ArakniD/foxbms/hardware/hw-slave-12-ltc6811-1/v2.1.7/Sources/slave.PcbDoc.htm

Reporting Options

# File in Previous Format

Date | : | 11/01/2020
Time | : | 5:13:20 AM
Filename | : | C:\sandbox\github\foxBMS\hardware\hw-slave-12-ltc6811-1\v2.1.7\Sources\slave.PcbDoc

Version | Warning

This file was generated by an earlier version of the software
