ArakniD/foxbms/hardware/hw-master/v1.0.6-2/Sources/master.PcbDoc.htm

Reporting Options

# File in Previous Format

Date | : | 3/12/2019
Time | : | 3:43:56 PM
Filename | : | C:\Users\lucas\Documents\GitHub\foxbms\hardware\hw-master\v1.0.6\Sources\master.PcbDoc

Version | Warning

This file was generated by an earlier version of the software
