ArakniD/foxbms/hardware/datasheets/TPS26602 - Design Calculator Rev1p0.xlsx

Sheet: Calculation Sheet
TPS26602 Design Calculator Tool
Constants Cells | Input / Select Cells | Calculation Cells
 | Calculated, but can be over-ridden by the user. Note: Once cells are over-ridden, new calculation sheet should be used for the next design
Parameter | Description | Value | Units | Tolerance
VIN (max) | Maximum System Input Voltage | 16.0 | V
UVset | Undervoltage Lockout Threshold | 10.00 | V
OVset | Over Voltage Clamp Threshold | 38 | V
Cout | Load Capacitance | 330.0 | µF | 10%
TA (max) | Maximum Ambient Temperature | TA = 85C | °C
RLstart | Load during start-up (Assumed to be resistive) | 42.0 | Ω
Imax | Maximum continuous load current | 1.0 | A
ILimit | Current Limit, 10% higher than the maximum continuous load current | 1.10 | A
UVLO, OVP Calculations
R2_sel | Select a value in the range from 10k to 249k | 49.9 | kΩ | 1.0% | 9.34 | PFAIL (VIN Falling)
R1_cal | Calculated value of Resistor at IN pin | 369.4 | kΩ |  | 10.11 | UVLO (VIN Rising)
SELECT THE CLOSEST POSSIBLE RESISTANCE VALUE FOR R1, R2 |  |  |  |  | 38.00 | OV Clamp (VIN Rising)
R2_sel | Selected closest possible value for R3 resistor | 49.9 | kΩ | 1.0%
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
