ArakniD/foxbms/hardware/datasheets/TPS2663x _TPS1663x_Design_Calculator_revA.xlsx

Sheet: Instructions
Instructions for using the TPS2663x/TPS1663x Design Calculator
Instructions for using the TPS2663x/TPS1663x Design Calculator Design Inputs • Enter the design inputs for operating input voltage, under voltage, overvoltage set points, output capacitance, ambient temperature, load at start-up, maximum continuous load current, and permissible inrush current at start up for charging output capacitance in cells D5 to D14 in Calculation Sheet. • Select the current limit for device (ILimit) at-least 5% more than (Imax + IINRUSH_Permissible) in Cell D15 in Calculation Sheet. UVLO, OVP Calculations • Enter the value of resistor (R3) between UVLO and OVP pins in Cell D17 in Calculation in Calculation Sheet • Design Calculator provides the calculated value of R2, R3 • Select the value of R1, R2 and R3 resistors in cells D22 to D24 close to the calculated values. • Design calculator provides the final under voltage, overvoltage and power fail set points based on selected values of R1 to R3 in cells D22 to D24. • Verify the value of current through resistors R1 to R3. The color of cell D28 changes based on value of current. If Current < 2uA, the cell turns RED and value of
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
