ArakniD/foxbms/hardware/hw-master/v1.0.6-2/Fabrication/Report Board Stack/master.xls

Board Stack Report
Stack Up |  | Layer Stack
Layer | Board Layer Stack | Name | Material | Thickness | Constant
1 |  | Top Paste
2 |  | Top Overlay
3 |  | Top Solder | Solder Resist | 0.020mm | 3.8
4 |  | Top Signal | Copper | 0.036mm
5 |  | Dielectric 1 | PP-015 | 0.100mm | 4.05
6 |  | Top GND | Copper | 0.018mm
7 |  | Dielectric 4 | Core-036 | 0.565mm | 4.6
8 |  | Inner PWR | Copper | 0.018mm
9 |  | Dielectric 2 | PP-015 | 0.127mm | 4.25
10 |  | Inner Signal | Copper | 0.018mm
11 |  | Dielectric 5 | Core-036 | 0.565mm | 4.6
12 |  | Bottom GND | Copper | 0.018mm
13 |  | Dielectric 3 | PP-015 | 0.100mm | 4.05
14 |  | Bottom Signal | Copper | 0.036mm
15 |  | Bottom Solder | Solder Resist | 0.020mm | 3.8
16 |  | Bottom Overlay
17 |  | Bottom Paste
 | Height : 1.641mm
