ArakniD/foxbms/hardware/datasheets/WBDesign21_AltiumDesigner/ExportFiles/Schematic/Altium/2019-07-21_03-39-48/readme.txt

 

**********************************************************
*************  Important Instructions Follow  ************
**********************************************************
 
All files exported to: Z:\\23\\04\\2304964\\21\Altium\2019-07-21_03-39-48\2019-07-21_03-39-48

**********************************************************
***************** Schematic Instructions  ****************
**********************************************************

To import your new Schematic into Altium:

1. Unzip the downloaded folder files to a local directory and
Start the Altium program.
2. From the menu select "File"->"Open".
3. Select the file named in the path above ending with ".schdoc"
and "Open" the file.
4. Your Schematic should be viewable within Altium now.

For additional information, please visit this site:
http://www.accelerated-designs.com/help/Altium_BrdSch_import.html

**********************************************************
*******************  PCB Instructions  *******************
**********************************************************

To import your new BOARD into Altium:

1. Unzip the downloaded folder files to a local directory
	and Start the Altium program.
2. From the menu select "File"->"Open".
3. Select the file named in the path above ending with ".pcbdoc"
and "Open" the file.
4. Planes will need to be repoured to update the Copper Pour Polygons
	a. Once your board is loaded, select the Tools menu from the
	   top Menu Bar
	b. Scroll to the Polygon Pours item on the Tools Menu.
	c. The Polygon Pours item should expand to show more options
	d. Select Repour All Polygons, this will repour all of the
	   polygons.
5. Your board should be viewable within Altium now.

For additional information, please visit this site:
http://www.accelerated-designs.com/help/Altium_BrdSch_import.html

**********************************************************
*******************  LIB Instructions  *******************
**********************************************************

To import your new LIBRARY PARTS into Altium follow these steps:

1. After running the Ultra Librarian export for the first time,
you will need to copy the following files into an area where
they can be accessed for all future translations.  They are script
files that Altium will need to be able to find.
	a. UL_Form.dfm
	b. UL_Form.pas
	c. UL_Import.pas
	d. UL_Import.prjScr
2. The above script file will need to be run from within Altium.
This can be done by going to File, Open and selecting the
UL_Import.PrjScr file stored above.
3. Select the "DXP" dropdown menu in the top-left corner runfrom
the drop down menu and select "Run Script". Select "UL_Form.pas"
and click "OK"
4. When the script is run, it will ask you for the file name of the
Ultra Librarian file to run. Click "File...", select the latest file
produced with a date code (for instance 2010-02-17_23-12-34.txt), and
click "Start Import".
5. The script will open a new Integraged Library project and import
the Ultra Librarian data into it.  When complete a message box
will pop up saying that import is done.

For additional information, please visit this site:
http://www.accelerated-designs.com/help/Altium_import.html

For a video tutorial, please visit:
http://youtu.be/pih50yx9HYU

**********************************************************
**********************************************************
**********************************************************

Padstack "RX78p74Y236p22D0T" renamed to "RX78p74Y236p22D0"
Symbol "WB_CFF_BLOCK_TPS54202" renamed to "WB_CFF_BLOCK_TPS"
Symbol "WB_PWL_VOLTAGE_SOURCE" renamed to "WB_PWL_VOLTAGE_S"
Symbol "WB_SOURCE_RESISTOR" renamed to "WB_SOURCE_RESIST"
Symbol "WB_PRIM_PWL_VOLTAGE_SOURCE" renamed to "WB_PRIM_PWL_VOLT"
Symbol "WB_PRIM_STARTUP_VOLTAGE_SOURCE" renamed to "WB_PRIM_STARTUP_"
Symbol "WB_STARTUP_VOLTAGE_SOURCE" renamed to "WB_STARTUP_VOLTA"
Symbol "WB_PWL_CURRENT_LOAD" renamed to "WB_PWL_CURRENT_L"
Symbol "WB_PRIMITIVE_BATTERY" renamed to "WB_PRIMITIVE_BAT"
Component "TPS54202DDCR" renamed to "TPS54202DDCR"
Component "WB_CURRENT_LOAD" renamed to "WB_CURRENT_LOAD"
Component "SRN6045-4R7Y" renamed to "SRN6045-4R7Y"
Component "CRCW040222K1FKED" renamed to "CRCW040222K1FKED"
Component "CGA3E2X7R1H104K080AA" renamed to "CGA3E2X7R1H104K0"
Component "CL32B106KBJNNWE" renamed to "CL32B106KBJNNWE"
Component "WB_GND" renamed to "WB_GND"
Component "CRCW0402100KFKED" renamed to "CRCW0402100KFKED"
Component "CL21C510JBANNNC" renamed to "CL21C510JBANNNC"
Component "WB_BATTERY" renamed to "WB_BATTERY"
Component "TMK325B7226KMHP" renamed to "TMK325B7226KMHP"
The Symbol WB_CONTINUATION was missing a RefDes attribute, a refdes was created for the symbol.
The Symbol WB_CONTINUATION was missing a Type attribute, a type was created for the symbol.
The Symbol WB_CONTINUATION was missing a Value attribute, a value was created for the symbol.
The Symbol WB_BLOCK_IO was missing a RefDes attribute, a refdes was created for the symbol.
The Symbol WB_BLOCK_IO was missing a Type attribute, a type was created for the symbol.
The Symbol WB_BLOCK_IO was missing a Value attribute, a value was created for the symbol.
The Symbol WB_TPS54202DDC was missing a RefDes attribute, a refdes was created for the symbol.
The Symbol WB_TPS54202DDC was missing a Type attribute, a type was created for the symbol.
The Symbol WB_TPS54202DDC was missing a Value attribute, a value was created for the symbol.
The Symbol WB_VOLTAGE_PROBE was missing a RefDes attribute, a refdes was created for the symbol.
The Symbol WB_VOLTAGE_PROBE was missing a Type attribute, a type was created for the symbol.
The Symbol WB_VOLTAGE_PROBE was missing a Value attribute, a value was created for the symbol.
The Symbol WB_CURRENT_PROBE was missing a RefDes attribute, a refdes was created for the symbol.
The Symbol WB_CURRENT_PROBE was missing a Type attribute, a type was created for the symbol.
The Symbol WB_CURRENT_PROBE was missing a Value attribute, a value was created for the symbol.
The Symbol WB_CFF_BLOCK_TPS was missing a RefDes attribute, a refdes was created for the symbol.
The Symbol WB_CFF_BLOCK_TPS was missing a Type attribute, a type was created for the symbol.
The Symbol WB_CFF_BLOCK_TPS was missing a Value attribute, a value was created for the symbol.
The Symbol WB_PWL_VOLTAGE_S was missing a RefDes attribute, a refdes was created for the symbol.
The Symbol WB_PWL_VOLTAGE_S was missing a Type attribute, a type was created for the symbol.
The Symbol WB_PWL_VOLTAGE_S was missing a Value attribute, a value was created for the symbol.
The Symbol WB_SOURCE_RESIST was missing a RefDes attribute, a refdes was created for the symbol.
The Symbol WB_SOURCE_RESIST was missing a Type attribute, a type was created for the symbol.
The Symbol WB_SOURCE_RESIST was missing a Value attribute, a value was created for the symbol.
The Symbol WB_PRIM_PWL_VOLT was missing a RefDes attribute, a refdes was created for the symbol.
The Symbol WB_PRIM_PWL_VOLT was missing a Type attribute, a type was created for the symbol.
The Symbol WB_PRIM_PWL_VOLT was missing a Value attribute, a value was created for the symbol.
The Symbol WB_LOAD_RESISTOR was missing a RefDes attribute, a refdes was created for the symbol.
The Symbol WB_LOAD_RESISTOR was missing a Type attribute, a type was created for the symbol.
The Symbol WB_LOAD_RESISTOR was missing a Value attribute, a value was created for the symbol.
The Symbol WB_PRIM_STARTUP_ was missing a RefDes attribute, a refdes was created for the symbol.
The Symbol WB_PRIM_STARTUP_ was missing a Type attribute, a type was created for the symbol.
The Symbol WB_PRIM_STARTUP_ was missing a Value attribute, a value was created for the symbol.
The Symbol WB_STARTUP_VOLTA was missing a RefDes attribute, a refdes was created for the symbol.
The Symbol WB_STARTUP_VOLTA was missing a Type attribute, a type was created for the symbol.
The Symbol WB_STARTUP_VOLTA was missing a Value attribute, a value was created for the symbol.
The Symbol WB_PWL_CURRENT_L was missing a RefDes attribute, a refdes was created for the symbol.
The Symbol WB_PWL_CURRENT_L was missing a Type attribute, a type was created for the symbol.
The Symbol WB_PWL_CURRENT_L was missing a Value attribute, a value was created for the symbol.
The Symbol WB_PRIMITIVE_BAT was missing a RefDes attribute, a refdes was created for the symbol.
The Symbol WB_PRIMITIVE_BAT was missing a Type attribute, a type was created for the symbol.
The Symbol WB_PRIMITIVE_BAT was missing a Value attribute, a value was created for the symbol.

Ultra Librarian Gold 8.1.204 Process Report

Message - Component "SRN6045-4R7Y" attribute "Datasheet URL" references text style "" that is not in the database.
The default pattern text style "H50s3" was substituted.
Message - Component "SRN6045-4R7Y" attribute "L" references text style "" that is not in the database.
The default pattern text style "H50s3" was substituted.
Message - Component "SRN6045-4R7Y" attribute "DCR" references text style "" that is not in the database.
The default pattern text style "H50s3" was substituted.
Message - Component "SRN6045-4R7Y" attribute "IDC" references text style "" that is not in the database.
The default pattern text style "H50s3" was substituted.
Message - Component "CRCW040222K1FKED" attribute "Resistance" references text style "" that is not in the database.
The default pattern text style "H50s3" was substituted.
Message - Component "CRCW040222K1FKED" attribute "Power" references text style "" that is not in the database.
The default pattern text style "H50s3" was substituted.
Message - Component "CRCW040222K1FKED" attribute "Tolerance" references text style "" that is not in the database.
The default pattern text style "H50s3" was substituted.
Message - Component "CGA3E2X7R1H104K0" attribute "Datasheet URL" references text style "" that is not in the database.
The default pattern text style "H50s3" was substituted.
Message - Component "CGA3E2X7R1H104K0" attribute "Cap" references text style "" that is not in the database.
The default pattern text style "H50s3" was substituted.
Message - Component "CGA3E2X7R1H104K0" attribute "ESR" references text style "" that is not in the database.
The default pattern text style "H50s3" was substituted.
Message - Component "CGA3E2X7R1H104K0" attribute "IRMS" references text style "" that is not in the database.
The default pattern text style "H50s3" was substituted.
Message - Component "CGA3E2X7R1H104K0" attribute "VDC" references text style "" that is not in the database.
The default pattern text style "H50s3" was substituted.
Message - Component "CL32B106KBJNNWE" attribute "Datasheet URL" references text style "" that is not in the database.
The default pattern text style "H50s3" was substituted.
Message - Component "CL32B106KBJNNWE" attribute "Cap" references text style "" that is not in the database.
The default pattern text style "H50s3" was substituted.
Message - Component "CL32B106KBJNNWE" attribute "ESR" references text style "" that is not in the database.
The default pattern text style "H50s3" was substituted.
Message - Component "CL32B106KBJNNWE" attribute "IRMS" references text style "" that is not in the database.
The default pattern text style "H50s3" was substituted.
Message - Component "CL32B106KBJNNWE" attribute "VDC" references text style "" that is not in the database.
The default pattern text style "H50s3" was substituted.
Message - Component "CRCW0402100KFKED" attribute "Resistance" references text style "" that is not in the database.
The default pattern text style "H50s3" was substituted.
Message - Component "CRCW0402100KFKED" attribute "Power" references text style "" that is not in the database.
The default pattern text style "H50s3" was substituted.
Message - Component "CRCW0402100KFKED" attribute "Tolerance" references text style "" that is not in the database.
The default pattern text style "H50s3" was substituted.
Message - Component "CL21C510JBANNNC" attribute "Datasheet URL" references text style "" that is not in the database.
The default pattern text style "H50s3" was substituted.
Message - Component "CL21C510JBANNNC" attribute "Cap" references text style "" that is not in the database.
The default pattern text style "H50s3" was substituted.
Message - Component "CL21C510JBANNNC" attribute "ESR" references text style "" that is not in the database.
The default pattern text style "H50s3" was substituted.
Message - Component "CL21C510JBANNNC" attribute "IRMS" references text style "" that is not in the database.
The default pattern text style "H50s3" was substituted.
Message - Component "CL21C510JBANNNC" attribute "VDC" references text style "" that is not in the database.
The default pattern text style "H50s3" was substituted.
Message - Component "TMK325B7226KMHP" attribute "Datasheet URL" references text style "" that is not in the database.
The default pattern text style "H50s3" was substituted.
Message - Component "TMK325B7226KMHP" attribute "Cap" references text style "" that is not in the database.
The default pattern text style "H50s3" was substituted.
Message - Component "TMK325B7226KMHP" attribute "ESR" references text style "" that is not in the database.
The default pattern text style "H50s3" was substituted.
Message - Component "TMK325B7226KMHP" attribute "IRMS" references text style "" that is not in the database.
The default pattern text style "H50s3" was substituted.
Message - Component "TMK325B7226KMHP" attribute "VDC" references text style "" that is not in the database.
The default pattern text style "H50s3" was substituted.
Message - Pattern "DDC0006A_N", Attribute "RefDes" is a duplicate Attribute and will be deleted.
Message - Pattern "DDC0006A_M", Attribute "RefDes" is a duplicate Attribute and will be deleted.
Message - Pattern "DDC0006A_L", Attribute "RefDes" is a duplicate Attribute and will be deleted.

TextStyle count:  24
Padstack count:   8
Pattern count:    8
Symbol count:     21
Component count:  11

Export

Footprint "0402" has no layer data mapped and will be skipped.
Component "CRCW040222K1FKED" requires footprint "0402" and will be skipped.
Component "CRCW0402100KFKED" requires footprint "0402" and will be skipped.
Footprint "0603" has no layer data mapped and will be skipped.
Component "CGA3E2X7R1H104K0" requires footprint "0603" and will be skipped.
Footprint "0805" has no layer data mapped and will be skipped.
Component "CL21C510JBANNNC" requires footprint "0805" and will be skipped.
Warning: Symbol "TPS54202DDC" attribute "VAL" references missing text style ""
Warning: Symbol "TPS54202DDC" attribute "DEV" references missing text style ""
Warning: Symbol "TPS54202DDC" attribute "PN" references missing text style ""
Warning: Symbol "WB_INDUCTOR" attribute "L" references missing text style ""
Warning: Symbol "WB_INDUCTOR" attribute "DCR" references missing text style ""
Warning: Symbol "WB_INDUCTOR" attribute "IDC" references missing text style ""
Warning: Symbol "WB_INDUCTOR" attribute "PN" references missing text style ""
Warning: Symbol "WB_INDUCTOR" attribute "DEV" references missing text style ""
Warning: Symbol "WB_INDUCTOR" attribute "VAL" references missing text style ""
Warning: Symbol "WB_INDUCTOR" attribute "TOL" references missing text style ""
Warning: Symbol "WB_INDUCTOR" attribute "RefDes2" references missing text style ""
Warning: Symbol "WB_CAPACITOR" attribute "Cap" references missing text style ""
Warning: Symbol "WB_CAPACITOR" attribute "ESR" references missing text style ""
Warning: Symbol "WB_CAPACITOR" attribute "IRMS" references missing text style ""
Warning: Symbol "WB_CAPACITOR" attribute "VDC" references missing text style ""
Warning: Symbol "WB_CAPACITOR" attribute "TOL" references missing text style ""
Warning: Symbol "WB_CAPACITOR" attribute "VAL" references missing text style ""
Warning: Symbol "WB_CAPACITOR" attribute "DEV" references missing text style ""
Warning: Symbol "WB_CAPACITOR" attribute "PN" references missing text style ""
Warning: Symbol "WB_CAPACITOR" attribute "RefDes2" references missing text style ""
Warning: Symbol "WB_CAPACITOR" attribute "Cap" references missing text style ""
Warning: Symbol "WB_CAPACITOR" attribute "ESR" references missing text style ""
Warning: Symbol "WB_CAPACITOR" attribute "IRMS" references missing text style ""
Warning: Symbol "WB_CAPACITOR" attribute "VDC" references missing text style ""
Warning: Symbol "WB_CAPACITOR" attribute "TOL" references missing text style ""
Warning: Symbol "WB_CAPACITOR" attribute "VAL" references missing text style ""
Warning: Symbol "WB_CAPACITOR" attribute "DEV" references missing text style ""
Warning: Symbol "WB_CAPACITOR" attribute "PN" references missing text style ""
Warning: Symbol "WB_CAPACITOR" attribute "RefDes2" references missing text style ""
