ArakniD/foxbms/hardware/datasheets/WBDesign20_AltiumDesigner/ExportFiles/Schematic/webench_schematic_exchange_design_2304964_20_Altium/Altium/2019-07-21_03-32-47/readme.txt

 

**********************************************************
*************  Important Instructions Follow  ************
**********************************************************
 
All files exported to: Z:\\23\\04\\2304964\\20\Altium\2019-07-21_03-32-47\2019-07-21_03-32-47

**********************************************************
***************** Schematic Instructions  ****************
**********************************************************

To import your new Schematic into Altium:

1. Unzip the downloaded folder files to a local directory and
Start the Altium program.
2. From the menu select "File"->"Open".
3. Select the file named in the path above ending with ".schdoc"
and "Open" the file.
4. Your Schematic should be viewable within Altium now.

For additional information, please visit this site:
http://www.accelerated-designs.com/help/Altium_BrdSch_import.html

**********************************************************
*******************  PCB Instructions  *******************
**********************************************************

To import your new BOARD into Altium:

1. Unzip the downloaded folder files to a local directory
	and Start the Altium program.
2. From the menu select "File"->"Open".
3. Select the file named in the path above ending with ".pcbdoc"
and "Open" the file.
4. Planes will need to be repoured to update the Copper Pour Polygons
	a. Once your board is loaded, select the Tools menu from the
	   top Menu Bar
	b. Scroll to the Polygon Pours item on the Tools Menu.
	c. The Polygon Pours item should expand to show more options
	d. Select Repour All Polygons, this will repour all of the
	   polygons.
5. Your board should be viewable within Altium now.

For additional information, please visit this site:
http://www.accelerated-designs.com/help/Altium_BrdSch_import.html

**********************************************************
*******************  LIB Instructions  *******************
**********************************************************

To import your new LIBRARY PARTS into Altium follow these steps:

1. After running the Ultra Librarian export for the first time,
you will need to copy the following files into an area where
they can be accessed for all future translations.  They are script
files that Altium will need to be able to find.
	a. UL_Form.dfm
	b. UL_Form.pas
	c. UL_Import.pas
	d. UL_Import.prjScr
2. The above script file will need to be run from within Altium.
This can be done by going to File, Open and selecting the
UL_Import.PrjScr file stored above.
3. Select the "DXP" dropdown menu in the top-left corner runfrom
the drop down menu and select "Run Script". Select "UL_Form.pas"
and click "OK"
4. When the script is run, it will ask you for the file name of the
Ultra Librarian file to run. Click "File...", select the latest file
produced with a date code (for instance 2010-02-17_23-12-34.txt), and
click "Start Import".
5. The script will open a new Integraged Library project and import
the Ultra Librarian data into it.  When complete a message box
will pop up saying that import is done.

For additional information, please visit this site:
http://www.accelerated-designs.com/help/Altium_import.html

For a video tutorial, please visit:
http://youtu.be/pih50yx9HYU

**********************************************************
**********************************************************
**********************************************************

Symbol "WB_STARTUP_VOLTAGE_SOURCE" renamed to "WB_STARTUP_VOLTA"
Symbol "WB_SOURCE_RESISTOR" renamed to "WB_SOURCE_RESIST"
Symbol "WB_PRIM_STARTUP_VOLTAGE_SOURCE" renamed to "WB_PRIM_STARTUP_"
Symbol "WB_PWL_CURRENT_LOAD" renamed to "WB_PWL_CURRENT_L"
Symbol "WB_ZERO_VOLT_SOURCE" renamed to "WB_ZERO_VOLT_SOU"
Symbol "WB_PWL_VOLTAGE_SOURCE" renamed to "WB_PWL_VOLTAGE_S"
Symbol "WB_PRIM_PWL_VOLTAGE_SOURCE" renamed to "WB_PRIM_PWL_VOLT"
Symbol "WB_PRIMITIVE_BATTERY" renamed to "WB_PRIMITIVE_BAT"
Symbol "WB_TPS62131_CINX_BLOCK" renamed to "WB_TPS62131_CINX"
Symbol "WB_TPS62131_DEF_HIGH" renamed to "WB_TPS62131_DEF_"
Symbol "WB_TPS62131_DEF_LOW" renamed to "WB_TPS62131_DE00"
Symbol "WB_TPS62131_FSW_HIGH" renamed to "WB_TPS62131_FSW_"
Symbol "WB_TPS62131_FSW_LOW" renamed to "WB_TPS62131_FS00"
Component "C0805C106K8PACTU" renamed to "C0805C106K8PACTU"
Component "GRM188R60J226MEA0D" renamed to "GRM188R60J226MEA"
Component "GRM1555C1E391JA01D" renamed to "GRM1555C1E391JA0"
Component "WB_GND" renamed to "WB_GND"
Component "PA4332.222NLT" renamed to "PA4332.222NLT"
Component "CRCW0402100KFKED" renamed to "CRCW0402100KFKED"
Component "TPS62142RGTR" renamed to "TPS62142RGTR"
Component "WB_BATTERY" renamed to "WB_BATTERY"
Component "WB_CURRENT_LOAD" renamed to "WB_CURRENT_LOAD"
The Symbol WB_CONTINUATION was missing a RefDes attribute, a refdes was created for the symbol.
The Symbol WB_CONTINUATION was missing a Type attribute, a type was created for the symbol.
The Symbol WB_CONTINUATION was missing a Value attribute, a value was created for the symbol.
The Symbol WB_BLOCK_IO was missing a RefDes attribute, a refdes was created for the symbol.
The Symbol WB_BLOCK_IO was missing a Type attribute, a type was created for the symbol.
The Symbol WB_BLOCK_IO was missing a Value attribute, a value was created for the symbol.
The Symbol WB_STARTUP_VOLTA was missing a RefDes attribute, a refdes was created for the symbol.
The Symbol WB_STARTUP_VOLTA was missing a Type attribute, a type was created for the symbol.
The Symbol WB_STARTUP_VOLTA was missing a Value attribute, a value was created for the symbol.
The Symbol WB_SOURCE_RESIST was missing a RefDes attribute, a refdes was created for the symbol.
The Symbol WB_SOURCE_RESIST was missing a Type attribute, a type was created for the symbol.
The Symbol WB_SOURCE_RESIST was missing a Value attribute, a value was created for the symbol.
The Symbol WB_PRIM_STARTUP_ was missing a RefDes attribute, a refdes was created for the symbol.
The Symbol WB_PRIM_STARTUP_ was missing a Type attribute, a type was created for the symbol.
The Symbol WB_PRIM_STARTUP_ was missing a Value attribute, a value was created for the symbol.
The Symbol WB_CURRENT_PROBE was missing a RefDes attribute, a refdes was created for the symbol.
The Symbol WB_CURRENT_PROBE was missing a Type attribute, a type was created for the symbol.
The Symbol WB_CURRENT_PROBE was missing a Value attribute, a value was created for the symbol.
The Symbol WB_PWL_CURRENT_L was missing a RefDes attribute, a refdes was created for the symbol.
The Symbol WB_PWL_CURRENT_L was missing a Type attribute, a type was created for the symbol.
The Symbol WB_PWL_CURRENT_L was missing a Value attribute, a value was created for the symbol.
The Symbol WB_ZERO_VOLT_SOU was missing a RefDes attribute, a refdes was created for the symbol.
The Symbol WB_ZERO_VOLT_SOU was missing a Type attribute, a type was created for the symbol.
The Symbol WB_ZERO_VOLT_SOU was missing a Value attribute, a value was created for the symbol.
The Symbol WB_PWL_VOLTAGE_S was missing a RefDes attribute, a refdes was created for the symbol.
The Symbol WB_PWL_VOLTAGE_S was missing a Type attribute, a type was created for the symbol.
The Symbol WB_PWL_VOLTAGE_S was missing a Value attribute, a value was created for the symbol.
The Symbol WB_PRIM_PWL_VOLT was missing a RefDes attribute, a refdes was created for the symbol.
The Symbol WB_PRIM_PWL_VOLT was missing a Type attribute, a type was created for the symbol.
The Symbol WB_PRIM_PWL_VOLT was missing a Value attribute, a value was created for the symbol.
The Symbol WB_LOAD_RESISTOR was missing a RefDes attribute, a refdes was created for the symbol.
The Symbol WB_LOAD_RESISTOR was missing a Type attribute, a type was created for the symbol.
The Symbol WB_LOAD_RESISTOR was missing a Value attribute, a value was created for the symbol.
The Symbol WB_PRIMITIVE_BAT was missing a RefDes attribute, a refdes was created for the symbol.
The Symbol WB_PRIMITIVE_BAT was missing a Type attribute, a type was created for the symbol.
The Symbol WB_PRIMITIVE_BAT was missing a Value attribute, a value was created for the symbol.
The Symbol WB_TPS62142 was missing a RefDes attribute, a refdes was created for the symbol.
The Symbol WB_TPS62142 was missing a Type attribute, a type was created for the symbol.
The Symbol WB_TPS62142 was missing a Value attribute, a value was created for the symbol.
The Symbol WB_VOLTAGE_PROBE was missing a RefDes attribute, a refdes was created for the symbol.
The Symbol WB_VOLTAGE_PROBE was missing a Type attribute, a type was created for the symbol.
The Symbol WB_VOLTAGE_PROBE was missing a Value attribute, a value was created for the symbol.
The Symbol WB_TPS62131_CINX was missing a RefDes attribute, a refdes was created for the symbol.
The Symbol WB_TPS62131_CINX was missing a Type attribute, a type was created for the symbol.
The Symbol WB_TPS62131_CINX was missing a Value attribute, a value was created for the symbol.
The Symbol WB_TPS62131_DEF_ was missing a RefDes attribute, a refdes was created for the symbol.
The Symbol WB_TPS62131_DEF_ was missing a Type attribute, a type was created for the symbol.
The Symbol WB_TPS62131_DEF_ was missing a Value attribute, a value was created for the symbol.
The Symbol WB_TPS62131_DE00 was missing a RefDes attribute, a refdes was created for the symbol.
The Symbol WB_TPS62131_DE00 was missing a Type attribute, a type was created for the symbol.
The Symbol WB_TPS62131_DE00 was missing a Value attribute, a value was created for the symbol.
The Symbol WB_TPS62131_FSW_ was missing a RefDes attribute, a refdes was created for the symbol.
The Symbol WB_TPS62131_FSW_ was missing a Type attribute, a type was created for the symbol.
The Symbol WB_TPS62131_FSW_ was missing a Value attribute, a value was created for the symbol.
The Symbol WB_TPS62131_FS00 was missing a RefDes attribute, a refdes was created for the symbol.
The Symbol WB_TPS62131_FS00 was missing a Type attribute, a type was created for the symbol.
The Symbol WB_TPS62131_FS00 was missing a Value attribute, a value was created for the symbol.

Ultra Librarian Gold 8.1.204 Process Report

Message - Symbol "WB_CAPACITOR" has as multiple attributes named "TYPE".
One of the attributes was renamed to "TYPE_2".
Message - Component "C0805C106K8PACTU" attribute "Cap" references text style "" that is not in the database.
The default pattern text style "H50s3" was substituted.
Message - Component "C0805C106K8PACTU" attribute "ESR" references text style "" that is not in the database.
The default pattern text style "H50s3" was substituted.
Message - Component "C0805C106K8PACTU" attribute "IRMS" references text style "" that is not in the database.
The default pattern text style "H50s3" was substituted.
Message - Component "C0805C106K8PACTU" attribute "VDC" references text style "" that is not in the database.
The default pattern text style "H50s3" was substituted.
Message - Component "GRM188R60J226MEA" attribute "Datasheet URL" references text style "" that is not in the database.
The default pattern text style "H50s3" was substituted.
Message - Component "GRM188R60J226MEA" attribute "Cap" references text style "" that is not in the database.
The default pattern text style "H50s3" was substituted.
Message - Component "GRM188R60J226MEA" attribute "ESR" references text style "" that is not in the database.
The default pattern text style "H50s3" was substituted.
Message - Component "GRM188R60J226MEA" attribute "IRMS" references text style "" that is not in the database.
The default pattern text style "H50s3" was substituted.
Message - Component "GRM188R60J226MEA" attribute "VDC" references text style "" that is not in the database.
The default pattern text style "H50s3" was substituted.
Message - Component "GRM1555C1E391JA0" attribute "Cap" references text style "" that is not in the database.
The default pattern text style "H50s3" was substituted.
Message - Component "GRM1555C1E391JA0" attribute "ESR" references text style "" that is not in the database.
The default pattern text style "H50s3" was substituted.
Message - Component "GRM1555C1E391JA0" attribute "IRMS" references text style "" that is not in the database.
The default pattern text style "H50s3" was substituted.
Message - Component "GRM1555C1E391JA0" attribute "VDC" references text style "" that is not in the database.
The default pattern text style "H50s3" was substituted.
Message - Component "PA4332.222NLT" attribute "Datasheet URL" references text style "" that is not in the database.
The default pattern text style "H50s3" was substituted.
Message - Component "PA4332.222NLT" attribute "L" references text style "" that is not in the database.
The default pattern text style "H50s3" was substituted.
Message - Component "PA4332.222NLT" attribute "DCR" references text style "" that is not in the database.
The default pattern text style "H50s3" was substituted.
Message - Component "PA4332.222NLT" attribute "IDC" references text style "" that is not in the database.
The default pattern text style "H50s3" was substituted.
Message - Component "CRCW0402100KFKED" attribute "Resistance" references text style "" that is not in the database.
The default pattern text style "H50s3" was substituted.
Message - Component "CRCW0402100KFKED" attribute "Power" references text style "" that is not in the database.
The default pattern text style "H50s3" was substituted.
Message - Component "CRCW0402100KFKED" attribute "Tolerance" references text style "" that is not in the database.
The default pattern text style "H50s3" was substituted.

TextStyle count:  24
Padstack count:   6
Pattern count:    5
Symbol count:     26
Component count:  9

Export

Footprint "0805" has no layer data mapped and will be skipped.
Component "C0805C106K8PACTU" requires footprint "0805" and will be skipped.
Footprint "0603" has no layer data mapped and will be skipped.
Component "GRM188R60J226MEA" requires footprint "0603" and will be skipped.
Footprint "0402" has no layer data mapped and will be skipped.
Component "GRM1555C1E391JA0" requires footprint "0402" and will be skipped.
Component "CRCW0402100KFKED" requires footprint "0402" and will be skipped.
Warning: Symbol "WB_INDUCTOR" attribute "L" references missing text style ""
Warning: Symbol "WB_INDUCTOR" attribute "DCR" references missing text style ""
Warning: Symbol "WB_INDUCTOR" attribute "IDC" references missing text style ""
Warning: Symbol "WB_INDUCTOR" attribute "TOL" references missing text style ""
Warning: Symbol "WB_INDUCTOR" attribute "VAL" references missing text style ""
Warning: Symbol "WB_INDUCTOR" attribute "DEV" references missing text style ""
Warning: Symbol "WB_INDUCTOR" attribute "PN" references missing text style ""
Warning: Symbol "TPS62142RGT" attribute "TOL" references missing text style ""
Warning: Symbol "TPS62142RGT" attribute "VAL" references missing text style ""
Warning: Symbol "TPS62142RGT" attribute "DEV" references missing text style ""
Warning: Symbol "TPS62142RGT" attribute "PN" references missing text style ""
