ArakniD/foxbms/documentation/sphinx/general_information/releases/releases.rst

.. include:: ../../macros.rst

.. _GENERAL_INFORMATION_RELEASES:

========
Releases
========

The current **software version** of |foxbms| is |version|.

The latest **hardware release** versions are:

  - |BMS-Master|: |hw-version-master|
  - |BMS-Extension|: |hw-version-extension|
  - |BMS-Interface|: |hw-version-interface|
  - |BMS-12-Slave|: |hw-version-12-slave|
  - |BMS-18-Slave|: |hw-version-18-slave|

.. note::

    EEPROM module from **v1.5.0** is **NOT** compatible with previous versions
    due to the changed memory layout because of added timestamps!

.. note::

    foxBMS uses now python3. The foxconda3 installer is found at
    https://iisb-foxbms.iisb.fraunhofer.de/foxbms/. foxconda3 must be installed
    to C:\\foxconda3!

.. note::

    Until version **v1.1.0**, the |foxbms| software was split into several
    repositories, with an independent version number for each repository.
    Starting from version **v1.5.0**, the |foxbms| software is contained in
    only one repository, with one version number!

The following tables describe the different versions of |foxbms| that were
released. The first line is the most recent one, the last one the oldest one.

**Versions 1.5.0 and higher:**

+--------+----------+--------------+
| foxbms | foxconda | Release date |
+========+==========+==============+
| v1.6.3 | 3.0.3    | 2019-09-03   |
+--------+----------+--------------+
| v1.6.2 | 3.0.3    | 2019-07-05   |
+--------+----------+--------------+
| v1.6.1 | 3.0.3    | 2019-06-19   |
+--------+----------+--------------+
| v1.6.0 | 3.0.3    | 2019-06-19   |
+--------+----------+--------------+
| v1.5.5 | 3.0.3    | 2019-01-25   |
+--------+----------+--------------+
| v1.5.4 | 3.0.3    | 2018-12-14   |
+--------+----------+--------------+
| v1.5.3 | 3.0.3    | 2018-12-07   |
+--------+----------+--------------+
| v1.5.2 | 3.0.3    | 2018-10-26   |
+--------+----------+--------------+
| v1.5.1 | 3.0.3    | 2018-10-09   |
+--------+----------+--------------+
| v1.5.0 | 3.0.3    | 2018-09-25   |
+--------+----------+--------------+

**Versions before 1.5.0:**

.. note::

    The following table is only presented as information on previous |foxbms|
    versions. This software structure with different software repositories is
    not used anymore.

+---------------+-------------------------------------------------------+----------------------------------------------------------------+------------+
| Documentation | Embedded Software                                     |                          |foxbms| Hardware                     |  foxConda  |
+               +----------+-----------+-----------+---------+----------+--------------+-----------------+-------------+-----------------+------------+
|               | Primary  | Secondary | Common    | HAL     | FreeRTOS | |BMS-Master| | |BMS-Interface| | |BMS-Slave| | |BMS-Extension| |            |
+===============+==========+===========+===========+=========+==========+==============+=================+=============+=================+============+
| 1.0.3         | 1.1.0    | 1.1.0     | 1.1.0     | | 1.0.1 |  1.1.0   | 1.0.2        | 1.0.1           |   | 2.1.0   | 1.0.2           | 1.0.0      |
|               |          |           |           | | 1.0.0 |          |              |                 |   | 2.0.3   |                 |            |
|               |          |           |           |         |          |              |                 |   | 1.0.1   |                 |            |
+---------------+----------+-----------+-----------+---------+----------+--------------+-----------------+-------------+-----------------+------------+
| 1.0.2         | | 1.0.2  | | 1.0.1   | | 1.0.2   | | 1.0.1 |  1.0.0   | 1.0.2        | 1.0.1           |   | 2.1.0   | 1.0.2           | 1.0.0      |
|               | | 1.0.1  | | 1.0.0   | | 1.0.1   | | 1.0.0 |          |              |                 |   | 2.0.3   |                 |            |
|               | | 1.0.0  |           | | 1.0.0   |         |          |              |                 |   | 1.0.1   |                 |            |
+---------------+----------+-----------+-----------+---------+----------+--------------+-----------------+-------------+-----------------+------------+
| 0.5.2         | 0.5.2    | 0.5.2     |           |         |          | 1.0.2        | 1.0.1           |   | 2.1.0   | 1.0.2           | 0.5.0      |
|               |          |           |           |         |          |              |                 |   | 2.0.3   |                 |            |
|               |          |           |           |         |          |              |                 |   | 1.0.1   |                 |            |
+---------------+----------+-----------+-----------+---------+----------+--------------+-----------------+-------------+-----------------+------------+
| 0.5.1         | 0.5.1    | 0.5.1     |           |         |          | 1.0.2        | 1.0.1           | 1.0.1       | 1.0.2           | 0.5.0      |
+---------------+----------+-----------+-----------+---------+----------+--------------+-----------------+-------------+-----------------+------------+
| 0.5.0         | 0.5.0    | 0.5.0     |           |         |          | 1.0.2        | 1.0.1           | 1.0.1       | 1.0.2           | 0.5.0      |
+---------------+----------+-----------+-----------+---------+----------+--------------+-----------------+-------------+-----------------+------------+
| 0.4.4         | 0.4.4    | 0.4.4     |           |         |          | 1.0.1        | 1.0.1           | 1.0.1       | 1.0.1           | 0.4.3      |
+---------------+----------+-----------+-----------+---------+----------+--------------+-----------------+-------------+-----------------+------------+
| 0.4.3         | 0.4.3    | 0.4.3     |           |         |          | 1.0.0        | 1.0.0           | 1.0.0       | 1.0.0           | 0.4.3      |
+---------------+----------+-----------+-----------+---------+----------+--------------+-----------------+-------------+-----------------+------------+
| 0.4.2         | 0.4.2    | 0.4.2     |           |         |          | 1.0.0        | 1.0.0           | 1.0.0       | 1.0.0           | 0.4.0      |
+---------------+----------+-----------+-----------+---------+----------+--------------+-----------------+-------------+-----------------+------------+
| 0.4.1         | 0.4.1    | 0.4.1     |           |         |          | 1.0.0        | 1.0.0           | 1.0.0       | 1.0.0           | 0.4.0      |
+---------------+----------+-----------+-----------+---------+----------+--------------+-----------------+-------------+-----------------+------------+
| 0.4.0         | 0.4.0    | 0.4.0     |           |         |          | 1.0.0        | 1.0.0           | 1.0.0       | 1.0.0           | 0.4.0      |
+---------------+----------+-----------+-----------+---------+----------+--------------+-----------------+-------------+-----------------+------------+
