ArakniD/foxbms/hardware/datasheets/13461.png

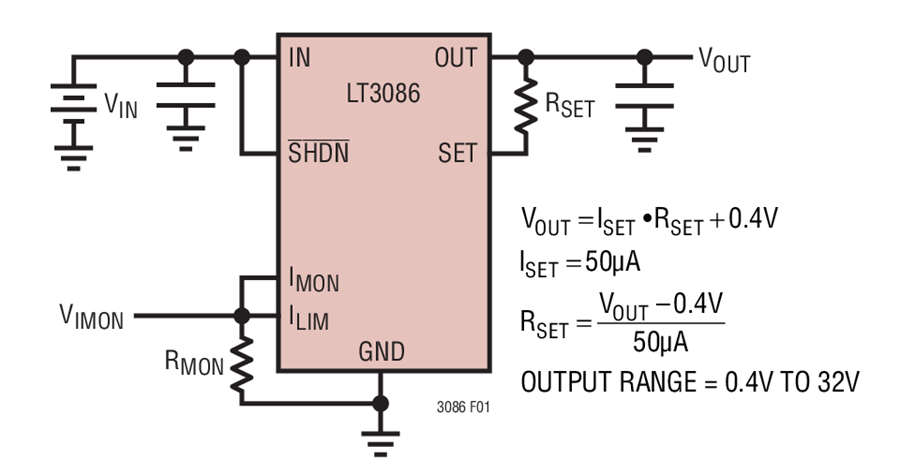
hardware/datasheets/13461.png
