ArakniD/foxbms/hardware/hw-slave-12-ltc6811-1/v2.1.7/Assembly default/bom/bom-slave-12-ltc6811-1(default).xlsx

Sheet: BOM
BOM for slave-12-ltc6811-1, Variant default
Generated on 28.03.2019 11:59:38
Line # | Designator | Quantity | Name | Description | Case EIA | Manufacturer 1 | Manufacturer Part Number 1 | Supplier 1 | Supplier Part Number 1
 | IC800-1, IC800-2 | 2 | M24M02-DWMN3TP/K | Automotive 2-Mbit serial I²C bus EEPROM with 1 MHz clock |  | STMicroelectronics (https://octopart-clicks.com/click/altium?manufacturer=STMicroelectronics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) | M24M02-DWMN3TP/K (https://octopart-clicks.com/click/altium?manufacturer=STMicroelectronics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) | Digi-Key | 497-16238-1-ND (https://octopart-clicks.com/click/altium?manufacturer=STMicroelectronics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)
1 | R605-1, R605-2, R1402-1, R1403-2, R1406-1, R1407-2, R1410-1, R1410-2, R1413-1, R1413-2, R1417-1, R1417-2, R1419-2, R1420-1 | 14 | 0R | SMD Resistor 0R 0603 | 0603 | Vishay Semiconductors (https://octopart-clicks.com/click/altium?manufacturer=Vishay%20Semiconductors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) | RCA06030000ZSEA (https://octopart-clicks.com/click/altium?manufacturer=Vishay%20Semiconductors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) | Farnell | 2616580, 2073345 (https://octopart-clicks.com/click/altium?manufacturer=Vishay%20Semiconductors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)
2 | R108-1, R108-2, R109-1, R109-2, R110-1, R110-2, R111-1, R111-2, R112-1, R112-2, R113-1, R113-2, R114-1, R114-2, R115-1, R115-2, R116-1, R116-2, R118-1, R118-2, R1300-1, R1300-2, R1301-1, R1301-2, R1302-1, R1302-2, R1303-1, R1303-2, R1304-1, R1304-2, R1305-1, R1305-2, R1306-1, R1306-2, R1307-1, R1307-2, R1308-1, R1308-2, R1309-1, R1309-2, R1310-1, R1310-2, R1311-1, R1311-2, R1312-1, R1312-2 | 46 | 100R | SMD Resistor 100R 0603 | 0603 | Panasonic (https://octopart-clicks.com/click/altium?manufacturer=Panasonic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) | ERJ-3EKF1000V (https://octopart-clicks.com/click/altium?manufacturer=Panasonic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) | Digikey, Farnell | P100HCT-ND, 1469752 (https://octopart-clicks.com/click/altium?manufacturer=Panasonic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)
3 | R1422-1, R1422-2, R1423-1, R1423-2 | 4 | 120R | SMD Resistor 120R 0603 | 0603 | Multicomp (https://octopart-clicks.com/click/altium?sku=2073369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) | MCMR06X1200FTL (https://octopart-clicks.com/click/altium?sku=2073369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) | Farnell | 2073369 (https://octopart-clicks.com/click/altium?sku=2073369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)
4 | R1100, R1101, R1102, R1103, R1104, R1105, R1106, R1107, R1108, R1109, R1110, R1111 | 12 | 150R | SMD Resistor 150R 0603 | 0603 | Vishay (https://octopart-clicks.com/click/altium?sku=1469760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) | CRCW0603150RFKEA (https://octopart-clicks.com/click/altium?sku=1469760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) | Farnell | 1469760 (https://octopart-clicks.com/click/altium?sku=1469760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)
5 | R1406-2, R1407-1 | 2 | 270R | SMD Resistor 270R 0603 | 0603 | Vishay (https://octopart-clicks.com/click/altium?sku=2141320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) | CRCW0603270RFKEA (https://octopart-clicks.com/click/altium?sku=2141320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) | Farnell | 2141320 (https://octopart-clicks.com/click/altium?sku=2141320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)
6 | R1421-1, R1421-2 | 2 | 820R | SMD Resistor 820R 0603 | 0603 | Vishay (https://octopart-clicks.com/click/altium?sku=1469841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) | CRCW0603820RFKEA (https://octopart-clicks.com/click/altium?sku=1469841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) | Farnell | 1469841 (https://octopart-clicks.com/click/altium?sku=1469841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)
7 | R610-1, R610-2 | 2 | 1k | SMD Resistor 1k 0603 | 0603 | Vishay Dale (https://octopart-clicks.com/click/altium?sku=1652848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) | CRCW06031K00FKTA (https://octopart-clicks.com/click/altium?sku=1652848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) | Farnell | 1652848 (https://octopart-clicks.com/click/altium?sku=1652848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)
8 | R1415-1, R1415-2, R1416-1, R1416-2, R1419-1, R1420-2 | 6 | 1k21 | SMD Resistor 1k21 0603 | 0603 | Vishay (https://octopart-clicks.com/click/altium?sku=1652852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) | CRCW06031K21FKEA (https://octopart-clicks.com/click/altium?sku=1652852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) | Farnell | 1652852 (https://octopart-clicks.com/click/altium?sku=1652852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)
9 | R606-1, R606-2 | 2 | 1k5 | SMD Resistor 1k5 0603 | 0603 | Vishay Dale (https://octopart-clicks.com/click/altium?sku=2616745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) | CRCW06031K50JNEA (https://octopart-clicks.com/click/altium?sku=2616745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) | Farnell | 2616745 (https://octopart-clicks.com/click/altium?sku=2616745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)
10 | R603-1, R603-2, R608-1, R608-2 | 4 | 124k | SMD Resistor 124k 0603 | 0603 | Vishay (https://octopart-clicks.com/click/altium?sku=2138508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) | CRCW0603124KFKEA (https://octopart-clicks.com/click/altium?sku=2138508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) | Farnell | 2138508 (https://octopart-clicks.com/click/altium?sku=2138508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)
11 | R1500, R1501, R1506, R1507, R1512, R1513, R1518, R1519, R1524, R1525, R1530, R1531 | 12 | 3k3 | SMD Resistor 3k3 0603 | 0603 | Vishay (https://octopart-clicks.com/click/altium?sku=1469793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) | CRCW06033K30FKEA (https://octopart-clicks.com/click/altium?sku=1469793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) | Farnell | 1469793 (https://octopart-clicks.com/click/altium?sku=1469793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)
12 | R100-1, R100-2, R101-1, R101-2, R102-1, R102-2, R103-1, R103-2, R104-1, R104-2, R105-1, R105-2, R106-1, R106-2, R107-1, R107-2, R600-1, R600-2, R604-1, R604-2, R609-1, R609-2, R700-1, R700-2, R701-1, R701-2, R702-1, R702-2, R703-1, R703-2, R704-1, R704-2, R705-1, R705-2, R706-1, R706-2, R707-1, R707-2, R708-1, R708-2, R801-1, R801-2, R904, R1112, R1404-1, R1404-2, R1408-1, R1408-2, R1411-1, R1411-2 | 50 | 10k | SMD Resistor 10k 0603 | 0603 | Multicomp (https://octopart-clicks.com/click/altium?sku=2073349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) | MCMR06X1002FTL (https://octopart-clicks.com/click/altium?sku=2073349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) | Farnell | 2073349 (https://octopart-clicks.com/click/altium?sku=2073349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)
13 | R905 | 1 | 86k6 | SMD Resistor 86k6 0603 | 0603 | Panasonic (https://octopart-clicks.com/click/altium?sku=2059490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) | ERJ-3EKF8662V (https://octopart-clicks.com/click/altium?sku=2059490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) | Farnell | 2059490 (https://octopart-clicks.com/click/altium?sku=2059490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)
14 | R602-1, R602-2 | 2 | 68k | SMD Resistor 68k 0603 | 0603
15 | R902 | 1 | 150k | SMD Resistor 150k 0603 | 0603
16 | R901 | 1 | 390k | SMD Resistor 390k 0603 | 0603 | Panasonic (https://octopart-clicks.com/click/altium?sku=2303278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) | ERJ3EKF3903V (https://octopart-clicks.com/click/altium?sku=2303278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) | Farnell | 2303278 (https://octopart-clicks.com/click/altium?sku=2303278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)
17 | R1400-2, R1401-1 | 2 | 1M | SMD Resistor 1M 0603 | 0603 | Vishay (https://octopart-clicks.com/click/altium?sku=1469746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) | CRCW06031M00FKEA (https://octopart-clicks.com/click/altium?sku=1469746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) | Farnell | 1469746 (https://octopart-clicks.com/click/altium?sku=1469746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)
18 | R607-1, R607-2 | 2 | 1R | SMD Resistor 1R 0805 | 0805 | Vishay Dale (https://octopart-clicks.com/click/altium?sku=2616757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) | CRCW08051R00FKEA (https://octopart-clicks.com/click/altium?sku=2616757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) | Farnell | 2616757 (https://octopart-clicks.com/click/altium?sku=2616757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)
19 | R900 | 1 | 39R | SMD Resistor 39R 0805 | 0805 | Panasonic (https://octopart-clicks.com/click/altium?sku=1750736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) | ERJP06F39R0V (https://octopart-clicks.com/click/altium?sku=1750736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) | Farnell | 1750736 (https://octopart-clicks.com/click/altium?sku=1750736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)
20 | R1400-1, R1401-2 | 2 | 100R | SMD Resistor 100R 0805 | 0805 | Vishay Dale (https://octopart-clicks.com/click/altium?sku=1469862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) | CRCW0805100RFKEA (https://octopart-clicks.com/click/altium?sku=1469862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) | Farnell | 1469862 (https://octopart-clicks.com/click/altium?sku=1469862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)
21 | R1502, R1503, R1504, R1505, R1508, R1509, R1510, R1511, R1514, R1515, R1516, R1517, R1520, R1521, R1522, R1523, R1526, R1527, R1528, R1529, R1532, R1533, R1534, R1535 | 24 | 68R | SMD Resistor 68R 2010 | 2010 | Panasonic (https://octopart-clicks.com/click/altium?sku=2323988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) | ERJ-12ZYJ680U (https://octopart-clicks.com/click/altium?sku=2323988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) | Farnell | 2323988 (https://octopart-clicks.com/click/altium?sku=2323988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)
22 | C1404-1, C1404-2, C1405-1, C1405-2 | 4 | 100p/50V | MLCC | 0603 | KEMET (https://octopart-clicks.com/click/altium?sku=1414603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) | C0603C101J5GACTU (https://octopart-clicks.com/click/altium?sku=1414603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) | Farnell | 1414603 (https://octopart-clicks.com/click/altium?sku=1414603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)
23 | C102-1, C102-2, C103-1, C103-2, C104-1, C104-2, C105-1, C105-2, C106-1, C106-2, C107-1, C107-2, C108-1, C108-2, C109-1, C109-2, C111-1, C111-2, C115-1, C115-2, C600-1, C600-2, C1300-1, C1300-2, C1301-1, C1301-2, C1304-1, C1304-2, C1305-1, C1305-2, C1308-1, C1308-2, C1309-1, C1309-2, C1312-1, C1312-2, C1313-1, C1313-2, C1316-1, C1316-2, C1317-1, C1317-2, C1320-1, C1320-2, C1321-1, C1321-2 | 46 | 10n/100V | MLCC | 0603 | KEMET (https://octopart-clicks.com/click/altium?sku=1301715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) | C0603X103K1RACAUTO (https://octopart-clicks.com/click/altium?sku=1301715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) | Farnell | 1301715 (https://octopart-clicks.com/click/altium?sku=1301715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)
24 | C100-1, C100-2, C400, C401, C402, C403, C404, C405, C406, C407, C601-1, C601-2, C604-1, C604-2, C605-1, C605-2, C700-1, C700-2, C701-1, C701-2, C800-1, C800-2, C801-1, C801-2, C906, C1100 | 26 | 100n/50V | MLCC | 0603 | Murata (https://octopart-clicks.com/click/altium?sku=490-6049-1-ND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) | GCM188L81H104KA57D (https://octopart-clicks.com/click/altium?sku=490-6049-1-ND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) | Digi-Key | 490-6049-1-ND (https://octopart-clicks.com/click/altium?sku=490-6049-1-ND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)
25 | C902 | 1 | 470p/100V | MLCC | 0805 | Multicomp (https://octopart-clicks.com/click/altium?sku=1759283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) | MC0805B471K101CT (https://octopart-clicks.com/click/altium?sku=1759283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) | Farnell | 1759283 (https://octopart-clicks.com/click/altium?sku=1759283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)
27 | C101-1, C101-2, C110-1, C110-2, C112-1, C112-2, C113-1, C113-2, C114-1, C114-2, C606-1, C606-2, C904, C907, C1401-1, C1401-2, C1402-1, C1402-2, C1403-1, C1403-2 | 20 | 1u/35V | MLCC | 0603 | Murata (https://octopart-clicks.com/click/altium?sku=1907508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) | GRM188R7YA105KA12D (https://octopart-clicks.com/click/altium?sku=1907508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) | Farnell | 1907508 (https://octopart-clicks.com/click/altium?sku=1907508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)
28 | C607-1, C607-2, C608-1, C608-2 | 4 | 2u2/10V | MLCC | 0805 | KEMET (https://octopart-clicks.com/click/altium?sku=2478259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) | C0805C225K8RACAUTO (https://octopart-clicks.com/click/altium?sku=2478259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) | Farnell | 2478259 (https://octopart-clicks.com/click/altium?sku=2478259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)
29 | C603-1, C603-2, C1400-1, C1400-2 | 4 | 100n/100V | MLCC | 0805 | Multicomp (https://octopart-clicks.com/click/altium?sku=2320821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) | MC0805B104K101CT (https://octopart-clicks.com/click/altium?sku=2320821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) | Farnell | 2320821 (https://octopart-clicks.com/click/altium?sku=2320821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)
30 | C900, C901 | 2 | 2u2/250V | MLCC | 2220 | TDK (https://octopart-clicks.com/click/altium?sku=445-7997-2-ND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) | CGA9P3X7T2E225M250KE (https://octopart-clicks.com/click/altium?sku=445-7997-2-ND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) | Digi-Key | 445-7997-2-ND (https://octopart-clicks.com/click/altium?sku=445-7997-2-ND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)
32 | C903 | 1 | 4n7/1000V | MLCC | 1812 | KEMET (https://octopart-clicks.com/click/altium?sku=1702159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) | C1812C472KDRACTU (https://octopart-clicks.com/click/altium?sku=1702159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) | Farnell | 1702159 (https://octopart-clicks.com/click/altium?sku=1702159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)
33 | C602-1, C602-2 | 2 | 1u/250V | MLCC | 1812 | TDK (https://octopart-clicks.com/click/altium?sku=2435499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) | CGA8P3X7T2E105K250KA (https://octopart-clicks.com/click/altium?sku=2435499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) | Farnell | 2435499 (https://octopart-clicks.com/click/altium?sku=2435499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)
34 | C905 | 1 | 22u/50V | MLCC | 2220 | KEMET (https://octopart-clicks.com/click/altium?sku=399-5797-1-ND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) | C2220C226M5R2CAUTO (https://octopart-clicks.com/click/altium?sku=399-5797-1-ND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) | Digi-Key | 399-5797-1-ND (https://octopart-clicks.com/click/altium?sku=399-5797-1-ND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)
35 | D1100 | 1 | BAT54C,215 | Schottky Barrier Diode, 30 V, 3-Pin SOT23, RoHS, Tape and Reel |  | NXP Semiconductors | BAT54C,215
36 | D1401-1, D1401-2 | 2 | SMAJ60A-E3/61 | Transient Voltage Suppressor, 6.40 to 231 V, 60 V Stand-off Voltage, Uni-Directional, -55 to 155 degC, 2-pin DO-214AC, Pb-Free, Tape and Reel |  | Vishay Semiconductors (https://octopart-clicks.com/click/altium?sku=1837055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) | SMAJ60A-E3/61 (https://octopart-clicks.com/click/altium?sku=1837055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) | Farnell | 1837055 (https://octopart-clicks.com/click/altium?sku=1837055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)
37 | D900 | 1 | PDS3200 | Schottky Diode 3A 200V 780mV |  | Diodes (https://octopart-clicks.com/click/altium?sku=1713904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) | PDS3200-13 (https://octopart-clicks.com/click/altium?sku=1713904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) | Farnell | 1713904 (https://octopart-clicks.com/click/altium?sku=1713904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)
38 | D901, D1400-1, D1400-2 | 3 | DFLS1100-7 | 1 A High Voltage Schottky Barrier Rectifier, 0.62 V, -55 to 175 degC, 2- Pin POWERDI123, Pb-Free, Tape and Reel |  | Diodes (https://octopart-clicks.com/click/altium?sku=1713889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) | DFLS1100-7 (https://octopart-clicks.com/click/altium?sku=1713889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) | Farnell | 1713889 (https://octopart-clicks.com/click/altium?sku=1713889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)
39 | Z1300-1, Z1300-2, Z1301-1, Z1301-2, Z1302-1, Z1302-2, Z1303-1, Z1303-2, Z1304-1, Z1304-2, Z1305-1, Z1305-2, Z1306-1, Z1306-2, Z1307-1, Z1307-2, Z1308-1, Z1308-2, Z1309-1, Z1309-2, Z1310-1, Z1310-2, Z1311-1, Z1311-2 | 24 | MMSZ4692T1G | Zener Voltage Regulator, 500 mW, 2-Pin SOD-123, Pb-Free, Tape and Reel |  | ON Semiconductor (https://octopart-clicks.com/click/altium?sku=MMSZ4692T1GOSCT-ND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) | MMSZ4692T1G (https://octopart-clicks.com/click/altium?sku=MMSZ4692T1GOSCT-ND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) | Digi-Key | MMSZ4692T1GOSCT-ND (https://octopart-clicks.com/click/altium?sku=MMSZ4692T1GOSCT-ND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)
40 | LD1400-1, LD1400-2 | 2 | green | LED |  | Kingbright (https://octopart-clicks.com/click/altium?sku=2099223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) | KPT-1608SGC (https://octopart-clicks.com/click/altium?sku=2099223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) | Farnell | 2099223 (https://octopart-clicks.com/click/altium?sku=2099223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)
41 | F300, F314 | 2 | fuse_0.5A_0448.500MR | Fuse, Surface Mount, NANO2 Series, 500 mA, 125 VAC, 32 VDC, Very Fast Acting, SMD |  | Littelfuse (https://octopart-clicks.com/click/altium?sku=1596919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) | 0448.500MR (https://octopart-clicks.com/click/altium?sku=1596919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) | Farnell | 1596919 (https://octopart-clicks.com/click/altium?sku=1596919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)
42 | F301, F302, F303, F304, F305, F306, F307, F308, F309, F310, F311, F312, F313 | 13 | fuse_0.25A_0466.250NR | Fuse, Surface Mount, 466 Series, 250 mA, 125 VAC, 125 VDC, Very Fast Acting, 1206 |  | Littelfuse (https://octopart-clicks.com/click/altium?sku=9921826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) | 0466.250NR (https://octopart-clicks.com/click/altium?sku=9921826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) | Farnell | 9921826 (https://octopart-clicks.com/click/altium?sku=9921826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)
43 | F900 | 1 | fuse_1.25A_04661.25NR | Fuse, Surface Mount, 466 Series, 1.25 A, 63 VAC, 63 VDC, Very Fast Acting, 1206 |  | Littelfuse (https://octopart-clicks.com/click/altium?sku=1596526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) | 0466.125NR (https://octopart-clicks.com/click/altium?sku=1596526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) | Farnell | 1596526 (https://octopart-clicks.com/click/altium?sku=1596526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)
44 | L900 | 1 | 74404042100 | WE-LQS SMD Power Inductor, L=10 µH |  | Wurth Electronics (https://octopart-clicks.com/click/altium?sku=2431496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) | 74404042100 (https://octopart-clicks.com/click/altium?sku=2431496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) | Farnell | 2431496 (https://octopart-clicks.com/click/altium?sku=2431496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)
45 | L600-1, L600-2 | 2 | 220µH | Power Inductor |  | Laird Steward (https://octopart-clicks.com/click/altium?sku=240-2742-1-ND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) | TYS6045221M-10 (https://octopart-clicks.com/click/altium?sku=240-2742-1-ND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) | Digi-Key | 240-2742-1-ND (https://octopart-clicks.com/click/altium?sku=240-2742-1-ND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)
46 | T1500, T1501, T1502, T1503, T1504, T1505, T1506, T1507, T1508, T1509, T1510, T1511 | 12 | NX2301P,215 | P-Channel Trench MOSFET, -20 V, -2 A, -55 to 150 degC, 3-Pin SOT23, Tape and Reel |  | NXP Semiconductors (https://octopart-clicks.com/click/altium?sku=771-NX2301P215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) | NX2301P,215 (https://octopart-clicks.com/click/altium?sku=771-NX2301P215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) | Mouser | 771-NX2301P215 (https://octopart-clicks.com/click/altium?sku=771-NX2301P215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)
47 | Q600-1, Q600-2 | 2 | PBSS4112PANP | Dual NPN/PNP Transistor
48 | IC100-1, IC100-2, IC101-1, IC101-2, IC102-1, IC102-2 | 6 | ADG728BRUZ | CMOS, Low Voltage, 2-Wire Serially Controlled, Matrix Switch, -40 to 85 degC, 16-pin SOP (RU-16), Tube |  | Analog Devices (https://octopart-clicks.com/click/altium?sku=9604383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) | ADG728BRUZ (https://octopart-clicks.com/click/altium?sku=9604383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) | Farnell | 9604383 (https://octopart-clicks.com/click/altium?sku=9604383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)
49 | U700-1, U700-2 | 2 | TCA6408APWR | Low-Voltage 8-Bit I2C and SMBus I/O Expander, 1.65 to 5.5 V, -40 to 85 degC, 16-pin TSSOP (PW), Green (RoHS & no Sb/Br) |  | Texas Instruments (https://octopart-clicks.com/click/altium?sku=1903303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) | TCA6408APWR (https://octopart-clicks.com/click/altium?sku=1903303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) | Farnell | 1903303 (https://octopart-clicks.com/click/altium?sku=1903303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)
50 | IC900 | 1 | LT8302HS8E#PBF | Micropower No-Opto Isolated Flyback Converter, 2.8 to 42 V, -40 to 150 degC, 8-Pin SOIC (S8E), RoHS, Tube |  | Analog Devices / Linear Technology (https://octopart-clicks.com/click/altium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) | LT8302HS8E#PBF (https://octopart-clicks.com/click/altium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) | Digi-Key | LT8302HS8E#PBF-ND (https://octopart-clicks.com/click/altium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)
51 | U100-1, U100-2, U101-1, U101-2 | 4 | AD8628ARTZ-R2 | Single Channel RRIO Operational Amplifier, 2.5 MHz BW, 1 V/us SR, Industrial, 5-pin SOT23 (RJ-5), Reel |  | Analog Devices (https://octopart-clicks.com/click/altium?sku=AD8628ARTZ-R2CT-ND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) | AD8628ARTZ-R2 (https://octopart-clicks.com/click/altium?sku=AD8628ARTZ-R2CT-ND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) | Digi-Key | AD8628ARTZ-R2CT-ND (https://octopart-clicks.com/click/altium?sku=AD8628ARTZ-R2CT-ND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)
52 | IC1400-1, IC1400-2 | 2 | LTC6811HG-1#PBF | Multicell Battery Monitor, 60 V Vin MAX, 48-pin SOP (G-48), -40 to 125 degC, Pb-Free |  | Analog Devices / Linear Technology (https://octopart-clicks.com/click/altium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) | LTC6811HG-1#PBF (https://octopart-clicks.com/click/altium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) | Digi-Key | LTC6811HG-1#PBF-ND (https://octopart-clicks.com/click/altium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)
53 | U1100, U1101, U1102, U1103, U1104, U1105, U1106, U1107, U1108, U1109, U1110, U1111 | 12 | ACPL-217 | Optocoupler, Transistor Output, 1 Channel |  | Broadcom (https://octopart-clicks.com/click/altium?sku=1602623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) | ACPL-217-56BE (https://octopart-clicks.com/click/altium?sku=1602623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) | Farnell | 1602623 (https://octopart-clicks.com/click/altium?sku=1602623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)
54 | IC801-1, IC801-2 | 2 | MCP9800A0T-M/OT | 2-Wire High-Accuracy Temperature Sensor, Slave Address 000, 5-Pin SOT-23, -55°C to +125°C Temperature, Tape and Reel |  | Microchip (https://octopart-clicks.com/click/altium?sku=1439485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) | MCP9800A0T-M/OT (https://octopart-clicks.com/click/altium?sku=1439485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) | Farnell | 1439485 (https://octopart-clicks.com/click/altium?sku=1439485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)
55 | U600-1, U600-2 | 2 | LM5161QPWPRQ1 | Automotive DC/DC buck converter |  | Texas Instruments (https://octopart-clicks.com/click/altium?sku=296-47791-1-ND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) | LM5161QPWPRQ1 (https://octopart-clicks.com/click/altium?sku=296-47791-1-ND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) | Digi-Key | 296-47791-1-ND (https://octopart-clicks.com/click/altium?sku=296-47791-1-ND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)
56 | TR1400-1, TR1400-2 | 2 | HM2102NL | Pulse HM2102NL BMS Transformer |  | Pulse Electronics Network (https://octopart-clicks.com/click/altium?manufacturer=Pulse%20Electronics%20Network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) | HM2102NLT (https://octopart-clicks.com/click/altium?manufacturer=Pulse%20Electronics%20Network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) | Digi-Key | 1840-1034-1-ND (https://octopart-clicks.com/click/altium?manufacturer=Pulse%20Electronics%20Network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)
57 | TR900 | 1 | WE_750313457 | MID-FLYLT Flyback Transformers for Linear Technology |  | Wurth Electronics (https://octopart-clicks.com/click/altium?sku=1297-1136-1-ND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) | 750313457 (https://octopart-clicks.com/click/altium?sku=1297-1136-1-ND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) | Digi-Key | 1297-1136-1-ND (https://octopart-clicks.com/click/altium?sku=1297-1136-1-ND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)
59 | X1000 | 1 | samtec_TSW-102-07-G-D | Board-To-Board Connector, Vertical, 2.54 mm, 4 Contacts, Header, TSW Series, Through Hole, 2 Rows |  | Samtec (https://octopart-clicks.com/click/altium?sku=2025248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) | TSW-102-07-G-D (https://octopart-clicks.com/click/altium?sku=2025248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) | Farnell | 2025248 (https://octopart-clicks.com/click/altium?sku=2025248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)
61 | X401, X404 | 2 | gen_pinheader_2.54_2x5 | Standard Pinheader, THD, gerade, 2.54mm, 2-reihig |  | Samtec (https://octopart-clicks.com/click/altium?sku=2578720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) | TSW-105-07-G-D (https://octopart-clicks.com/click/altium?sku=2578720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) | Farnell | 2578720 (https://octopart-clicks.com/click/altium?sku=2578720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)
62 | X400, X403 | 2 | gen_pinheader_2.54_2x9 | Standard Pinheader, THD, gerade, 2.54mm, 2-reihig |  | Samtec (https://octopart-clicks.com/click/altium?sku=2025256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) | TSW-109-07-G-D (https://octopart-clicks.com/click/altium?sku=2025256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) | Farnell | 2025256 (https://octopart-clicks.com/click/altium?sku=2025256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)
63 | X402 | 1 | gen_pinheader_2.54_2x10 | Standard Pinheader, THD, gerade, 2.54mm, 2-reihig |  | Samtec (https://octopart-clicks.com/click/altium?sku=2025257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) | TSW-110-07-G-D (https://octopart-clicks.com/click/altium?sku=2025257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) | Farnell | 2025257 (https://octopart-clicks.com/click/altium?sku=2025257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)
64 | X500, X501, X502, X503, X1001, X1002 | 6 | molex_microfit_3_01x2_THT | Micro-Fit 3.0 Right Angle Header, 3.00mm Pitch, Dual Row, 2 Circuits, with Snap-in Plastic Peg PCB Lock, Tin, Glow Wire Capable, Black, 43045-0200 |  | Molex (https://octopart-clicks.com/click/altium?sku=1012251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) | 43045-0200 (https://octopart-clicks.com/click/altium?sku=1012251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) | Farnell | 1012251 (https://octopart-clicks.com/click/altium?sku=1012251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)
65 | X201, X202 | 2 | molex_microfit_3_08x2_THT | Micro-Fit 3.0 Right Angle Header, 3.00mm Pitch, Dual Row, 16 Circuits, with Snap-in Plastic Peg PCB Lock, Tin, Glow Wire Capable, Black, 43045-1600 |  | Molex (https://octopart-clicks.com/click/altium?sku=9961380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) | 43045-1600 (https://octopart-clicks.com/click/altium?sku=9961380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) | Farnell | 9961380 (https://octopart-clicks.com/click/altium?sku=9961380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)
66 | X200 | 1 | molex_microfit_3_12x2_THT | Micro-Fit 3.0 Right Angle Header, 3.00mm Pitch, Dual Row, 24 Circuits, with Snap-in Plastic Peg PCB Lock, Tin, Glow Wire Capable, Black, 43045-2400 |  | Molex (https://octopart-clicks.com/click/altium?sku=1012245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) | 43045-2400 (https://octopart-clicks.com/click/altium?sku=1012245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) | Farnell | 1012245 (https://octopart-clicks.com/click/altium?sku=1012245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)

Sheet: DATA
slave-12-ltc6811-1.PrjPcb
28.03.2019 11:59:38
default
