ArakniD/foxbms/hardware/hw-extension/v1.0.5/Assembly default/bom/bom-extension(default).xlsx

Sheet: BOM
BOM for extension, Variant default
Generated on 26.10.2018 08:24:22
Line # | Designator | Quantity | Name | Description | Case EIA | Manufacturer 1 | Manufacturer Part Number 1 | Supplier 1 | Supplier Part Number 1 | MOQ | multiple | order quantity | Automotive Qualified
 | C801, C1102, C1301, C1502, C1703, C1902 | 6 | 1u/50V | MLCC | 0603 | Taiyo Yuden (https://octopart-clicks.com/click/altium?sku=2779055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) | UMK107AB7105KA-T (https://octopart-clicks.com/click/altium?sku=2779055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) | Farnell | 2779055 (https://octopart-clicks.com/click/altium?sku=2779055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) |  | 1 | 6
 | C802, C803, C805, C806, C807, C1101, C1103, C1104, C1105, C1106, C1302, C1303, C1304, C1305, C1306, C1501, C1701, C1702, C1704, C1705, C1706, C1707, C1708, C1901, C1903, C1904, C1905, C1906, C1907 | 29 | 100n/50V | MLCC | 0603 | Vishay (https://octopart-clicks.com/click/altium?sku=2525267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) | VJ0603Y104KXAAC31X (https://octopart-clicks.com/click/altium?sku=2525267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) | Farnell | 2525267 (https://octopart-clicks.com/click/altium?sku=2525267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) |  | 1 | 29
 | C804 | 1 | 4n7/50V | MLCC | 0603 | KEMET (https://octopart-clicks.com/click/altium?sku=2904754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) | C0603C472J5RACAUTO (https://octopart-clicks.com/click/altium?sku=2904754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) | Farnell | 2904754 (https://octopart-clicks.com/click/altium?sku=2904754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) |  | 1 | 1 | True
 | D801 | 1 | PESD1CAN | CAN Bus ESD Protection Diode, 200 W, 24 V, -65 to 150 degC, 3-Pin SOT23, RoHS, Tape and Reel |  | NXP Semiconductors | PESD1CAN |  |  |  | 1 | 1
 | D1101, D1102, D1103, D1901, D1902, D1903, D1904 | 7 | CDSOD323-T05 | TVS Diode, CDSOD323 Series, Unidirectional, 5 V, 18.3 V, SOD-323, 2 Pins |  | Bourns (https://octopart-clicks.com/click/altium?sku=2341914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) | CDSOD323-T05 (https://octopart-clicks.com/click/altium?sku=2341914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) | Farnell | 2341914 (https://octopart-clicks.com/click/altium?sku=2341914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) |  | 1 | 7
 | D1701, D1702, D1703, D1704, D1705 | 5 | MM3Z3V3ST1G | Zener Voltage Regulator, 300 mW, Tight Tolerance Portfolio, 2-Pin SOD-323, Pb-Free, Tape and Reel |  | ON Semiconductor | MM3Z3V3ST1G |  |  |  | 1 | 5
 | F1001, F1002, F1003 | 3 | Schurter SMD Fuse 4.0A UMT 3403.0172.11 | Schurter SMD Fuse 4.0A UMT 3403.0172.11 |  | Schurter (https://octopart-clicks.com/click/altium?sku=486-1253-ND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) | 3403.0172.11 (https://octopart-clicks.com/click/altium?sku=486-1253-ND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) | Digi-Key | 486-1253-ND (https://octopart-clicks.com/click/altium?sku=486-1253-ND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) |  | 1 | 3
 | IC801 | 1 | KA7805ERT | 3-Terminal 1 A Positive Voltage Regulator |  | ON Semiconductor / Fairchild (https://octopart-clicks.com/click/altium?manufacturer=ON%20Semiconductor%20%2F%20Fairchild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) | KA7805ERTF (https://octopart-clicks.com/click/altium?manufacturer=ON%20Semiconductor%20%2F%20Fairchild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) | Farnell | 2102585 (https://octopart-clicks.com/click/altium?manufacturer=ON%20Semiconductor%20%2F%20Fairchild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) |  | 1 | 1
 | IC802 | 1 | CPC1008N | Single-Pole, Normally Open 4-Pin SOP OptoMOS Relay |  | CPC (https://octopart-clicks.com/click/altium?sku=1653755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) | CPC1008N (https://octopart-clicks.com/click/altium?sku=1653755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) | Farnell | 1653755 (https://octopart-clicks.com/click/altium?sku=1653755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) |  | 1 | 1
 | IC803 | 1 | TJA1052IT/5Y | Galvanically Isolated High-Speed CAN Transceiver, -40 to 125 degC, 16-Pin SOIC, RoHS, Tape and Reel |  | NXP Semiconductors (https://octopart-clicks.com/click/altium?sku=2400552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) | TJA1052IT/5Y (https://octopart-clicks.com/click/altium?sku=2400552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) | Farnell | 2400552 (https://octopart-clicks.com/click/altium?sku=2400552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) |  | 1 | 1
 | IC1001, IC1002, IC1003, IC2001, IC2002, IC2003, IC2004, IC2005, IC2006 | 9 | AQV252G2SX | PhotoMOS Relay |  | Panasonic (https://octopart-clicks.com/click/altium?sku=2302216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) | AQV252G2SX (https://octopart-clicks.com/click/altium?sku=2302216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) | Farnell | 2302216 (https://octopart-clicks.com/click/altium?sku=2302216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) |  | 1 | 9
 | IC1101, IC1301, IC1901 | 3 | UA78L05CPK | Positive-Voltage Regulator, 100 mA, 0 to 125 degC, 3-Pin SOT-89 (PK), Green (RoHS & no Sb/Br), Tape and Reel |  | Texas Instruments (https://octopart-clicks.com/click/altium?sku=2112604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) | UA78L05CPK (https://octopart-clicks.com/click/altium?sku=2112604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) | Farnell | 2112604 (https://octopart-clicks.com/click/altium?sku=2112604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) |  | 1 | 3
 | IC1102 | 1 | ADUM3300CRWZ | Triple Channel Digital Isolator, Enhanced System-Level ESD Reliability, 2.5 KV rms Insulation Rating, 90 Mbps Data Rate, 32 ns Delay, Industrial, 16-pin SOIC (RW-16), Tube |  | Analog Devices (https://octopart-clicks.com/click/altium?sku=584-ADUM3300CRWZ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) | ADUM3300CRWZ (https://octopart-clicks.com/click/altium?sku=584-ADUM3300CRWZ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) | Mouser | 584-ADUM3300CRWZ (https://octopart-clicks.com/click/altium?sku=584-ADUM3300CRWZ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) |  | 1 | 1
 | IC1302 | 1 | LT1785 | Transceiver RS422/RS485, Fault Protected, 4.75V-5.25V supply, SOIC-8 |  | Analog Devices / Linear Technology (https://octopart-clicks.com/click/altium?sku=1663498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) | LT1785CS8#PBF (https://octopart-clicks.com/click/altium?sku=1663498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) | Farnell | 1663498 (https://octopart-clicks.com/click/altium?sku=1663498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) |  | 1 | 1
 | IC1303 | 1 | ADUM3401CRWZ | Quad Channel Digital Isolator, Enhanced System-Level ESD Reliability, 2.5 KV rms Insulation Rating, 90 Mbps Data Rate, 32 ns Delay, Industrial, 16-pin SOIC (RW-16), Tube |  | Analog Devices (https://octopart-clicks.com/click/altium?sku=1274129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) | ADUM3401CRWZ (https://octopart-clicks.com/click/altium?sku=1274129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) | Farnell | 1274129 (https://octopart-clicks.com/click/altium?sku=1274129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) |  | 1 | 1
 | IC1701 | 1 | ADR3425ARJZ-R2 | Micropower, High Accuracy Voltage Reference, 2.5 V Output, 2.7 to 5.5 V Supply, Industrial, 6-pin SOT23 (RJ-6), Reel |  | Analog Devices (https://octopart-clicks.com/click/altium?sku=2377039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) | ADR3425ARJZ-R2 (https://octopart-clicks.com/click/altium?sku=2377039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) | Farnell | 2377039 (https://octopart-clicks.com/click/altium?sku=2377039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) |  | 1 | 1
 | IC1902, IC1903 | 2 | ADUM3402BRWZ | Quad Channel Digital Isolator, Enhanced System-Level ESD Reliability, 2.5 KV rms Insulation Rating, 10 Mbps Data Rate, 50 ns Delay, Industrial, 16-pin SOIC (RW-16), Tube |  | Analog Devices (https://octopart-clicks.com/click/altium?sku=1274127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) | ADUM3402BRWZ (https://octopart-clicks.com/click/altium?sku=1274127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) | Farnell | 1274127 (https://octopart-clicks.com/click/altium?sku=1274127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) |  | 1 | 2
 | JP2201, JP2202 | 2 | X2x12 | Board-To-Board Connector, Vertical, Low Profile, 2.54 mm, 24 Contacts, Header, TLW Series, Through Hole, 2 Rows |  | Samtec (https://octopart-clicks.com/click/altium?sku=SAM1096-12-ND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) | TLW-112-06-G-D (https://octopart-clicks.com/click/altium?sku=SAM1096-12-ND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) | Digikey | SAM1096-12-ND (https://octopart-clicks.com/click/altium?sku=SAM1096-12-ND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) |  | 1 | 2
 | L801 | 1 | 51uH | Common Mode Choke |  | TDK EPCOS (https://octopart-clicks.com/click/altium?sku=871-B82789C0513H002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) | B82789C0513H002 (https://octopart-clicks.com/click/altium?sku=871-B82789C0513H002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) | Mouser | 871-B82789C0513H002 (https://octopart-clicks.com/click/altium?sku=871-B82789C0513H002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) |  | 1 | 1
 | L1501 | 1 | BLM21AG471SN1J | Chip Ferrite Bead for General Signal lines, 470 Ohm, 700 mA, -55 to 125 degC, 2 x 1.25 x 1.05 mm SMD, Tape and Reel |  | Laird (https://octopart-clicks.com/click/altium?sku=2292413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) | HZ0805G471R-10 (https://octopart-clicks.com/click/altium?sku=2292413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) | Farnell | 2292413 (https://octopart-clicks.com/click/altium?sku=2292413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) |  | 1 | 1
 | R801, R802 | 2 | 62R | SMD Resistor 62R 0603 | 0603 | Multicomp (https://octopart-clicks.com/click/altium?sku=2073943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) | MCMR12X62R0FTL (https://octopart-clicks.com/click/altium?sku=2073943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) | Farnell | 2073943 (https://octopart-clicks.com/click/altium?sku=2073943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) |  | 1 | 2
 | R803, R805, R901, R1002, R1005, R1008, R1104, R1105, R1106, R1502, R1503, R1504, R1505, R1506, R1507, R1903, R1904, R1907, R1908, R2003, R2004, R2009, R2010, R2015, R2016 | 25 | 10k | SMD Resistor 10k 0603 | 0603 | Multicomp (https://octopart-clicks.com/click/altium?sku=2073349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) | MCMR06X1002FTL (https://octopart-clicks.com/click/altium?sku=2073349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) | Farnell | 2073349 (https://octopart-clicks.com/click/altium?sku=2073349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) |  | 1 | 25
 | R804, R1003, R1006, R1009, R2005, R2006, R2011, R2012, R2017, R2018 | 10 | 430R | SMD Resistor 430R 0603 | 0603 | Multicomp (https://octopart-clicks.com/click/altium?sku=2074259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) | MCSR06X4300FTL (https://octopart-clicks.com/click/altium?sku=2074259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) | Farnell | 2074259 (https://octopart-clicks.com/click/altium?sku=2074259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) |  | 1 | 10
 | R806, R902, R1001, R1004, R1007, R2001, R2002, R2007, R2008, R2013, R2014 | 11 | 10R | SMD Resistor 10R 0603 | 0603 | Multicomp (https://octopart-clicks.com/click/altium?sku=2073361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) | MCMR06X10R0FTL (https://octopart-clicks.com/click/altium?sku=2073361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) | Farnell | 2073361 (https://octopart-clicks.com/click/altium?sku=2073361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) |  | 1 | 11
 | R1101, R1102, R1103, R1901, R1902, R1905, R1906 | 7 | 47R | SMD Resistor 47R 0603 | 0603 | Panasonic (https://octopart-clicks.com/click/altium?sku=2303030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) | ERJ-3EKF47R0V (https://octopart-clicks.com/click/altium?sku=2303030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) | Farnell | 2303030 (https://octopart-clicks.com/click/altium?sku=2303030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) |  | 1 | 7
 | R1501 | 1 | 47k | SMD Resistor 47k 0603 | 0603 | Multicomp (https://octopart-clicks.com/click/altium?sku=2073510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) | MCMR06X4702FTL (https://octopart-clicks.com/click/altium?sku=2073510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) | Farnell | 2073510 (https://octopart-clicks.com/click/altium?sku=2073510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) |  | 1 | 1
 | R1701, R1703, R1705, R1707, R1709 | 5 | 0R | SMD Resistor 0R 0603 | 0603 | Multicomp (https://octopart-clicks.com/click/altium?sku=2073345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) | MCMR06X000PTL (https://octopart-clicks.com/click/altium?sku=2073345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) | Farnell | 2073345 (https://octopart-clicks.com/click/altium?sku=2073345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) |  | 1 | 5
 | R1702, R1704, R1706, R1708, R1710 | 5 | 4k75 | SMD Resistor 4k75 0603 | 0603 | Multicomp (https://octopart-clicks.com/click/altium?sku=2073517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) | MCMR06X4751FTL (https://octopart-clicks.com/click/altium?sku=2073517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) | Farnell | 2073517 (https://octopart-clicks.com/click/altium?sku=2073517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) |  | 1 | 5
 | SLOT1501 | 1 | MOLEX_47352-1001 | 1.10mm Pitch Memorycard Card Connector, Push-Push Type, with VSS (Supply Voltage Ground) Detect Switch, Lead-Free |  | Molex (https://octopart-clicks.com/click/altium?sku=2424133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) | 47352-1001 (https://octopart-clicks.com/click/altium?sku=2424133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) | Farnell | 2424133 (https://octopart-clicks.com/click/altium?sku=2424133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) |  | 1 | 1 | False
 | SV901 | 1 | samtec_TLW-104-06-G-D | Board-To-Board Connector, Vertical, Low Profile, 2.54 mm, 8 Contacts, Header, TLW Series, Through Hole, 2 Rows |  | Samtec (https://octopart-clicks.com/click/altium?sku=SAM1096-04-ND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) | TLW-104-06-G-D (https://octopart-clicks.com/click/altium?sku=SAM1096-04-ND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) | Digikey | SAM1096-04-ND (https://octopart-clicks.com/click/altium?sku=SAM1096-04-ND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) |  | 1 | 1
 | T801, T1001, T1002, T1003, T2001, T2002, T2003, T2004, T2005, T2006 | 10 | IRLML0100TRPBF | MOSFET-Transistor, n-Kanal, 1.6 A, 100 V, 0.178 ohm, 10 V, 2.5 V |  | International Rectifier (https://octopart-clicks.com/click/altium?sku=1783928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) | IRLML0100TRPBF (https://octopart-clicks.com/click/altium?sku=1783928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) | Farnell | 1783928 (https://octopart-clicks.com/click/altium?sku=1783928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) |  | 1 | 10
 | T901 | 1 | BUK964R8-60E,118 | N-Channel TrenchMOS Logic Level FET, 60 V, 100 A, 3-Pin SOT404, Tape and Reel |  | NXP Semiconductors (https://octopart-clicks.com/click/altium?manufacturer=NXP%20Semiconductors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) | BUK964R8-60E,118 (https://octopart-clicks.com/click/altium?manufacturer=NXP%20Semiconductors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) | Digi-Key | 1727-7261-6-ND (https://octopart-clicks.com/click/altium?manufacturer=NXP%20Semiconductors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) |  | 1 | 1 | Y
 | T1501 | 1 | BSS84P | P-Channel SIPMOS Small-Signal-Transistor, -60 V VDS, -0.17 A ID, -55 to 150 degC, PG-SOT23, Reel, Green |  | Infineon | BSS84P |  |  |  | 1 | 1
 | X801, X1201, X1202, X1203 | 4 | molex_microfit_3_02x2_THT | Micro-Fit 3.0 Right Angle Header, 3.00mm Pitch, Dual Row, 4 Circuits, with Snap-in Plastic Peg PCB Lock, Tin, Glow Wire Capable, Black, 43045-0400 |  | Molex (https://octopart-clicks.com/click/altium?sku=9733019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) | 43045-0400 (https://octopart-clicks.com/click/altium?sku=9733019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) | Farnell | 9733019 (https://octopart-clicks.com/click/altium?sku=9733019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) |  | 1 | 4
 | X1301 | 1 | molex_microfit_3_03x2_THT | Micro-Fit 3.0 Right Angle Header, 3.00mm Pitch, Dual Row, 6 Circuits, with Snap-in Plastic Peg PCB Lock, Tin, Glow Wire Capable, Black, 43045-0600 |  | Molex (https://octopart-clicks.com/click/altium?sku=1012252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) | 43045-0600 (https://octopart-clicks.com/click/altium?sku=1012252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) | Farnell | 1012252 (https://octopart-clicks.com/click/altium?sku=1012252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) |  | 1 | 1
 | X1701, X2001 | 2 | molex_microfit_3_06x2_THT | Micro-Fit 3.0 Right Angle Header, 3.00mm Pitch, Dual Row, 12 Circuits, with Snap-in Plastic Peg PCB Lock, Tin, Glow Wire Capable, Black, 43045-1200 |  | Molex (https://octopart-clicks.com/click/altium?sku=9732977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) | 43045-1200 (https://octopart-clicks.com/click/altium?sku=9732977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) | Farnell | 9732977 (https://octopart-clicks.com/click/altium?sku=9732977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) |  | 1 | 2
 | X1901 | 1 | molex_microfit_3_05x2_THT | Micro-Fit 3.0 Right Angle Header, 3.00mm Pitch, Dual Row, 10 Circuits, with Snap-in Plastic Peg PCB Lock, Tin, Glow Wire Capable, Black, 43045-1000 |  | Molex (https://octopart-clicks.com/click/altium?sku=1012255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) | 43045-1000 (https://octopart-clicks.com/click/altium?sku=1012255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) | Farnell | 1012255 (https://octopart-clicks.com/click/altium?sku=1012255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) |  | 1 | 1

Sheet: DATA
extension.PrjPcb
26.10.2018 08:24:22
default
