ArakniD/foxbms/hardware/hw-interface-ltc6820/v1.9.3/Assembly default/bom/bom-interface(default).xlsx

Sheet: BOM
BOM for interface, Variant default
Generated on 08.08.2018 08:54:17
Line # | Designator | Quantity | Name | Description | Case EIA | Manufacturer 1 | Manufacturer Part Number 1 | Supplier 1 | Supplier Part Number 1
1 | JP203_1, JP203_2, JP204_1, JP204_2, JP205_1, JP205_2, JP206_1, JP206_2, R203_1, R203_2 | 10 | 0R | SMD Resistor 0R 0603 | 0603 | Vishay Semiconductors (https://octopart-clicks.com/click/altium?sku=2616580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) | RCA06030000ZSEA (https://octopart-clicks.com/click/altium?sku=2616580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) | Farnell | 2616580 (https://octopart-clicks.com/click/altium?sku=2616580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)
2 | R400_1, R400_2, R401_1, R401_2 | 4 | 120R | SMD Resistor 120R 0603 | 0603 | Vishay (https://octopart-clicks.com/click/altium?sku=1652832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) | CRCW0603120RFKEA (https://octopart-clicks.com/click/altium?sku=1652832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) | Farnell | 1652832 (https://octopart-clicks.com/click/altium?sku=1652832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)
3 | R250_1, R250_2, R250_3, R250_4 | 4 | 806R | SMD Resistor 806R 0603 | 0603 | Panasonic (https://octopart-clicks.com/click/altium?sku=2059324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) | ERJ-3EKF8060V (https://octopart-clicks.com/click/altium?sku=2059324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) | Farnell | 2059324 (https://octopart-clicks.com/click/altium?sku=2059324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)
4 | R251_1, R251_2, R251_3, R251_4 | 4 | 1k2 | SMD Resistor 1k2 0603 | 0603 | Multicomp (https://octopart-clicks.com/click/altium?sku=2073370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) | MCMR06X1201FTL (https://octopart-clicks.com/click/altium?sku=2073370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) | Farnell | 2073370 (https://octopart-clicks.com/click/altium?sku=2073370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)
5 | R200_1, R200_2, R201_1, R201_2 | 4 | 2k | SMD Resistor 2k 0603 | 0603 | Panasonic (https://octopart-clicks.com/click/altium?sku=2059343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) | ERJ-3EKF2001V (https://octopart-clicks.com/click/altium?sku=2059343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) | Farnell | 2059343 (https://octopart-clicks.com/click/altium?sku=2059343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)
6 | R202_1, R202_2 | 2 | 20k | SMD Resistor 20k 0603 | 0603 | Panasonic (https://octopart-clicks.com/click/altium?sku=2059432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) | ERJ-3EKF2002V (https://octopart-clicks.com/click/altium?sku=2059432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) | Farnell | 2059432 (https://octopart-clicks.com/click/altium?sku=2059432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)
7 | C400_1, C400_2, C401_1, C401_2 | 4 | 27p/50V | MLCC | 0603 | KEMET (https://octopart-clicks.com/click/altium?sku=2219430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) | C0603X270J5GACAUTO (https://octopart-clicks.com/click/altium?sku=2219430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) | Farnell | 2219430 (https://octopart-clicks.com/click/altium?sku=2219430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)
8 | C200_1, C200_2, C250_1, C250_2, C250_3, C250_4, C251_1, C251_2, C251_3, C251_4 | 10 | 100n/50V | MLCC | 0603 | Murata (https://octopart-clicks.com/click/altium?sku=2525267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) | GCM188L81H104KA57D (https://octopart-clicks.com/click/altium?sku=2525267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) | Farnell | 2525267 (https://octopart-clicks.com/click/altium?sku=2525267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)
9 | IC250_1, IC250_2, IC250_3, IC250_4 | 4 | LTC6820HMS#PBF | IsoSPI Isolated Communication Interface, 2.7 to 5.5 V, -40 to 125 degC, 16-Pin MSOP (MS), Pb-Free |  | Analog Devices / Linear Technology | LTC6820HMS#PBF
10 | U200_1, U200_2 | 2 | SN74LVC00APWR | Quadruple 2-Input Positive-NAND Gate, PW0014A, LARGE T&R |  | Texas Instruments (https://octopart-clicks.com/click/altium?sku=1105931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) | SN74LVC00APWR (https://octopart-clicks.com/click/altium?sku=1105931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) | Farnell | 1105931 (https://octopart-clicks.com/click/altium?sku=1105931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)
11 | TR400_1, TR400_2 | 2 | HM2102NL | Pulse HM2102NL BMS Transformer |  | Pulse Electronics (https://octopart-clicks.com/click/altium?sku=1840-1034-1-ND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) | HM2102NLT (https://octopart-clicks.com/click/altium?sku=1840-1034-1-ND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) | Digi-Key | 1840-1034-1-ND (https://octopart-clicks.com/click/altium?sku=1840-1034-1-ND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)
12 | J500, J501 | 2 | SSW-104-01-G-D | SQ Post Socket, Through-hole, Vertical, -55 to 125 degC, 2.54mm Pitch, 8-Pin, Female, RoHS |  | Samtec (https://octopart-clicks.com/click/altium?sku=1668340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) | SSW-104-01-G-D (https://octopart-clicks.com/click/altium?sku=1668340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) | Farnell | 1668340 (https://octopart-clicks.com/click/altium?sku=1668340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)
13 | J300_1, J300_2 | 2 | SSW-108-01-G-D | SQ Post Socket, Through-hole, Vertical, -55 to 125 degC, 2.54mm Pitch, 16-Pin, Female, RoHS |  | Samtec (https://octopart-clicks.com/click/altium?sku=SAM1208-08-ND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) | SSW-108-01-G-D (https://octopart-clicks.com/click/altium?sku=SAM1208-08-ND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) | Digi-Key | SAM1208-08-ND (https://octopart-clicks.com/click/altium?sku=SAM1208-08-ND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)

Sheet: DATA
interface.PrjPcb
08.08.2018 08:54:17
default
