ArakniD/foxbms/hardware/hw-slave-18-ltc6813-1/v1.1.5/Assembly default/bom/bom-slave-18-ltc6813-1(default).xlsx

Sheet: BOM
BOM for slave-18-ltc6813-1, Variant default
Generated on 14.12.2018 14:27:44
Line # | Designator | Quantity | Name | Description | Case EIA | Manufacturer 1 | Manufacturer Part Number 1 | Supplier 1 | Supplier Part Number 1 | Automotive Qualified
1 | R610_1, R610_2, R1407_1, R1407_2, R1409_1, R1409_2, R1411_1, R1411_2, R1413_1, R1413_2, R1415_1, R1415_2, R1417_1, R1417_2 | 14 | 0R | SMD Resistor 0R 0603 | 0603 | Vishay Semiconductors (https://octopart-clicks.com/click/altium?sku=2616580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) | RCA06030000ZSEA (https://octopart-clicks.com/click/altium?sku=2616580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) | Farnell | 2616580 (https://octopart-clicks.com/click/altium?sku=2616580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) | True
2 | R108_1, R108_2, R109_1, R109_2, R112_1, R112_2, R113_1, R113_2, R114_1, R114_2, R115_1, R115_2, R116_1, R116_2, R117_1, R117_2, R118_1, R118_2, R119_1, R119_2, R1300_1, R1300_2, R1301_1, R1301_2, R1302_1, R1302_2, R1303_1, R1303_2, R1304_1, R1304_2, R1305_1, R1305_2, R1306_1, R1306_2, R1307_1, R1307_2, R1308_1, R1308_2, R1309_1, R1309_2, R1310_1, R1310_2, R1311_1, R1311_2, R1312_1, R1312_2, R1313_1, R1313_2, R1314_1, R1314_2, R1315_1, R1315_2, R1316_1, R1316_2, R1317_1, R1317_2, R1318_1, R1318_2 | 58 | 100R | SMD Resistor 100R 0603 | 0603 | Panasonic (https://octopart-clicks.com/click/altium?sku=P100HCT-ND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) | ERJ-3EKF1000V (https://octopart-clicks.com/click/altium?sku=P100HCT-ND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) | Digi-Key | P100HCT-ND (https://octopart-clicks.com/click/altium?sku=P100HCT-ND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) | True
3 | R1405_1, R1405_2, R1418_1, R1418_2 | 4 | 120R | SMD Resistor 120R 0603 | 0603 | Vishay (https://octopart-clicks.com/click/altium?sku=1652832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) | CRCW0603120RFKEA (https://octopart-clicks.com/click/altium?sku=1652832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) | Farnell | 1652832 (https://octopart-clicks.com/click/altium?sku=1652832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) | True
4 | R1100, R1101, R1102, R1103, R1104, R1105, R1106, R1107, R1108, R1109, R1110, R1111, R1112, R1113, R1114, R1115, R1116, R1117 | 18 | 150R | SMD Resistor 150R 0603 | 0603 | Panasonic (https://octopart-clicks.com/click/altium?sku=2303076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) | ERJ-3EKF1500V (https://octopart-clicks.com/click/altium?sku=2303076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) | Farnell | 2303076 (https://octopart-clicks.com/click/altium?sku=2303076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) | True
5 | R1403_1, R1403_2 | 2 | 270R | SMD Resistor 270R 0603 | 0603 | Vishay (https://octopart-clicks.com/click/altium?sku=2141320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) | CRCW0603270RFKEA (https://octopart-clicks.com/click/altium?sku=2141320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) | Farnell | 2141320 (https://octopart-clicks.com/click/altium?sku=2141320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) | True
6 | R1402_1, R1402_2 | 2 | 820R | SMD Resistor 820R 0603 | 0603 | Vishay (https://octopart-clicks.com/click/altium?sku=1469841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) | CRCW0603820RFKEA (https://octopart-clicks.com/click/altium?sku=1469841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) | Farnell | 1469841 (https://octopart-clicks.com/click/altium?sku=1469841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) | True
7 | R603_1, R603_2 | 2 | 1k | SMD Resistor 1k 0603 | 0603 | Vishay Dale (https://octopart-clicks.com/click/altium?sku=1652848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) | CRCW06031K00FKTA (https://octopart-clicks.com/click/altium?sku=1652848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) | Farnell | 1652848 (https://octopart-clicks.com/click/altium?sku=1652848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) | True
8 | R1400_1, R1400_2, R1419_1, R1419_2, R1420_1, R1420_2 | 6 | 1k2 | SMD Resistor 1k2 0603 | 0603 | Multicomp (https://octopart-clicks.com/click/altium?sku=2073370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) | MCMR06X1201FTL (https://octopart-clicks.com/click/altium?sku=2073370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) | Farnell | 2073370 (https://octopart-clicks.com/click/altium?sku=2073370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) | True
9 | R602_1, R602_2 | 2 | 1k5 | SMD Resistor 1k5 0603 | 0603 | Vishay Dale (https://octopart-clicks.com/click/altium?sku=2616745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) | CRCW06031K50JNEA (https://octopart-clicks.com/click/altium?sku=2616745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) | Farnell | 2616745 (https://octopart-clicks.com/click/altium?sku=2616745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) | True
10 | R600_1, R600_2, R606_1, R606_2 | 4 | 124k | SMD Resistor 124k 0603 | 0603 | Vishay (https://octopart-clicks.com/click/altium?sku=2138508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) | CRCW0603124KFKEA (https://octopart-clicks.com/click/altium?sku=2138508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) | Farnell | 2138508 (https://octopart-clicks.com/click/altium?sku=2138508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) | True
11 | R1512, R1513, R1514, R1515, R1516, R1517, R1530, R1531, R1532, R1533, R1534, R1535, R1548, R1549, R1550, R1551, R1552, R1553 | 18 | 3k3 | SMD Resistor 3k3 0603 | 0603 | Panasonic (https://octopart-clicks.com/click/altium?sku=2303173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) | ERJ-3EKF3301V (https://octopart-clicks.com/click/altium?sku=2303173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) | Farnell | 2303173 (https://octopart-clicks.com/click/altium?sku=2303173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) | True
12 | R100_1, R100_2, R101_1, R101_2, R102_1, R102_2, R103_1, R103_2, R104_1, R104_2, R105_1, R105_2, R106_1, R106_2, R107_1, R107_2, R601_1, R601_2, R605_1, R605_2, R607_1, R607_2, R700_1, R700_2, R701_1, R701_2, R702_1, R702_2, R703_1, R703_2, R704_1, R704_2, R705_1, R705_2, R706_1, R706_2, R707_1, R707_2, R708_1, R708_2, R800_1, R800_2, R905, R1118, R1421_1, R1421_2, R1422_1, R1422_2, R1423_1, R1423_2, R1424_1, R1424_2 | 52 | 10k | SMD Resistor 10k 0603 | 0603 | Multicomp (https://octopart-clicks.com/click/altium?sku=2073349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) | MCMR06X1002FTL (https://octopart-clicks.com/click/altium?sku=2073349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) | Farnell | 2073349 (https://octopart-clicks.com/click/altium?sku=2073349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) | True
13 | R901 | 1 | 86k6 | SMD Resistor 86k6 0603 | 0603 | Panasonic (https://octopart-clicks.com/click/altium?sku=2059490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) | ERJ-3EKF8662V (https://octopart-clicks.com/click/altium?sku=2059490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) | Farnell | 2059490 (https://octopart-clicks.com/click/altium?sku=2059490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) | True
14 | R608_1, R608_2 | 2 | 68k | SMD Resistor 68k 0603 | 0603 |  |  |  |  | False
15 | R904 | 1 | 220k | SMD Resistor 220k 0603 | 0603 |  |  |  |  | False
16 | R900 | 1 | 390k | SMD Resistor 390k 0603 | 0603 | Panasonic (https://octopart-clicks.com/click/altium?sku=2303278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) | ERJ-3EKF3903V (https://octopart-clicks.com/click/altium?sku=2303278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) | Farnell | 2303278 (https://octopart-clicks.com/click/altium?sku=2303278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) | True
17 | R1404_1, R1404_2 | 2 | 1M | SMD Resistor 1M 0603 | 0603 | Vishay (https://octopart-clicks.com/click/altium?sku=1469746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) | CRCW06031M00FKEA (https://octopart-clicks.com/click/altium?sku=1469746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) | Farnell | 1469746 (https://octopart-clicks.com/click/altium?sku=1469746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) | True
18 | R604_1, R604_2 | 2 | 1R | SMD Resistor 1R 0805 | 0805 | Vishay Dale (https://octopart-clicks.com/click/altium?sku=2616757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) | CRCW08051R00FKEA (https://octopart-clicks.com/click/altium?sku=2616757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) | Farnell | 2616757 (https://octopart-clicks.com/click/altium?sku=2616757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) | True
19 | R903 | 1 | 39R | SMD Resistor 39R 0805 | 0805 | Panasonic (https://octopart-clicks.com/click/altium?sku=1750736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) | ERJ-P06F39R0V (https://octopart-clicks.com/click/altium?sku=1750736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) | Farnell | 1750736 (https://octopart-clicks.com/click/altium?sku=1750736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) | True
20 | R1401_1, R1401_2 | 2 | 100R | SMD Resistor 100R 0805 | 0805 | Vishay Dale (https://octopart-clicks.com/click/altium?sku=1469862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) | CRCW0805100RFKEA (https://octopart-clicks.com/click/altium?sku=1469862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) | Farnell | 1469862 (https://octopart-clicks.com/click/altium?sku=1469862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) | True
21 | R1500, R1501, R1502, R1503, R1504, R1505, R1506, R1507, R1508, R1509, R1510, R1511, R1518, R1519, R1520, R1521, R1522, R1523, R1524, R1525, R1526, R1527, R1528, R1529, R1536, R1537, R1538, R1539, R1540, R1541, R1542, R1543, R1544, R1545, R1546, R1547 | 36 | 130R | SMD Resistor 130R 2010 | 2010 | Vishay Dale (https://octopart-clicks.com/click/altium?sku=1892735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) | CRCW2010130RJNEF (https://octopart-clicks.com/click/altium?sku=1892735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) | Farnell | 1892735 (https://octopart-clicks.com/click/altium?sku=1892735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) | True
22 | C1404_1, C1404_2, C1405_1, C1405_2 | 4 | 100p/50V | MLCC | 0603 | KEMET (https://octopart-clicks.com/click/altium?sku=2478236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) | C0603C101K5GACAUTO (https://octopart-clicks.com/click/altium?sku=2478236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) | Farnell | 2478236 (https://octopart-clicks.com/click/altium?sku=2478236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) | True
23 | C106_1, C106_2, C107_1, C107_2, C108_1, C108_2, C109_1, C109_2, C110_1, C110_2, C111_1, C111_2, C112_1, C112_2, C113_1, C113_2, C114_1, C114_2, C115_1, C115_2, C608_1, C608_2, C1300_1, C1300_2, C1301_1, C1301_2, C1302_1, C1302_2, C1303_1, C1303_2, C1304_1, C1304_2, C1305_1, C1305_2, C1312_1, C1312_2, C1313_1, C1313_2, C1314_1, C1314_2, C1315_1, C1315_2, C1316_1, C1316_2, C1317_1, C1317_2, C1324_1, C1324_2, C1325_1, C1325_2, C1326_1, C1326_2, C1327_1, C1327_2, C1328_1, C1328_2, C1329_1, C1329_2 | 58 | 10n/100V | MLCC | 0603 | KEMET (https://octopart-clicks.com/click/altium?sku=1301715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) | C0603X103K1RACAUTO (https://octopart-clicks.com/click/altium?sku=1301715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) | Farnell | 1301715 (https://octopart-clicks.com/click/altium?sku=1301715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) | True
24 | C100_1, C100_2, C400, C401, C402, C403, C404, C405, C406, C407, C602_1, C602_2, C604_1, C604_2, C607_1, C607_2, C700_1, C700_2, C701_1, C701_2, C800_1, C800_2, C801_1, C801_2, C903, C1100 | 26 | 100n/50V | MLCC | 0603 | Murata (https://octopart-clicks.com/click/altium?sku=490-6049-1-ND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) | GCM188L81H104KA57D (https://octopart-clicks.com/click/altium?sku=490-6049-1-ND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) | Digi-Key | 490-6049-1-ND (https://octopart-clicks.com/click/altium?sku=490-6049-1-ND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) | True
25 | C905 | 1 | 470p/100V | MLCC | 0805 | KEMET (https://octopart-clicks.com/click/altium?sku=2070482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) | C0805C471K1RACAUTO (https://octopart-clicks.com/click/altium?sku=2070482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) | Farnell | 2070482 (https://octopart-clicks.com/click/altium?sku=2070482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) | True
27 | C101_1, C101_2, C102_1, C102_2, C103_1, C103_2, C104_1, C104_2, C105_1, C105_2, C603_1, C603_2, C900, C904, C1401_1, C1401_2, C1402_1, C1402_2, C1403_1, C1403_2 | 20 | 1u/50V | MLCC | 0805 | Murata (https://octopart-clicks.com/click/altium?sku=2672199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) | GRT21BR71H105KE01L (https://octopart-clicks.com/click/altium?sku=2672199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) | Farnell | 2672199 (https://octopart-clicks.com/click/altium?sku=2672199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) | True
28 | C605_1, C605_2, C606_1, C606_2 | 4 | 2u2/10V | MLCC | 0805 | KEMET (https://octopart-clicks.com/click/altium?sku=2478259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) | C0805C225K8RACAUTO (https://octopart-clicks.com/click/altium?sku=2478259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) | Farnell | 2478259 (https://octopart-clicks.com/click/altium?sku=2478259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) | True
29 | C601_1, C601_2, C1400_1, C1400_2 | 4 | 100n/200V | MLCC | 1206 | KEMET (https://octopart-clicks.com/click/altium?sku=2673161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) | C1206J104K2RACAUTO (https://octopart-clicks.com/click/altium?sku=2673161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) | Farnell | 2673161 (https://octopart-clicks.com/click/altium?sku=2673161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) | True
30 | C907, C908 | 2 | 2u2/250V | MLCC | 2220 | TDK (https://octopart-clicks.com/click/altium?sku=445-7997-2-ND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) | CGA9P3X7T2E225M250KE (https://octopart-clicks.com/click/altium?sku=445-7997-2-ND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) | Digi-Key | 445-7997-2-ND (https://octopart-clicks.com/click/altium?sku=445-7997-2-ND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) | True
32 | C906 | 1 | 4n7/1000V | MLCC | 1812 | KEMET (https://octopart-clicks.com/click/altium?sku=2834565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) | C1812C472KDRACAUTO (https://octopart-clicks.com/click/altium?sku=2834565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) | Farnell | 2834565 (https://octopart-clicks.com/click/altium?sku=2834565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) | True
33 | C600_1, C600_2 | 2 | 1u/250V | MLCC | 1812 | TDK (https://octopart-clicks.com/click/altium?sku=2435499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) | CGA8P3X7T2E105K250KA (https://octopart-clicks.com/click/altium?sku=2435499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) | Farnell | 2435499 (https://octopart-clicks.com/click/altium?sku=2435499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) | True
34 | C902 | 1 | 22u/50V | MLCC | 2220 | KEMET (https://octopart-clicks.com/click/altium?sku=399-5797-1-ND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) | C2220C226M5R2CAUTO7186 (https://octopart-clicks.com/click/altium?sku=399-5797-1-ND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) | Digi-Key | 399-5797-1-ND (https://octopart-clicks.com/click/altium?sku=399-5797-1-ND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) | True
35 | D1100 | 1 | BAT54C,215 | Schottky Barrier Diode, 30 V, 3-Pin SOT23, RoHS, Tape and Reel |  | Nexperia (https://octopart-clicks.com/click/altium?sku=1727-2902-1-ND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) | BAT54C,215 (https://octopart-clicks.com/click/altium?sku=1727-2902-1-ND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) | Digi-Key | 1727-2902-1-ND (https://octopart-clicks.com/click/altium?sku=1727-2902-1-ND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)
36 | D1401_1, D1401_2 | 2 | SMAJ85A-E3/61 | Transient Voltage Suppressor, 6.40 to 231 V, 85 V Stand-off Voltage, Uni-Directional, -55 to 155 degC, 2-pin DO-214AC, Pb-Free, Tape and Reel |  | Vishay Semiconductors (https://octopart-clicks.com/click/altium?manufacturer=Vishay%20Semiconductors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) | SMAJ85A-E3/61 (https://octopart-clicks.com/click/altium?manufacturer=Vishay%20Semiconductors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) | Digi-Key | SMAJ85A-E3/61GIDKR-ND (https://octopart-clicks.com/click/altium?manufacturer=Vishay%20Semiconductors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)
37 | D901 | 1 | PDS3200 | Schottky Diode 3A 200V 780mV |  | Diodes (https://octopart-clicks.com/click/altium?sku=1713904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) | PDS3200-13 (https://octopart-clicks.com/click/altium?sku=1713904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) | Farnell | 1713904 (https://octopart-clicks.com/click/altium?sku=1713904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) | True
38 | D900, D1400_1, D1400_2 | 3 | DFLS1100-7 | 1 A High Voltage Schottky Barrier Rectifier, 0.62 V, -55 to 175 degC, 2- Pin POWERDI123, Pb-Free, Tape and Reel |  | Diodes (https://octopart-clicks.com/click/altium?sku=DFLS1100DICT-ND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) | DFLS1100-7 (https://octopart-clicks.com/click/altium?sku=DFLS1100DICT-ND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) | Digi-Key | DFLS1100DICT-ND (https://octopart-clicks.com/click/altium?sku=DFLS1100DICT-ND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)
39 | Z1300_1, Z1300_2, Z1301_1, Z1301_2, Z1302_1, Z1302_2, Z1303_1, Z1303_2, Z1304_1, Z1304_2, Z1305_1, Z1305_2, Z1306_1, Z1306_2, Z1307_1, Z1307_2, Z1308_1, Z1308_2, Z1309_1, Z1309_2, Z1310_1, Z1310_2, Z1311_1, Z1311_2, Z1312_1, Z1312_2, Z1313_1, Z1313_2, Z1314_1, Z1314_2, Z1315_1, Z1315_2, Z1316_1, Z1316_2, Z1317_1, Z1317_2 | 36 | MMSZ4692T1G | Zener Voltage Regulator, 500 mW, 2-Pin SOD-123, Pb-Free, Tape and Reel |  | ON Semiconductor (https://octopart-clicks.com/click/altium?sku=MMSZ4692T1GOSCT-ND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) | MMSZ4692T1G (https://octopart-clicks.com/click/altium?sku=MMSZ4692T1GOSCT-ND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) | Digi-Key | MMSZ4692T1GOSCT-ND (https://octopart-clicks.com/click/altium?sku=MMSZ4692T1GOSCT-ND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)
40 | LD1400_1, LD1400_2 | 2 | green | TLMG1100-GS08 |  | Vishay Semiconductors (https://octopart-clicks.com/click/altium?manufacturer=Vishay%20Semiconductors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) | TLMG1100-GS08 (https://octopart-clicks.com/click/altium?manufacturer=Vishay%20Semiconductors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) | Digi-Key | 751-1165-1-ND (https://octopart-clicks.com/click/altium?manufacturer=Vishay%20Semiconductors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) | True
41 | F300, F320 | 2 | fuse_0.5A_0448.500MR | Fuse, Surface Mount, NANO2 Series, 500 mA, 125 VAC, 32 VDC, Very Fast Acting, SMD |  | Littelfuse (https://octopart-clicks.com/click/altium?sku=1596919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) | 0448.500MR (https://octopart-clicks.com/click/altium?sku=1596919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) | Farnell | 1596919 (https://octopart-clicks.com/click/altium?sku=1596919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) | False
42 | F301, F302, F303, F304, F305, F306, F307, F308, F309, F310, F311, F312, F313, F314, F315, F316, F317, F318, F319 | 19 | fuse_0.25A_0466.250NR | Fuse, Surface Mount, 466 Series, 250 mA, 125 VAC, 125 VDC, Very Fast Acting, 1206 |  | Littelfuse (https://octopart-clicks.com/click/altium?sku=9921826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) | 0466.250NR (https://octopart-clicks.com/click/altium?sku=9921826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) | Farnell | 9921826 (https://octopart-clicks.com/click/altium?sku=9921826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) | False
43 | F900 | 1 | fuse_1.25A_04661.25NR | Fuse, Surface Mount, 466 Series, 1.25 A, 63 VAC, 63 VDC, Very Fast Acting, 1206 |  | Littelfuse (https://octopart-clicks.com/click/altium?sku=1596526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) | 0466.125NR (https://octopart-clicks.com/click/altium?sku=1596526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) | Farnell | 1596526 (https://octopart-clicks.com/click/altium?sku=1596526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) | False
44 | L900 | 1 | 74404042100 | WE-LQS SMD Power Inductor, L=10 µH |  | Wurth Electronics (https://octopart-clicks.com/click/altium?sku=732-5508-6-ND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) | 74404042100 (https://octopart-clicks.com/click/altium?sku=732-5508-6-ND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) | Digi-Key | 732-5508-6-ND (https://octopart-clicks.com/click/altium?sku=732-5508-6-ND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)
45 | L600_1, L600_2 | 2 | 220µH | Power Inductor |  | Laird Steward (https://octopart-clicks.com/click/altium?sku=240-2742-1-ND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) | TYS6045221M-10 (https://octopart-clicks.com/click/altium?sku=240-2742-1-ND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) | Digi-Key | 240-2742-1-ND (https://octopart-clicks.com/click/altium?sku=240-2742-1-ND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) | True
46 | T1500, T1501, T1502, T1503, T1504, T1505, T1506, T1507, T1508, T1509, T1510, T1511, T1512, T1513, T1514, T1515, T1516, T1517 | 18 | NX2301P,215 | P-Channel Trench MOSFET, -20 V, -2 A, -55 to 150 degC, 3-Pin SOT23, Tape and Reel |  | NXP Semiconductors | NX2301P,215 |  |  | Y
47 | IC801_1, IC801_2 | 2 | M24M02-DWMN3TP/K | Automotive 2-Mbit serial I²C bus EEPROM with 1 MHz clock |  | STMicroelectronics (https://octopart-clicks.com/click/altium?manufacturer=STMicroelectronics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) | M24M02-DWMN3TP/K (https://octopart-clicks.com/click/altium?manufacturer=STMicroelectronics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) | Digi-Key | 497-16238-1-ND (https://octopart-clicks.com/click/altium?manufacturer=STMicroelectronics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) | True
47.1 | Q600_1, Q600_2 | 2 | PBSS4112PANP | Dual NPN/PNP Transistor |  |  |  |  |  | True
48 | IC100_1, IC100_2, IC101_1, IC101_2, IC104_1, IC104_2 | 6 | ADG728BRUZ | CMOS, Low Voltage, 2-Wire Serially Controlled, Matrix Switch, -40 to 85 degC, 16-pin SOP (RU-16), Tube |  | Analog Devices (https://octopart-clicks.com/click/altium?sku=ADG728BRUZ-ND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) | ADG728BRUZ (https://octopart-clicks.com/click/altium?sku=ADG728BRUZ-ND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) | Digi-Key | ADG728BRUZ-ND (https://octopart-clicks.com/click/altium?sku=ADG728BRUZ-ND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)
49 | U700_1, U700_2 | 2 | TCA6408APWR | Low-Voltage 8-Bit I2C and SMBus I/O Expander, 1.65 to 5.5 V, -40 to 85 degC, 16-pin TSSOP (PW), Green (RoHS & no Sb/Br) |  | Texas Instruments (https://octopart-clicks.com/click/altium?sku=296-24327-1-ND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) | TCA6408APWR (https://octopart-clicks.com/click/altium?sku=296-24327-1-ND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) | Digi-Key | 296-24327-1-ND (https://octopart-clicks.com/click/altium?sku=296-24327-1-ND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)
50 | IC900 | 1 | LT8302HS8E#PBF | Micropower No-Opto Isolated Flyback Converter, 2.8 to 42 V, -40 to 150 degC, 8-Pin SOIC (S8E), RoHS, Tube |  | Analog Devices / Linear Technology (https://octopart-clicks.com/click/altium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) | LT8302HS8E#PBF (https://octopart-clicks.com/click/altium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) | Digi-Key | LT8302HS8E#PBF-ND (https://octopart-clicks.com/click/altium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)
51 | U100_1, U100_2, U101_1, U101_2 | 4 | AD8628ARTZ-R2 | Single Channel RRIO Operational Amplifier, 2.5 MHz BW, 1 V/us SR, Industrial, 5-pin SOT23 (RJ-5), Reel |  | Analog Devices (https://octopart-clicks.com/click/altium?sku=AD8628ARTZ-R2CT-ND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) | AD8628ARTZ-R2 (https://octopart-clicks.com/click/altium?sku=AD8628ARTZ-R2CT-ND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) | Digi-Key | AD8628ARTZ-R2CT-ND (https://octopart-clicks.com/click/altium?sku=AD8628ARTZ-R2CT-ND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) | Yes
52 | IC1400_1, IC1400_2 | 2 | LTC6813HLWE-1#3ZZPBF | 18 Cell Multicell Battery Monitor, -40 to 125 degC, Pb-Free |  | Analog Devices / Linear Technology (https://octopart-clicks.com/click/altium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) | LTC6813HLWE-1#3ZZPBF (https://octopart-clicks.com/click/altium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) | Digikey | LTC6813HLWE-1#3ZZPBF-ND (https://octopart-clicks.com/click/altium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) | True
53 | U1100, U1101, U1102, U1103, U1104, U1105, U1106, U1107, U1108, U1109, U1110, U1111, U1112, U1113, U1114, U1115, U1116, U1117 | 18 | ACPL-217 | Optocoupler, Transistor Output, 1 Channel |  | Broadcom Avago (https://octopart-clicks.com/click/altium?sku=1602623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) | ACPL-217-56BE (https://octopart-clicks.com/click/altium?sku=1602623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) | Farnell | 1602623 (https://octopart-clicks.com/click/altium?sku=1602623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) | False
54 | IC800_1, IC800_2 | 2 | MCP9800A0T-M/OT | 2-Wire High-Accuracy Temperature Sensor, Slave Address 000, 5-Pin SOT-23, -55°C to +125°C Temperature, Tape and Reel |  | Microchip (https://octopart-clicks.com/click/altium?manufacturer=Microchip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) | MCP9800A0T-M/OT (https://octopart-clicks.com/click/altium?manufacturer=Microchip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) | Digi-Key | MCP9800A0T-M/OTDKR-ND (https://octopart-clicks.com/click/altium?manufacturer=Microchip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)
55 | U600_1, U600_2 | 2 | LM5161QPWPRQ1 | Automotive DC/DC buck converter |  | Texas Instruments (https://octopart-clicks.com/click/altium?sku=296-47791-1-ND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) | LM5161QPWPRQ1 (https://octopart-clicks.com/click/altium?sku=296-47791-1-ND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) | Digi-Key | 296-47791-1-ND (https://octopart-clicks.com/click/altium?sku=296-47791-1-ND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) | True
56 | TR1400_1, TR1400_2 | 2 | HM2102NL | Pulse HM2102NL BMS Transformer |  | Pulse Electronics (https://octopart-clicks.com/click/altium?sku=1840-1034-1-ND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) | HM2102NLT (https://octopart-clicks.com/click/altium?sku=1840-1034-1-ND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) | Digi-Key | 1840-1034-1-ND (https://octopart-clicks.com/click/altium?sku=1840-1034-1-ND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) | True
57 | TR900 | 1 | WE_750313457 | MID-FLYLT Flyback Transformers for Linear Technology |  | Wurth Electronics (https://octopart-clicks.com/click/altium?sku=1297-1136-1-ND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) | 750313457 (https://octopart-clicks.com/click/altium?sku=1297-1136-1-ND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) | Digi-Key | 1297-1136-1-ND (https://octopart-clicks.com/click/altium?sku=1297-1136-1-ND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) | False
60 | X405 | 1 | gen_pinheader_2.54_2x4 | Standard Pinheader, THD, gerade, 2.54mm, 2-reihig |  | Samtec (https://octopart-clicks.com/click/altium?sku=2856692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) | TSW-104-07-G-D (https://octopart-clicks.com/click/altium?sku=2856692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) | Farnell | 2856692 (https://octopart-clicks.com/click/altium?sku=2856692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) | False
61 | X402, X403 | 2 | gen_pinheader_2.54_2x5 | Standard Pinheader, THD, gerade, 2.54mm, 2-reihig |  | Samtec (https://octopart-clicks.com/click/altium?sku=2578720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) | TSW-105-07-G-D (https://octopart-clicks.com/click/altium?sku=2578720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) | Farnell | 2578720 (https://octopart-clicks.com/click/altium?sku=2578720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) | False
62 | X400, X401 | 2 | gen_pinheader_2.54_2x9 | Standard Pinheader, THD, gerade, 2.54mm, 2-reihig |  | Samtec (https://octopart-clicks.com/click/altium?sku=2025256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) | TSW-109-07-G-D (https://octopart-clicks.com/click/altium?sku=2025256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) | Farnell | 2025256 (https://octopart-clicks.com/click/altium?sku=2025256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) | False
63 | X404 | 1 | gen_pinheader_2.54_2x10 | Standard Pinheader, THD, gerade, 2.54mm, 2-reihig |  | Samtec (https://octopart-clicks.com/click/altium?sku=2779676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) | TSW-110-07-G-D (https://octopart-clicks.com/click/altium?sku=2779676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) | Farnell | 2779676 (https://octopart-clicks.com/click/altium?sku=2779676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) | False
64 | X500, X501, X502, X503, X1001, X1002 | 6 | molex_microfit_3_01x2_THT | Micro-Fit 3.0 Right Angle Header, 3.00mm Pitch, Dual Row, 2 Circuits, with Snap-in Plastic Peg PCB Lock, Tin, Glow Wire Capable, Black, 43045-0200 |  | Molex (https://octopart-clicks.com/click/altium?sku=1012251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) | 43045-0200 (https://octopart-clicks.com/click/altium?sku=1012251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) | Farnell | 1012251 (https://octopart-clicks.com/click/altium?sku=1012251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) | False
65 | X201, X202 | 2 | molex_microfit_3_08x2_THT | Micro-Fit 3.0 Right Angle Header, 3.00mm Pitch, Dual Row, 16 Circuits, with Snap-in Plastic Peg PCB Lock, Tin, Glow Wire Capable, Black, 43045-1600 |  | Molex (https://octopart-clicks.com/click/altium?sku=9961380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) | 0430451600 (https://octopart-clicks.com/click/altium?sku=9961380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) | Farnell | 9961380 (https://octopart-clicks.com/click/altium?sku=9961380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) | False
66 | X200 | 1 | molex_microfit_3_12x2_THT | Micro-Fit 3.0 Right Angle Header, 3.00mm Pitch, Dual Row, 24 Circuits, with Snap-in Plastic Peg PCB Lock, Tin, Glow Wire Capable, Black, 43045-2400 |  | Molex (https://octopart-clicks.com/click/altium?sku=1012245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) | 0430452400 (https://octopart-clicks.com/click/altium?sku=1012245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) | Farnell | 1012245 (https://octopart-clicks.com/click/altium?sku=1012245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) | False

Sheet: DATA
slave-18-ltc6813-1.PrjPcb
14.12.2018 14:27:44
default
