ArakniD/foxbms/hardware/hw-master/v1.0.6-2/Sources/Project Outputs for master-010106/BOM/Bill of Materials-master.xlsx

Line # | Name | Description | Designator | Case EIA | Quantity | TargetPrice | Manufacturer 1 | Manufacturer Part Number 1 | Manufacturer Lifecycle 1 | Supplier 1 | Supplier Part Number 1 | Supplier Unit Price 1 | Supplier Subtotal 1
 | 330m | Eaton 330mF, 5.5v, -20 to +80, Ultracapacitor, KW-5R5C334H-R | BT1 |  | 1 | 0 | Eaton | KW-5R5C334H-R |  | Avnet | KW-5R5C334H-R
 | 4.7µF 16V | Ceramic, 4.7µF, ±10%, 16V, X7R, –55 to 125°C, 0805 (2012),RoHS, Automotive | C1.1, C1.2, C39, C85 | 0805 | 4 | 0 | Murata | GCJ21BR71C475KA01L | Volume Production | Digi-Key | 490-10557-1-ND | 0.53314 | 2.13
 | 100nF 50V | Ceramic, 100nF, ±10%, 50V, X7R, –55 to 125°C, 0603 (1608),RoHS, Automotive | C2.1, C2.2, C5.1, C5.2, C10.1, C10.2, C12.1, C12.2, C28.1, C28.2, C28.3, C28.4, C31, C55, C56, C70, C71, C73, C76, C77, C78, C79, C80, C81, C82, C86, C107, C115, C128, C134, C142, C143, C149, C150, C151, C152, C159, C161.1, C161.2, C164, C165.1, C165.2, C166, C167, C177, C178, C179, C180 | 0603 | 48 | 0 | Murata | GCJ188R71H104KA12D | Volume Production | Digi-Key | 490-5798-1-ND | 0.3653 | 17.53
 | 10µF 10V | Ceramic, 10µF, ±10%, 10V, X7R, –55 to 125°C, 0805 (2012),RoHS, Automotive | C3.1, C3.2, C8.1, C8.2, C9.1, C9.2, C144, C146, C158.1, C158.2 | 0805 | 10 | 0 | Murata | GCJ21BR71A106KE01L | Volume Production | Digi-Key | 490-12646-1-ND | 0.65395 | 6.54
 | 47pF 50V | Ceramic, 47pF, ±5%, 50V, C0G, 25 to 125°C, 0402 (1005),RoHS, Automotive | C4.1, C4.2, C7.1, C7.2 | 0402 | 4 | 0 |  |  |  | Digi-Key | 490-10670-1-ND
 | 390pF 25V | Ceramic, 390pF, ±5%, 25V, C0G, 25 to 125°C, 0402 (1005),RoHS, Automotive | C6.1, C6.2 | 0402 | 2 | 0 | Murata | GCM1555C1H180JA16D | Volume Production | Digi-Key | 490-12650-1-ND | 0.14532 | 0.29065
 | 1.0µF 25V | Ceramic, 1.0µF, ±10%, 25V, X7R, –55 to 125°C, 0603 (1608),RoHS, Automotive | C11.1, C11.2, C67, C154 | 0603 | 4 | 0 | Murata | GCJ188R71E105KA01D |  | Digi-Key | 490-14409-1-ND | 0.4069 | 1.63
 | 10nF 50V | Ceramic, 10nF, ±10%, 50V, X7R, –55 to 125°C, 0603 (1608),RoHS, Automotive | C13.1, C13.2, C153, C157 | 0603 | 4 | 0 | Murata | GCJ188R71H102KA01D | Volume Production | Digi-Key | 490-5768-1-ND | 0.24142 | 0.96569
 | 2.2µF 25V | Ceramic, 2.2µF, ±10%, 25V, X7R, –55 to 125°C, 0805 (2012),RoHS, Automotive | C14, C17, C96, C141 | 0805 | 4 | 0 | Murata | GCM21BR71E225KA73L | Volume Production | Digi-Key | 490-4787-1-ND | 0.61361 | 2.45
 | 100nF 50V | Ceramic, 100nF, ±10%, 50V, X7R, –55 to 125°C, 0402 (1005),RoHS, Automotive | C15, C16, C29, C30, C33, C34, C35, C40, C87, C88, C89, C90, C97, C105, C108, C109, C116, C123, C125, C126, C127, C135, C136, C137, C138 | 0402 | 25 | 0 | Murata | GCM155R71H104KE02D | Volume Production | Digi-Key | 490-10672-1-ND | 0.06136 | 1.53
 | T598D107M010ATE025 | CAP, Aluminum Polymer, 220 µF, 6.3 V,+/- 20%, 0.01 ohm, 7343-31 SMD | C18.1, C18.2 |  | 2 | 0 | Murata | ECASD60J227M010K00 | Volume Production | Digi-Key | 490-12529-1-ND | 1.85 | 3.7
 | 27p/50V | MLCC | C19, C26, C36, C48 | 0603 | 4 | 0 | KEMET | C0603X270J5GACAUTO | Volume Production | Farnell | 2219430 | 0.2944 | 2.94
 | 100n/50V | MLCC | C20.1, C20.2, C20.3, C20.4, C23.1, C23.2, C84, C147, C148 | 0603 | 9 | 0 | KEMET | C0603C104K5RACAUTO | Volume Production | Farnell | 2070398 | 0.17065 | 1.71
 | GRM188R72A104KA35J | CAP, CERM, 0.1 uF, 100 V, +/- 10%, X7R, 0603 | C22.1, C22.2, C52.1, C52.2 |  | 4 | 0 | Murata | GRM188R72A104KA35J | Volume Production | Mouser | 81-GRM188R72A104KA5J | 0.28166 | 1.13
 | GRM1885C2A220JA01D | CAP, CERM, 22 pF, 100 V, +/- 5%, C0G/NP0, 0603 | C24.1, C24.2, C43.1, C43.2 |  | 4 | 0 | Murata | GRM1885C2A220JA01D | Volume Production | Digi-Key | 490-1335-1-ND | 0.11065 | 0.44261
 | GRM32EC80J107ME20L | CAP, CERM, 100 uF, 6.3 V, +/- 20%, X6S, 1210 | C25.1, C25.2 |  | 2 | 0 | Murata | GRM32EC80J107ME20L | Volume Production | Digi-Key | 490-6533-6-ND | 1.53 | 3.06
 | 1.0µF 25V | Ceramic, 1.0µF, ±10%, 25V, X7R, –55 to 125°C, 0603 (1608),RoHS, Automotive | C37, C44, C75, C83, C91, C92.1, C92.2, C93, C122, C124, C130, C145 | 0603 | 12 | 0 | Murata | GCJ188R71E105KA01D |  | Digi-Key | 490-14409-1-ND | 0.28193 | 3.38
 | 18pF 50V | Ceramic, 18pF, ±5%, 50V, X7R, 25 to 125°C, 0402 (1005),RoHS, Automotive | C38, C42, C99, C102, C112, C117 | 0402 | 6 | 0 | Murata | GCM1555C1H180JA16D | Volume Production | Digi-Key | 490-12650-1-ND | 0.14532 | 0.87194
 | CAP TANTALUM 33UF 50V 2917 | 33µF Molded Tantalum Polymer Capacitor 50V 2917 (7343 Metric) 75mOhm @ 100kHz | C47.1, C47.2 |  | 2 | 0 |  |  |  | Digi-Key | 399-11721-1-ND
 | GRM32DC72A475KE01L | CAP, CERM, 4.7 uF, 100 V, +/- 10%, X7S, 1210 | C49.1, C49.2, C50.1, C50.2 |  | 4 | 0 | Murata | GRM32DC72A475KE01L |  | Mouser | 81-GRM32DC72A475KE1L | 1.1 | 4.39
 | GCM188R71E473KA37D | CAP, CERM, 0.047 uF, 25 V, +/- 10%, X7R, AEC-Q200 Grade 1, 0603 | C53.1, C53.2 |  | 2 | 0 | Murata | GCM188R71E473KA37D | Volume Production | Digi-Key | 490-8018-1-ND | 0.25148 | 0.50296
 | 100nF 50V | Ceramic, 100nF, ±20%, 50V, X7R, –55 to 125°C, 0805 (2012),RoHS, Automotive | C54, C69 | 0805, 0603 | 2 | 0 | Murata | GCJ188R71H104KA12D | Volume Production | Digi-Key | 490-5798-1-ND | 0.52486 | 1.05
 | 1500pF 50V | Ceramic, 390pF, ±5%, 25V, C0G, 25 to 125°C, 0402 (1005),RoHS, Automotive | C57 | 0402 | 1 | 0 |  |  |  | Digi-Key
 | 10uF 50V | Ceramic, 10uF, 50 V, -55 to 125 degC, 2-Pin SMD (1210), RoHS, Tape and Reel | C58 | 1210 | 1 | 0 | Kyocera AVX | 12105C106KAT2A
 | 10nF 50V | Ceramic, 10nF, ±10%, 50V, X7R, –55 to 125°C, 0402 (1005),RoHS, Automotive | C59, C68 | 0402 | 2 | 0
 | 22uF 16V | Ceramic, 22uF, 16 V, -55 to 125 degC, 2-Pin SMD (1210), RoHS, Tape and Reel | C60, C61, C62 | 1210 | 3 | 0 | Kyocera AVX | 12105C106KAT2A
 | 1200pF 50V | Ceramic, 390pF, ±5%, 50V, C0G, 25 to 125°C, 0402 (1005),RoHS, Automotive | C63 | 0402 | 1 | 0 |  |  |  | Digi-Key
 | GRM31CR72A105KA01L | Chip Capacitor, 1 uF, +/- 10%, 100 V, -55 to 125 degC, 1206 (3216 Metric), RoHS, Tape and Reel | C64, C65, C72, C74 | 1206 | 4 | 0 | Murata | GRM31CR72A105KA01L | Volume Production | Digi-Key | 490-3909-1-ND | 0.77456 | 3.1
 | 10nF 50V | Ceramic, 10nF, ±10%, 50V, X7R, –55 to 125°C, 0402 (1005),RoHS, Automotive | C66 | 0402 | 1 | 0
 | 10µF 10V | Ceramic, 10µF, ±10%, 10V, X7R, –55 to 125°C, 0805 (2012),RoHS, Automotive | C120, C156 | 0805 | 2 | 0 | Murata | GCJ21BR71A106KE01L | Volume Production | Digi-Key | 490-12646-1-ND | 0.93006 | 1.86
 | 100nF 50V | Ceramic, 100nF, ±10%, 50V, X7R, –55 to 125°C, 0603 (1608),RoHS, Automotive | C155 | 0603 | 1 | 0 | Murata | GCJ188R71H104KA12D | Volume Production | Digi-Key | 490-5798-1-ND | 0.52486 | 0.52486
 | GRM1885C1H560JA01D | CAP, CERM, 56 pF, 50 V, +/- 5%, C0G/NP0, 0603 | C160.1, C160.2, C163.1, C163.2 |  | 4 | 0 | Murata | GRM1885C1H560JA01D | Volume Production | Digi-Key | 490-1421-1-ND | 0.11065 | 0.44261
 | GCM188R71H472KA37D | CAP, CERM, 4700 pF, 50 V, +/- 10%, X7R, AEC-Q200 Grade 1, 0603 | C162.1, C162.2 |  | 2 | 0 | Murata | GCM188R71H472KA37D | Volume Production | Digi-Key | 490-4932-1-ND | 0.17101 | 0.34201
 | 1u/50V | MLCC | C181 | 0603 | 1 | 0 | Taiyo Yuden | UMK107AB7105KA-T | Volume Production | Farnell | 2779055 | 0.3426 | 0.3426
 | MMSZ5232BS-7-F | Diode, Zener, 5.6 V, 200 mW, SOD-323 | D1.1, D1.2 |  | 2 | 0 | Diodes | MMSZ5232BS-7-F | Volume Production | Digi-Key | MMSZ5232BS-FDICT-ND | 0.2716 | 0.5432
 | 40V | Diode, Schottky, 40 V, 3 A, AEC-Q101, SMAF | D2.1, D2.2 |  | 2 | 0 | ON Semiconductor / Fairchild | FSV340AF | New Product | Digi-Key | FSV340AFCT-ND | 0.50296 | 1.01
 | DFLZ24-7 | Diode, Zener, 24 V, 1 W, PowerDI123 | D3.1, D3.2 |  | 2 | 0 | Diodes | DFLZ24-7 | Volume Production | Digi-Key | DFLZ24DICT-ND | 0.36213 | 0.72426
 | 75V | Diode, Ultrafast, 75 V, 0.25 A, SOD-323 | D4.1, D4.2 |  | 2 | 0
 | MM3Z12VT1G | Zener Diode | D5, D6 |  | 2 | 0 | ON Semiconductor | MM3Z12VT1G | Volume Production | Digi-Key | MM3Z12VT1GOSCT-ND | 0.15089 | 0.30178
 | BAT54SW-7-F | Schottky Barrier Diode, 30 V, 200 mA, -65 to 125 degC, 3-Pin SOT323, RoHS, Tape and Reel | D7 |  | 1 | 0
 | CDSOD323-T05 | TVS Diode, CDSOD323 Series, Unidirectional, 5 V, 18.3 V, SOD-323, 2 Pins | D8, D9, D10, D11 |  | 4 | 0 | Bourns | CDSOD323-T05S | Volume Production | Digi-Key | CDSOD323-T05SCT-ND | 0.63373 | 2.53
 | MBR0520L | Schottky Diode, 20V, 0.2A, 2-pin SOD-123, RoHS, Tape and Reel | D16, D17 |  | 2 | 0 | ON Semiconductor / Fairchild | MBR0520L | Volume Production | Farnell | 1467521 | 0.35172 | 1.76
 | BZX84C5V1ET1G | Zener Voltage Regulator, 225 mW, 3-Pin SOT-23, Pb-Free, Tape and Reel | D18 |  | 1 | 0 | ON Semiconductor | SZBZX84C5V1ET1G | Volume Production | Digi-Key | SZBZX84C5V1ET1GOSCT-ND | 0.21124 | 0.21124
 | NF | '''BAT41 Schottky diode, small signal''' - If(avg) = 200mA, Vf(max) = 1V@200mA - Vr(max) = 100V, Ir = 100nA@50V, 25deg - SOD-523 package, RoHS compliant | D19 |  | 1 | 0
 | ISO7741DWR | Imported | IC1.1, IC1.2 |  | 2 | 0 | Texas Instruments | ISO7741DWR |  | Digi-Key | 296-47781-1-ND | 3.3 | 6.6
 | FT231XQ-R | USB to Full-Handshake UART Interface Chip, UHCI/OHCI/EHCI Compatible, USB 2.0 Compatible, -40 to +85 degC, 20-Pin QFN, Pb-Free, Tape and Reel | IC2.1, IC2.2 |  | 2 | 0
 | MB85RS2MTAPNF-G-BDERE1 | FRAM (Ferroelectric RAM) Memory IC 2Mb (256K x 8) SPI 40MHz 8-SOP | IC3 |  | 1 | 0 | Fujitsu | MB85RS2MTAPNF-G-BDERE1 |  | Digi-Key | 865-1286-1-ND | 6.25 | 6.25
 | IS42S16400J-7TLI | SDRAM, 4M x 16 Bit | IC4 |  | 1 | 0 | ISSI | IS42S16400J-7TLI | Volume Production | Digi-Key | 706-1132-ND | 1.94 | 1.94
 | SLW-112-01-T-D | Low Profile Socket Strips, Through-hole, Vertical, -55 to 105 degC, 2.54 mm Pitch, 24-Pin, Female, RoHS | JP1, JP2 |  | 2 | 0 | Samtec | SLW-112-01-S-D | Volume Production | Digi-Key | SAM1090-12-ND | 3.76 | 7.52
 | BLM21AG471SN1J | Chip Ferrite Bead for General Signal lines, 470 Ohm, 700 mA, -55 to 125 degC, 2 x 1.25 x 1.05 mm SMD, Tape and Reel | L1.1, L1.2, L2.1, L2.2, L6, L7, L8, L9, L10, L11, L12, L13, L14, L17 |  | 14 | 0 | Murata | BLM21AG471SZ1D |  | Digi-Key | 490-16493-6-ND | 0.12272 | 1.72
 | 744042100 | Inductor, Shielded Drum Core, Ferrite, 10 uH, 1 A, 0.12 ohm, SMD | L3.1, L3.2 |  | 2 | 0 | Wurth Electronics | 744042100 | Volume Production | Farnell | 1635842 | 1.95 | 3.91
 | 742792021 | Ferrite Bead, 22 ohm @ 100 MHz, 6 A, 0805 | L4.1, L4.2 |  | 2 | 0 | Wurth Electronics | 742792021 | Volume Production | Digi-Key | 732-4637-1-ND | 0.2213 | 0.44261
 | SDR0403-4R7ML | 4.7uH | L5 |  | 1 | 0 | Bourns | SDR0403-4R7ML | Volume Production | Digi-Key | SDR0403-4R7MLCT-ND | 0.60355 | 0.60355
 | PA4332.222NLT | Imported | L15_1, L15_2 |  | 2 | 0 | Pulse | PA4332.222NLT | Volume Production | Mouser | 673-PA4332222NLT | 0.61361 | 1.23
 | Wurth 750316031 Xformer | Isolated interface power supply for CAN, RS-485, RS-422, RS-232, SPI, I2C, lower-power LAN 1:1 1A | L16 |  | 1 | 0 | Wurth Electronics Midcom | 750316031 |  | Farnell | 2907253 | 7.14 | 7.14
 | B82789C0104H001 | Coupled inductor, 100 µH, 0.15 A, 1.5 ohm, SMD | L20.1, L20.2 |  | 2 | 0 | TDK EPCOS | B82789C0104H001 | Not Recommended for New Design | Mouser | 871-B82789C0104H001
 | green | LED | LED1, LED4 | 0603 | 2 | 0 | Wurth Electronics | 150060VS75000 | Volume Production | Digi-Key | 732-4980-1-ND | 0.14083 | 0.28166
 | red | LED | LED2, LED5 | 0603 | 2 | 0 | Wurth Electronics | 150060RS75000 | Volume Production | Digi-Key | 732-4978-1-ND | 0.14083 | 0.28166
 | orange | LED | LED3, LED6 | 0603 | 2 | 0 | Wurth Electronics | 150060YS75000 | Volume Production | Digi-Key | 732-4981-1-ND | 0.14083 | 0.28166
 | PS1240P02CT3 | Loudspeaker | LS1 |  | 1 | 0 | TDK | PS1240P02CT3 | Volume Production | Digi-Key | 445-5229-1-ND | 0.73432 | 0.73432
 | CX2520DB32000D0GEJZ1 | Crystal,CRYSTAL 40MHZ 15PF 85degC Surface Mount 2.5 x 2.0 mm | Q1, Q13 |  | 2 | 0 | Abracon | ABM3B-8.000MHZ-10-1-U-T | Volume Production | Digi-Key | 535-9721-1-ND | 0.69409 | 1.39
 | BSS138 | MOSFET, N-CH, 50V, 0.22A, SOT-23 | Q2, Q4, Q6, Q8, Q10 |  | 5 | 0 | Micross | BSS138 |  | Farnell | 9845330 | 0.27747 | 1.39
 | CSD17308Q3 | MOSFET, N-CH, 30V, 47A, SON 3.3x3.3mm | Q3 |  | 1 | 0 | Texas Instruments | CSD17308Q3 | Volume Production | Farnell | 3125023 | 0.98742 | 4.94
 | CSD18543Q3A | 60V, N ch NexFET MOSFET™, single SON3x3, 9.9mOhm | Q5, Q7, Q9, Q11 |  | 4 | 0 |  |  |  | Digi-Key | 296-45302-1-ND
 | 32.768kHz | Crystal, 32.768 KHz, 12.5 pF, -40 to 85 degC, 2-Pin SMD, RoHS, Tape and Reel | Q12 |  | 1 | 0 | Epson | FC-13532.7680KA-A3 | Volume Production | Digi-Key | SER4071DKR-ND
 | 27R | SMD Resistor 27R 0603 | R1.1, R1.2, R5.1, R5.2 | 0603 | 4 | 0 | Panasonic | ERJ-3GEYJ270V | Volume Production | Farnell | 2059559 | 0.05888 | 0.58881
 | 130R | SMD Resistor 130R 0603 | R2, R3, R4, R60, R61, R62 | 0603 | 6 | 0 | Panasonic | ERJ3RBD1300V | Volume Production | Farnell | 2379959 | 0.09119 | 0.91187
 | 0.01R | SMD Resistor 10m 0805 | R6, R116 | 0805 | 2 | 0
 | 0R | SMD Resistor 0R 0603 | R7.1, R7.2, R8.1, R8.2, R9, R20.1, R20.2, R26, R55, R56 | 0603 | 10 | 0 | Multicomp | MCMR06X000PTL | Volume Production | Farnell | 2073345 | 0.00782 | 0.07816
 | 680R | SMD Resistor 680R 0603 | R10, R54 | 0603 | 2 | 0 | Panasonic | ERA3APB681V | Volume Production | Farnell | 2797303 | 0.65394 | 6.54
 | 1k2 | SMD Resistor 1k2 0603 | R11.1, R11.2, R11.3, R11.4 | 0603 | 4 | 0 | Multicomp | MCMR06X1201FTL | Volume Production | Farnell | 2073370 | 0.00951 | 0.09509
 | 806R | SMD Resistor 806R 0603 | R12.1, R12.2, R12.3, R12.4 | 0603 | 4 | 0 | Panasonic | ERJ-3EKF8060V | Volume Production | Farnell | 2059324 | 0.08376 | 0.83762
 | 2k | SMD Resistor 2k 0603 | R13.1, R13.2, R14.1, R14.2 | 0603 | 4 | 0 | Panasonic | ERJ-3EKF2001V | Volume Production | Farnell | 2059343 | 0.08207 | 0.82068
 | 120R | SMD Resistor 120R 0603 | R15.1, R15.2, R15.3, R15.4 | 0603 | 4 | 0 | Yageo | RC0805FR-07120RL | Volume Production | Digi-Key | 311-120CRCT-ND | 0.04024 | 0.40237
 | 0R | SMD Resistor 10m 0805 | R16, R57, R113, R123 | 0805 | 4 | 0
 | 10k | SMD Resistor 10k 0603 | R17, R24, R34, R35, R41, R70, R73, R74, R75, R78, R79, R80, R83, R84, R86, R92, R93, R94, R95, R96, R99, R101, R115, R134, R138, R139, R140, R141, R142, R143 | 0603 | 30 | 0 | MULTICOMP PRO | MCMR06X1002FTL |  | Farnell | 2073349
 | CRCW0603100RFKEA | RES, 100, 1%, 0.1 W, 0603 | R21.1, R21.2, R33.1, R33.2 |  | 4 | 0 | Vishay Dale | CRCW0603100RFKEA | Volume Production | Digi-Key | 541-100HCT-ND | 0.0342 | 0.34201
 | 20k | SMD Resistor 20k 0603 | R23.1, R23.2 | 0603 | 2 | 0 | Panasonic | ERJ3EKF2002V | Volume Production | Farnell | 2059432 | 0.07868 | 0.78681
 | 100k | SMD Resistor 100k 0603 | R25, R58, R104, R109, R110, R117, R119, R126 | 0603 | 8 | 0
 | 0R | SMD Resistor 0R 0402 | R31, R48, R64, R112 | 0402 | 4 | 0
 | CRCW0603158KFKEA | RES, 158 k, 1%, 0.1 W, AEC-Q200 Grade 0, 0603 | R39.1, R39.2 |  | 2 | 0 | Vishay | CRCW0603158KFKEA | Volume Production | Digi-Key | 541-158KHCT-ND | 0.10059 | 0.20118
 | 10R | SMD Resistor 10R 0603 | R40, R85, R132 | 0603 | 3 | 0 | Multicomp | MCMR06X10R0FTL | Volume Production | Farnell | 2073361 | 0.01803 | 0.18035
 | CRCW0603130KFKEA | RES, 130 k, 1%, 0.1 W, AEC-Q200 Grade 0, 0603 | R44.1, R44.2 |  | 2 | 0 | Vishay | CRCW0603130KFKEA | Volume Production | Digi-Key | 541-130KHCT-ND | 0.10059 | 0.20118
 | CRCW060312K1FKEA | RES, 12.1 k, 1%, 0.1 W, 0603 | R45.1, R45.2 |  | 2 | 0 | Vishay | CRCW060312K1FKEA | Volume Production | Digi-Key | 541-12.1KHCT-ND | 0.10059 | 0.20118
 | 430R | SMD Resistor 430R 0603 | R46, R87 | 0603 | 2 | 0 | Multicomp | MCSR06X4300FTL | Volume Production | Farnell | 2074259 | 0.01159 | 0.11594
 | 10.7k | SMD Resistor 10.7k 0402 | R47 | 0402 | 1 | 0
 | 26.1k | SMD Resistor 26.1k 0402 | R49, R63 | 0402 | 2 | 0
 | 49k9 | SMD Resistor 49.9k 0402 | R50, R65 | 0402 | 2 | 0
 | 100k | SMD Resistor 100k 0402 | R51 | 0402 | 1 | 0
 | 600R | SMD Resistor 330R 0603 | R52 | 0805 | 1 | 0
 | 374k | SMD Resistor 374k 0402 | R53, R66 | 0402 | 2 | 0
 | 0.47 | SMD Resistor 0R47 0402 | R59 | 0402 | 1 | 0
 | 30k | SMD Resistor 30k 0402 | R67 | 0402 | 1 | 0
 | 56k | SMD Resistor 49.9k 0402 | R68 | 0402 | 1 | 0
 | 49k9 | SMD Resistor 49.9k 0402 | R69 | 0402 | 1 | 0
 | 40R | SMD Resistor 120R 0603 | R71 | 0805 | 1 | 0 | Multicomp | MCMR06X1200FTL | Volume Production | Farnell | 2073369 | 0.01779 | 0.17791
 | 20k | SMD Resistor 120R 0603 | R72 | 0805 | 1 | 0 | Multicomp | MCMR06X1200FTL | Volume Production | Farnell | 2073369 | 0.01779 | 0.17791
 | 47R | SMD Resistor 47R 0603 | R76, R77, R81, R82, R89, R90, R97, R98 | 0603 | 8 | 0 | Panasonic | ERJ-3EKF47R0V | Volume Production | Farnell | 2303030 | 0.03869 | 0.38689
 | 100k | SMD Resistor 100k 0603 | R88, R91, R108 | 0603 | 3 | 0
 | 47k | SMD Resistor 47k 0603 | R100 | 0603 | 1 | 0 | Multicomp | MCMR06X4702FTL | Volume Production | Farnell | 2073510 | 0.01003 | 0.10031
 | 10R | SMD Resistor 10R 0603 | R118, R120, R121, R122 | 0603 | 4 | 0 | Multicomp | MCMR06X10R0FTL | Volume Production | Farnell | 2073361 | 0.01803 | 0.18035
 | CRCW120660R4FKEA | RES, 60.4, 1%, 0.25 W, 1206 | R124.1, R124.2, R125.1, R125.2 |  | 4 | 0 | Vishay | CRCW120660R4FKEA | Volume Production | Digi-Key | 541-60.4FCT-ND | 0.10059 | 0.40237
 | 4k7 | SMD Resistor 4.7k 0603 | R127, R128 | 0603 | 2 | 0
 | 10M | SMD Resistor 10M 0603 | R129 | 0603 | 1 | 0
 | NF | SMD Resistor NF 0603 | R130 | 0603 | 1 | 0
 | 1k | SMD Resistor 1k 0603 | R137 | 0603 | 1 | 0
 | KMR221GLFS | Microminiature Tactile Switch | S1, S2 |  | 2 | 0 | ITT C&K | KMR221GLFS | Volume Production | Digi-Key | 401-1427-1-ND | 0.52308 | 1.05
 | TSW-106-07-G-D | Board-To-Board Connector, Vertical, 2.54 mm, 12 Contacts, Header, TSW Series, Through Hole, 2 Rows | SV1 |  | 1 | 0 | Samtec | TSW-106-07-G-D | Volume Production | Farnell | 2984502 | 1.05 | 1.05
 | TSW-104-07-G-D | Board-To-Board Connector, Vertical, 2.54 mm, 8 Contacts, Header, TSW Series, Through Hole, 2 Rows | SV2 |  | 1 | 0 | Samtec | TSW-104-07-G-D-LL | Volume Production | Digi-Key | TSW-104-07-G-D-LL-ND | 1.02 | 1.02
 | SLW-104-01-G-D | Board-To-Board Connector, Dual, 2.54 mm, 8 Contacts, Receptacle, SLW Series, Through Hole, 2 Rows | SV3 |  | 1 | 0 | Samtec | SLW-104-01-G-D | Volume Production | Digi-Key | SAM1088-04-ND | 1.41 | 1.41
 | YA8779-BL | Transformer, 30 uH, SMD | T1.1, T1.2 |  | 2 | 0 | Coilcraft | YA8779-BLD
 | BSS84P | P-Channel SIPMOS Small-Signal-Transistor, -60 V VDS, -0.17 A ID, -55 to 150 degC, PG-SOT23, Reel, Green | T2, T4, T5, T7 |  | 4 | 0 | Infineon | BSS84P | Volume Production | Digi-Key | BSS84PH6327XTSA2CT-ND | 0.34201 | 1.37
 | IRLML0100TRPBF | MOSFET-Transistor, n-Kanal, 1.6 A, 100 V, 0.178 ohm, 10 V, 2.5 V | T3, T6, T9 |  | 3 | 0 | International Rectifier | IRLML0100TRPBF | Volume Production | Digi-Key | IRLML0100TRPBFCT-ND | 0.48284 | 1.45
 | SS/BIAS | Test Point, Miniature, SMT | TP9.1, TP9.2 |  | 2 | 0 |  |  |  | Digi-Key | 36-5015TR-ND
 | HX1188NL | 10/100 Base-T Single Port Surface Mount Magnetic with Turns Ratio, -40 to 85 degC, 16-Pin Module, RoHS, Tube | TR1, TR2 |  | 2 | 0
 | TPS62142RGTR | Imported | U1.1, U1.2 |  | 2 | 0 | Texas Instruments | TPS62142RGTR | Volume Production | Digi-Key | 296-39447-1-ND | 2.09 | 4.18
 | STM32F429VIT6 | ARM Cortex-M4 32-bit MCU+FPU, 225 DMIPS, 2048 kB Flash, 256 kB Internal RAM, 82 I/Os, 100-pin LQFP, -40 to 85 degC, Tray | U2 |  | 1 | 0 | STMicroelectronics | STM32F429VIT6 | Volume Production | Digi-Key | 497-14052-ND | 13.01 | 13.01
 | LTC6820IUD#PBF | IsoSPI Isolated Communication Interface, 2.7 to 5.5 V, -40 to 85 degC, 16-Pin QFN (UD-16EPV-AA), Pb-Free | U3.1, U3.2, U3.3, U3.4 |  | 4 | 0
 | SN74LVC00ARGYR | Quadruple 2-Input Positive-NAND Gate, RGY0014A, LARGE T&R | U4.1, U4.2 |  | 2 | 0
 | LM3724IM5-3.08/NOPB | 5-Pin Microprocessor Reset Circuits, 5-pin SOT-23, Pb-Free | U7, U17 |  | 2 | 0
 | AQY212GHA | PhotoMOS GU 1 Form A, 60 V Load Voltage, 1.1 A Continuous Load Current, -40 to 85 degC, 4-Pin DIP(SMT), Tube, RoHS | U8, U11, U21, U24 |  | 4 | 0 | Panasonic | AQY212GHA | Volume Production | RSComponents | 8113292 | 3.93 | 15.7
 | LM5180QNGURQ1 | 70-V PSR Flyback Converter With 100-V, 1.2-A Power Switch and Ultra-Low IQ, NGU0008C (WSON-8) | U12.1, U12.2 |  | 2 | 0 | Texas Instruments | LM5180NGUR |  | Digi-Key | 296-LM5180NGURDKR-ND | 6.3 | 12.59
 | TPS26602RHFR | 37V Clamped input protection | U13 |  | 1 | 0 | Texas Instruments | TPS26602RHFR |  | Digi-Key | 296-51900-1-ND | 5.26 | 5.26
 | ISO7762DBQR | Imported | U14 |  | 1 | 0 | Texas Instruments | ISO7762DBQR |  | Digi-Key | 296-49451-6-ND | 3.75 | 3.75
 | TVS3301DRBR | TVS3301 33-V Bidirectional Flat-Clamp Surge Protection Device | U15, U20 |  | 2 | 0 | Texas Instruments | TVS3301DRBR |  | Digi-Key | 296-53063-1-ND | 0.84498 | 1.69
 | LM536013QDSXRQ1 | Imported | U16 |  | 1 | 0 | Texas Instruments | LM536013QDSXRQ1 |  | Mouser | 595-LM536013QDSXRQ1 | 4.6 | 4.6
 | LT3092EDD#TRPBF | 200 mA Two-Terminal Programmable Current Source, 0.3 mA Isupply, 8-pin SON (DD-8), -40 to 125 degC, Pb-Free, Tape and Reel | U18 |  | 1 | 0 | Analog Devices / Linear Technology | LT3092EDD#TRPBF | Volume Production | Digi-Key | LT3092EDD#TRPBFDKR-ND | 4.28 | 4.28
 | TPS26630RGET | Imported | U19 |  | 1 | 0 | Texas Instruments | TPS26630RGET |  | Mouser | 595-TPS26630RGET | 6.07 | 6.07
 | MOLEX_47352-1001 | 1.10mm Pitch Memorycard Card Connector, Push-Push Type, with VSS (Supply Voltage Ground) Detect Switch, Lead-Free | U22 |  | 1 | 0 | Molex | 47352-1001 | Volume Production | Digi-Key | WM3290CT-ND | 3.96 | 3.96
 | ISO7761DWR | Imported | U23, U25 |  | 2 | 0 | Texas Instruments | ISO7761DW |  | Farnell | 2842967 | 5.74 | 11.49
 | STM32F429IIT6 | ARM Cortex-M4 32-bit MCU+FPU, 225 DMIPS, 2048 kB Flash, 256 kB Internal RAM, 140 I/Os, 176-pin LQFP, -40 to 85 degC, Tray | U26 |  | 1 | 0 | STMicroelectronics | STM32F429IIT6 | Volume Production | Digi-Key | 497-14054-ND | 14.3 | 14.3
 | LM3880MFX-1AB/NOPB | Power Sequencer, 6-pin SOT-23, Pb-Free | U28 |  | 1 | 0 | TI National Semiconductor | LM3880MFX-1AB/NOPB | Volume Production | Digi-Key | 296-38724-6-ND | 1.36 | 1.36
 | SN6505ADBVR | Imported | U31 |  | 1 | 0 | Texas Instruments | SN6505ADBVR | Not Recommended for New Design | Digi-Key | 296-48949-6-ND | 2.64 | 2.64
 | ADR3425ARJZ-R2 | Micropower, High Accuracy Voltage Reference, 2.5 V Output, 2.7 to 5.5 V Supply, Industrial, 6-pin SOT23 (RJ-6), Reel | U33 |  | 1 | 0 | Analog Devices | ADR3425ARJZ-R2 | Volume Production | Digi-Key | ADR3425ARJZ-R2CT-ND | 4.26 | 4.26
 | ISO1432DWR | 5-kVrms isolated RS-485/RS-422 transceiver with robust EMC | U34 |  | 1 | 0 | Texas Instruments | ISO1432DW |  | Mouser | 595-ISO1432DW | 9.09 | 9.09
 | PSM712-LF-T7 | TVS Array - Asymmetrical Data Line Protector, 600 W, 7.5 V, -55 to 150 degC, 3-Pin SOT23, RoHS, Tape and Reel | U35, U37 |  | 2 | 0 | Protek Devices | PSM712LFT7 | Volume Production
 | LTC2990 |  | U36 |  | 1 | 0 | Analog Devices / Linear Technology | LTC2990CMS#PBF | Volume Production | Digi-Key | LTC2990CMS#PBF-ND | 5.49 | 5.49
 | ISO1042DWVR | Imported | U38.1, U38.2 |  | 2 | 0 | Texas Instruments | ISO1042DWVR |  | Digi-Key | 296-ISO1042DWVRDKR-ND | 4.82 | 9.64
 | TPD2E007DCKR | ESD Protection Array for AC Signal Data Interface, 2 Channels, -40 to +85 degC, 3-pin SC70 (DCK), Green (RoHS & no Sb/Br) | U39.1, U39.2 |  | 2 | 0 | Texas Instruments | TPD2E007DCKR | Volume Production | Farnell | 2120465 | 0.69042 | 1.38
 | DS1339-U33 |  | U40 |  | 1 | 0 | Maxim | DS1339U-33+T&R | Volume Production | Digi-Key | DS1339U-33+T&RCT-ND | 3.54 | 3.54
 | 54819-0589 | USB, MINI, SMD, RA KME04-USBMU03A01 | X1.1, X1.2 |  | 2 | 0 | Molex | 54819-0589 | Volume Production | Digi-Key | WM3895CT-ND | 1.4 | 2.8
 | 95501-2441 | Connector | X2, X4 |  | 2 | 0 | Molex | 95501-2441 | Volume Production | Digi-Key | WM5568-ND | 0.93551 | 1.87
 | samtec_TSW-102-07-G-S | Board-To-Board Connector, Vertical, 2.54 mm, 2 Contacts, Header, TSW Series, Through Hole, 1 Row | X3, X8, X10 |  | 3 | 0 | Samtec | TSW-102-07-G-S | Volume Production | Farnell | 2505044 | 0.20452 | 2.05
 | FTSH-110-01-L-DV-007-K-P | Board-To-Board Connector, ARM Cortex Debug Header 20 Pin | X5, X9 |  | 2 | 0 | Samtec | FTSH-110-01-L-DV-007-K-P |  | Digi-Key | SAM11268-ND | 5.53 | 11.07
 | 43045-0221 | Micro-Fit 3.0 Right Angle Header, 3.00mm Pitch, Dual Row, 2 Circuits, with Snap-in Plastic Peg PCB Lock, Tin, Glow Wire Capable, Black, 43045-0200 | X6 |  | 1 | 0 | Molex | 0430450221 | Volume Production | Farnell | 3051552 | 1.26 | 1.26
 | 43045-0621 | Micro-Fit 3.0 Right Angle Header, 3.00mm Pitch, Dual Row, 6 Circuits, with Snap-in Plastic Peg PCB Lock, Tin, Glow Wire Capable, Black, 43045-0621 | X7 |  | 1 | 0 | Molex | 43045-0621 | Volume Production | Digi-Key | WM2674-ND | 1.9 | 1.9
 | 43045-1621 | Micro-Fit 3.0 Right Angle Header, 3.00mm Pitch, Dual Row, 16 Circuits, with Snap-in Plastic Peg PCB Lock, Tin, Glow Wire Capable, Black, 43045-1600 | X11 |  | 1 | 0 | Molex | 0430451621 | Volume Production | Farnell | 3049101 | 4.86 | 4.86
 | 43045-0621 | Micro-Fit 3.0 Right Angle Header, 3.00mm Pitch, Dual Row, 6 Circuits, with Snap-in Plastic Peg PCB Lock, Tin, Glow Wire Capable, Black, 43045-0621 | X12 |  | 1 | 0 | Molex | 43045-0621 | Volume Production | Farnell | 2381275 | 2.02 | 2.02
 | CONN MOD JACK 6P6C R/A UNSHLD | Jack Modular Connector 6p6c (RJ9, RJ10, RJ22) 90° Angle (Right) Unshielded Cat3 | X13, X16 |  | 2 | 0 | Molex | 95501-2441 | Volume Production | Farnell | 1560167 | 0.65003 | 6.5
 | ABS07-120 32.768k |  | X15 |  | 1 | 0 | Abracon | ABS07-120-32.768KHZ-T | Volume Production | Digi-Key | 535-11937-1-ND | 0.77456 | 0.77456
