ArakniD/foxbms/hardware/datasheets/Capacitor lookups.xlsx

Sheet: Sheet1
Order | designator | partNo | Temp | LxW | Height | Height2 | EIA | Metric | Temp3 | Volts | Tolerance | Cap_Short | Cap | Comment | Series | PnP | Text | Lib Ref | Description
1 | C90 | GCJ21BR71A106KE01 | R7 | 21 | B | 1.25mm | 0805 | 2012 | –55 to 125°C | 10V | ±10% | 10u | 10µF | 10µF 10V | GCJ | 10µF/10V/X7R | Ceramic, 10µF, ±10%, 10V, X7R, –55 to 125°C, 0805 (2012),RoHS, Automotive | gen_C_ceramic_10u_X7R_0805 | 10µF 0805 (2012) ±10% 10V X7R
2 | C91 | GCJ21BR71A106KE01 | R7 | 21 | B | 1.25mm | 0805 | 2012 | –55 to 125°C | 10V | ±10% | 10u | 10µF | 10µF 10V | GCJ | 10µF/10V/X7R | Ceramic, 10µF, ±10%, 10V, X7R, –55 to 125°C, 0805 (2012),RoHS, Automotive | gen_C_ceramic_10u_X7R_0805 | 10µF 0805 (2012) ±10% 10V X7R
3 | C111 | GCJ21BR71A106KE01 | R7 | 21 | B | 1.25mm | 0805 | 2012 | –55 to 125°C | 10V | ±10% | 10u | 10µF | 10µF 10V | GCJ | 10µF/10V/X7R | Ceramic, 10µF, ±10%, 10V, X7R, –55 to 125°C, 0805 (2012),RoHS, Automotive | gen_C_ceramic_10u_X7R_0805 | 10µF 0805 (2012) ±10% 10V X7R
4 | C117 | GCJ21BR71A106KE01 | R7 | 21 | B | 1.25mm | 0805 | 2012 | –55 to 125°C | 10V | ±10% | 10u | 10µF | 10µF 10V | GCJ | 10µF/10V/X7R | Ceramic, 10µF, ±10%, 10V, X7R, –55 to 125°C, 0805 (2012),RoHS, Automotive | gen_C_ceramic_10u_X7R_0805 | 10µF 0805 (2012) ±10% 10V X7R
5 | C14 | GCJ21BR71A106KE01 | R7 | 21 | B | 1.25mm | 0805 | 2012 | –55 to 125°C | 10V | ±10% | 10u | 10µF | 10µF 10V | GCJ | 10µF/10V/X7R | Ceramic, 10µF, ±10%, 10V, X7R, –55 to 125°C, 0805 (2012),RoHS, Automotive | gen_C_ceramic_10u_X7R_0805 | 10µF 0805 (2012) ±10% 10V X7R
6 | C16 | GCJ21BR71A106KE01 | R7 | 21 | B | 1.25mm | 0805 | 2012 | –55 to 125°C | 10V | ±10% | 10u | 10µF | 10µF 10V | GCJ | 10µF/10V/X7R | Ceramic, 10µF, ±10%, 10V, X7R, –55 to 125°C, 0805 (2012),RoHS, Automotive | gen_C_ceramic_10u_X7R_0805 | 10µF 0805 (2012) ±10% 10V X7R
7 | C1 | GCJ21BR71C475KA01 | R7 | 21 | B | 1.25mm | 0805 | 2012 | –55 to 125°C | 16V | ±10% | 4u7 | 4.7µF | 4.7µF 16V | GCJ | 4.7µF/16V/X7R | Ceramic, 4.7µF, ±10%, 16V, X7R, –55 to 125°C, 0805 (2012),RoHS, Automotive | gen_C_ceramic_4u7_X7R_0805 | 4.7µF 0805 (2012) ±10% 16V X7R
8 | C31 | GCJ21BR71C475KA01 | R7 | 21 | B | 1.25mm | 0805 | 2012 | –55 to 125°C | 16V | ±10% | 4u7 | 4.7µF | 4.7µF 16V | GCJ | 4.7µF/16V/X7R | Ceramic, 4.7µF, ±10%, 16V, X7R, –55 to 125°C, 0805 (2012),RoHS, Automotive | gen_C_ceramic_4u7_X7R_0805 | 4.7µF 0805 (2012) ±10% 16V X7R
9 | C48 | GCJ21BR71C475KA01 | R7 | 21 | B | 1.25mm | 0805 | 2012 | –55 to 125°C | 16V | ±10% | 4u7 | 4.7µF | 4.7µF 16V | GCJ | 4.7µF/16V/X7R | Ceramic, 4.7µF, ±10%, 16V, X7R, –55 to 125°C, 0805 (2012),RoHS, Automotive | gen_C_ceramic_4u7_X7R_0805 | 4.7µF 0805 (2012) ±10% 16V X7R
10 | C36 | GCJ21BR71E225KA01 | R7 | 21 | B | 1.25mm | 0805 | 2012 | –55 to 125°C | 25V | ±10% | 2u2 | 2.2µF | 2.2µF 25V | GCJ | 2.2µF/25V/X7R | Ceramic, 2.2µF, ±10%, 25V, X7R, –55 to 125°C, 0805 (2012),RoHS, Automotive | gen_C_ceramic_2u2_X7R_0805 | 2.2µF 0805 (2012) ±10% 25V X7R
11 | C60 | GCJ21BR71E225KA01 | R7 | 21 | B | 1.25mm | 0805 | 2012 | –55 to 125°C | 25V | ±10% | 2u2 | 2.2µF | 2.2µF 25V | GCJ | 2.2µF/25V/X7R | Ceramic, 2.2µF, ±10%, 25V, X7R, –55 to 125°C, 0805 (2012),RoHS, Automotive | gen_C_ceramic_2u2_X7R_0805 | 2.2µF 0805 (2012) ±10% 25V X7R
12 | C88 | GCJ21BR71E225KA01 | R7 | 21 | B | 1.25mm | 0805 | 2012 | –55 to 125°C | 25V | ±10% | 2u2 | 2.2µF | 2.2µF 25V | GCJ | 2.2µF/25V/X7R | Ceramic, 2.2µF, ±10%, 25V, X7R, –55 to 125°C, 0805 (2012),RoHS, Automotive | gen_C_ceramic_2u2_X7R_0805 | 2.2µF 0805 (2012) ±10% 25V X7R
13 | C12 | GCJ21BR71E225KA01 | R7 | 21 | B | 1.25mm | 0805 | 2012 | –55 to 125°C | 25V | ±10% | 2u2 | 2.2µF | 2.2µF 25V | GCJ | 2.2µF/25V/X7R | Ceramic, 2.2µF, ±10%, 25V, X7R, –55 to 125°C, 0805 (2012),RoHS, Automotive | gen_C_ceramic_2u2_X7R_0805 | 2.2µF 0805 (2012) ±10% 25V X7R
14 | C8 | GCJ21BR71E225KA01 | R7 | 21 | B | 1.25mm | 0805 | 2012 | –55 to 125°C | 25V | ±10% | 2u2 | 2.2µF | 2.2µF 25V | GCJ | 2.2µF/25V/X7R | Ceramic, 2.2µF, ±10%, 25V, X7R, –55 to 125°C, 0805 (2012),RoHS, Automotive | gen_C_ceramic_2u2_X7R_0805 | 2.2µF 0805 (2012) ±10% 25V X7R
15 | C92 | GCJ188R71E105KA01 | R7 | 18 | 8 | 0.8mm | 0603 | 1608 | –55 to 125°C | 25V | ±10% | 1u | 1.0µF | 1.0µF 25V | GCJ | 1.0µF/25V/X7R | Ceramic, 1.0µF, ±10%, 25V, X7R, –55 to 125°C, 0603 (1608),RoHS, Automotive | gen_C_ceramic_1u_X7R_0603 | 1.0µF 0603 (1608) ±10% 25V X7R
16 | C95 | GCJ188R71E105KA01 | R7 | 18 | 8 | 0.8mm | 0603 | 1608 | –55 to 125°C | 25V | ±10% | 1u | 1.0µF | 1.0µF 25V | GCJ | 1.0µF/25V/X7R | Ceramic, 1.0µF, ±10%, 25V, X7R, –55 to 125°C, 0603 (1608),RoHS, Automotive | gen_C_ceramic_1u_X7R_0603 | 1.0µF 0603 (1608) ±10% 25V X7R
17 | C56 | GCJ188R71E105KA01 | R7 | 18 | 8 | 0.8mm | 0603 | 1608 | –55 to 125°C | 25V | ±10% | 1u | 1.0µF | 1.0µF 25V | GCJ | 1.0µF/25V/X7R | Ceramic, 1.0µF, ±10%, 25V, X7R, –55 to 125°C, 0603 (1608),RoHS, Automotive | gen_C_ceramic_1u_X7R_0603 | 1.0µF 0603 (1608) ±10% 25V X7R
18 | C28 | GCJ188R71E105KA01 | R7 | 18 | 8 | 0.8mm | 0603 | 1608 | –55 to 125°C | 25V | ±10% | 1u | 1.0µF | 1.0µF 25V | GCJ | 1.0µF/25V/X7R | Ceramic, 1.0µF, ±10%, 25V, X7R, –55 to 125°C, 0603 (1608),RoHS, Automotive | gen_C_ceramic_1u_X7R_0603 | 1.0µF 0603 (1608) ±10% 25V X7R
19 | C34 | GCJ188R71E105KA01 | R7 | 18 | 8 | 0.8mm | 0603 | 1608 | –55 to 125°C | 25V | ±10% | 1u | 1.0µF | 1.0µF 25V | GCJ | 1.0µF/25V/X7R | Ceramic, 1.0µF, ±10%, 25V, X7R, –55 to 125°C, 0603 (1608),RoHS, Automotive | gen_C_ceramic_1u_X7R_0603 | 1.0µF 0603 (1608) ±10% 25V X7R
20 | C73 | GCJ188R71E105KA01 | R7 | 18 | 8 | 0.8mm | 0603 | 1608 | –55 to 125°C | 25V | ±10% | 1u | 1.0µF | 1.0µF 25V | GCJ | 1.0µF/25V/X7R | Ceramic, 1.0µF, ±10%, 25V, X7R, –55 to 125°C, 0603 (1608),RoHS, Automotive | gen_C_ceramic_1u_X7R_0603 | 1.0µF 0603 (1608) ±10% 25V X7R
21 | C75 | GCJ188R71E105KA01 | R7 | 18 | 8 | 0.8mm | 0603 | 1608 | –55 to 125°C | 25V | ±10% | 1u | 1.0µF | 1.0µF 25V | GCJ | 1.0µF/25V/X7R | Ceramic, 1.0µF, ±10%, 25V, X7R, –55 to 125°C, 0603 (1608),RoHS, Automotive | gen_C_ceramic_1u_X7R_0603 | 1.0µF 0603 (1608) ±10% 25V X7R
22 | C80 | GCJ188R71E105KA01 | R7 | 18 | 8 | 0.8mm | 0603 | 1608 | –55 to 125°C | 25V | ±10% | 1u | 1.0µF | 1.0µF 25V | GCJ | 1.0µF/25V/X7R | Ceramic, 1.0µF, ±10%, 25V, X7R, –55 to 125°C, 0603 (1608),RoHS, Automotive | gen_C_ceramic_1u_X7R_0603 | 1.0µF 0603 (1608) ±10% 25V X7R
23 | C99 | GCJ188R71E105KA01 | R7 | 18 | 8 | 0.8mm | 0603 | 1608 | –55 to 125°C | 25V | ±10% | 1u | 1.0µF | 1.0µF 25V | GCJ | 1.0µF/25V/X7R | Ceramic, 1.0µF, ±10%, 25V, X7R, –55 to 125°C, 0603 (1608),RoHS, Automotive | gen_C_ceramic_1u_X7R_0603 | 1.0µF 0603 (1608) ±10% 25V X7R
24 | C116 | GCJ188R71E105KA01 | R7 | 18 | 8 | 0.8mm | 0603 | 1608 | –55 to 125°C | 25V | ±10% | 1u | 1.0µF | 1.0µF 25V | GCJ | 1.0µF/25V/X7R | Ceramic, 1.0µF, ±10%, 25V, X7R, –55 to 125°C, 0603 (1608),RoHS, Automotive | gen_C_ceramic_1u_X7R_0603 | 1.0µF 0603 (1608) ±10% 25V X7R
25 | C19 | GCJ188R71E105KA01 | R7 | 18 | 8 | 0.8mm | 0603 | 1608 | –55 to 125°C | 25V | ±10% | 1u | 1.0µF | 1.0µF 25V | GCJ | 1.0µF/25V/X7R | Ceramic, 1.0µF, ±10%, 25V, X7R, –55 to 125°C, 0603 (1608),RoHS, Automotive | gen_C_ceramic_1u_X7R_0603 | 1.0µF 0603 (1608) ±10% 25V X7R
26 | C103 | GCJ188R71H102KA01 | R7 | 18 | 8 | 0.8mm | 0603 | 1608 | –55 to 125°C | 50V | ±10% | 10n | 10nF | 10nF 50V | GCJ | 10nF/50V/X7R | Ceramic, 10nF, ±10%, 50V, X7R, –55 to 125°C, 0603 (1608),RoHS, Automotive | gen_C_ceramic_10n_X7R_0603 | 10nF 0603 ±10% 50V X7R
27 | C89 | GCJ188R71H102KA01 | R7 | 18 | 8 | 0.8mm | 0603 | 1608 | –55 to 125°C | 50V | ±10% | 10n | 10nF | 10nF 50V | GCJ | 10nF/50V/X7R | Ceramic, 10nF, ±10%, 50V, X7R, –55 to 125°C, 0603 (1608),RoHS, Automotive | gen_C_ceramic_10n_X7R_0603 | 10nF 0603 ±10% 50V X7R
28 | C112 | GCJ188R71H102KA01 | R7 | 18 | 8 | 0.8mm | 0603 | 1608 | –55 to 125°C | 50V | ±10% | 10n | 10nF | 10nF 50V | GCJ | 10nF/50V/X7R | Ceramic, 10nF, ±10%, 50V, X7R, –55 to 125°C, 0603 (1608),RoHS, Automotive | gen_C_ceramic_10n_X7R_0603 | 10nF 0603 ±10% 50V X7R
29 | C115 | GCJ188R71H102KA01 | R7 | 18 | 8 | 0.8mm | 0603 | 1608 | –55 to 125°C | 50V | ±10% | 10n | 10nF | 10nF 50V | GCJ | 10nF/50V/X7R | Ceramic, 10nF, ±10%, 50V, X7R, –55 to 125°C, 0603 (1608),RoHS, Automotive | gen_C_ceramic_10n_X7R_0603 | 10nF 0603 ±10% 50V X7R
30 | C22 | GCJ188R71H102KA01 | R7 | 18 | 8 | 0.8mm | 0603 | 1608 | –55 to 125°C | 50V | ±10% | 10n | 10nF | 10nF 50V | GCJ | 10nF/50V/X7R | Ceramic, 10nF, ±10%, 50V, X7R, –55 to 125°C, 0603 (1608),RoHS, Automotive | gen_C_ceramic_10n_X7R_0603 | 10nF 0603 ±10% 50V X7R
31 | C24 | GCJ188R71H102KA01 | R7 | 18 | 8 | 0.8mm | 0603 | 1608 | –55 to 125°C | 50V | ±10% | 10n | 10nF | 10nF 50V | GCJ | 10nF/50V/X7R | Ceramic, 10nF, ±10%, 50V, X7R, –55 to 125°C, 0603 (1608),RoHS, Automotive | gen_C_ceramic_10n_X7R_0603 | 10nF 0603 ±10% 50V X7R
32 | C2 | GCJ188R71H104KA12 | R7 | 18 | 8 | 0.8mm | 0603 | 1608 | –55 to 125°C | 50V | ±10% | 100n | 100nF | 100nF 50V | GCJ | 100nF/50V/X7R | Ceramic, 100nF, ±10%, 50V, X7R, –55 to 125°C, 0603 (1608),RoHS, Automotive | gen_C_ceramic_100n_X7R_0603 | 100nF 0603 ±10% 50V X7R
33 | C38 | GCJ188R71H104KA12 | R7 | 18 | 8 | 0.8mm | 0603 | 1608 | –55 to 125°C | 50V | ±10% | 100n | 100nF | 100nF 50V | GCJ | 100nF/50V/X7R | Ceramic, 100nF, ±10%, 50V, X7R, –55 to 125°C, 0603 (1608),RoHS, Automotive | gen_C_ceramic_100n_X7R_0603 | 100nF 0603 ±10% 50V X7R
34 | C39 | GCJ188R71H104KA12 | R7 | 18 | 8 | 0.8mm | 0603 | 1608 | –55 to 125°C | 50V | ±10% | 100n | 100nF | 100nF 50V | GCJ | 100nF/50V/X7R | Ceramic, 100nF, ±10%, 50V, X7R, –55 to 125°C, 0603 (1608),RoHS, Automotive | gen_C_ceramic_100n_X7R_0603 | 100nF 0603 ±10% 50V X7R
35 | C6 | GCJ188R71H104KA12 | R7 | 18 | 8 | 0.8mm | 0603 | 1608 | –55 to 125°C | 50V | ±10% | 100n | 100nF | 100nF 50V | GCJ | 100nF/50V/X7R | Ceramic, 100nF, ±10%, 50V, X7R, –55 to 125°C, 0603 (1608),RoHS, Automotive | gen_C_ceramic_100n_X7R_0603 | 100nF 0603 ±10% 50V X7R
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
100 | C78 | GCM155R71H104KE02 | R7 | 15 | 5 | 0.5mm | 0402 | 1005 | –55 to 125°C | 50V | ±10% | 100n | 100nF | 100nF 50V | GCM | 100nF/50V/X7R | Ceramic, 100nF, ±10%, 50V, X7R, –55 to 125°C, 0402 (1005),RoHS, Automotive | gen_C_ceramic_100n_X7R_0402 | 100nF 0402 ±10% 50V X7R
101 | C84 | GCM155R71H104KE02 | R7 | 15 | 5 | 0.5mm | 0402 | 1005 | –55 to 125°C | 50V | ±10% | 100n | 100nF | 100nF 50V | GCM | 100nF/50V/X7R | Ceramic, 100nF, ±10%, 50V, X7R, –55 to 125°C, 0402 (1005),RoHS, Automotive | gen_C_ceramic_100n_X7R_0402 | 100nF 0402 ±10% 50V X7R
102 | C85 | GCM155R71H104KE02 | R7 | 15 | 5 | 0.5mm | 0402 | 1005 | –55 to 125°C | 50V | ±10% | 100n | 100nF | 100nF 50V | GCM | 100nF/50V/X7R | Ceramic, 100nF, ±10%, 50V, X7R, –55 to 125°C, 0402 (1005),RoHS, Automotive | gen_C_ceramic_100n_X7R_0402 | 100nF 0402 ±10% 50V X7R
103 | C86 | GCM155R71H104KE02 | R7 | 15 | 5 | 0.5mm | 0402 | 1005 | –55 to 125°C | 50V | ±10% | 100n | 100nF | 100nF 50V | GCM | 100nF/50V/X7R | Ceramic, 100nF, ±10%, 50V, X7R, –55 to 125°C, 0402 (1005),RoHS, Automotive | gen_C_ceramic_100n_X7R_0402 | 100nF 0402 ±10% 50V X7R
104 | C87 | GCM155R71H104KE02 | R7 | 15 | 5 | 0.5mm | 0402 | 1005 | –55 to 125°C | 50V | ±10% | 100n | 100nF | 100nF 50V | GCM | 100nF/50V/X7R | Ceramic, 100nF, ±10%, 50V, X7R, –55 to 125°C, 0402 (1005),RoHS, Automotive | gen_C_ceramic_100n_X7R_0402 | 100nF 0402 ±10% 50V X7R
105 | C59 | GCM1555C1H180JA16# | 5C | 15 | 5 | 0.5mm | 0402 | 1005 | 25 to 125°C | 50V | ±5% | 18p | 18pF | 18pF 50V | GCM | 18pF/50V/X7R | Ceramic, 18pF, ±5%, 50V, X7R, 25 to 125°C, 0402 (1005),RoHS, Automotive | gen_C_ceramic_18p_X7R_0402 | 18pF 0402 ±5% 50V C0G
106 | C61 | GCM1555C1H180JA16# | 5C | 15 | 5 | 0.5mm | 0402 | 1005 | 25 to 125°C | 50V | ±5% | 18p | 18pF | 18pF 50V | GCM | 18pF/50V/X7R | Ceramic, 18pF, ±5%, 50V, X7R, 25 to 125°C, 0402 (1005),RoHS, Automotive | gen_C_ceramic_18p_X7R_0402 | 18pF 0402 ±5% 50V C0G
107 | C67 | GCM1555C1H180JA16# | 5C | 15 | 5 | 0.5mm | 0402 | 1005 | 25 to 125°C | 50V | ±5% | 18p | 18pF | 18pF 50V | GCM | 18pF/50V/X7R | Ceramic, 18pF, ±5%, 50V, X7R, 25 to 125°C, 0402 (1005),RoHS, Automotive | gen_C_ceramic_18p_X7R_0402 | 18pF 0402 ±5% 50V C0G
108 | C70 | GCM1555C1H180JA16# | 5C | 15 | 5 | 0.5mm | 0402 | 1005 | 25 to 125°C | 50V | ±5% | 18p | 18pF | 18pF 50V | GCM | 18pF/50V/X7R | Ceramic, 18pF, ±5%, 50V, X7R, 25 to 125°C, 0402 (1005),RoHS, Automotive | gen_C_ceramic_18p_X7R_0402 | 18pF 0402 ±5% 50V C0G
109 | C30 | GCM1555C1H180JA16# | 5C | 15 | 5 | 0.5mm | 0402 | 1005 | 25 to 125°C | 50V | ±5% | 18p | 18pF | 18pF 50V | GCM | 18pF/50V/X7R | Ceramic, 18pF, ±5%, 50V, X7R, 25 to 125°C, 0402 (1005),RoHS, Automotive | gen_C_ceramic_18p_X7R_0402 | 18pF 0402 ±5% 50V C0G
110 | C33 | GCM1555C1H180JA16# | 5C | 15 | 5 | 0.5mm | 0402 | 1005 | 25 to 125°C | 50V | ±5% | 18p | 18pF | 18pF 50V | GCM | 18pF/50V/X7R | Ceramic, 18pF, ±5%, 50V, X7R, 25 to 125°C, 0402 (1005),RoHS, Automotive | gen_C_ceramic_18p_X7R_0402 | 18pF 0402 ±5% 50V C0G
111 | C107 | GCM1885C2A680JA16 | 5C | 18 | 8 | 0.8mm | 0603 | 1608 | 25 to 125°C | 100V | ±5% | 68p | 68pF | 68pF 100V | GCM | 68pF/100V/X7R | Ceramic, 68pF, ±5%, 100V, X7R, 25 to 125°C, 0603 (1608),RoHS, Automotive | gen_C_ceramic_68p_X7R_0603 | 68pF 0603 ±5% 50V C0G
112 | C97 | GCM1885C2A680JA16 | 5C | 18 | 8 | 0.8mm | 0603 | 1608 | 25 to 125°C | 100V | ±5% | 68p | 68pF | 68pF 100V | GCM | 68pF/100V/X7R | Ceramic, 68pF, ±5%, 100V, X7R, 25 to 125°C, 0603 (1608),RoHS, Automotive | gen_C_ceramic_68p_X7R_0603 | 68pF 0603 ±5% 50V C0G
#N/A | C118 | GCJ31CR72A105KA01 | R7 | 31 | C | 1.6mm | 1206 | 3216 | –55 to 125°C | 100V | ±10% | 1u | 1.0µF | 1.0µF 100V | GCJ | 1.0µF/100V/X7R | Chip Capacitor, 1 uF, +/- 10%, 100 V, -55 to 125 degC, 1206 (3216 Metric), RoHS, Tape and Reel | gen_C_ceramic_1u_X7R_1206
#N/A | C121 | GCJ31CR72A105KA01 | R7 | 31 | C | 1.6mm | 1206 | 3216 | –55 to 125°C | 100V | ±10% | 1u | 1.0µF | 1.0µF 100V | GCJ | 1.0µF/100V/X7R | Chip Capacitor, 1 uF, +/- 10%, 100 V, -55 to 125 degC, 1206 (3216 Metric), RoHS, Tape and Reel | gen_C_ceramic_1u_X7R_1206
#N/A | C123 | GCJ31CR72A105KA01 | R7 | 31 | C | 1.6mm | 1206 | 3216 | –55 to 125°C | 100V | ±10% | 1u | 1.0µF | 1.0µF 100V | GCJ | 1.0µF/100V/X7R | Chip Capacitor, 1 uF, +/- 10%, 100 V, -55 to 125 degC, 1206 (3216 Metric), RoHS, Tape and Reel | gen_C_ceramic_1u_X7R_1206
#N/A | C124 | GCJ31CR72A105KA01 | R7 | 31 | C | 1.6mm | 1206 | 3216 | –55 to 125°C | 100V | ±10% | 1u | 1.0µF | 1.0µF 100V | GCJ | 1.0µF/100V/X7R | Chip Capacitor, 1 uF, +/- 10%, 100 V, -55 to 125 degC, 1206 (3216 Metric), RoHS, Tape and Reel | gen_C_ceramic_1u_X7R_1206
#N/A | C113 | GCM32ER71E106KA57 | R7 | 32 | E | 2.5mm | 1210 | 3235 | –55 to 125°C | 25V | ±10% | 10u | 10µF | 10µF 25V | GCM | 10µF/25V/X7R | Multilayer Ceramic Capacitor, 50 V, -55 to 125 degC, 2-Pin SMD (1210), RoHS, Tape and Reel | gen_C_ceramic_10u_X7R_1210
#N/A | C15 | GCM32ER71E106KA57 | R7 | 32 | E | 2.5mm | 1210 | 3235 | –55 to 125°C | 25V | ±10% | 10u | 10µF | 10µF 25V | GCM | 10µF/25V/X7R | Multilayer Ceramic Capacitor, 50 V, -55 to 125 degC, 2-Pin SMD (1210), RoHS, Tape and Reel | gen_C_ceramic_10u_X7R_1210
#N/A | C17 | GCM32ER71E106KA57 | R7 | 32 | E | 2.5mm | 1210 | 3235 | –55 to 125°C | 25V | ±10% | 10u | 10µF | 10µF 25V | GCM | 10µF/25V/X7R | Multilayer Ceramic Capacitor, 50 V, -55 to 125 degC, 2-Pin SMD (1210), RoHS, Tape and Reel | gen_C_ceramic_10u_X7R_1210
#N/A | C18 | GCM32ER71E106KA57 | R7 | 32 | E | 2.5mm | 1210 | 3235 | –55 to 125°C | 25V | ±10% | 10u | 10µF | 10µF 25V | GCM | 10µF/25V/X7R | Multilayer Ceramic Capacitor, 50 V, -55 to 125 degC, 2-Pin SMD (1210), RoHS, Tape and Reel | gen_C_ceramic_10u_X7R_1210

Sheet: Sheet4
Order | Part No | XX | pnp val | sdl | asdasd | Series | Supplier 1 | Supplier 2 | Supplier Part 1 | Supplier Part 2 | Supplier Part 3
1 |  | * | * | * | * | * | Avnet |  | KW-5R5C334H-R
2 | GCJ21BR71C475KA01 | * | C_0805_10 | 4.7µF/16V/X7R | 16V | GCJ | Digi-Key |  | 490-10557-1-ND |  | 490-10557-1-ND
3 | GCJ188R71H104KA12 | x | C_0603_10 | 100nF/50V/X7R | 50V | GCJ | Digi-Key |  | 490-5798-1-ND |  | 490-5798-1-ND
4 | GCJ188R71H104KA12 | x | C_0603_10 | 100nF/50V/X7R | 50V | GCJ | Digi-Key |  | 490-5798-1-ND |  | 490-5798-1-ND
5 | GCJ188R71H104KA12 | x | C_0603_10 | 100nF/50V/X7R | 50V | GCJ | Digi-Key |  | 490-5798-1-ND |  | 490-5798-1-ND
6 | GCJ188R71H104KA12 | x | C_0603_10 | 100nF/50V/X7R | 50V | GCJ | Digi-Key |  | 490-5798-1-ND |  | 490-5798-1-ND
7 | GCJ188R71H104KA12 | x | C_0603_10 | 100nF/50V/X7R | 50V | GCJ | Digi-Key |  | 490-5798-1-ND |  | 490-5798-1-ND
8 | GCJ188R71H104KA12 | x | C_0603_10 | 100nF/50V/X7R | 50V | GCJ | Digi-Key |  | 490-5798-1-ND |  | 490-5798-1-ND
9 | GCJ21BR71E225KA01 | * | C_0805_10 | 2.2µF/25V/X7R | 25V | GCJ |  |  |  |  | 0
10 | GCM155R71H104KE02 | x | C_0402_10 | 100nF/50V/X7R | 50V | GCM | Digi-Key |  | 490-10672-1-ND |  | 490-10672-1-ND
11 | GCJ188R71H104KA12 | x | C_0603_10 | 100nF/50V/X7R | 50V | GCJ | Digi-Key |  | 490-5798-1-ND |  | 490-5798-1-ND
12 | GCM155R71H104KE02 | x | C_0402_10 | 100nF/50V/X7R | 50V | GCM | Digi-Key |  | 490-10672-1-ND |  | 490-10672-1-ND
13 | GCJ21BR71E225KA01 | * | C_0805_10 | 2.2µF/25V/X7R | 25V | GCJ |  |  |  |  | 0
14 | GCJ21BR71A106KE01 | * | C_0805_10 | 10µF/10V/X7R | 10V | GCJ | Digi-Key |  | 490-12646-1-ND |  | 490-12646-1-ND
15 |  | * | C_1210_10 | 10µF/25V/X7R | 25V | GCM
16 | GCJ21BR71A106KE01 | * | C_0805_10 | 10µF/10V/X7R | 10V | GCJ | Digi-Key |  | 490-12646-1-ND |  | 490-12646-1-ND
17 |  | * | C_1210_10 | 10µF/25V/X7R | 25V | GCM
18 |  | * | C_1210_10 | 10µF/25V/X7R | 25V | GCM
19 | GCJ188R71E105KA01 | * | C_0603_10 | 1.0µF/25V/X7R | 25V | GCJ | Digi-Key |  | 490-14409-1-ND |  | 490-14409-1-ND
20 | GCM155R71H104KE02 | x | C_0402_10 | 100nF/50V/X7R | 50V | GCM | Digi-Key |  | 490-10672-1-ND |  | 490-10672-1-ND
21 | GCM155R71H104KE02 | x | C_0402_10 | 100nF/50V/X7R | 50V | GCM | Digi-Key |  | 490-10672-1-ND |  | 490-10672-1-ND
22 | GCJ188R71H102KA01 | * | C_0603_10 | 10nF/50V/X7R | 50V | GCJ | Digi-Key |  | 490-5768-1-ND |  | 490-5768-1-ND
23 | GCJ188R71H104KA12 | x | C_0603_10 | 100nF/50V/X7R | 50V | GCJ | Digi-Key |  | 490-5798-1-ND |  | 490-5798-1-ND
24 | GCJ188R71H102KA01 | * | C_0603_10 | 10nF/50V/X7R | 50V | GCJ | Digi-Key |  | 490-5768-1-ND |  | 490-5768-1-ND
25 | GCM155R71H104KE02 | x | C_0402_10 | 100nF/50V/X7R | 50V | GCM | Digi-Key |  | 490-10672-1-ND |  | 490-10672-1-ND
26 | GCM155R71H104KE02 | x | C_0402_10 | 100nF/50V/X7R | 50V | GCM | Digi-Key |  | 490-10672-1-ND |  | 490-10672-1-ND
27 | GCM155R71H104KE02 | x | C_0402_10 | 100nF/50V/X7R | 50V | GCM | Digi-Key |  | 490-10672-1-ND |  | 490-10672-1-ND
28 | GCJ188R71E105KA01 | x | C_0603_10 | 1.0µF/25V/X7R | 25V | GCJ | Digi-Key |  | 490-14409-1-ND |  | 490-14409-1-ND
29 | GCJ188R71H104KA12 | x | C_0603_10 | 100nF/50V/X7R | 50V | GCJ | Digi-Key |  | 490-5798-1-ND |  | 490-5798-1-ND
30 | GCM1555C1H180JA16# | * | C_0402_10 | 18pF/50V/X7R | 50V | GCM | Digi-Key |  | 490-12650-1-ND |  | 490-12650-1-ND
31 | GCJ21BR71C475KA01 | * | C_0805_10 | 4.7µF/16V/X7R | 16V | GCJ | Digi-Key |  | 490-10557-1-ND |  | 490-10557-1-ND
32 | GCM155R71H104KE02 | x | C_0402_10 | 100nF/50V/X7R | 50V | GCM | Digi-Key |  | 490-10672-1-ND |  | 490-10672-1-ND
33 | GCM1555C1H180JA16# | * | C_0402_10 | 18pF/50V/X7R | 50V | GCM | Digi-Key |  | 490-12650-1-ND |  | 490-12650-1-ND
34 | GCJ188R71E105KA01 | x | C_0603_10 | 1.0µF/25V/X7R | 25V | GCJ | Digi-Key |  | 490-14409-1-ND |  | 490-14409-1-ND
35 | GCJ188R71H104KA12 | x | C_0603_10 | 100nF/50V/X7R | 50V | GCJ | Digi-Key |  | 490-5798-1-ND |  | 490-5798-1-ND
36 | GCJ21BR71E225KA01 | * | C_0805_10 | 2.2µF/25V/X7R | 25V | GCJ |  |  |  |  | 0
37 | GCJ188R71H104KA12 | x | C_0603_10 | 100nF/50V/X7R | 50V | GCJ | Digi-Key |  | 490-5798-1-ND |  | 490-5798-1-ND
38 | GCJ188R71H104KA12 | x | C_0603_10 | 100nF/50V/X7R | 50V | GCJ | Digi-Key |  | 490-5798-1-ND |  | 490-5798-1-ND
39 | GCJ188R71H104KA12 | x | C_0603_10 | 100nF/50V/X7R | 50V | GCJ | Digi-Key |  | 490-5798-1-ND |  | 490-5798-1-ND
40 | GCJ188R71H104KA12 | x | C_0603_10 | 100nF/50V/X7R | 50V | GCJ | Digi-Key |  | 490-5798-1-ND |  | 490-5798-1-ND
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
76 | GCJ188R71H104KA12 | x | C_0603_10 | 100nF/50V/X7R | 50V | GCJ | Digi-Key |  | 490-5798-1-ND |  | 490-5798-1-ND
77 | GCJ188R71E105KA01 | x | C_0603_10 | 1.0µF/25V/X7R | 25V | GCJ | Digi-Key |  | 490-14409-1-ND |  | 490-14409-1-ND
78 | GCJ188R71H104KA12 | x | C_0603_10 | 100nF/50V/X7R | 50V | GCJ | Digi-Key |  | 490-5798-1-ND |  | 490-5798-1-ND
79 | GCM155R71H104KE02 | x | C_0402_10 | 100nF/50V/X7R | 50V | GCM | Digi-Key |  | 490-10672-1-ND |  | 490-10672-1-ND
80 | GCM155R71H104KE02 | x | C_0402_10 | 100nF/50V/X7R | 50V | GCM | Digi-Key |  | 490-10672-1-ND |  | 490-10672-1-ND
81 | GCM155R71H104KE02 | x | C_0402_10 | 100nF/50V/X7R | 50V | GCM | Digi-Key |  | 490-10672-1-ND |  | 490-10672-1-ND
82 | GCM155R71H104KE02 | x | C_0402_10 | 100nF/50V/X7R | 50V | GCM | Digi-Key |  | 490-10672-1-ND |  | 490-10672-1-ND
83 | GCJ21BR71E225KA01 | * | C_0805_10 | 2.2µF/25V/X7R | 25V | GCJ |  |  |  |  | 0
84 | GCJ188R71H102KA01 | * | C_0603_10 | 10nF/50V/X7R | 50V | GCJ | Digi-Key |  | 490-5768-1-ND |  | 490-5768-1-ND
85 | GCJ21BR71A106KE01 | * | C_0805_10 | 10µF/10V/X7R | 10V | GCJ | Digi-Key |  | 490-12646-1-ND |  | 490-12646-1-ND
86 | GCJ21BR71A106KE01 | * | C_0805_10 | 10µF/10V/X7R | 10V | GCJ | Digi-Key |  | 490-12646-1-ND |  | 490-12646-1-ND
87 | GCJ188R71E105KA01 | x | C_0603_10 | 1.0µF/25V/X7R | 25V | GCJ | Digi-Key |  | 490-14409-1-ND |  | 490-14409-1-ND
88 | GCJ188R71H104KA12 | x | C_0603_10 | 100nF/50V/X7R | 50V | GCJ | Digi-Key |  | 490-5798-1-ND |  | 490-5798-1-ND
89 | GCJ188R71H104KA12 | x | C_0603_10 | 100nF/50V/X7R | 50V | GCJ | Digi-Key |  | 490-5798-1-ND |  | 490-5798-1-ND
90 | GCJ188R71E105KA01 | x | C_0603_10 | 1.0µF/25V/X7R | 25V | GCJ | Digi-Key |  | 490-14409-1-ND |  | 490-14409-1-ND
91 | GCJ188R71H104KA12 | x | C_0603_10 | 100nF/50V/X7R | 50V | GCJ | Digi-Key |  | 490-5798-1-ND |  | 490-5798-1-ND
92 | GCM1885C2A680JA16 | * | C_0603_05 | 68pF/100V/X7R | 100V | GCM | Digi-Key |  | 490-4945-1-ND |  | 490-4945-1-ND
93 | GCJ188R71H104KA12 | x | C_0603_10 | 100nF/50V/X7R | 50V | GCJ | Digi-Key |  | 490-5798-1-ND |  | 490-5798-1-ND
94 | GCJ188R71E105KA01 | x | C_0603_10 | 1.0µF/25V/X7R | 25V | GCJ | Digi-Key |  | 490-14409-1-ND |  | 490-14409-1-ND
95 | GCJ188R71H104KA12 | x | C_0603_10 | 100nF/50V/X7R | 50V | GCJ | Digi-Key |  | 490-5798-1-ND |  | 490-5798-1-ND
96 | GCJ188R71H104KA12 | x | C_0603_10 | 100nF/50V/X7R | 50V | GCJ | Digi-Key |  | 490-5798-1-ND |  | 490-5798-1-ND
97 | GCJ188R71H104KA12 | * | C_0603_10 | 100nF/50V/X7R | 50V | GCJ | Digi-Key |  | 490-5798-1-ND |  | 490-5798-1-ND
98 | GCJ188R71H102KA01 | * | C_0603_10 | 10nF/50V/X7R | 50V | GCJ | Digi-Key |  | 490-5768-1-ND |  | 490-5768-1-ND
99 | GCJ188R71H104KA12 | x | C_0603_10 | 100nF/50V/X7R | 50V | GCJ | Digi-Key |  | 490-5798-1-ND |  | 490-5798-1-ND
100 | GCJ188R71H104KA12 | x | C_0603_10 | 100nF/50V/X7R | 50V | GCJ | Digi-Key |  | 490-5798-1-ND |  | 490-5798-1-ND
101 | GRT1885C1H472JA02 | * | C_0603_05 | * | 50V | * | Digi-Key
102 | GCM1885C2A680JA16 | * | C_0603_05 | 68pF/100V/X7R | 100V | GCM | Digi-Key |  | 490-4945-1-ND |  | 490-4945-1-ND
103 | GCJ188R71H104KA12 | * | C_0603_10 | 100nF/50V/X7R | 50V | GCJ | Digi-Key |  | 490-5798-1-ND |  | 490-5798-1-ND
104 | GCJ188R71H104KA12 | x | C_0603_10 | 100nF/50V/X7R | 50V | GCJ | Digi-Key |  | 490-5798-1-ND |  | 490-5798-1-ND
105 | GCJ21BR71A106KE01 | * | C_0805_10 | 10µF/10V/X7R | 10V | GCJ | Digi-Key |  | 490-12646-1-ND |  | 490-12646-1-ND
106 | GCJ188R71H102KA01 | * | C_0603_10 | 10nF/50V/X7R | 50V | GCJ | Digi-Key |  | 490-5768-1-ND |  | 490-5768-1-ND
107 |  | * | C_1210_10 | 10µF/25V/X7R | 25V | GCM
108 | UCL1C102MNL1GS | * | * | * | 16 V | *
109 | GCJ188R71H102KA01 | * | C_0603_10 | 10nF/50V/X7R | 50V | GCJ | Digi-Key |  | 490-5768-1-ND |  | 490-5768-1-ND
110 | GCJ188R71E105KA01 | * | C_0603_10 | 1.0µF/25V/X7R | 25V | GCJ | Digi-Key |  | 490-14409-1-ND |  | 490-14409-1-ND
111 | GCJ21BR71A106KE01 | * | C_0805_10 | 10µF/10V/X7R | 10V | GCJ | Digi-Key |  | 490-12646-1-ND |  | 490-12646-1-ND
112 |  | * | C_1206_10 | 1.0µF/100V/X7R | 100V | GCJ
113 | GCJ188R71H104KA12 | x | C_0603_10 | 100nF/50V/X7R | 50V | GCJ | Digi-Key |  | 490-5798-1-ND |  | 490-5798-1-ND
114 | GCJ188R71H104KA12 | x | C_0603_10 | 100nF/50V/X7R | 50V | GCJ | Digi-Key |  | 490-5798-1-ND |  | 490-5798-1-ND
115 |  | * | C_1206_10 | 1.0µF/100V/X7R | 100V | GCJ
116 | GRT155R71H104KE01 | * | C_0402_10 | 10n/50V/X7R | 50V | *
117 |  | * | C_1206_10 | 1.0µF/100V/X7R | 100V | GCJ
118 |  | * | C_1206_10 | 1.0µF/100V/X7R | 100V | GCJ
119 | GCJ188R71H104KA12 | x | C_0603_10 | 100nF/50V/X7R | 50V | GCJ | Digi-Key |  | 490-5798-1-ND |  | 490-5798-1-ND
120 | GCJ188R71H104KA12 | x | C_0603_10 | 100nF/50V/X7R | 50V | GCJ | Digi-Key |  | 490-5798-1-ND |  | 490-5798-1-ND
121 | GCJ188R71H104KA12 | x | C_0603_10 | 100nF/50V/X7R | 50V | GCJ | Digi-Key |  | 490-5798-1-ND |  | 490-5798-1-ND
122 | GCJ188R71H104KA12 | x | C_0603_10 | 100nF/50V/X7R | 50V | GCJ | Digi-Key |  | 490-5798-1-ND |  | 490-5798-1-ND
123 | GCJ188R71H104KA12 | x | C_0603_10 | 100nF/50V/X7R | 50V | GCJ | Digi-Key |  | 490-5798-1-ND |  | 490-5798-1-ND
124 | GCJ188R71H104KA12 | x | C_0603_10 | 100nF/50V/X7R | 50V | GCJ | Digi-Key |  | 490-5798-1-ND |  | 490-5798-1-ND

Sheet: Sheet5
0603R | 100k | Resistor | SMD Resistor 100k 0603 | gen_R_100k_0603
0603R | 100k | Resistor | SMD Resistor 100k 0603 | gen_R_100k_0603
0603R | 10k | SMD Resistor 10k 0603 | SMD Resistor 10k 0603 | gen_R_10k_0603
0805R | 59R | SMD Resistor 62R 0603 | SMD Resistor 59R 0805 | gen_R_59R_0805
0805R | 0.01R | Resistor | SMD Resistor 0.01R 0805 | gen_R_0.01R_0805
0805R | 59R | SMD Resistor 62R 0603 | SMD Resistor 59R 0805 | gen_R_59R_0805
0603R | 100k | Resistor | SMD Resistor 100k 0603 | gen_R_100k_0603
0603R | 0R | SMD Resistor 430R 0603 | SMD Resistor 0R 0603 | gen_R_0R_0603
0603R | 4k7 | Resistor | SMD Resistor 4k7 0603 | gen_R_4k7_0603
0603R | 4k7 | Resistor | SMD Resistor 4k7 0603 | gen_R_4k7_0603
0603R | 10k | Resistor | SMD Resistor 10k 0603 | gen_R_10k_0603
0603R | NF | Resistor | SMD Resistor NF 0603 | gen_R_NF_0603
0603R | 10Meg | Resistor | SMD Resistor 10Meg 0603 | gen_R_10Meg_0603
0402R | 10k7 | Resistor | SMD Resistor 10k7 0402 | gen_R_10k7_0402
0402R | 100k | Resistor | SMD Resistor 100k 0402 | gen_R_100k_0402
0402R | 26k1 | Resistor | SMD Resistor 26k1 0402 | gen_R_26k1_0402
0402R | 0R | Resistor | SMD Resistor 0R 0402 | gen_R_0R_0402
0402R | 374k |  | SMD Resistor 374k 0402 | gen_R_374k_0402
0402R | 49k9 |  | SMD Resistor 49k9 0402 | gen_R_49k9_0402
 |  |  | 100n | 603 | 1608 | X7R | gen_C_ceramic_100n_X7R_0603
 |  |  | 10n | 603 | 1608 | X7R | gen_C_ceramic_10n_X7R_0603
 |  |  | 100n | 603 | 1608 | X7R | gen_C_ceramic_100n_X7R_0603
 |  |  | 10n | 603 | 1608 | X7R | gen_C_ceramic_10n_X7R_0603
 |  |  | 10u | 805 | 2012 | X7R | gen_C_ceramic_10u_X7R_0805
 |  |  | 10n | 603 | 1608 | X7R | gen_C_ceramic_10n_X7R_0603
 |  |  | 10n | 603 | 1608 | X7R | gen_C_ceramic_10n_X7R_0603
 |  |  | 1u | 603 | 1608 | X7R | gen_C_ceramic_1u_X7R_0603
 |  |  | 10u | 805 | 2012 | X7R | gen_C_ceramic_10u_X7R_0805
 |  |  | 10n | 402 | 1005 | X7R | gen_C_ceramic_10n_X7R_0402
 |  |  | 10u | 805 | 2012 | X7R | gen_C_ceramic_10u_X7R_0805
 |  |  | 10u | 805 | 2012 | X7R | gen_C_ceramic_10u_X7R_0805
 |  |  | 1u | 603 | 1608 | X7R | gen_C_ceramic_1u_X7R_0603
 |  |  | 10n | 603 | 1608 | X7R | gen_C_ceramic_10n_X7R_0603
 |  |  | 10n | 603 | 1608 | X7R | gen_C_ceramic_10n_X7R_0603

Sheet: Sheet6
 |  |  | Lib Name
Ceramic, 1.0µF, ±10%, 25V, X7R, –55 to 125°C, 0603 (1608),RoHS, Automotive | 0603C | master-010106.SCHLIB | gen_C_ceramic_1u_25V_X7R_0603 | 0603 | 0603 | TRUE
Ceramic, 1.0µF, ±10%, 25V, X7R, –55 to 125°C, 0603 (1608),RoHS, Automotive | 0603C | master-010106.SCHLIB | gen_C_ceramic_1u_25V_X7R_0603 | 0603 | 0603 | TRUE
Ceramic, 1.0µF, ±10%, 25V, X7R, –55 to 125°C, 0603 (1608),RoHS, Automotive | 0603C | master-010106.SCHLIB | gen_C_ceramic_1u_25V_X7R_0603 | 0603 | 0603 | TRUE
Ceramic, 1.0µF, ±10%, 25V, X7R, –55 to 125°C, 0603 (1608),RoHS, Automotive | 0603C | master-010106.SCHLIB | gen_C_ceramic_1u_25V_X7R_0603 | 0603 | 0603 | TRUE
Ceramic, 1.0µF, ±10%, 25V, X7R, –55 to 125°C, 0603 (1608),RoHS, Automotive | 0603C | master-010106.SCHLIB | gen_C_ceramic_1u_25V_X7R_0603 | 0603 | 0603 | TRUE
Ceramic, 1.0µF, ±10%, 25V, X7R, –55 to 125°C, 0603 (1608),RoHS, Automotive | 0603C | master-010106.SCHLIB | gen_C_ceramic_1u_25V_X7R_0603 | 0603 | 0603 | TRUE
Ceramic, 1.0µF, ±10%, 25V, X7R, –55 to 125°C, 0603 (1608),RoHS, Automotive | 0603C | master-010106.SCHLIB | gen_C_ceramic_1u_25V_X7R_0603 | 0603 | 0603 | TRUE
Ceramic, 1.0µF, ±10%, 25V, X7R, –55 to 125°C, 0603 (1608),RoHS, Automotive | 0603C | master-010106.SCHLIB | gen_C_ceramic_1u_25V_X7R_0603 | 0603 | 0603 | TRUE
Ceramic, 1.0µF, ±10%, 25V, X7R, –55 to 125°C, 0603 (1608),RoHS, Automotive | 0603C | master-010106.SCHLIB | gen_C_ceramic_1u_25V_X7R_0603 | 0603 | 0603 | TRUE
Ceramic, 1.0µF, ±10%, 25V, X7R, –55 to 125°C, 0603 (1608),RoHS, Automotive | 0603C | master-010106.SCHLIB | gen_C_ceramic_1u_25V_X7R_0603 | 0603 | 0603 | TRUE
Ceramic, 1.0µF, ±10%, 25V, X7R, –55 to 125°C, 0603 (1608),RoHS, Automotive | 0603C | master-010106.SCHLIB | gen_C_ceramic_1u_25V_X7R_0603 | 0603 | 0603 | TRUE
Chip Capacitor, 1 uF, +/- 10%, 100 V, -55 to 125 degC, 1206 (3216 Metric), RoHS, Tape and Reel | CAPC3216X180X55ML20T25 | master-010106.SCHLIB | gen_C_ceramic_1u_100V_X7R_1206 | CAPC | 1206 | FALSE
Chip Capacitor, 1 uF, +/- 10%, 100 V, -55 to 125 degC, 1206 (3216 Metric), RoHS, Tape and Reel | CAPC3216X180X55ML20T25 | master-010106.SCHLIB | gen_C_ceramic_1u_100V_X7R_1206 | CAPC | 1206 | FALSE
Chip Capacitor, 1 uF, +/- 10%, 100 V, -55 to 125 degC, 1206 (3216 Metric), RoHS, Tape and Reel | CAPC3216X180X55ML20T25 | master-010106.SCHLIB | gen_C_ceramic_1u_100V_X7R_1206 | CAPC | 1206 | FALSE
Chip Capacitor, 1 uF, +/- 10%, 100 V, -55 to 125 degC, 1206 (3216 Metric), RoHS, Tape and Reel | CAPC3216X180X55ML20T25 | master-010106.SCHLIB | gen_C_ceramic_1u_100V_X7R_1206 | CAPC | 1206 | FALSE
Ceramic, 2.2µF, ±10%, 25V, X7R, –55 to 125°C, 0805 (2012),RoHS, Automotive | 0805C | master-010106.SCHLIB | gen_C_ceramic_2u2_10V_X5R_0603 | 0805 | 0603 | FALSE
Ceramic, 2.2µF, ±10%, 25V, X7R, –55 to 125°C, 0805 (2012),RoHS, Automotive | 0805C | master-010106.SCHLIB | gen_C_ceramic_2u2_10V_X5R_0603 | 0805 | 0603 | FALSE
Ceramic, 2.2µF, ±10%, 25V, X7R, –55 to 125°C, 0805 (2012),RoHS, Automotive | 0805C | master-010106.SCHLIB | gen_C_ceramic_2u2_10V_X5R_0603 | 0805 | 0603 | FALSE
Ceramic, 4.7µF, ±10%, 16V, X7R, –55 to 125°C, 0805 (2012),RoHS, Automotive | 0805C | master-010106.SCHLIB | gen_C_ceramic_2u2_10V_X5R_0603 | 0805 | 0603 | FALSE
Ceramic, 2.2µF, ±10%, 25V, X7R, –55 to 125°C, 0805 (2012),RoHS, Automotive | 0805C | master-010106.SCHLIB | gen_C_ceramic_2u2_10V_X5R_0603 | 0805 | 0603 | FALSE
Ceramic, 4.7µF, ±10%, 16V, X7R, –55 to 125°C, 0805 (2012),RoHS, Automotive | 0805C | master-010106.SCHLIB | gen_C_ceramic_2u2_10V_X5R_0603 | 0805 | 0603 | FALSE
Ceramic, 2.2µF, ±10%, 25V, X7R, –55 to 125°C, 0805 (2012),RoHS, Automotive | 0805C | master-010106.SCHLIB | gen_C_ceramic_2u2_50V_X7R_0805 | 0805 | 0805 | TRUE
Ceramic, 4700pF, 0603, ±5%, 50V, C0G | 0603C | master-010106.SCHLIB | gen_C_ceramic_4n7_50V_X7R_0603 | 0603 | 0603 | TRUE
Ceramic, 68pF, ±5%, 100V, X7R, 25 to 125°C, 0603 (1608),RoHS, Automotive | 0603C | master-010106.SCHLIB | gen_C_ceramic_4n7_50V_X7R_0603 | 0603 | 0603 | TRUE
Ceramic, 68pF, ±5%, 100V, X7R, 25 to 125°C, 0603 (1608),RoHS, Automotive | 0603C | master-010106.SCHLIB | gen_C_ceramic_4n7_50V_X7R_0603 | 0603 | 0603 | TRUE
Ceramic, 4.7µF, ±10%, 16V, X7R, –55 to 125°C, 0805 (2012),RoHS, Automotive | 0805C | master-010106.SCHLIB | gen_C_ceramic_4u7_25V_X5R_0603 | 0805 | 0603 | FALSE
Ceramic, 10nF, ±10%, 50V, X7R, –55 to 125°C, 0402 (1005),RoHS, Automotive | 0402C | master-010106.SCHLIB | gen_C_ceramic_10n_50V_X7R_0402 | 0402 | 0402 | TRUE
Ceramic, 10nF, ±10%, 50V, X7R, –55 to 125°C, 0603 (1608),RoHS, Automotive | 0603C | master-010106.SCHLIB | gen_C_ceramic_10n_50V_X7R_0603 | 0603 | 0603 | TRUE
Ceramic, 10nF, ±10%, 50V, X7R, –55 to 125°C, 0603 (1608),RoHS, Automotive | 0603C | master-010106.SCHLIB | gen_C_ceramic_10n_50V_X7R_0603 | 0603 | 0603 | TRUE
Ceramic, 10nF, ±10%, 50V, X7R, –55 to 125°C, 0603 (1608),RoHS, Automotive | 0603C | master-010106.SCHLIB | gen_C_ceramic_10n_50V_X7R_0603 | 0603 | 0603 | TRUE
Ceramic, 10nF, ±10%, 50V, X7R, –55 to 125°C, 0603 (1608),RoHS, Automotive | 0603C | master-010106.SCHLIB | gen_C_ceramic_10n_50V_X7R_0603 | 0603 | 0603 | TRUE
Ceramic, 10nF, ±10%, 50V, X7R, –55 to 125°C, 0603 (1608),RoHS, Automotive | 0603C | master-010106.SCHLIB | gen_C_ceramic_10n_50V_X7R_0603 | 0603 | 0603 | TRUE
Ceramic, 10nF, ±10%, 50V, X7R, –55 to 125°C, 0603 (1608),RoHS, Automotive | 0603C | master-010106.SCHLIB | gen_C_ceramic_10n_50V_X7R_0603 | 0603 | 0603 | TRUE
Ceramic, 10µF, ±10%, 10V, X7R, –55 to 125°C, 0805 (2012),RoHS, Automotive | 0805C | master-010106.SCHLIB | gen_C_ceramic_10u_10V_X7R_0805 | 0805 | 0805 | TRUE
Ceramic, 10µF, ±10%, 10V, X7R, –55 to 125°C, 0805 (2012),RoHS, Automotive | 0805C | master-010106.SCHLIB | gen_C_ceramic_10u_10V_X7R_0805 | 0805 | 0805 | TRUE
Ceramic, 10µF, ±10%, 10V, X7R, –55 to 125°C, 0805 (2012),RoHS, Automotive | 0805C | master-010106.SCHLIB | gen_C_ceramic_10u_10V_X7R_0805 | 0805 | 0805 | TRUE
Ceramic, 10µF, ±10%, 10V, X7R, –55 to 125°C, 0805 (2012),RoHS, Automotive | 0805C | master-010106.SCHLIB | gen_C_ceramic_10u_10V_X7R_0805 | 0805 | 0805 | TRUE
Ceramic, 10µF, ±10%, 10V, X7R, –55 to 125°C, 0805 (2012),RoHS, Automotive | 0805C | master-010106.SCHLIB | gen_C_ceramic_10u_10V_X7R_0805 | 0805 | 0805 | TRUE
Ceramic, 10µF, ±10%, 10V, X7R, –55 to 125°C, 0805 (2012),RoHS, Automotive | 0805C | master-010106.SCHLIB | gen_C_ceramic_10u_10V_X7R_0805 | 0805 | 0805 | TRUE
Multilayer Ceramic Capacitor, 50 V, -55 to 125 degC, 2-Pin SMD (1210), RoHS, Tape and Reel | CAPC3225X279X50LL20T25 | master-010106.SCHLIB | gen_C_ceramic_10u_25V_X7R_1210 | CAPC | 1210 | FALSE
Multilayer Ceramic Capacitor, 50 V, -55 to 125 degC, 2-Pin SMD (1210), RoHS, Tape and Reel | CAPC3225X279X50LL20T25 | master-010106.SCHLIB | gen_C_ceramic_10u_25V_X7R_1210 | CAPC | 1210 | FALSE
Multilayer Ceramic Capacitor, 50 V, -55 to 125 degC, 2-Pin SMD (1210), RoHS, Tape and Reel | CAPC3225X279X50LL20T25 | master-010106.SCHLIB | gen_C_ceramic_10u_25V_X7R_1210 | CAPC | 1210 | FALSE
Multilayer Ceramic Capacitor, 50 V, -55 to 125 degC, 2-Pin SMD (1210), RoHS, Tape and Reel | CAPC3225X279X50LL20T25 | master-010106.SCHLIB | gen_C_ceramic_10u_25V_X7R_1210 | CAPC | 1210 | FALSE
Ceramic, 18pF, ±5%, 50V, X7R, 25 to 125°C, 0402 (1005),RoHS, Automotive | 0402C | master-010106.SCHLIB | gen_C_ceramic_18p_50V_C0G_0603 | 0402 | 0603 | FALSE
Ceramic, 18pF, ±5%, 50V, X7R, 25 to 125°C, 0402 (1005),RoHS, Automotive | 0402C | master-010106.SCHLIB | gen_C_ceramic_18p_50V_C0G_0603 | 0402 | 0603 | FALSE
Ceramic, 18pF, ±5%, 50V, X7R, 25 to 125°C, 0402 (1005),RoHS, Automotive | 0402C | master-010106.SCHLIB | gen_C_ceramic_18p_50V_C0G_0603 | 0402 | 0603 | FALSE
Ceramic, 18pF, ±5%, 50V, X7R, 25 to 125°C, 0402 (1005),RoHS, Automotive | 0402C | master-010106.SCHLIB | gen_C_ceramic_18p_50V_C0G_0603 | 0402 | 0603 | FALSE
Ceramic, 18pF, ±5%, 50V, X7R, 25 to 125°C, 0402 (1005),RoHS, Automotive | 0402C | master-010106.SCHLIB | gen_C_ceramic_18p_50V_C0G_0603 | 0402 | 0603 | FALSE
Ceramic, 18pF, ±5%, 50V, X7R, 25 to 125°C, 0402 (1005),RoHS, Automotive | 0402C | master-010106.SCHLIB | gen_C_ceramic_18p_50V_C0G_0603 | 0402 | 0603 | FALSE
Ceramic, 100nF, ±10%, 50V, X7R, –55 to 125°C, 0402 (1005),RoHS, Automotive | 0402C | master-010106.SCHLIB | gen_C_ceramic_100n_50V_X7R_0402 | 0402 | 0402 | TRUE
Ceramic, 100nF, ±10%, 50V, X7R, –55 to 125°C, 0402 (1005),RoHS, Automotive | 0402C | master-010106.SCHLIB | gen_C_ceramic_100n_50V_X7R_0402 | 0402 | 0402 | TRUE
Ceramic, 100nF, ±10%, 50V, X7R, –55 to 125°C, 0402 (1005),RoHS, Automotive | 0402C | master-010106.SCHLIB | gen_C_ceramic_100n_50V_X7R_0402 | 0402 | 0402 | TRUE
Ceramic, 100nF, ±10%, 50V, X7R, –55 to 125°C, 0402 (1005),RoHS, Automotive | 0402C | master-010106.SCHLIB | gen_C_ceramic_100n_50V_X7R_0402 | 0402 | 0402 | TRUE
Ceramic, 100nF, ±10%, 50V, X7R, –55 to 125°C, 0402 (1005),RoHS, Automotive | 0402C | master-010106.SCHLIB | gen_C_ceramic_100n_50V_X7R_0402 | 0402 | 0402 | TRUE
Ceramic, 100nF, ±10%, 50V, X7R, –55 to 125°C, 0402 (1005),RoHS, Automotive | 0402C | master-010106.SCHLIB | gen_C_ceramic_100n_50V_X7R_0402 | 0402 | 0402 | TRUE
Ceramic, 100nF, ±10%, 50V, X7R, –55 to 125°C, 0402 (1005),RoHS, Automotive | 0402C | master-010106.SCHLIB | gen_C_ceramic_100n_50V_X7R_0402 | 0402 | 0402 | TRUE
Ceramic, 100nF, ±10%, 50V, X7R, –55 to 125°C, 0402 (1005),RoHS, Automotive | 0402C | master-010106.SCHLIB | gen_C_ceramic_100n_50V_X7R_0402 | 0402 | 0402 | TRUE
Ceramic, 100nF, ±10%, 50V, X7R, –55 to 125°C, 0402 (1005),RoHS, Automotive | 0402C | master-010106.SCHLIB | gen_C_ceramic_100n_50V_X7R_0402 | 0402 | 0402 | TRUE
Ceramic, 100nF, ±10%, 50V, X7R, –55 to 125°C, 0402 (1005),RoHS, Automotive | 0402C | master-010106.SCHLIB | gen_C_ceramic_100n_50V_X7R_0402 | 0402 | 0402 | TRUE
Ceramic, 100nF, ±10%, 50V, X7R, –55 to 125°C, 0402 (1005),RoHS, Automotive | 0402C | master-010106.SCHLIB | gen_C_ceramic_100n_50V_X7R_0402 | 0402 | 0402 | TRUE
Ceramic, 100nF, ±10%, 50V, X7R, –55 to 125°C, 0402 (1005),RoHS, Automotive | 0402C | master-010106.SCHLIB | gen_C_ceramic_100n_50V_X7R_0402 | 0402 | 0402 | TRUE
Ceramic, 100nF, ±10%, 50V, X7R, –55 to 125°C, 0402 (1005),RoHS, Automotive | 0402C | master-010106.SCHLIB | gen_C_ceramic_100n_50V_X7R_0402 | 0402 | 0402 | TRUE
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
SMD Resistor 680R 0603 | 0603R | master-010106.SCHLIB | gen_R_680R_0603 | 0603 | 0603 | TRUE
SMD Resistor 680R 0603 | 0603R | master-010106.SCHLIB | gen_R_680R_0603 | 0603 | 0603 | TRUE
SMD Resistor NF 0603 | 0603R | master-010106.SCHLIB | gen_R_NF_0603 | 0603 | 0603 | TRUE

Sheet: Sheet3
des | order
C90 | 1
C91 | 2
C111 | 3
C117 | 4
C14 | 5
C16 | 6
C1 | 7
C31 | 8
C48 | 9
C36 | 10
C60 | 11
C88 | 12
C12 | 13
C8 | 14
C92 | 15
C95 | 16
C56 | 17
C28 | 18
C34 | 19
C73 | 20
C75 | 21
C80 | 22
C99 | 23
C116 | 24
C19 | 25
C103 | 26
C89 | 27
C112 | 28
C115 | 29
C22 | 30
C24 | 31
C2 | 32
C38 | 33
C39 | 34
C6 | 35
C110 | 36
C93 | 37
C94 | 38
C1201 | 39
C1203 | 40
C1205 | 41
C1207 | 42
C1209 | 43
C1211 | 44
C40 | 45
C43 | 46
C45 | 47
C47 | 48
C57 | 49
C65 | 50
C42 | 51
C50 | 52
C51 | 53
C55 | 54
C46 | 55
C79 | 56
C83 | 57
C35 | 58
C10 | 59
C3 | 60
C4 | 61
C7 | 62
C41 | 63
C68 | 64
C29 | 65
C37 | 66
C23 | 67
C44 | 68
C102 | 69
C108 | 70
C96 | 71
C100 | 72
C101 | 73
C104 | 74
C105 | 75
C119 | 76
C120 | 77
C98 | 78
C5 | 79
C11 | 80
C20 | 81
C21 | 82
C25 | 83
C26 | 84
C27 | 85
C32 | 86
C9 | 87
C49 | 88
C52 | 89
C53 | 90
C54 | 91
C58 | 92
C62 | 93
C63 | 94
C64 | 95
C69 | 96
C74 | 97
C76 | 98
C77 | 99
C78 | 100
C84 | 101
C85 | 102
C86 | 103
C87 | 104
C59 | 105
C61 | 106
C67 | 107
C70 | 108
C30 | 109
C33 | 110
C107 | 111
C97 | 112

Sheet: Sheet2
Chip Dim | EIA | Metric | HeightDim | Dimension | 6Rated Voltage |  | 8Capacitance Tolerance
03 | 0201 | 0603 | 3 | 0.3mm | Code | Rated Voltage | Code | Tolerance
15 | 0402 | 1005 | 5 | 0.5mm | 0E | 2.5V | C | ±0.25pF
18 | 0603 | 1608 | 6 | 0.6mm | 0G | 4V | D | ±0.5pF (Less than 10pF) ±0.5% (10pF and over)
21 | 0805 | 2012 | 8 | 0.8mm | 0J | 6.3V | J | ±5%
31 | 1206 | 3216 | 9 | 0.85mm | 1A | 10V | K | ±10%
32 | 1210 | 3235 | A | 1.0mm | 1C | 16V | M | ±20%
43 | 1812 | 4532 | B | 1.25mm | 1E | 25V
55 | 2220 | 5750 | C | 1.6mm | YA | 35V
 |  |  | D | 2.0mm | 1H | 50V
 |  |  | E | 2.5mm | 1J | 63V
 |  |  | M | 1.15mm | 1K | 80V |  |  | PartNo | Supp | Part
 |  |  | Q | 1.5mm | 2A | 100V |  |  | GCJ21BR71A106KE01 | Digi-Key | 490-12646-1-ND | GCJ188R71E105KA01 | Digi-Key | 490-14409-1-ND
 |  |  | X |  | 2E | 250V |  |  | GCJ21BR71C475KA01 | Digi-Key | 490-10557-1-ND | GCJ188R71E105KA01 | Digi-Key | 490-14409-1-ND
 |  |  |  |  | 2W | 450V |  |  | GCJ21BR71E225KA01 |  |  | GCJ188R71E105KA01 | Digi-Key | 490-14409-1-ND
 |  |  |  |  | 2J | 630V |  |  | GCJ188R71E105KA01 | Digi-Key | 490-14409-1-ND | GCJ188R71E105KA01 | Digi-Key | 490-14409-1-ND
 |  |  |  |  | 3A | 1kV |  |  | GCJ188R71H102KA01 | Digi-Key | 490-5768-1-ND | GCJ188R71H104KA12 | Digi-Key | 490-5798-1-ND
 |  |  |  |  |  |  |  |  | GCM155R71H104KE02 | Digi-Key | 490-10672-1-ND | GCJ188R71H104KA12 | Digi-Key | 490-5798-1-ND
 |  |  |  |  |  |  |  |  | GCM1555C1H180JA16 | Digi-Key | 490-12650-1-ND | GCJ21BR71A106KE01 | Digi-Key | 490-12646-1-ND
 |  |  |  |  |  |  |  |  | GCM1885C2A680JA16 | Digi-Key | 490-4945-1-ND | GCJ188R71H102KA01 | Digi-Key | 490-5768-1-ND
 |  |  |  |  |  |  |  |  | GCJ31CR72A105KA01 | Digi-Key | 490-16468-1-ND | GCJ188R71H102KA01 | Digi-Key | 490-5768-1-ND
 |  |  |  |  |  |  |  |  | GCM32ER71E106KA57 | Digi-Key | 490-11170-1-ND | GCJ188R71E105KA01 | Digi-Key | 490-14409-1-ND
 |  |  |  |  |  |  |  |  | GCJ188R71H104KA12 |  | 490-5798-1-ND | GCJ21BR71A106KE01 | Digi-Key | 490-12646-1-ND
 |  |  |  |  |  |  |  |  | GCM1555C1H180JA16# |  | 490-12650-1-ND
 |  |  |  |  |  |  |  |  | GCM1885C2A680JA16 |  | 490-4945-1-ND

Sheet: Sheet7
C90 | 10µF 10V | Standard | Ceramic, 10µF, ±10%, 10V, X7R, –55 to 125°C, 0805 (2012),RoHS, Automotive | 0805C |  | master-010106.SCHLIB | gen_C_ceramic_10u_10V_X7R_0805
C91 | 10µF 10V | Standard | Ceramic, 10µF, ±10%, 10V, X7R, –55 to 125°C, 0805 (2012),RoHS, Automotive | 0805C |  | master-010106.SCHLIB | gen_C_ceramic_10u_10V_X7R_0805
C36 | 2.2µF 25V | Standard | Ceramic, 2.2µF, ±10%, 25V, X7R, –55 to 125°C, 0805 (2012),RoHS, Automotive | 0805C |  | master-010106.SCHLIB | gen_C_ceramic_2u2_50V_X7R_0805
C1 | 4.7µF 16V | Standard | Ceramic, 4.7µF, ±10%, 16V, X7R, –55 to 125°C, 0805 (2012),RoHS, Automotive | 0805C |  | master-010106.SCHLIB | gen_C_ceramic_4u7_16V_X7R_0805
C60 | 2.2µF 25V | Standard | Ceramic, 2.2µF, ±10%, 25V, X7R, –55 to 125°C, 0805 (2012),RoHS, Automotive | 0805C |  | master-010106.SCHLIB | gen_C_ceramic_2u2_50V_X7R_0805
C88 | 2.2µF 25V | Standard | Ceramic, 2.2µF, ±10%, 25V, X7R, –55 to 125°C, 0805 (2012),RoHS, Automotive | 0805C |  | master-010106.SCHLIB | gen_C_ceramic_2u2_50V_X7R_0805
C12 | 2.2µF 25V | Standard | Ceramic, 2.2µF, ±10%, 25V, X7R, –55 to 125°C, 0805 (2012),RoHS, Automotive | 0805C |  | master-010106.SCHLIB | gen_C_ceramic_2u2_50V_X7R_0805
C31 | 4.7µF 16V | Standard | Ceramic, 4.7µF, ±10%, 16V, X7R, –55 to 125°C, 0805 (2012),RoHS, Automotive | 0805C |  | master-010106.SCHLIB | gen_C_ceramic_4u7_16V_X7R_0805
C8 | 2.2µF 25V | Standard | Ceramic, 2.2µF, ±10%, 25V, X7R, –55 to 125°C, 0805 (2012),RoHS, Automotive | 0805C |  | master-010106.SCHLIB | gen_C_ceramic_2u2_50V_X7R_0805
C48 | 4.7µF 16V | Standard | Ceramic, 4.7µF, ±10%, 16V, X7R, –55 to 125°C, 0805 (2012),RoHS, Automotive | 0805C |  | master-010106.SCHLIB | gen_C_ceramic_4u7_16V_X7R_0805
C111 | 10µF 10V | Standard | Ceramic, 10µF, ±10%, 10V, X7R, –55 to 125°C, 0805 (2012),RoHS, Automotive | 0805C |  | master-010106.SCHLIB | gen_C_ceramic_10u_10V_X7R_0805
C117 | 10µF 10V | Standard | Ceramic, 10µF, ±10%, 10V, X7R, –55 to 125°C, 0805 (2012),RoHS, Automotive | 0805C |  | master-010106.SCHLIB | gen_C_ceramic_10u_10V_X7R_0805
C14 | 10µF 10V | Standard | Ceramic, 10µF, ±10%, 10V, X7R, –55 to 125°C, 0805 (2012),RoHS, Automotive | 0805C |  | master-010106.SCHLIB | gen_C_ceramic_10u_10V_X7R_0805
C16 | 10µF 10V | Standard | Ceramic, 10µF, ±10%, 10V, X7R, –55 to 125°C, 0805 (2012),RoHS, Automotive | 0805C |  | master-010106.SCHLIB | gen_C_ceramic_10u_10V_X7R_0805
Designator | Comment | Type | Description | Footprint | NA | Library | Lib Reference
C92 | 1.0µF 25V | Standard | Ceramic, 1.0µF, ±10%, 25V, X7R, –55 to 125°C, 0603 (1608),RoHS, Automotive | 0603C |  | master-010106.SCHLIB | gen_C_ceramic_1u_25V_X7R_0603 | C107 | gen_C_ceramic_68p_100V_X7R_0603
C95 | 1.0µF 25V | Standard | Ceramic, 1.0µF, ±10%, 25V, X7R, –55 to 125°C, 0603 (1608),RoHS, Automotive | 0603C |  | master-010106.SCHLIB | gen_C_ceramic_1u_25V_X7R_0603 | C97 | gen_C_ceramic_68p_100V_X7R_0603
C56 | 1.0µF 25V | Standard | Ceramic, 1.0µF, ±10%, 25V, X7R, –55 to 125°C, 0603 (1608),RoHS, Automotive | 0603C |  | master-010106.SCHLIB | gen_C_ceramic_1u_25V_X7R_0603 | C59 | gen_C_ceramic_18p_50V_C0G_0402
C28 | 1.0µF 25V | Standard | Ceramic, 1.0µF, ±10%, 25V, X7R, –55 to 125°C, 0603 (1608),RoHS, Automotive | 0603C |  | master-010106.SCHLIB | gen_C_ceramic_1u_25V_X7R_0603 | C61 | gen_C_ceramic_18p_50V_C0G_0402
C34 | 1.0µF 25V | Standard | Ceramic, 1.0µF, ±10%, 25V, X7R, –55 to 125°C, 0603 (1608),RoHS, Automotive | 0603C |  | master-010106.SCHLIB | gen_C_ceramic_1u_25V_X7R_0603 | C67 | gen_C_ceramic_18p_50V_C0G_0402
C73 | 1.0µF 25V | Standard | Ceramic, 1.0µF, ±10%, 25V, X7R, –55 to 125°C, 0603 (1608),RoHS, Automotive | 0603C |  | master-010106.SCHLIB | gen_C_ceramic_1u_25V_X7R_0603 | C70 | gen_C_ceramic_18p_50V_C0G_0402
C75 | 1.0µF 25V | Standard | Ceramic, 1.0µF, ±10%, 25V, X7R, –55 to 125°C, 0603 (1608),RoHS, Automotive | 0603C |  | master-010106.SCHLIB | gen_C_ceramic_1u_25V_X7R_0603 | Rext_2 | gen_R_0R_0402
C80 | 1.0µF 25V | Standard | Ceramic, 1.0µF, ±10%, 25V, X7R, –55 to 125°C, 0603 (1608),RoHS, Automotive | 0603C |  | master-010106.SCHLIB | gen_C_ceramic_1u_25V_X7R_0603 | C11 | gen_C_ceramic_100n_50V_X7R_0402
C99 | 1.0µF 25V | Standard | Ceramic, 1.0µF, ±10%, 25V, X7R, –55 to 125°C, 0603 (1608),RoHS, Automotive | 0603C |  | master-010106.SCHLIB | gen_C_ceramic_1u_25V_X7R_0603 | C20 | gen_C_ceramic_100n_50V_X7R_0402
C116 | 1.0µF 25V | Standard | Ceramic, 1.0µF, ±10%, 25V, X7R, –55 to 125°C, 0603 (1608),RoHS, Automotive | 0603C |  | master-010106.SCHLIB | gen_C_ceramic_1u_25V_X7R_0603 | C21 | gen_C_ceramic_100n_50V_X7R_0402
C19 | 1.0µF 25V | Standard | Ceramic, 1.0µF, ±10%, 25V, X7R, –55 to 125°C, 0603 (1608),RoHS, Automotive | 0603C |  | master-010106.SCHLIB | gen_C_ceramic_1u_25V_X7R_0603 | C25 | gen_C_ceramic_100n_50V_X7R_0402
C11 | 100nF 50V | Standard | Ceramic, 100nF, ±10%, 50V, X7R, –55 to 125°C, 0402 (1005),RoHS, Automotive | 0402C |  | master-010106.SCHLIB | gen_C_ceramic_100n_50V_X7R_0402 | C26 | gen_C_ceramic_100n_50V_X7R_0402
C20 | 100nF 50V | Standard | Ceramic, 100nF, ±10%, 50V, X7R, –55 to 125°C, 0402 (1005),RoHS, Automotive | 0402C |  | master-010106.SCHLIB | gen_C_ceramic_100n_50V_X7R_0402 | C27 | gen_C_ceramic_100n_50V_X7R_0402
C21 | 100nF 50V | Standard | Ceramic, 100nF, ±10%, 50V, X7R, –55 to 125°C, 0402 (1005),RoHS, Automotive | 0402C |  | master-010106.SCHLIB | gen_C_ceramic_100n_50V_X7R_0402 | C30 | gen_C_ceramic_18p_50V_C0G_0402
C25 | 100nF 50V | Standard | Ceramic, 100nF, ±10%, 50V, X7R, –55 to 125°C, 0402 (1005),RoHS, Automotive | 0402C |  | master-010106.SCHLIB | gen_C_ceramic_100n_50V_X7R_0402 | C33 | gen_C_ceramic_18p_50V_C0G_0402
C26 | 100nF 50V | Standard | Ceramic, 100nF, ±10%, 50V, X7R, –55 to 125°C, 0402 (1005),RoHS, Automotive | 0402C |  | master-010106.SCHLIB | gen_C_ceramic_100n_50V_X7R_0402 | C9 | gen_C_ceramic_100n_50V_X7R_0402
C27 | 100nF 50V | Standard | Ceramic, 100nF, ±10%, 50V, X7R, –55 to 125°C, 0402 (1005),RoHS, Automotive | 0402C |  | master-010106.SCHLIB | gen_C_ceramic_100n_50V_X7R_0402 | Rext_1 | gen_R_0R_0402
C9 | 100nF 50V | Standard | Ceramic, 100nF, ±10%, 50V, X7R, –55 to 125°C, 0402 (1005),RoHS, Automotive | 0402C |  | master-010106.SCHLIB | gen_C_ceramic_100n_50V_X7R_0402 | C102 | gen_C_ceramic_100n_50V_X7R_0603
C49 | 100nF 50V | Standard | Ceramic, 100nF, ±10%, 50V, X7R, –55 to 125°C, 0402 (1005),RoHS, Automotive | 0402C |  | master-010106.SCHLIB | gen_C_ceramic_100n_50V_X7R_0402 | C103 | gen_C_ceramic_10n_50V_X7R_0603
C52 | 100nF 50V | Standard | Ceramic, 100nF, ±10%, 50V, X7R, –55 to 125°C, 0402 (1005),RoHS, Automotive | 0402C |  | master-010106.SCHLIB | gen_C_ceramic_100n_50V_X7R_0402 | C108 | gen_C_ceramic_100n_50V_X7R_0603
C53 | 100nF 50V | Standard | Ceramic, 100nF, ±10%, 50V, X7R, –55 to 125°C, 0402 (1005),RoHS, Automotive | 0402C |  | master-010106.SCHLIB | gen_C_ceramic_100n_50V_X7R_0402 | C49 | gen_C_ceramic_100n_50V_X7R_0402
C54 | 100nF 50V | Standard | Ceramic, 100nF, ±10%, 50V, X7R, –55 to 125°C, 0402 (1005),RoHS, Automotive | 0402C |  | master-010106.SCHLIB | gen_C_ceramic_100n_50V_X7R_0402 | C52 | gen_C_ceramic_100n_50V_X7R_0402
C58 | 100nF 50V | Standard | Ceramic, 100nF, ±10%, 50V, X7R, –55 to 125°C, 0402 (1005),RoHS, Automotive | 0402C |  | master-010106.SCHLIB | gen_C_ceramic_100n_50V_X7R_0402 | C53 | gen_C_ceramic_100n_50V_X7R_0402
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
C24 | 10nF 50V | Standard | Ceramic, 10nF, ±10%, 50V, X7R, –55 to 125°C, 0603 (1608),RoHS, Automotive | 0603C |  | master-010106.SCHLIB | gen_C_ceramic_10n_50V_X7R_0603 | C24 | gen_C_ceramic_10n_50V_X7R_0603
C59 | 18pF 50V | Standard | Ceramic, 18pF, ±5%, 50V, X7R, 25 to 125°C, 0402 (1005),RoHS, Automotive | 0402C |  | master-010106.SCHLIB | gen_C_ceramic_18p_50V_C0G_0402
C61 | 18pF 50V | Standard | Ceramic, 18pF, ±5%, 50V, X7R, 25 to 125°C, 0402 (1005),RoHS, Automotive | 0402C |  | master-010106.SCHLIB | gen_C_ceramic_18p_50V_C0G_0402
C67 | 18pF 50V | Standard | Ceramic, 18pF, ±5%, 50V, X7R, 25 to 125°C, 0402 (1005),RoHS, Automotive | 0402C |  | master-010106.SCHLIB | gen_C_ceramic_18p_50V_C0G_0402
C70 | 18pF 50V | Standard | Ceramic, 18pF, ±5%, 50V, X7R, 25 to 125°C, 0402 (1005),RoHS, Automotive | 0402C |  | master-010106.SCHLIB | gen_C_ceramic_18p_50V_C0G_0402
C30 | 18pF 50V | Standard | Ceramic, 18pF, ±5%, 50V, X7R, 25 to 125°C, 0402 (1005),RoHS, Automotive | 0402C |  | master-010106.SCHLIB | gen_C_ceramic_18p_50V_C0G_0402
C33 | 18pF 50V | Standard | Ceramic, 18pF, ±5%, 50V, X7R, 25 to 125°C, 0402 (1005),RoHS, Automotive | 0402C |  | master-010106.SCHLIB | gen_C_ceramic_18p_50V_C0G_0402
C107 | 68pF 100V | Standard | Ceramic, 68pF, ±5%, 100V, X7R, 25 to 125°C, 0603 (1608),RoHS, Automotive | 0603C |  | master-010106.SCHLIB | gen_C_ceramic_68p_100V_X7R_0603
C97 | 68pF 100V | Standard | Ceramic, 68pF, ±5%, 100V, X7R, 25 to 125°C, 0603 (1608),RoHS, Automotive | 0603C |  | master-010106.SCHLIB | gen_C_ceramic_68p_100V_X7R_0603
Rext_2 | 0R | Standard | SMD Resistor 0R 0402 | 0402R |  | master-010106.SCHLIB | gen_R_0R_0402
Rext_1 | 0R | Standard | SMD Resistor 0R 0402 | 0402R |  | master-010106.SCHLIB | gen_R_0R_0402
R80 | 0R | Standard | SMD Resistor 0R 0402 | 0402R |  | master-010106.SCHLIB | gen_R_0R_0402
C107 | 68pF 100V | Standard | Ceramic, 68pF, ±5%, 100V, X7R, 25 to 125°C, 0603 (1608),RoHS, Automotive | 0603C |  | master-010106.SCHLIB | gen_C_ceramic_68p_100V_X7R_0603 | C107 | gen_C_ceramic_68p_100V_X7R_0603
C90 | 10µF 10V | Standard | Ceramic, 10µF, ±10%, 10V, X7R, –55 to 125°C, 0805 (2012),RoHS, Automotive | 0805C |  | master-010106.SCHLIB | gen_C_ceramic_10u_10V_X7R_0805 | C90 | gen_C_ceramic_10u_10V_X7R_0805
C91 | 10µF 10V | Standard | Ceramic, 10µF, ±10%, 10V, X7R, –55 to 125°C, 0805 (2012),RoHS, Automotive | 0805C |  | master-010106.SCHLIB | gen_C_ceramic_10u_10V_X7R_0805 | C91 | gen_C_ceramic_10u_10V_X7R_0805
C92 | 1.0µF 25V | Standard | Ceramic, 1.0µF, ±10%, 25V, X7R, –55 to 125°C, 0603 (1608),RoHS, Automotive | 0603C |  | master-010106.SCHLIB | gen_C_ceramic_1u_25V_X7R_0603 | C92 | gen_C_ceramic_1u_25V_X7R_0603
C95 | 1.0µF 25V | Standard | Ceramic, 1.0µF, ±10%, 25V, X7R, –55 to 125°C, 0603 (1608),RoHS, Automotive | 0603C |  | master-010106.SCHLIB | gen_C_ceramic_1u_25V_X7R_0603 | C95 | gen_C_ceramic_1u_25V_X7R_0603
C97 | 68pF 100V | Standard | Ceramic, 68pF, ±5%, 100V, X7R, 25 to 125°C, 0603 (1608),RoHS, Automotive | 0603C |  | master-010106.SCHLIB | gen_C_ceramic_68p_100V_X7R_0603 | C97 | gen_C_ceramic_68p_100V_X7R_0603
R71 | 0R | Standard | SMD Resistor 0R 0603 | 0603R |  | master-010106.SCHLIB | gen_R_0R_0603 | R71 | gen_R_0R_0603
C56 | 1.0µF 25V | Standard | Ceramic, 1.0µF, ±10%, 25V, X7R, –55 to 125°C, 0603 (1608),RoHS, Automotive | 0603C |  | master-010106.SCHLIB | gen_C_ceramic_1u_25V_X7R_0603 | C56 | gen_C_ceramic_1u_25V_X7R_0603
C59 | 18pF 50V | Standard | Ceramic, 18pF, ±5%, 50V, X7R, 25 to 125°C, 0402 (1005),RoHS, Automotive | 0402C |  | master-010106.SCHLIB | gen_C_ceramic_18p_50V_C0G_0402 | C59 | gen_C_ceramic_18p_50V_C0G_0402
C61 | 18pF 50V | Standard | Ceramic, 18pF, ±5%, 50V, X7R, 25 to 125°C, 0402 (1005),RoHS, Automotive | 0402C |  | master-010106.SCHLIB | gen_C_ceramic_18p_50V_C0G_0402 | C61 | gen_C_ceramic_18p_50V_C0G_0402
C67 | 18pF 50V | Standard | Ceramic, 18pF, ±5%, 50V, X7R, 25 to 125°C, 0402 (1005),RoHS, Automotive | 0402C |  | master-010106.SCHLIB | gen_C_ceramic_18p_50V_C0G_0402 | C67 | gen_C_ceramic_18p_50V_C0G_0402
C70 | 18pF 50V | Standard | Ceramic, 18pF, ±5%, 50V, X7R, 25 to 125°C, 0402 (1005),RoHS, Automotive | 0402C |  | master-010106.SCHLIB | gen_C_ceramic_18p_50V_C0G_0402 | C70 | gen_C_ceramic_18p_50V_C0G_0402
Rext_2 | 0R | Standard | SMD Resistor 0R 0402 | 0402R |  | master-010106.SCHLIB | gen_R_0R_0402 | Rext_2 | gen_R_0R_0402
R13 | 10R | Standard | SMD Resistor 10R 0805 | 0805R |  | master-010106.SCHLIB | gen_R_10R_0805 | R13 | gen_R_10R_0805
C1 | 4.7µF 16V | Standard | Ceramic, 4.7µF, ±10%, 16V, X7R, –55 to 125°C, 0805 (2012),RoHS, Automotive | 0805C |  | master-010106.SCHLIB | gen_C_ceramic_4u7_16V_X7R_0805 | C1 | gen_C_ceramic_4u7_16V_X7R_0805
C60 | 2.2µF 25V | Standard | Ceramic, 2.2µF, ±10%, 25V, X7R, –55 to 125°C, 0805 (2012),RoHS, Automotive | 0805C |  | master-010106.SCHLIB | gen_C_ceramic_2u2_50V_X7R_0805 | C60 | gen_C_ceramic_2u2_50V_X7R_0805
C88 | 2.2µF 25V | Standard | Ceramic, 2.2µF, ±10%, 25V, X7R, –55 to 125°C, 0805 (2012),RoHS, Automotive | 0805C |  | master-010106.SCHLIB | gen_C_ceramic_2u2_50V_X7R_0805 | C88 | gen_C_ceramic_2u2_50V_X7R_0805
R72 | 4k7 | Standard | SMD Resistor 4.7k 0603 | 0603R |  | master-010106.SCHLIB | gen_R_4K7_0603 | R72 | gen_R_4K7_0603
R73 | 4k7 | Standard | SMD Resistor 4.7k 0603 | 0603R |  | master-010106.SCHLIB | gen_R_4K7_0603 | R73 | gen_R_4K7_0603
C11 | 100nF 50V | Standard | Ceramic, 100nF, ±10%, 50V, X7R, –55 to 125°C, 0402 (1005),RoHS, Automotive | 0402C |  | master-010106.SCHLIB | gen_C_ceramic_100n_50V_X7R_0603 | C11 | gen_C_ceramic_100n_50V_X7R_0603
C12 | 2.2µF 25V | Standard | Ceramic, 2.2µF, ±10%, 25V, X7R, –55 to 125°C, 0805 (2012),RoHS, Automotive | 0805C |  | master-010106.SCHLIB | gen_C_ceramic_2u2_50V_X7R_0805 | C12 | gen_C_ceramic_2u2_50V_X7R_0805
C20 | 100nF 50V | Standard | Ceramic, 100nF, ±10%, 50V, X7R, –55 to 125°C, 0402 (1005),RoHS, Automotive | 0402C |  | master-010106.SCHLIB | gen_C_ceramic_100n_50V_X7R_0603 | C20 | gen_C_ceramic_100n_50V_X7R_0603
C21 | 100nF 50V | Standard | Ceramic, 100nF, ±10%, 50V, X7R, –55 to 125°C, 0402 (1005),RoHS, Automotive | 0402C |  | master-010106.SCHLIB | gen_C_ceramic_100n_50V_X7R_0603 | C21 | gen_C_ceramic_100n_50V_X7R_0603
C25 | 100nF 50V | Standard | Ceramic, 100nF, ±10%, 50V, X7R, –55 to 125°C, 0402 (1005),RoHS, Automotive | 0402C |  | master-010106.SCHLIB | gen_C_ceramic_100n_50V_X7R_0603 | C25 | gen_C_ceramic_100n_50V_X7R_0603
C26 | 100nF 50V | Standard | Ceramic, 100nF, ±10%, 50V, X7R, –55 to 125°C, 0402 (1005),RoHS, Automotive | 0402C |  | master-010106.SCHLIB | gen_C_ceramic_100n_50V_X7R_0603 | C26 | gen_C_ceramic_100n_50V_X7R_0603
C27 | 100nF 50V | Standard | Ceramic, 100nF, ±10%, 50V, X7R, –55 to 125°C, 0402 (1005),RoHS, Automotive | 0402C |  | master-010106.SCHLIB | gen_C_ceramic_100n_50V_X7R_0603 | C27 | gen_C_ceramic_100n_50V_X7R_0603
C28 | 1.0µF 25V | Standard | Ceramic, 1.0µF, ±10%, 25V, X7R, –55 to 125°C, 0603 (1608),RoHS, Automotive | 0603C |  | master-010106.SCHLIB | gen_C_ceramic_1u_25V_X7R_0603 | C28 | gen_C_ceramic_1u_25V_X7R_0603
C30 | 18pF 50V | Standard | Ceramic, 18pF, ±5%, 50V, X7R, 25 to 125°C, 0402 (1005),RoHS, Automotive | 0402C |  | master-010106.SCHLIB | gen_C_ceramic_18p_50V_C0G_0402 | C30 | gen_C_ceramic_18p_50V_C0G_0402
C31 | 4.7µF 16V | Standard | Ceramic, 4.7µF, ±10%, 16V, X7R, –55 to 125°C, 0805 (2012),RoHS, Automotive | 0805C |  | master-010106.SCHLIB | gen_C_ceramic_4u7_16V_X7R_0805 | C31 | gen_C_ceramic_4u7_16V_X7R_0805
C33 | 18pF 50V | Standard | Ceramic, 18pF, ±5%, 50V, X7R, 25 to 125°C, 0402 (1005),RoHS, Automotive | 0402C |  | master-010106.SCHLIB | gen_C_ceramic_18p_50V_C0G_0402 | C33 | gen_C_ceramic_18p_50V_C0G_0402
C34 | 1.0µF 25V | Standard | Ceramic, 1.0µF, ±10%, 25V, X7R, –55 to 125°C, 0603 (1608),RoHS, Automotive | 0603C |  | master-010106.SCHLIB | gen_C_ceramic_1u_25V_X7R_0603 | C34 | gen_C_ceramic_1u_25V_X7R_0603
C8 | 2.2µF 25V | Standard | Ceramic, 2.2µF, ±10%, 25V, X7R, –55 to 125°C, 0805 (2012),RoHS, Automotive | 0805C |  | master-010106.SCHLIB | gen_C_ceramic_2u2_50V_X7R_0805 | C8 | gen_C_ceramic_2u2_50V_X7R_0805
C9 | 100nF 50V | Standard | Ceramic, 100nF, ±10%, 50V, X7R, –55 to 125°C, 0402 (1005),RoHS, Automotive | 0402C |  | master-010106.SCHLIB | gen_C_ceramic_100n_50V_X7R_0603 | C9 | gen_C_ceramic_100n_50V_X7R_0603
Rext_1 | 0R | Standard | SMD Resistor 0R 0402 | 0402R |  | master-010106.SCHLIB | gen_R_0R_0402 | Rext_1 | gen_R_0R_0402
C102 | 100nF 50V | Standard | Ceramic, 100nF, ±10%, 50V, X7R, –55 to 125°C, 0603 (1608),RoHS, Automotive | 0603C |  | master-010106.SCHLIB | gen_C_ceramic_100n_50V_X7R_0603 | C102 | gen_C_ceramic_100n_50V_X7R_0603
C103 | 10nF 50V | Standard | Ceramic, 10nF, ±10%, 50V, X7R, –55 to 125°C, 0603 (1608),RoHS, Automotive | 0603C |  | master-010106.SCHLIB | gen_C_ceramic_10n_50V_X7R_0603 | C103 | gen_C_ceramic_10n_50V_X7R_0603
C108 | 100nF 50V | Standard | Ceramic, 100nF, ±10%, 50V, X7R, –55 to 125°C, 0603 (1608),RoHS, Automotive | 0603C |  | master-010106.SCHLIB | gen_C_ceramic_100n_50V_X7R_0603 | C108 | gen_C_ceramic_100n_50V_X7R_0603
C48 | 4.7µF 16V | Standard | Ceramic, 4.7µF, ±10%, 16V, X7R, –55 to 125°C, 0805 (2012),RoHS, Automotive | 0805C |  | master-010106.SCHLIB | gen_C_ceramic_4u7_16V_X7R_0805 | C48 | gen_C_ceramic_4u7_16V_X7R_0805
C49 | 100nF 50V | Standard | Ceramic, 100nF, ±10%, 50V, X7R, –55 to 125°C, 0402 (1005),RoHS, Automotive | 0402C |  | master-010106.SCHLIB | gen_C_ceramic_100n_50V_X7R_0603 | C49 | gen_C_ceramic_100n_50V_X7R_0603
C52 | 100nF 50V | Standard | Ceramic, 100nF, ±10%, 50V, X7R, –55 to 125°C, 0402 (1005),RoHS, Automotive | 0402C |  | master-010106.SCHLIB | gen_C_ceramic_100n_50V_X7R_0603 | C52 | gen_C_ceramic_100n_50V_X7R_0603
C53 | 100nF 50V | Standard | Ceramic, 100nF, ±10%, 50V, X7R, –55 to 125°C, 0402 (1005),RoHS, Automotive | 0402C |  | master-010106.SCHLIB | gen_C_ceramic_100n_50V_X7R_0603 | C53 | gen_C_ceramic_100n_50V_X7R_0603
C54 | 100nF 50V | Standard | Ceramic, 100nF, ±10%, 50V, X7R, –55 to 125°C, 0402 (1005),RoHS, Automotive | 0402C |  | master-010106.SCHLIB | gen_C_ceramic_100n_50V_X7R_0603 | C54 | gen_C_ceramic_100n_50V_X7R_0603
C58 | 100nF 50V | Standard | Ceramic, 100nF, ±10%, 50V, X7R, –55 to 125°C, 0402 (1005),RoHS, Automotive | 0402C |  | master-010106.SCHLIB | gen_C_ceramic_100n_50V_X7R_0603 | C58 | gen_C_ceramic_100n_50V_X7R_0603
C62 | 100nF 50V | Standard | Ceramic, 100nF, ±10%, 50V, X7R, –55 to 125°C, 0402 (1005),RoHS, Automotive | 0402C |  | master-010106.SCHLIB | gen_C_ceramic_100n_50V_X7R_0603 | C62 | gen_C_ceramic_100n_50V_X7R_0603
C63 | 100nF 50V | Standard | Ceramic, 100nF, ±10%, 50V, X7R, –55 to 125°C, 0402 (1005),RoHS, Automotive | 0402C |  | master-010106.SCHLIB | gen_C_ceramic_100n_50V_X7R_0603 | C63 | gen_C_ceramic_100n_50V_X7R_0603
C64 | 100nF 50V | Standard | Ceramic, 100nF, ±10%, 50V, X7R, –55 to 125°C, 0402 (1005),RoHS, Automotive | 0402C |  | master-010106.SCHLIB | gen_C_ceramic_100n_50V_X7R_0603 | C64 | gen_C_ceramic_100n_50V_X7R_0603
C69 | 100nF 50V | Standard | Ceramic, 100nF, ±10%, 50V, X7R, –55 to 125°C, 0402 (1005),RoHS, Automotive | 0402C |  | master-010106.SCHLIB | gen_C_ceramic_100n_50V_X7R_0603 | C69 | gen_C_ceramic_100n_50V_X7R_0603
C73 | 1.0µF 25V | Standard | Ceramic, 1.0µF, ±10%, 25V, X7R, –55 to 125°C, 0603 (1608),RoHS, Automotive | 0603C |  | master-010106.SCHLIB | gen_C_ceramic_1u_25V_X7R_0603 | C73 | gen_C_ceramic_1u_25V_X7R_0603
C74 | 100nF 50V | Standard | Ceramic, 100nF, ±10%, 50V, X7R, –55 to 125°C, 0402 (1005),RoHS, Automotive | 0402C |  | master-010106.SCHLIB | gen_C_ceramic_100n_50V_X7R_0603 | C74 | gen_C_ceramic_100n_50V_X7R_0603
C75 | 1.0µF 25V | Standard | Ceramic, 1.0µF, ±10%, 25V, X7R, –55 to 125°C, 0603 (1608),RoHS, Automotive | 0603C |  | master-010106.SCHLIB | gen_C_ceramic_1u_25V_X7R_0603 | C75 | gen_C_ceramic_1u_25V_X7R_0603
C76 | 100nF 50V | Standard | Ceramic, 100nF, ±10%, 50V, X7R, –55 to 125°C, 0402 (1005),RoHS, Automotive | 0402C |  | master-010106.SCHLIB | gen_C_ceramic_100n_50V_X7R_0603 | C76 | gen_C_ceramic_100n_50V_X7R_0603
C77 | 100nF 50V | Standard | Ceramic, 100nF, ±10%, 50V, X7R, –55 to 125°C, 0402 (1005),RoHS, Automotive | 0402C |  | master-010106.SCHLIB | gen_C_ceramic_100n_50V_X7R_0603 | C77 | gen_C_ceramic_100n_50V_X7R_0603
C78 | 100nF 50V | Standard | Ceramic, 100nF, ±10%, 50V, X7R, –55 to 125°C, 0402 (1005),RoHS, Automotive | 0402C |  | master-010106.SCHLIB | gen_C_ceramic_100n_50V_X7R_0603 | C78 | gen_C_ceramic_100n_50V_X7R_0603
C80 | 1.0µF 25V | Standard | Ceramic, 1.0µF, ±10%, 25V, X7R, –55 to 125°C, 0603 (1608),RoHS, Automotive | 0603C |  | master-010106.SCHLIB | gen_C_ceramic_1u_25V_X7R_0603 | C80 | gen_C_ceramic_1u_25V_X7R_0603
C84 | 100nF 50V | Standard | Ceramic, 100nF, ±10%, 50V, X7R, –55 to 125°C, 0402 (1005),RoHS, Automotive | 0402C |  | master-010106.SCHLIB | gen_C_ceramic_100n_50V_X7R_0603 | C84 | gen_C_ceramic_100n_50V_X7R_0603
C85 | 100nF 50V | Standard | Ceramic, 100nF, ±10%, 50V, X7R, –55 to 125°C, 0402 (1005),RoHS, Automotive | 0402C |  | master-010106.SCHLIB | gen_C_ceramic_100n_50V_X7R_0603 | C85 | gen_C_ceramic_100n_50V_X7R_0603
C86 | 100nF 50V | Standard | Ceramic, 100nF, ±10%, 50V, X7R, –55 to 125°C, 0402 (1005),RoHS, Automotive | 0402C |  | master-010106.SCHLIB | gen_C_ceramic_100n_50V_X7R_0603 | C86 | gen_C_ceramic_100n_50V_X7R_0603
C87 | 100nF 50V | Standard | Ceramic, 100nF, ±10%, 50V, X7R, –55 to 125°C, 0402 (1005),RoHS, Automotive | 0402C |  | master-010106.SCHLIB | gen_C_ceramic_100n_50V_X7R_0603 | C87 | gen_C_ceramic_100n_50V_X7R_0603
C89 | 10nF 50V | Standard | Ceramic, 10nF, ±10%, 50V, X7R, –55 to 125°C, 0603 (1608),RoHS, Automotive | 0603C |  | master-010106.SCHLIB | gen_C_ceramic_10n_50V_X7R_0603 | C89 | gen_C_ceramic_10n_50V_X7R_0603
C99 | 1.0µF 25V | Standard | Ceramic, 1.0µF, ±10%, 25V, X7R, –55 to 125°C, 0603 (1608),RoHS, Automotive | 0603C |  | master-010106.SCHLIB | gen_C_ceramic_1u_25V_X7R_0603 | C99 | gen_C_ceramic_1u_25V_X7R_0603
R64 | 100k | Standard | SMD Resistor 100k 0603 | 0603R |  | master-010106.SCHLIB | gen_R_100k_0603 | R64 | gen_R_100k_0603
R65 | 100k | Standard | SMD Resistor 100k 0603 | 0603R |  | master-010106.SCHLIB | gen_R_100k_0603 | R65 | gen_R_100k_0603
R70 | 100k | Standard | SMD Resistor 100k 0603 | 0603R |  | master-010106.SCHLIB | gen_R_100k_0603 | R70 | gen_R_100k_0603
R75 | NF | Standard | SMD Resistor NF 0603 | 0603R |  | master-010106.SCHLIB | gen_R_NF_0603 | R75 | gen_R_NF_0603
R76 | 10Meg | Standard | SMD Resistor 10Meg 0603 | 0603R |  | master-010106.SCHLIB | gen_R_10M_0603 | R76 | gen_R_10M_0603
C111 | 10µF 10V | Standard | Ceramic, 10µF, ±10%, 10V, X7R, –55 to 125°C, 0805 (2012),RoHS, Automotive | 0805C |  | master-010106.SCHLIB | gen_C_ceramic_10u_10V_X7R_0805 | C111 | gen_C_ceramic_10u_10V_X7R_0805
C112 | 10nF 50V | Standard | Ceramic, 10nF, ±10%, 50V, X7R, –55 to 125°C, 0603 (1608),RoHS, Automotive | 0603C |  | master-010106.SCHLIB | gen_C_ceramic_10n_50V_X7R_0603 | C112 | gen_C_ceramic_10n_50V_X7R_0603
C115 | 10nF 50V | Standard | Ceramic, 10nF, ±10%, 50V, X7R, –55 to 125°C, 0603 (1608),RoHS, Automotive | 0603C |  | master-010106.SCHLIB | gen_C_ceramic_10n_50V_X7R_0603 | C115 | gen_C_ceramic_10n_50V_X7R_0603
C116 | 1.0µF 25V | Standard | Ceramic, 1.0µF, ±10%, 25V, X7R, –55 to 125°C, 0603 (1608),RoHS, Automotive | 0603C |  | master-010106.SCHLIB | gen_C_ceramic_1u_25V_X7R_0603 | C116 | gen_C_ceramic_1u_25V_X7R_0603
C117 | 10µF 10V | Standard | Ceramic, 10µF, ±10%, 10V, X7R, –55 to 125°C, 0805 (2012),RoHS, Automotive | 0805C |  | master-010106.SCHLIB | gen_C_ceramic_10u_10V_X7R_0805 | C117 | gen_C_ceramic_10u_10V_X7R_0805
C122 | 10nF 50V | Standard | Ceramic, 10nF, ±10%, 50V, X7R, –55 to 125°C, 0402 (1005),RoHS, Automotive | 0402C |  | master-010106.SCHLIB | gen_C_ceramic_10n_50V_X7R_0402 | C122 | gen_C_ceramic_10n_50V_X7R_0402
R68 | 0.01R | Standard | SMD Resistor 10m 0805 | 0805R |  | master-010106.SCHLIB | gen_R_0.01R_0805 | R68 | gen_R_0.01R_0805
R74 | 10k | Standard | SMD Resistor 10k 0603 | 0603R |  | master-010106.SCHLIB | gen_R_10k_0603 | R74 | gen_R_10k_0603
R77 | 10.7k | Standard | SMD Resistor 10.7k 0402 | 0402R |  | master-010106.SCHLIB | gen_R_10K7_0402 | R77 | gen_R_10K7_0402
R78 | 100k | Standard | SMD Resistor 100k 0402 | 0402R |  | master-010106.SCHLIB | gen_R_100k_0402 | R78 | gen_R_100k_0402
R79 | 26.1k | Standard | SMD Resistor 26.1k 0402 | 0402R |  | master-010106.SCHLIB | gen_R_26k1_0402 | R79 | gen_R_26k1_0402
R80 | 0R | Standard | SMD Resistor 0R 0402 | 0402R |  | master-010106.SCHLIB | gen_R_0R_0402 | R80 | gen_R_0R_0402
R81 | 374k | Standard | SMD Resistor 374k 0402 | 0402R |  | master-010106.SCHLIB | gen_R_374k_0402 | R81 | gen_R_374k_0402
R82 | 49k9 | Standard | SMD Resistor 49.9k 0402 | 0402R |  | master-010106.SCHLIB | gen_R_49k9_0402 | R82 | gen_R_49k9_0402
C14 | 10µF 10V | Standard | Ceramic, 10µF, ±10%, 10V, X7R, –55 to 125°C, 0805 (2012),RoHS, Automotive | 0805C |  | master-010106.SCHLIB | gen_C_ceramic_10u_10V_X7R_0805 | C14 | gen_C_ceramic_10u_10V_X7R_0805
C16 | 10µF 10V | Standard | Ceramic, 10µF, ±10%, 10V, X7R, –55 to 125°C, 0805 (2012),RoHS, Automotive | 0805C |  | master-010106.SCHLIB | gen_C_ceramic_10u_10V_X7R_0805 | C16 | gen_C_ceramic_10u_10V_X7R_0805
C19 | 1.0µF 25V | Standard | Ceramic, 1.0µF, ±10%, 25V, X7R, –55 to 125°C, 0603 (1608),RoHS, Automotive | 0603C |  | master-010106.SCHLIB | gen_C_ceramic_1u_25V_X7R_0603 | C19 | gen_C_ceramic_1u_25V_X7R_0603
C22 | 10nF 50V | Standard | Ceramic, 10nF, ±10%, 50V, X7R, –55 to 125°C, 0603 (1608),RoHS, Automotive | 0603C |  | master-010106.SCHLIB | gen_C_ceramic_10n_50V_X7R_0603 | C22 | gen_C_ceramic_10n_50V_X7R_0603
C24 | 10nF 50V | Standard | Ceramic, 10nF, ±10%, 50V, X7R, –55 to 125°C, 0603 (1608),RoHS, Automotive | 0603C |  | master-010106.SCHLIB | gen_C_ceramic_10n_50V_X7R_0603 | C24 | gen_C_ceramic_10n_50V_X7R_0603
R2 | 0.01R | Standard | SMD Resistor 10m 0805 | 0805R |  | master-010106.SCHLIB | gen_R_0.01R_0805 | R2 | gen_R_0.01R_0805
R3 | 10k | Standard | SMD Resistor 10k 0603 | 0603R |  | master-010106.SCHLIB | gen_R_10k_0603 | R3 | gen_R_10k_0603

Sheet: Sheet8
D | E | F | G | H | I
Aluminum Electrolytic Capacitor, Low Impedance, 1000 uF +/- 20%, 16 V, -55 to 105 degC, 2-Pin 10.3 x 10.3 x 13.5 mm SMD, RoHS, Reel | NIC-UCL-10x13.5-2_V |  | Altium Content Vault | CMP-0926-00001-1
Ceramic, 100nF, ±10%, 50V, X7R, –55 to 125°C, 0603 (1608),RoHS, Automotive | 0603C |  | master-010106.SCHLIB | gen_C_ceramic_100n_50V_X7R_0603
Ceramic, 100nF, ±10%, 50V, X7R, –55 to 125°C, 0603 (1608),RoHS, Automotive | 0603C |  | master-010106.SCHLIB | gen_C_ceramic_100n_50V_X7R_0603
Ceramic, 100nF, ±10%, 50V, X7R, –55 to 125°C, 0603 (1608),RoHS, Automotive | 0603C |  | master-010106.SCHLIB | gen_C_ceramic_100n_50V_X7R_0603
Ceramic, 100nF, ±10%, 50V, X7R, –55 to 125°C, 0603 (1608),RoHS, Automotive | 0603C |  | master-010106.SCHLIB | gen_C_ceramic_100n_50V_X7R_0603
Ceramic, 100nF, ±10%, 50V, X7R, –55 to 125°C, 0603 (1608),RoHS, Automotive | 0603C |  | master-010106.SCHLIB | gen_C_ceramic_100n_50V_X7R_0603
Ceramic, 100nF, ±10%, 50V, X7R, –55 to 125°C, 0603 (1608),RoHS, Automotive | 0603C |  | master-010106.SCHLIB | gen_C_ceramic_100n_50V_X7R_0603
Ceramic, 100nF, ±10%, 50V, X7R, –55 to 125°C, 0603 (1608),RoHS, Automotive | 0603C |  | master-010106.SCHLIB | gen_C_ceramic_100n_50V_X7R_0603
Ceramic, 100nF, ±10%, 50V, X7R, –55 to 125°C, 0603 (1608),RoHS, Automotive | 0603C |  | master-010106.SCHLIB | gen_C_ceramic_100n_50V_X7R_0603
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
Ceramic, 100nF, ±10%, 50V, X7R, –55 to 125°C, 0603 (1608),RoHS, Automotive | 0603C |  | master-010106.SCHLIB | gen_C_ceramic_100n_50V_X7R_0603
Ceramic, 100nF, ±10%, 50V, X7R, –55 to 125°C, 0603 (1608),RoHS, Automotive | 0603C |  | master-010106.SCHLIB | gen_C_ceramic_100n_50V_X7R_0603
Ceramic, 100nF, ±10%, 50V, X7R, –55 to 125°C, 0603 (1608),RoHS, Automotive | 0603C |  | master-010106.SCHLIB | gen_C_ceramic_100n_50V_X7R_0603
Ceramic, 100nF, ±10%, 50V, X7R, –55 to 125°C, 0603 (1608),RoHS, Automotive | 0603C |  | master-010106.SCHLIB | gen_C_ceramic_100n_50V_X7R_0603
Ceramic, 100nF, ±10%, 50V, X7R, –55 to 125°C, 0603 (1608),RoHS, Automotive | 0603C |  | master-010106.SCHLIB | gen_C_ceramic_100n_50V_X7R_0603
Ceramic, 100nF, ±10%, 50V, X7R, –55 to 125°C, 0603 (1608),RoHS, Automotive | 0603C |  | master-010106.SCHLIB | gen_C_ceramic_100n_50V_X7R_0603
Ceramic, 100nF, ±10%, 50V, X7R, –55 to 125°C, 0603 (1608),RoHS, Automotive | 0603C |  | master-010106.SCHLIB | gen_C_ceramic_100n_50V_X7R_0603
Ceramic, 100nF, ±10%, 50V, X7R, –55 to 125°C, 0603 (1608),RoHS, Automotive | 0603C |  | master-010106.SCHLIB | gen_C_ceramic_100n_50V_X7R_0603
Ceramic, 100nF, ±10%, 50V, X7R, –55 to 125°C, 0603 (1608),RoHS, Automotive | 0603C |  | master-010106.SCHLIB | gen_C_ceramic_100n_50V_X7R_0603
Ceramic, 100nF, ±10%, 50V, X7R, –55 to 125°C, 0603 (1608),RoHS, Automotive | 0603C |  | master-010106.SCHLIB | gen_C_ceramic_100n_50V_X7R_0603
Multilayer Ceramic Capacitor, 50 V, -55 to 125 degC, 2-Pin SMD (1210), RoHS, Tape and Reel | CAPC3225X279X50LL20T25 |  | master-010106.SCHLIB | gen_C_ceramic_10u_25V_X7R_1210
Multilayer Ceramic Capacitor, 50 V, -55 to 125 degC, 2-Pin SMD (1210), RoHS, Tape and Reel | CAPC3225X279X50LL20T25 |  | master-010106.SCHLIB | gen_C_ceramic_10u_25V_X7R_1210
Multilayer Ceramic Capacitor, 50 V, -55 to 125 degC, 2-Pin SMD (1210), RoHS, Tape and Reel | CAPC3225X279X50LL20T25 |  | master-010106.SCHLIB | gen_C_ceramic_10u_25V_X7R_1210
Multilayer Ceramic Capacitor, 50 V, -55 to 125 degC, 2-Pin SMD (1210), RoHS, Tape and Reel | CAPC3225X279X50LL20T25 |  | master-010106.SCHLIB | gen_C_ceramic_10u_25V_X7R_1210
Chip Capacitor, 1 uF, +/- 10%, 100 V, -55 to 125 degC, 1206 (3216 Metric), RoHS, Tape and Reel | CAPC3216X180X55ML20T25 |  | master-010106.SCHLIB | gen_C_ceramic_1u_100V_X7R_1206
Chip Capacitor, 1 uF, +/- 10%, 100 V, -55 to 125 degC, 1206 (3216 Metric), RoHS, Tape and Reel | CAPC3216X180X55ML20T25 |  | master-010106.SCHLIB | gen_C_ceramic_1u_100V_X7R_1206
Chip Capacitor, 1 uF, +/- 10%, 100 V, -55 to 125 degC, 1206 (3216 Metric), RoHS, Tape and Reel | CAPC3216X180X55ML20T25 |  | master-010106.SCHLIB | gen_C_ceramic_1u_100V_X7R_1206
Chip Capacitor, 1 uF, +/- 10%, 100 V, -55 to 125 degC, 1206 (3216 Metric), RoHS, Tape and Reel | CAPC3216X180X55ML20T25 |  | master-010106.SCHLIB | gen_C_ceramic_1u_100V_X7R_1206
Ceramic, 2.2µF, ±10%, 25V, X7R, –55 to 125°C, 0805 (2012),RoHS, Automotive | 0805C |  | master-010106.SCHLIB | gen_C_ceramic_2u2_50V_X7R_0805
Ceramic, 4700pF, 0603, ±5%, 50V, C0G | 0603C |  | master-010106.SCHLIB | gen_C_ceramic_4n7_50V_X7R_0603
SMD Resistor 0R 0603 |  |  |  | gen_R_0R_0603
SMD Resistor 0R 0402 |  |  |  | gen_R_0R_0402
SMD Resistor 10R 0805 |  |  |  | gen_R_10R_0805
SMD Resistor 4.7k 0603 |  |  |  | gen_R_4K7_0603
Ceramic, 4.7µF, ±10%, 16V, X7R, –55 to 125°C, 0805 (2012),RoHS, Automotive |  |  |  | gen_C_ceramic_4u7_16V_X7R_0805
SMD Resistor 100k 0603 |  |  |  | gen_R_100k_0603
SMD Resistor NF 0603 |  |  |  | gen_R_NF_0603
SMD Resistor 10Meg 0603 |  |  |  | gen_R_10M_0603
Ceramic, 10µF, ±10%, 10V, X7R, –55 to 125°C, 0805 (2012),RoHS, Automotive |  |  |  | gen_C_ceramic_10u_10V_X7R_0805
SMD Resistor 10m 0805 |  |  |  | gen_R_0.01R_0805
SMD Resistor 10k 0603 |  |  |  | gen_R_10k_0603
SMD Resistor 10.7k 0402 |  |  |  | gen_R_10K7_0402
SMD Resistor 100k 0402 |  |  |  | gen_R_100k_0402
SMD Resistor 26.1k 0402 |  |  |  | gen_R_26k1_0402
SMD Resistor 374k 0402 |  |  |  | gen_R_374k_0402
SMD Resistor 49.9k 0402 |  |  |  | gen_R_49k9_0402
