ArakniD/foxbms/hardware/datasheets/WBDesign24_AltiumDesigner/ExportFiles/Schematic/Altium/2019-07-21_05-52-01/SDR0403.stp

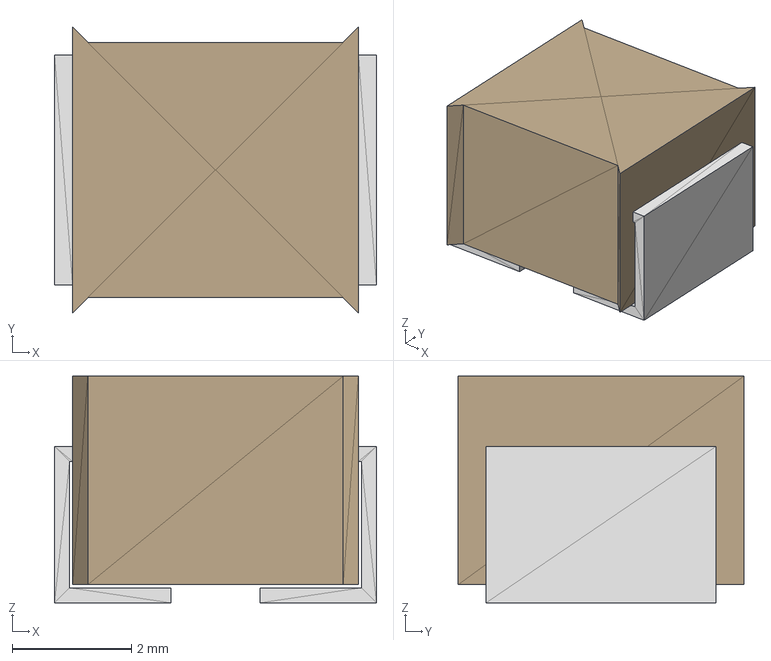
[picture p18: CAD file, 2019-10-29]
hardware/datasheets/WBDesign24_AltiumDesigner/ExportFiles/Schematic/Altium/2019-07-21_05-52-01/SDR0403.stp
5.41 x 4.80 x 3.81 mm
