ArakniD/foxbms/hardware/datasheets/Imports/DWV0008A.stp

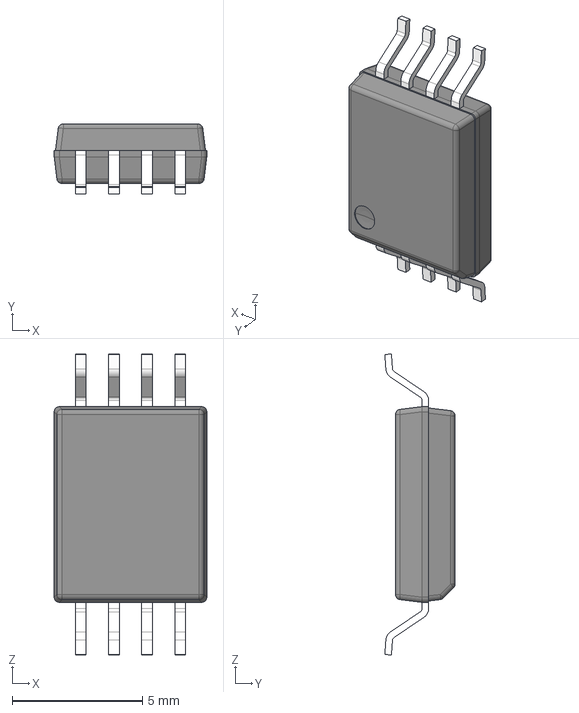
[picture p19: CAD file, 2019-10-29]
hardware/datasheets/Imports/DWV0008A.stp
5.85 x 2.70 x 11.5 mm
BODY-SOIC
LEAD-DWV0008A x 8
