ArakniD/foxbms/hardware/datasheets/HM2101NL_3D.STEP

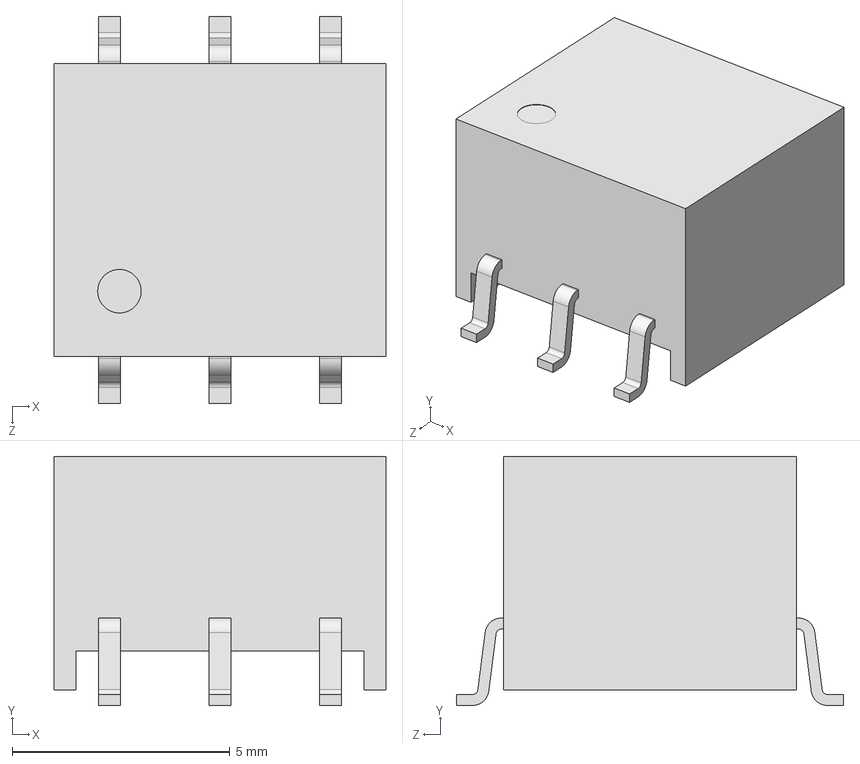
[picture p20: CAD file, 2019-10-29]
hardware/datasheets/HM2101NL_3D.STEP
7.62 x 5.72 x 8.89 mm
