ArakniD/foxbms/hardware/datasheets/Imports/Download_STP_250-1243 (rev1).STEP

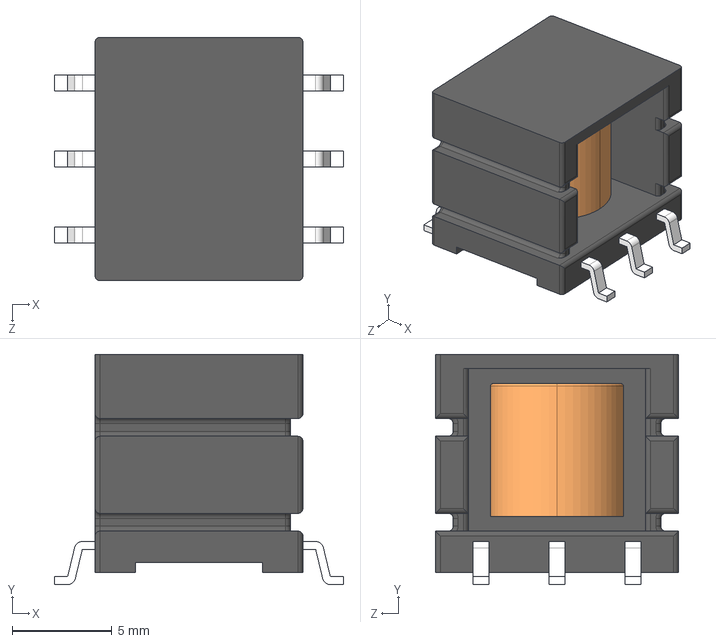
[picture p21: CAD file, 2019-10-29]
hardware/datasheets/Imports/Download_STP_250-1243 (rev1).STEP
14.5 x 11.5 x 12.2 mm
250-1243_6B
150-3052_6A
