ArakniD/foxbms/hardware/datasheets/Imports/DW0016B.stp

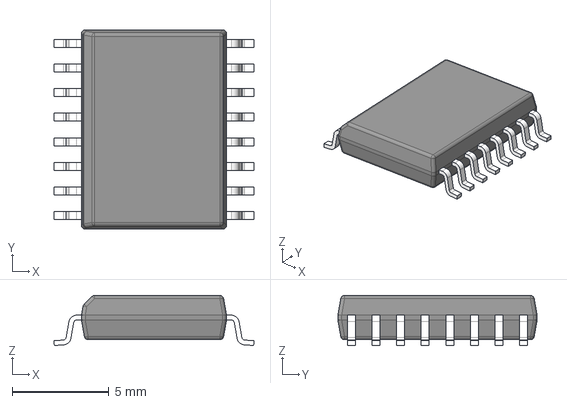
[picture p22: CAD file, 2019-07-09]
hardware/datasheets/Imports/DW0016B.stp
10.3 x 10.3 x 2.59 mm
BODY-SOIC
LEAD-DW0016 x 16
