ArakniD/foxbms/hardware/datasheets/Imports/DBQ0016A.stp

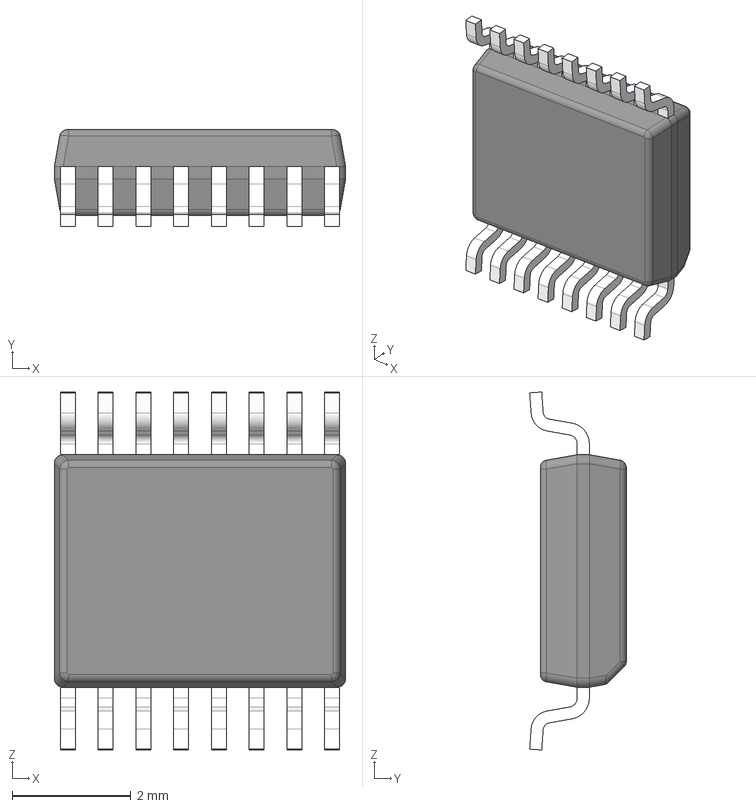
[picture p23: CAD file, 2019-07-09]
hardware/datasheets/Imports/DBQ0016A.stp
4.90 x 1.63 x 6.02 mm
BODY-SO
LEAD-DBQ0016B x 16
