ArakniD/foxbms/hardware/datasheets/User Library-AQY280S.step

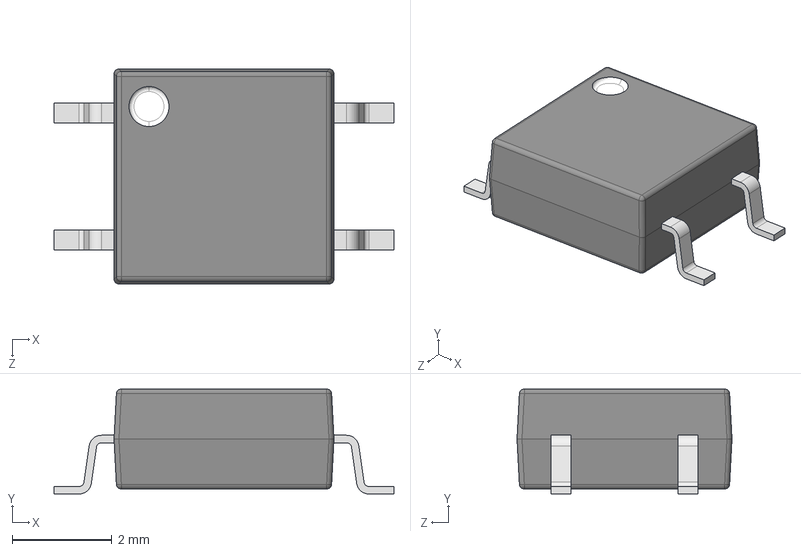
[picture p24: CAD file, 2019-07-09]
hardware/datasheets/User Library-AQY280S.step
6.80 x 2.10 x 4.30 mm
