ArakniD/foxbms/hardware/datasheets/pd1a_aqy27_a.dxf

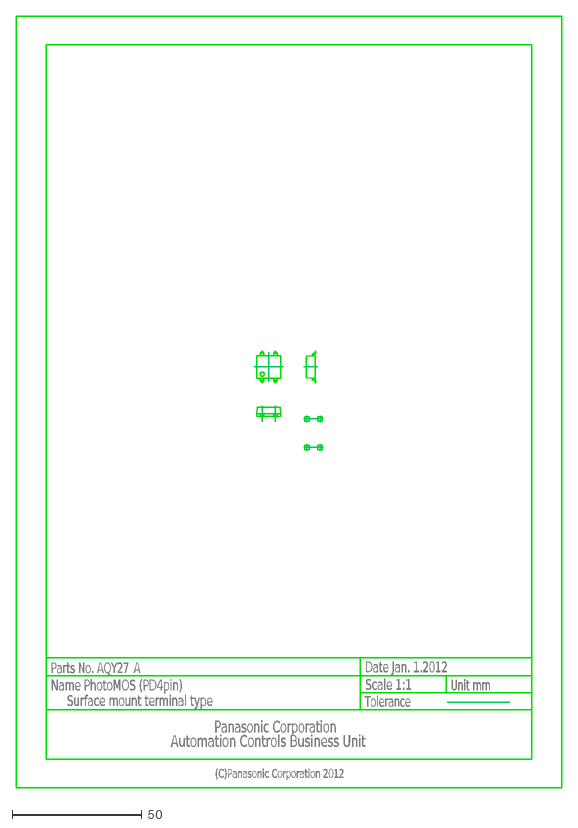
[picture p25: CAD file, 2019-07-09]
hardware/datasheets/pd1a_aqy27_a.dxf
Name PhotoMOS (PD4pin) Surface mount terminal type
Parts No. AQY27_A
(C)Panasonic Corporation 2012
Date Jan. 1.2012
Scale 1:1
Unit mm
Tolerance
Automation Controls Business Unit
Panasonic Corporation
