ArakniD/foxbms/hardware/hw-master/v1.0.6-2/Fabrication/pdf/board-stack.PDF

Layer | Board Layer Stack | Name | Material | Thickness Constant

# Board Stack Report

Stack Up | Layer Stack

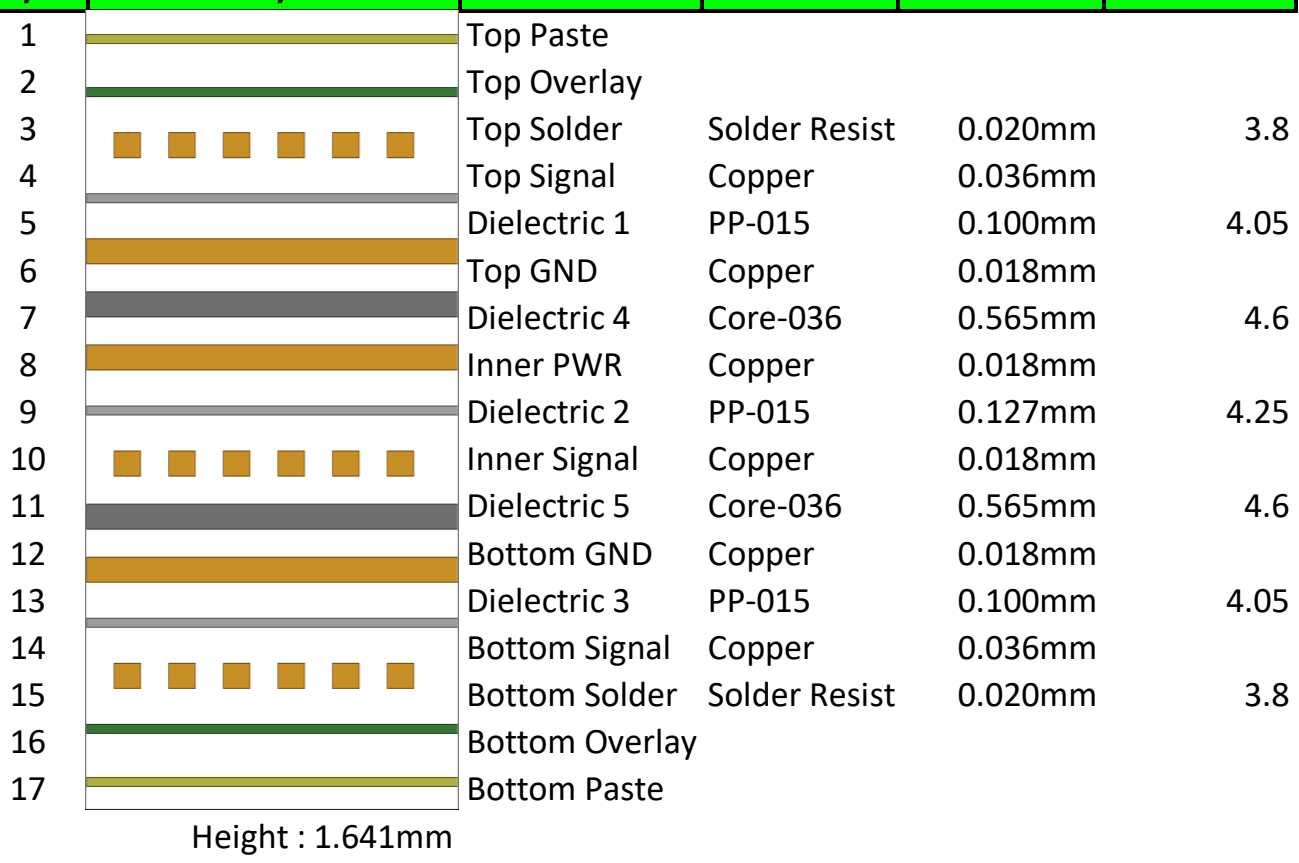
[picture p27: figure]
Top Paste; Top Overlay; Top Solder; Solder Resist; Top Signal; Copper; Dielectric 1; Top GND; Dielectric 4; Core-036; Inner PWR; Dielectric 2; Inner Signal; Dielectric 5; Bottom GND; Dielectric 3; Bottom Signal Copper; Bottom Solder Solder Resist; Bottom Overlay; Bottom Paste; Height : 1.641mm
