ArakniD/foxbms/embedded-software/mcu-common/src/module/ltc/ltc.c

/**
 *
 * @copyright &copy; 2010 - 2019, Fraunhofer-Gesellschaft zur Foerderung der
 *  angewandten Forschung e.V. All rights reserved.
 *
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
 * We kindly request you to use one or more of the following phrases to refer
 * to foxBMS in your hardware, software, documentation or advertising
 * materials:
 *
 * &Prime;This product uses parts of foxBMS&reg;&Prime;
 *
 * &Prime;This product includes parts of foxBMS&reg;&Prime;
 *
 * &Prime;This product is derived from foxBMS&reg;&Prime;
 *
 */

/**
 * @file    ltc.c
 * @author  foxBMS Team
 * @date    01.09.2015 (date of creation)
 * @ingroup DRIVERS
 * @prefix  LTC
 *
 * @brief   Driver for the LTC monitoring chip.
 *
 */

/*================== Includes =============================================*/
#include "ltc.h"

#include "database.h"
#include "diag.h"
#include "ltc_pec.h"
#include "os.h"
#include "slaveplausibility.h"

/*================== Macros and Definitions ===============================*/

/**
 * TI port expander register addresses
 *
 */

#define LTC_PORT_EXPANDER_TI_INPUT_REG_ADR    0x00
#define LTC_PORT_EXPANDER_TI_OUTPUT_REG_ADR   0x01
#define LTC_PORT_EXPANDER_TI_CONFIG_REG_ADR   0x03

/**
 * LTC COMM definitions
 */

#define LTC_ICOM_START              0x60
#define LTC_ICOM_STOP               0x10
#define LTC_ICOM_BLANK              0x00
#define LTC_ICOM_NO_TRANSMIT        0x70
#define LTC_FCOM_MASTER_ACK         0x00
#define LTC_FCOM_MASTER_NACK        0x08
#define LTC_FCOM_MASTER_NACK_STOP   0x09

#define LTC_MAX_SUPPORTED_CELLS         12

/**
 * Saves the last state and the last substate
 */
#define LTC_SAVELASTSTATES()    ltc_state.laststate = ltc_state.state; \
                                ltc_state.lastsubstate = ltc_state.substate

/*================== Constant and Variable Definitions ====================*/

static uint8_t ltc_used_cells_index = 0;

static DATA_BLOCK_CELLVOLTAGE_s ltc_cellvoltage;
static DATA_BLOCK_CELLTEMPERATURE_s ltc_celltemperature;
static DATA_BLOCK_MINMAX_s ltc_minmax;
static DATA_BLOCK_BALANCING_FEEDBACK_s ltc_balancing_feedback;
static DATA_BLOCK_USER_MUX_s ltc_user_mux;
static DATA_BLOCK_BALANCING_CONTROL_s ltc_balancing_control;
static DATA_BLOCK_SLAVE_CONTROL_s ltc_slave_control;
static DATA_BLOCK_ALLGPIOVOLTAGE_s ltc_allgpiovoltage;
static DATA_BLOCK_OPENWIRE_s ltc_openwire;
static uint16_t ltc_openwire_pup_buffer[BS_NR_OF_BAT_CELLS];
static uint16_t ltc_openwire_pdown_buffer[BS_NR_OF_BAT_CELLS];
static int32_t ltc_openwire_delta[BS_NR_OF_BAT_CELLS];

static LTC_ERRORTABLE_s LTC_ErrorTable[LTC_N_LTC];  /* init in LTC_ResetErrorTable-function */


static LTC_STATE_s ltc_state = {
    .timer                   = 0,
    .statereq                = LTC_STATE_NO_REQUEST,
    .state                   = LTC_STATEMACH_UNINITIALIZED,
    .substate                = 0,
    .laststate               = LTC_STATEMACH_UNINITIALIZED,
    .lastsubstate            = 0,
    .adcModereq              = LTC_ADCMODE_FAST_DCP0,
    .adcMode                 = LTC_ADCMODE_FAST_DCP0,
    .adcMeasChreq            = LTC_ADCMEAS_UNDEFINED,
    .adcMeasCh               = LTC_ADCMEAS_UNDEFINED,
    .numberOfMeasuredMux     = 32,
    .triggerentry            = 0,
    .ErrRetryCounter         = 0,
    .ErrRequestCounter       = 0,
    .VoltageSampleTime       = 0,
    .muxSampleTime           = 0,
    .commandDataTransferTime = 3,
    .commandTransferTime     = 3,
    .gpioClocksTransferTime  = 3,
    .muxmeas_seqptr          = NULL_PTR,
    .muxmeas_seqendptr       = NULL_PTR,
    .muxmeas_nr_end          = 0,
    .first_measurement_made  = FALSE,
    .ltc_muxcycle_finished   = E_NOT_OK,
    .check_spi_flag          = FALSE,
    .balance_control_done     = FALSE,
};

static const uint8_t ltc_cmdDummy[1]={0x00};
static const uint8_t ltc_cmdWRCFG[4]={0x00, 0x01, 0x3D, 0x6E};
static const uint8_t ltc_cmdWRCFG2[4]={0x00, 0x24, 0xB1, 0x9E};

static const uint8_t ltc_cmdRDCVA[4] = {0x00, 0x04, 0x07, 0xC2};
static const uint8_t ltc_cmdRDCVB[4] = {0x00, 0x06, 0x9A, 0x94};
static const uint8_t ltc_cmdRDCVC[4] = {0x00, 0x08, 0x5E, 0x52};
static const uint8_t ltc_cmdRDCVD[4] = {0x00, 0x0A, 0xC3, 0x04};
static const uint8_t ltc_cmdRDCVE[4] = {0x00, 0x09, 0xD5, 0x60};
static const uint8_t ltc_cmdRDCVF[4] = {0x00, 0x0B, 0x48, 0x36};
static const uint8_t ltc_cmdWRCOMM[4] = {0x07, 0x21, 0x24, 0xB2};
static const uint8_t ltc_cmdSTCOMM[4] = {0x07, 0x23, 0xB9, 0xE4};
static const uint8_t ltc_cmdRDCOMM[4] = {0x07, 0x22, 0x32, 0xD6};
static const uint8_t ltc_cmdRDAUXA[4] = {0x00, 0x0C, 0xEF, 0xCC};
static const uint8_t ltc_cmdRDAUXB[4] = {0x00, 0x0E, 0x72, 0x9A};
static const uint8_t ltc_cmdRDAUXC[4] = {0x00, 0x0D, 0x64, 0xFE};
static const uint8_t ltc_cmdRDAUXD[4] = {0x00, 0x0F, 0xF9, 0xA8};

/* static const uint8_t ltc_cmdMUTE[4] = {0x00, 0x28, 0xE8, 0x0E};                    !< MUTE discharging via S pins */
/* static const uint8_t ltc_cmdUNMUTE[4] = {0x00, 0x29, 0x63, 0x3C};                  !< UN-MUTE discharging via S pins */

/* LTC I2C commands */
/* static const uint8_t ltc_I2CcmdDummy[6] = {0x7F, 0xF9, 0x7F, 0xF9, 0x7F, 0xF9};      !< dummy command (no transmit) */

static const uint8_t ltc_I2CcmdTempSens0[6] = {0x69, 0x08, 0x00, 0x09, 0x7F, 0xF9};  /*!< sets the internal data pointer of the temperature sensor (address 0x48) to 0x00 */
static const uint8_t ltc_I2CcmdTempSens1[6] = {0x69, 0x18, 0x0F, 0xF0, 0x0F, 0xF9};  /*!< reads two data bytes from the temperature sensor */

static const uint8_t ltc_I2CcmdPortExpander1[6] = {0x64, 0x18, 0x0F, 0xF9, 0x7F, 0xF9};  /*!< reads one data byte from the port expander */

/* Cells */
static const uint8_t ltc_cmdADCV_normal_DCP0[4] = {0x03, 0x60, 0xF4, 0x6C};        /*!< All cells, normal mode, discharge not permitted (DCP=0)    */
static const uint8_t ltc_cmdADCV_normal_DCP1[4] = {0x03, 0x70, 0xAF, 0x42};        /*!< All cells, normal mode, discharge permitted (DCP=1)        */
static const uint8_t ltc_cmdADCV_filtered_DCP0[4] = {0x03, 0xE0, 0xB0, 0x4A};      /*!< All cells, filtered mode, discharge not permitted (DCP=0)  */
static const uint8_t ltc_cmdADCV_filtered_DCP1[4] = {0x03, 0xF0, 0xEB, 0x64};      /*!< All cells, filtered mode, discharge permitted (DCP=1)      */
static const uint8_t ltc_cmdADCV_fast_DCP0[4] = {0x02, 0xE0, 0x38, 0x06};          /*!< All cells, fast mode, discharge not permitted (DCP=0)      */
static const uint8_t ltc_cmdADCV_fast_DCP1[4] = {0x02, 0xF0, 0x63, 0x28};          /*!< All cells, fast mode, discharge permitted (DCP=1)          */
static const uint8_t ltc_cmdADCV_fast_DCP0_twocells[4] = {0x02, 0xE1, 0xb3, 0x34}; /*!< Two cells (1 and 7), fast mode, discharge not permitted (DCP=0) */

/* GPIOs  */
static const uint8_t ltc_cmdADAX_normal_GPIO1[4] = {0x05, 0x61, 0x58, 0x92};      /*!< Single channel, GPIO 1, normal mode   */
static const uint8_t ltc_cmdADAX_filtered_GPIO1[4] = {0x05, 0xE1, 0x1C, 0xB4};    /*!< Single channel, GPIO 1, filtered mode */
static const uint8_t ltc_cmdADAX_fast_GPIO1[4] = {0x04, 0xE1, 0x94, 0xF8};        /*!< Single channel, GPIO 1, fast mode     */
static const uint8_t ltc_cmdADAX_normal_GPIO2[4] = {0x05, 0x62, 0x4E, 0xF6};      /*!< Single channel, GPIO 2, normal mode   */
static const uint8_t ltc_cmdADAX_filtered_GPIO2[4] = {0x05, 0xE2, 0x0A, 0xD0};    /*!< Single channel, GPIO 2, filtered mode */
static const uint8_t ltc_cmdADAX_fast_GPIO2[4] = {0x04, 0xE2, 0x82, 0x9C};        /*!< Single channel, GPIO 2, fast mode     */
static const uint8_t ltc_cmdADAX_normal_GPIO3[4] = {0x05, 0x63, 0xC5, 0xC4};      /*!< Single channel, GPIO 3, normal mode   */
static const uint8_t ltc_cmdADAX_filtered_GPIO3[4] = {0x05, 0xE3, 0x81, 0xE2};    /*!< Single channel, GPIO 3, filtered mode */
static const uint8_t ltc_cmdADAX_fast_GPIO3[4] = {0x04, 0xE3, 0x09, 0xAE};        /*!< Single channel, GPIO 3, fast mode     */
/* static const uint8_t ltc_cmdADAX_normal_GPIO4[4] = {0x05, 0x64, 0x62, 0x3E};      !< Single channel, GPIO 4, normal mode   */
/* static const uint8_t ltc_cmdADAX_filtered_GPIO4[4] = {0x05, 0xE4, 0x26, 0x18};    !< Single channel, GPIO 4, filtered mode */
/* static const uint8_t ltc_cmdADAX_fast_GPIO4[4] = {0x04, 0xE4, 0xAE, 0x54};        !< Single channel, GPIO 4, fast mode     */
/* static const uint8_t ltc_cmdADAX_normal_GPIO5[4] = {0x05, 0x65, 0xE9, 0x0C};      !< Single channel, GPIO 5, normal mode   */
/* static const uint8_t ltc_cmdADAX_filtered_GPIO5[4] = {0x05, 0xE5, 0xAD, 0x2A};    !< Single channel, GPIO 5, filtered mode */
/* static const uint8_t ltc_cmdADAX_fast_GPIO5[4] = {0x04, 0xE5, 0x25, 0x66};        !< Single channel, GPIO 5, fast mode     */
static const uint8_t ltc_cmdADAX_normal_ALLGPIOS[4] = {0x05, 0x60, 0xD3, 0xA0};   /*!< All channels, normal mode             */
static const uint8_t ltc_cmdADAX_filtered_ALLGPIOS[4] = {0x05, 0xE0, 0x97, 0x86}; /*!< All channels, filtered mode           */
static const uint8_t ltc_cmdADAX_fast_ALLGPIOS[4] = {0x04, 0xE0, 0x1F, 0xCA};     /*!< All channels, fast mode               */

/* Open-wire */
static const uint8_t ltc2_BC_cmdADOW_PUP_normal_DCP0[4] = {0x03, 0x68, 0x1C, 0x62};    /*!< Broadcast, Pull-up current, All cells, normal mode, discharge not permitted (DCP=0)   */
static const uint8_t ltc2_BC_cmdADOW_PDOWN_normal_DCP0[4] = {0x03, 0x28, 0xFB, 0xE8};  /*!< Broadcast, Pull-down current, All cells, normal mode, discharge not permitted (DCP=0) */
static const uint8_t ltc2_BC_cmdADOW_PUP_filtered_DCP0[4] = {0x03, 0xE8, 0x1C, 0x62};    /*!< Broadcast, Pull-up current, All cells, filtered mode, discharge not permitted (DCP=0)   */
static const uint8_t ltc2_BC_cmdADOW_PDOWN_filtered_DCP0[4] = {0x03, 0xA8, 0xFB, 0xE8};  /*!< Broadcast, Pull-down current, All cells, filtered mode, discharge not permitted (DCP=0) */


static uint8_t ltc_RXPECbuffer[LTC_N_BYTES_FOR_DATA_TRANSMISSION];
static uint8_t ltc_TXPECbuffer[LTC_N_BYTES_FOR_DATA_TRANSMISSION];
static uint8_t ltc_TXBuffer[LTC_N_BYTES_FOR_DATA_TRANSMISSION_DATA_ONLY];

static uint8_t ltc_TXBufferClock[4+9];
static uint8_t ltc_TXPECBufferClock[4+9];


/*================== Function Prototypes ==================================*/

static void LTC_Initialize_Database(void);
static void LTC_SaveBalancingFeedback(uint8_t *DataBufferSPI_RX);
static void LTC_Get_BalancingControlValues(void);
static void LTC_StateTransition(LTC_STATEMACH_e state, uint8_t substate, uint16_t timer_ms);
static void LTC_CondBasedStateTransition(STD_RETURN_TYPE_e retVal, DIAG_CH_ID_e diagCode, uint8_t state_ok, uint8_t substate_ok, uint16_t timer_ms_ok, uint8_t state_nok, uint8_t substate_nok, uint16_t timer_ms_nok);

static STD_RETURN_TYPE_e LTC_BalanceControl(uint8_t registerSet);

static void LTC_ResetErrorTable(void);
static STD_RETURN_TYPE_e LTC_Init(void);

static STD_RETURN_TYPE_e LTC_StartVoltageMeasurement(LTC_ADCMODE_e adcMode, LTC_ADCMEAS_CHAN_e  adcMeasCh);
static STD_RETURN_TYPE_e LTC_StartGPIOMeasurement(LTC_ADCMODE_e adcMode, LTC_ADCMEAS_CHAN_e  adcMeasCh);
static STD_RETURN_TYPE_e LTC_StartOpenWireMeasurement(LTC_ADCMODE_e adcMode, uint8_t PUP);

static uint16_t LTC_Get_MeasurementTCycle(LTC_ADCMODE_e adcMode, LTC_ADCMEAS_CHAN_e  adcMeasCh);
static void LTC_SaveRXtoVoltagebuffer(uint8_t registerSet, uint8_t *rxBuffer);
static void LTC_SaveRXtoGPIOBuffer(uint8_t registerSet, uint8_t *rxBuffer);

static STD_RETURN_TYPE_e LTC_RX_PECCheck(uint8_t *DataBufferSPI_RX_with_PEC);
static STD_RETURN_TYPE_e LTC_RX(uint8_t *Command, uint8_t *DataBufferSPI_RX_with_PEC);
static STD_RETURN_TYPE_e LTC_TX(uint8_t *Command, uint8_t *DataBufferSPI_TX, uint8_t *DataBufferSPI_TX_with_PEC);
static void LTC_SetMUXChCommand(uint8_t *DataBufferSPI_TX, uint8_t mux, uint8_t channel);
static uint8_t LTC_SendEEPROMReadCommand(uint8_t *DataBufferSPI_TX, uint8_t *DataBufferSPI_TX_with_PEC, uint8_t step);
static void LTC_SetEEPROMReadCommand(uint8_t step, uint8_t *DataBufferSPI_TX);
static void LTC_EEPROMSaveReadValue(uint8_t *rxBuffer);
static uint8_t LTC_SendEEPROMWriteCommand(uint8_t *DataBufferSPI_TX, uint8_t *DataBufferSPI_TX_with_PEC, uint8_t step);
static void LTC_SetEEPROMWriteCommand(uint8_t step, uint8_t *DataBufferSPI_TX);
static uint8_t LTC_SetMuxChannel(uint8_t *DataBufferSPI_TX, uint8_t *DataBufferSPI_TX_with_PEC, uint8_t mux, uint8_t channel);
static uint8_t LTC_SetPortExpander(uint8_t *DataBufferSPI_TX, uint8_t *DataBufferSPI_TX_with_PEC);
static void LTC_PortExpanderSaveValues(uint8_t *rxBuffer);
static void LTC_TempSensSaveTemp(uint8_t *rxBuffer);
static uint8_t LTC_SetPortExpanderDirection_TI(LTC_PORT_EXPANDER_TI_DIRECTION_e direction, uint8_t *DataBufferSPI_TX, uint8_t *DataBufferSPI_TX_with_PEC);
static uint8_t LTC_SetPortExpander_Output_TI(uint8_t *DataBufferSPI_TX, uint8_t *DataBufferSPI_TX_with_PEC);
static uint8_t LTC_GetPortExpander_Input_TI(uint8_t step, uint8_t *DataBufferSPI_TX, uint8_t *DataBufferSPI_TX_with_PEC);
static void LTC_PortExpanderSaveValues_TI(uint8_t *rxBuffer);

static STD_RETURN_TYPE_e LTC_I2CClock(uint8_t *DataBufferSPI_TX, uint8_t *DataBufferSPI_TX_with_PEC);
static STD_RETURN_TYPE_e LTC_Send_I2C_Command(uint8_t *DataBufferSPI_TX, uint8_t *DataBufferSPI_TX_with_PEC, uint8_t *cmd_data);

static uint8_t LTC_I2CCheckACK(uint8_t *DataBufferSPI_RX, int mux);

static void LTC_SaveMuxMeasurement(uint8_t *DataBufferSPI_RX, LTC_MUX_CH_CFG_s  *muxseqptr);


static uint32_t LTC_GetSPIClock(void);
static void LTC_SetTransferTimes(void);

static LTC_RETURN_TYPE_e LTC_CheckStateRequest(LTC_STATE_REQUEST_e statereq);

static STD_RETURN_TYPE_e LTC_TimerElapsedAndSPITransmitOngoing(uint16_t timer);

/*================== Function Implementations =============================*/

/*================== Public functions =====================================*/

/*================== Static functions =====================================*/
/**
 * @brief   in the database, initializes the fields related to the LTC drivers.
 *
 * This function loops through all the LTC-related data fields in the database
 * and sets them to 0. It should be called in the initialization or re-initialization
 * routine of the LTC driver.
 */
static void LTC_Initialize_Database(void) {
    uint16_t i = 0;

    ltc_cellvoltage.state = 0;
    ltc_cellvoltage.timestamp = 0;
    ltc_minmax.voltage_min = 0;
    ltc_minmax.voltage_max = 0;
    ltc_minmax.voltage_module_number_min = 0;
    ltc_minmax.voltage_module_number_max = 0;
    ltc_minmax.voltage_cell_number_min = 0;
    ltc_minmax.voltage_cell_number_max = 0;
    for (i=0; i < BS_NR_OF_BAT_CELLS; i++) {
        ltc_cellvoltage.voltage[i] = 0;
        ltc_openwire_pup_buffer[i] = 0;
        ltc_openwire_pdown_buffer[i] = 0;
        ltc_openwire_delta[i] = 0;
    }

    ltc_celltemperature.state = 0;
    ltc_celltemperature.timestamp = 0;
    ltc_minmax.temperature_min = 0;
    ltc_minmax.temperature_max = 0;
    ltc_minmax.temperature_module_number_min = 0;
    ltc_minmax.temperature_module_number_max = 0;
    ltc_minmax.temperature_sensor_number_min = 0;
    ltc_minmax.temperature_sensor_number_max = 0;
    for (i=0; i < BS_NR_OF_TEMP_SENSORS; i++) {
        ltc_celltemperature.temperature[i] = 0;
    }

    ltc_balancing_feedback.state = 0;
    ltc_balancing_feedback.timestamp = 0;
    ltc_balancing_control.state = 0;
    ltc_balancing_control.timestamp = 0;
    for (i=0; i < BS_NR_OF_BAT_CELLS; i++) {
        ltc_balancing_feedback.value[i] = 0;
        ltc_balancing_control.balancing_state[i] = 0;
    }

    ltc_slave_control.state = 0;
    ltc_slave_control.timestamp = 0;
    ltc_slave_control.previous_timestamp = 0;
    for (i=0; i < BS_NR_OF_MODULES; i++) {
        ltc_slave_control.io_value_in[i] = 0;
        ltc_slave_control.io_value_out[i] = 0;
        ltc_slave_control.external_sensor_temperature[i] = 0;
        ltc_slave_control.eeprom_value_read[i] = 0;
        ltc_slave_control.eeprom_value_write[i] = 0;
    }
    ltc_slave_control.eeprom_read_address_last_used = 0xFFFFFFFF;
    ltc_slave_control.eeprom_read_address_to_use = 0xFFFFFFFF;
    ltc_slave_control.eeprom_write_address_last_used = 0xFFFFFFFF;
    ltc_slave_control.eeprom_write_address_to_use = 0xFFFFFFFF;

    ltc_allgpiovoltage.timestamp = 0;
    ltc_allgpiovoltage.previous_timestamp = 0;
    ltc_allgpiovoltage.state = 0;
    for (i=0; i < BS_NR_OF_MODULES * BS_NR_OF_GPIOS_PER_MODULE; i++) {
        ltc_allgpiovoltage.gpiovoltage[i] = 0;
    }

    for (i = 0; i < BS_NR_OF_MODULES * (BS_NR_OF_BAT_CELLS_PER_MODULE+1); i++) {
        ltc_openwire.openwire[i] = 0;
    }
    ltc_openwire.state = 0;

    DB_WriteBlock(&ltc_cellvoltage, DATA_BLOCK_ID_CELLVOLTAGE);
    DB_WriteBlock(&ltc_celltemperature, DATA_BLOCK_ID_CELLTEMPERATURE);
    DB_WriteBlock(&ltc_minmax, DATA_BLOCK_ID_MINMAX);
    DB_WriteBlock(&ltc_balancing_feedback, DATA_BLOCK_ID_BALANCING_FEEDBACK_VALUES);
    DB_WriteBlock(&ltc_balancing_control, DATA_BLOCK_ID_BALANCING_CONTROL_VALUES);
    DB_WriteBlock(&ltc_slave_control, DATA_BLOCK_ID_SLAVE_CONTROL);
    DB_WriteBlock(&ltc_openwire, DATA_BLOCK_ID_OPEN_WIRE);

    for (i=0; i < (8*2*BS_NR_OF_MODULES); i++) {
        ltc_user_mux.value[i] = 0;
    }
    ltc_user_mux.previous_timestamp = 0;
    ltc_user_mux.timestamp = 0;
    ltc_user_mux.state = 0;
}

/**
 * @brief   function for setting LTC_Trigger state transitions
 *
 * @param  state:    state to transition into
 * @param  substate: substate to transition into
 * @param  timer_ms: transition into state, substate after timer elapsed
 */
static void LTC_StateTransition(LTC_STATEMACH_e state, uint8_t substate, uint16_t timer_ms) {
        ltc_state.state = state;
        ltc_state.substate = substate;
        ltc_state.timer = timer_ms;
}

/**
 * @brief   condition-based state transition depending on retVal
 *
 * If retVal is E_OK, after timer_ms_ok is elapsed the LTC statemachine will
 * transition into state_ok and substate_ok, otherwise after timer_ms_nok the
 * statemachine will transition to state_nok and substate_nok. Depending on
 * value of retVal the corresponding diagnosis entry will be called.
 *
 * @param  retVal:       condition to determine if statemachine will transition into ok or nok states
 * @param  diagCode:     symbolic IDs for diagnosis entry, called with DIAG_EVENT_OK if retVal is E_OK, DIAG_EVENT_NOK otherwise
 * @param  state_ok      state to transition into if retVal is E_OK
 * @param  substate_ok:  substate to transition into if retVal is E_OK
 * @param  timer_ms_ok:  transition into state_ok, substate_ok after timer_ms_ok elapsed
 * @param  state_nok:    state to transition into if retVal is E_NOT_OK
 * @param  substate_nok: substate to transition into if retVal is E_NOT_OK
 * @param  timer_ms_nok: transition into state_nok, substate_nok after timer_ms_nok elapsed
 */
static void LTC_CondBasedStateTransition(STD_RETURN_TYPE_e retVal, DIAG_CH_ID_e diagCode, uint8_t state_ok, uint8_t substate_ok, uint16_t timer_ms_ok, uint8_t state_nok, uint8_t substate_nok, uint16_t timer_ms_nok) {
    if ((retVal != E_OK)) {
        DIAG_Handler(diagCode, DIAG_EVENT_NOK, 0);
        LTC_StateTransition(state_nok, substate_nok, timer_ms_nok);
    } else {
        DIAG_Handler(diagCode, DIAG_EVENT_OK, 0);
        LTC_StateTransition(state_ok, substate_ok, timer_ms_ok);
    }
}

/**
 * @brief   stores the measured voltages in the database.
 *
 * This function loops through the data of all modules in the LTC daisy-chain that are
 * stored in the LTC_CellVoltages buffer and writes them in the database.
 * At each write iteration, the variable named "state" and related to voltages in the
 * database is incremented.
 *
 */
extern void LTC_SaveVoltages(void) {
    uint16_t i = 0;
    uint16_t j = 0;
    uint16_t min = UINT16_MAX;
    uint16_t max = 0;
    uint32_t mean = 0;
    uint32_t sum = 0;
    uint8_t module_number_min = 0;
    uint8_t module_number_max = 0;
    uint8_t cell_number_min = 0;
    uint8_t cell_number_max = 0;
    uint16_t nrValidCellVoltages = 0;
    STD_RETURN_TYPE_e retval_PLminmax = E_NOT_OK;
    STD_RETURN_TYPE_e retval_PLspread = E_NOT_OK;
    STD_RETURN_TYPE_e result = E_NOT_OK;

    /* Perform min/max voltage plausibility check */
    retval_PLminmax = PL_CheckVoltageMinMax(&ltc_cellvoltage);

    /* Use only valid cell voltages for calculating mean voltage */
    for (i=0; i < BS_NR_OF_MODULES; i++) {
        for (j=0; j < BS_NR_OF_BAT_CELLS_PER_MODULE; j++) {
            if ((ltc_cellvoltage.valid_volt[i] & (0x01 << j)) == 0) {
                /* Cell voltage is valid -> use this voltage for subsequent calculations */
                nrValidCellVoltages++;
                sum += ltc_cellvoltage.voltage[i*(BS_NR_OF_BAT_CELLS_PER_MODULE)+j];
                if (ltc_cellvoltage.voltage[i*(BS_NR_OF_BAT_CELLS_PER_MODULE)+j] < min) {
                    min = ltc_cellvoltage.voltage[i*(BS_NR_OF_BAT_CELLS_PER_MODULE)+j];
                    module_number_min = i;
                    cell_number_min = j;
                }
                if (ltc_cellvoltage.voltage[i*(BS_NR_OF_BAT_CELLS_PER_MODULE)+j] > max) {
                    max = ltc_cellvoltage.voltage[i*(BS_NR_OF_BAT_CELLS_PER_MODULE)+j];
                    module_number_max = i;
                    cell_number_max = j;
                }
            }
        }
    }

    ltc_cellvoltage.packVoltage_mV = sum;

    /* Prevent division by 0, if all cell voltages are invalid */
    if (nrValidCellVoltages > 0) {
        mean = sum/nrValidCellVoltages;
    }

    /* Perform voltage spread plausibility check */
    retval_PLspread = PL_CheckVoltageSpread(&ltc_cellvoltage, mean);

    /* Set flag if plausibility error detected */
    if ((retval_PLminmax == E_OK) && (retval_PLspread == E_OK)) {
        result = E_OK;
    }
    DIAG_checkEvent(result, DIAG_CH_PLAUSIBILITY_CELL_VOLTAGE, 0);

    ltc_cellvoltage.state++;
    ltc_minmax.state++;
    ltc_minmax.voltage_mean = mean;
    ltc_minmax.previous_voltage_min = ltc_minmax.voltage_min;
    ltc_minmax.voltage_min = min;
    ltc_minmax.voltage_module_number_min = module_number_min;
    ltc_minmax.voltage_cell_number_min = cell_number_min;
    ltc_minmax.previous_voltage_max = ltc_minmax.voltage_max;
    ltc_minmax.voltage_max = max;
    ltc_minmax.voltage_module_number_max = module_number_max;
    ltc_minmax.voltage_cell_number_max = cell_number_max;

    DB_WriteBlock(&ltc_cellvoltage, DATA_BLOCK_ID_CELLVOLTAGE);
    DB_WriteBlock(&ltc_minmax, DATA_BLOCK_ID_MINMAX);
}

/**
 * @brief   stores the measured temperatures and the measured multiplexer feedbacks in the database.
 *
 * This function loops through the temperature and multiplexer feedback data of all modules
 * in the LTC daisy-chain that are stored in the LTC_MultiplexerVoltages buffer and writes
 * them in the database.
 * At each write iteration, the variables named "state" and related to temperatures and multiplexer feedbacks
 * in the database are incremented.
 *
 */
extern void LTC_SaveTemperatures(void) {
    uint16_t i = 0;
    uint16_t j = 0;
    int16_t min = INT16_MAX;
    int16_t max = INT16_MIN;
    int32_t sum = 0;
    float mean = 0;
    uint8_t module_number_min = 0;
    uint8_t module_number_max = 0;
    uint8_t sensor_number_min = 0;
    uint8_t sensor_number_max = 0;
    STD_RETURN_TYPE_e retval_PL  = E_NOT_OK;
    uint16_t nrValidTemperatures = 0;

    /* Perform plausibility check */
    retval_PL = PL_CheckTempMinMax(&ltc_celltemperature);
    /* Set flag if plausibility error detected */
    DIAG_checkEvent(retval_PL, DIAG_CH_PLAUSIBILITY_CELL_TEMP, 0);

    for (i=0; i < BS_NR_OF_MODULES; i++) {
        for (j=0; j < BS_NR_OF_TEMP_SENSORS_PER_MODULE; j++) {
            if ((ltc_celltemperature.valid_temperature[i] & (0x01 << j)) == 0) {
                /* Cell voltage is valid -> use this voltage for subsequent calculations */
                nrValidTemperatures++;
                sum += ltc_celltemperature.temperature[i*(BS_NR_OF_TEMP_SENSORS_PER_MODULE)+j];
                if (ltc_celltemperature.temperature[i*(BS_NR_OF_TEMP_SENSORS_PER_MODULE)+j] < min) {
                    min = ltc_celltemperature.temperature[i*(BS_NR_OF_TEMP_SENSORS_PER_MODULE)+j];
                    module_number_min = i;
                    sensor_number_min = j;
                }
                if (ltc_celltemperature.temperature[i*(BS_NR_OF_TEMP_SENSORS_PER_MODULE)+j] > max) {
                    max = ltc_celltemperature.temperature[i*(BS_NR_OF_TEMP_SENSORS_PER_MODULE)+j];
                    module_number_max = i;
                    sensor_number_max = j;
                }
            }
        }
    }

    /* Prevent division by 0, if all temperatues are invalid */
    if (nrValidTemperatures > 0) {
        mean = sum/nrValidTemperatures;
    }

    ltc_celltemperature.state++;
    ltc_minmax.state++;
    ltc_minmax.temperature_mean = mean;
    ltc_minmax.temperature_min = min;
    ltc_minmax.temperature_module_number_min = module_number_min;
    ltc_minmax.temperature_sensor_number_min = sensor_number_min;
    ltc_minmax.temperature_max = max;
    ltc_minmax.temperature_module_number_max = module_number_max;
    ltc_minmax.temperature_sensor_number_max = sensor_number_max;
    DB_WriteBlock(&ltc_celltemperature, DATA_BLOCK_ID_CELLTEMPERATURE);
    DB_WriteBlock(&ltc_minmax, DATA_BLOCK_ID_MINMAX);
}

/**
 * @brief   stores the measured GPIOs in the database.
 *
 * This function loops through the data of all modules in the LTC daisy-chain that are
 * stored in the ltc_allgpiovoltage buffer and writes them in the database.
 * At each write iteration, the variable named "state" and related to voltages in the
 * database is incremented.
 *
 */
extern void LTC_SaveAllGPIOMeasurement(void) {
    ltc_allgpiovoltage.state++;
    DB_WriteBlock(&ltc_allgpiovoltage, DATA_BLOCK_ID_ALLGPIOVOLTAGE);
}

/**
 * @brief   stores the measured balancing feedback values in the database.
 *
 * This function stores the global balancing feedback value measured on GPIO3 of the LTC into the database
 *
 */
static void LTC_SaveBalancingFeedback(uint8_t *DataBufferSPI_RX) {
    uint16_t i = 0;
    uint16_t val_i = 0;

    for (i=0; i < LTC_N_LTC; i++) {
        val_i = DataBufferSPI_RX[8+1*i*8] | (DataBufferSPI_RX[8+1*i*8+1] << 8);    /* raw value, GPIO3 */

            ltc_balancing_feedback.value[i] = val_i;
    }

    ltc_balancing_feedback.state++;
    DB_WriteBlock(&ltc_balancing_feedback, DATA_BLOCK_ID_BALANCING_FEEDBACK_VALUES);
}


/**
 * @brief   gets the balancing orders from the database.
 *
 * This function gets the balancing control from the database. Balancing control
 * is set by the BMS. The LTC driver only executes the balancing orders.
 */
static void LTC_Get_BalancingControlValues(void) {
    DB_ReadBlock(&ltc_balancing_control, DATA_BLOCK_ID_BALANCING_CONTROL_VALUES);
}



/**
 * @brief   re-entrance check of LTC state machine trigger function
 *
 * This function is not re-entrant and should only be called time- or event-triggered.
 * It increments the triggerentry counter from the state variable ltc_state.
 * It should never be called by two different processes, so if it is the case, triggerentry
 * should never be higher than 0 when this function is called.
 *
 *
 * @return  retval  0 if no further instance of the function is active, 0xff else
 *
 */
uint8_t LTC_CheckReEntrance(void) {
    uint8_t retval = 0;

    OS_TaskEnter_Critical();
    if (!ltc_state.triggerentry) {
        ltc_state.triggerentry++;
    } else {
        retval = 0xFF;    /* multiple calls of function */
    }
    OS_TaskExit_Critical();

    return (retval);
}

/**
 * @brief   gets the current state request.
 *
 * This function is used in the functioning of the LTC state machine.
 *
 * @return  retval  current state request, taken from LTC_STATE_REQUEST_e
 */
extern LTC_STATE_REQUEST_e LTC_GetStateRequest(void) {
    LTC_STATE_REQUEST_e retval = LTC_STATE_NO_REQUEST;

    OS_TaskEnter_Critical();
    retval    = ltc_state.statereq;
    OS_TaskExit_Critical();

    return (retval);
}

/**
 * @brief   gets the current state.
 *
 * This function is used in the functioning of the LTC state machine.
 *
 * @return  current state, taken from LTC_STATEMACH_e
 */
extern LTC_STATEMACH_e LTC_GetState(void) {
    return (ltc_state.state);
}

/**
 * @brief   transfers the current state request to the state machine.
 *
 * This function takes the current state request from ltc_state and transfers it to the state machine.
 * It resets the value from ltc_state to LTC_STATE_NO_REQUEST
 *
 * @param   *busIDptr       bus ID, main or backup (deprecated)
 * @param   *adcModeptr     LTC ADCmeasurement mode (fast, normal or filtered)
 * @param   *adcMeasChptr   number of channels measured for GPIOS (one at a time for multiplexers or all five GPIOs)
 *
 * @return  retVal          current state request, taken from LTC_STATE_REQUEST_e
 *
 */
LTC_STATE_REQUEST_e LTC_TransferStateRequest(uint8_t *busIDptr, LTC_ADCMODE_e *adcModeptr, LTC_ADCMEAS_CHAN_e *adcMeasChptr) {
    LTC_STATE_REQUEST_e retval = LTC_STATE_NO_REQUEST;

    OS_TaskEnter_Critical();
    retval    = ltc_state.statereq;
    *adcModeptr = ltc_state.adcModereq;
    *adcMeasChptr = ltc_state.adcMeasChreq;
    ltc_state.statereq = LTC_STATE_NO_REQUEST;
    OS_TaskExit_Critical();

    return (retval);
}

LTC_RETURN_TYPE_e LTC_SetStateRequest(LTC_STATE_REQUEST_e statereq) {
    LTC_RETURN_TYPE_e retVal = LTC_STATE_NO_REQUEST;

    OS_TaskEnter_Critical();
    retVal = LTC_CheckStateRequest(statereq);

    if (retVal == LTC_OK || retVal == LTC_BUSY_OK || retVal == LTC_OK_FROM_ERROR) {
            ltc_state.statereq   = statereq;
        }
    OS_TaskExit_Critical();

    return (retVal);
}

void LTC_Trigger(void) {
    STD_RETURN_TYPE_e retVal = E_OK;
    LTC_STATE_REQUEST_e statereq = LTC_STATE_NO_REQUEST;
    uint8_t tmpbusID = 0;
    LTC_ADCMODE_e tmpadcMode = LTC_ADCMODE_UNDEFINED;
    LTC_ADCMEAS_CHAN_e tmpadcMeasCh = LTC_ADCMEAS_UNDEFINED;

    /* Check re-entrance of function */
    if (LTC_CheckReEntrance())
        return;

    DIAG_SysMonNotify(DIAG_SYSMON_LTC_ID, 0);        /* task is running, state = ok */

    if (ltc_state.check_spi_flag == FALSE) {
        if (ltc_state.timer) {
            if (--ltc_state.timer) {
                ltc_state.triggerentry--;
                return;    /* handle state machine only if timer has elapsed */
            }
        }
    } else {
        if (SPI_IsTransmitOngoing() == TRUE) {
            if (ltc_state.timer) {
                if (--ltc_state.timer) {
                    ltc_state.triggerentry--;
                    return;    /* handle state machine only if timer has elapsed */
                }
            }
        }
    }

    switch (ltc_state.state) {
        /****************************UNINITIALIZED***********************************/
        case LTC_STATEMACH_UNINITIALIZED:
            /* waiting for Initialization Request */
            statereq = LTC_TransferStateRequest(&tmpbusID, &tmpadcMode, &tmpadcMeasCh);
            if (statereq == LTC_STATE_INIT_REQUEST) {
                LTC_SAVELASTSTATES();
                LTC_StateTransition(LTC_STATEMACH_INITIALIZATION, LTC_ENTRY_UNINITIALIZED, LTC_STATEMACH_SHORTTIME);
                ltc_state.adcMode = tmpadcMode;
                ltc_state.adcMeasCh = tmpadcMeasCh;
            } else if (statereq == LTC_STATE_NO_REQUEST) {
                /* no actual request pending */
            } else {
                ltc_state.ErrRequestCounter++;   /* illegal request pending */
            }
            break;

        /****************************INITIALIZATION**********************************/
        case LTC_STATEMACH_INITIALIZATION:

            LTC_SetTransferTimes();
            ltc_state.muxmeas_seqptr = ltc_mux_seq.seqptr;
            ltc_state.muxmeas_nr_end = ltc_mux_seq.nr_of_steps;
            ltc_state.muxmeas_seqendptr = ((LTC_MUX_CH_CFG_s *)ltc_mux_seq.seqptr)+ltc_mux_seq.nr_of_steps;  /* last sequence + 1 */

            if (ltc_state.substate == LTC_ENTRY_INITIALIZATION) {
                LTC_SAVELASTSTATES();
                retVal = LTC_SendWakeUp();        /* Send dummy byte to wake up the daisy chain */
                LTC_CondBasedStateTransition(retVal, DIAG_CH_LTC_SPI,
                                          LTC_STATEMACH_INITIALIZATION, LTC_RE_ENTRY_INITIALIZATION, LTC_STATEMACH_DAISY_CHAIN_FIRST_INITIALIZATION_TIME,
                                          LTC_STATEMACH_INITIALIZATION, LTC_ENTRY_INITIALIZATION, LTC_STATEMACH_SHORTTIME);

            } else if (ltc_state.substate == LTC_RE_ENTRY_INITIALIZATION) {
                LTC_SAVELASTSTATES();
                retVal = LTC_SendWakeUp();  /* Send dummy byte again to wake up the daisy chain */
                LTC_CondBasedStateTransition(retVal, DIAG_CH_LTC_SPI,
                                          LTC_STATEMACH_INITIALIZATION, LTC_START_INIT_INITIALIZATION, LTC_STATEMACH_DAISY_CHAIN_SECOND_INITIALIZATION_TIME,
                                          LTC_STATEMACH_INITIALIZATION, LTC_RE_ENTRY_INITIALIZATION, LTC_STATEMACH_SHORTTIME);

            } else if (ltc_state.substate == LTC_START_INIT_INITIALIZATION) {
                retVal = LTC_Init();  /* Initialize main LTC loop */
                ltc_state.lastsubstate = ltc_state.substate;
                DIAG_checkEvent(retVal, DIAG_CH_LTC_SPI, 0);
                LTC_StateTransition(LTC_STATEMACH_INITIALIZATION, LTC_EXIT_INITIALIZATION, ltc_state.commandDataTransferTime);

            } else if (ltc_state.substate == LTC_EXIT_INITIALIZATION) {
            /* in daisy-chain mode, there is no confirmation of the initialization */
                LTC_SAVELASTSTATES();
                LTC_Initialize_Database();
                LTC_ResetErrorTable();
                LTC_StateTransition(LTC_STATEMACH_INITIALIZED, LTC_ENTRY_INITIALIZATION, LTC_STATEMACH_SHORTTIME);
            }
            break;

        /****************************INITIALIZED*************************************/
        case LTC_STATEMACH_INITIALIZED:
            LTC_SAVELASTSTATES();
            LTC_StateTransition(LTC_STATEMACH_STARTMEAS, LTC_ENTRY, LTC_STATEMACH_SHORTTIME);
            break;

        /****************************START MEASUREMENT*******************************/
        case LTC_STATEMACH_STARTMEAS:

            ltc_state.adcMode = LTC_VOLTAGE_MEASUREMENT_MODE;
            ltc_state.adcMeasCh = LTC_ADCMEAS_ALLCHANNEL;

            ltc_state.check_spi_flag = FALSE;
            retVal = LTC_StartVoltageMeasurement(ltc_state.adcMode, ltc_state.adcMeasCh);
            LTC_CondBasedStateTransition(retVal, DIAG_CH_LTC_SPI,
                                      LTC_STATEMACH_READVOLTAGE, LTC_READ_VOLTAGE_REGISTER_A_RDCVA_READVOLTAGE, (ltc_state.commandTransferTime + LTC_Get_MeasurementTCycle(ltc_state.adcMode, ltc_state.adcMeasCh)),
                                      LTC_STATEMACH_READVOLTAGE, LTC_READ_VOLTAGE_REGISTER_A_RDCVA_READVOLTAGE, LTC_STATEMACH_SHORTTIME);
            break;

        /****************************READ VOLTAGE************************************/
        case LTC_STATEMACH_READVOLTAGE:

            if (ltc_state.substate == LTC_READ_VOLTAGE_REGISTER_A_RDCVA_READVOLTAGE) {
                ltc_state.check_spi_flag = TRUE;
                SPI_SetTransmitOngoing();
                retVal = LTC_RX((uint8_t*)(ltc_cmdRDCVA), ltc_RXPECbuffer);
                LTC_CondBasedStateTransition(retVal, DIAG_CH_LTC_SPI,
                        LTC_STATEMACH_READVOLTAGE, LTC_READ_VOLTAGE_REGISTER_B_RDCVB_READVOLTAGE, (ltc_state.commandDataTransferTime+LTC_TRANSMISSION_TIMEOUT),
                        LTC_STATEMACH_READVOLTAGE, LTC_READ_VOLTAGE_REGISTER_B_RDCVB_READVOLTAGE, LTC_STATEMACH_SHORTTIME);
                break;

            } else if (ltc_state.substate == LTC_READ_VOLTAGE_REGISTER_B_RDCVB_READVOLTAGE) {
                retVal = LTC_RX_PECCheck(ltc_RXPECbuffer);
                DIAG_checkEvent(retVal, DIAG_CH_LTC_PEC, 0);
                LTC_SaveRXtoVoltagebuffer(0, ltc_RXPECbuffer);

                SPI_SetTransmitOngoing();
                retVal = LTC_RX((uint8_t*)(ltc_cmdRDCVB), ltc_RXPECbuffer);
                LTC_CondBasedStateTransition(retVal, DIAG_CH_LTC_SPI,
                        LTC_STATEMACH_READVOLTAGE, LTC_READ_VOLTAGE_REGISTER_C_RDCVC_READVOLTAGE, (ltc_state.commandDataTransferTime+LTC_TRANSMISSION_TIMEOUT),
                        LTC_STATEMACH_READVOLTAGE, LTC_READ_VOLTAGE_REGISTER_C_RDCVC_READVOLTAGE, LTC_STATEMACH_SHORTTIME);
                break;

            } else if (ltc_state.substate == LTC_READ_VOLTAGE_REGISTER_C_RDCVC_READVOLTAGE) {
                retVal = LTC_RX_PECCheck(ltc_RXPECbuffer);
                DIAG_checkEvent(retVal, DIAG_CH_LTC_PEC, 0);
                LTC_SaveRXtoVoltagebuffer(1, ltc_RXPECbuffer);

                SPI_SetTransmitOngoing();
                retVal = LTC_RX((uint8_t*)(ltc_cmdRDCVC), ltc_RXPECbuffer);
                LTC_CondBasedStateTransition(retVal, DIAG_CH_LTC_SPI,
                                          LTC_STATEMACH_READVOLTAGE, LTC_READ_VOLTAGE_REGISTER_D_RDCVD_READVOLTAGE, (ltc_state.commandDataTransferTime+LTC_TRANSMISSION_TIMEOUT),
                                          LTC_STATEMACH_READVOLTAGE, LTC_READ_VOLTAGE_REGISTER_D_RDCVD_READVOLTAGE, LTC_STATEMACH_SHORTTIME);
                break;

            } else if (ltc_state.substate == LTC_READ_VOLTAGE_REGISTER_D_RDCVD_READVOLTAGE) {
                retVal = LTC_RX_PECCheck(ltc_RXPECbuffer);
                DIAG_checkEvent(retVal, DIAG_CH_LTC_PEC, 0);
                LTC_SaveRXtoVoltagebuffer(2, ltc_RXPECbuffer);

                SPI_SetTransmitOngoing();
                retVal = LTC_RX((uint8_t*)(ltc_cmdRDCVD), ltc_RXPECbuffer);
                if (BS_MAX_SUPPORTED_CELLS > 12) {
                    LTC_CondBasedStateTransition(retVal, DIAG_CH_LTC_SPI,
                            LTC_STATEMACH_READVOLTAGE, LTC_READ_VOLTAGE_REGISTER_E_RDCVE_READVOLTAGE, (ltc_state.commandDataTransferTime+LTC_TRANSMISSION_TIMEOUT),
                            LTC_STATEMACH_READVOLTAGE, LTC_READ_VOLTAGE_REGISTER_E_RDCVE_READVOLTAGE, LTC_STATEMACH_SHORTTIME);
                } else {
                    LTC_CondBasedStateTransition(retVal, DIAG_CH_LTC_SPI,
                            LTC_STATEMACH_READVOLTAGE, LTC_EXIT_READVOLTAGE, (ltc_state.commandDataTransferTime+LTC_TRANSMISSION_TIMEOUT),
                            LTC_STATEMACH_READVOLTAGE, LTC_EXIT_READVOLTAGE, LTC_STATEMACH_SHORTTIME);
                }
                break;

            } else if (ltc_state.substate == LTC_READ_VOLTAGE_REGISTER_E_RDCVE_READVOLTAGE) {
                retVal = LTC_RX_PECCheck(ltc_RXPECbuffer);
                DIAG_checkEvent(retVal, DIAG_CH_LTC_PEC, 0);
                LTC_SaveRXtoVoltagebuffer(3, ltc_RXPECbuffer);

                SPI_SetTransmitOngoing();
                retVal = LTC_RX((uint8_t*)(ltc_cmdRDCVE), ltc_RXPECbuffer);
                 if (BS_MAX_SUPPORTED_CELLS > 15) {
                    LTC_CondBasedStateTransition(retVal, DIAG_CH_LTC_SPI,
                            LTC_STATEMACH_READVOLTAGE, LTC_READ_VOLTAGE_REGISTER_F_RDCVF_READVOLTAGE, (ltc_state.commandDataTransferTime+LTC_TRANSMISSION_TIMEOUT),
                            LTC_STATEMACH_READVOLTAGE, LTC_READ_VOLTAGE_REGISTER_F_RDCVF_READVOLTAGE, LTC_STATEMACH_SHORTTIME);
                } else {
                    LTC_CondBasedStateTransition(retVal, DIAG_CH_LTC_SPI,
                            LTC_STATEMACH_READVOLTAGE, LTC_EXIT_READVOLTAGE, (ltc_state.commandDataTransferTime+LTC_TRANSMISSION_TIMEOUT),
                            LTC_STATEMACH_READVOLTAGE, LTC_EXIT_READVOLTAGE, LTC_STATEMACH_SHORTTIME);
                }
                break;

            } else if (ltc_state.substate == LTC_READ_VOLTAGE_REGISTER_F_RDCVF_READVOLTAGE) {
                retVal = LTC_RX_PECCheck(ltc_RXPECbuffer);
                DIAG_checkEvent(retVal, DIAG_CH_LTC_PEC, 0);
                LTC_SaveRXtoVoltagebuffer(4, ltc_RXPECbuffer);

                SPI_SetTransmitOngoing();
                retVal = LTC_RX((uint8_t*)(ltc_cmdRDCVF), ltc_RXPECbuffer);
                LTC_CondBasedStateTransition(retVal, DIAG_CH_LTC_SPI,
                        LTC_STATEMACH_READVOLTAGE, LTC_EXIT_READVOLTAGE, (ltc_state.commandDataTransferTime+LTC_TRANSMISSION_TIMEOUT),
                        LTC_STATEMACH_READVOLTAGE, LTC_EXIT_READVOLTAGE, LTC_STATEMACH_SHORTTIME);
                break;

            } else if (ltc_state.substate == LTC_EXIT_READVOLTAGE) {
                retVal = LTC_RX_PECCheck(ltc_RXPECbuffer);
                DIAG_checkEvent(retVal, DIAG_CH_LTC_PEC, 0);
                if (BS_MAX_SUPPORTED_CELLS == 12) {
                    LTC_SaveRXtoVoltagebuffer(3, ltc_RXPECbuffer);
                } else if (BS_MAX_SUPPORTED_CELLS == 15) {
                    LTC_SaveRXtoVoltagebuffer(4, ltc_RXPECbuffer);
                } else if (BS_MAX_SUPPORTED_CELLS == 18) {
                    LTC_SaveRXtoVoltagebuffer(5, ltc_RXPECbuffer);
                }

                /* Switch to different state if read voltage state is reused
                 * e.g. open-wire check...                                */
                if (ltc_state.reusageMeasurementMode == LTC_NOT_REUSED) {
                    LTC_SaveVoltages();
                    LTC_StateTransition(LTC_STATEMACH_MUXMEASUREMENT, LTC_STATEMACH_MUXCONFIGURATION_INIT, LTC_STATEMACH_SHORTTIME);
                } else if (ltc_state.reusageMeasurementMode == LTC_REUSE_READVOLT_FOR_ADOW_PUP) {
                    LTC_StateTransition(LTC_STATEMACH_OPENWIRE_CHECK, LTC_READ_VOLTAGES_PULLUP_OPENWIRE_CHECK, LTC_STATEMACH_SHORTTIME);
                } else if (ltc_state.reusageMeasurementMode == LTC_REUSE_READVOLT_FOR_ADOW_PDOWN) {
                    LTC_StateTransition(LTC_STATEMACH_OPENWIRE_CHECK, LTC_READ_VOLTAGES_PULLDOWN_OPENWIRE_CHECK, LTC_STATEMACH_SHORTTIME);
                }
                ltc_state.check_spi_flag = FALSE;
            }
            break;


        /****************************MULTIPLEXED MEASUREMENT CONFIGURATION***********/
        case LTC_STATEMACH_MUXMEASUREMENT:

            if (ltc_state.substate == LTC_STATEMACH_MUXCONFIGURATION_INIT) {
                ltc_state.adcMode = LTC_GPIO_MEASUREMENT_MODE;
                ltc_state.adcMeasCh = LTC_ADCMEAS_SINGLECHANNEL_GPIO1;

                if (ltc_state.muxmeas_seqptr >= ltc_state.muxmeas_seqendptr) {
                    /* last step of sequence reached (or no sequence configured) */

                    ltc_state.muxmeas_seqptr = ltc_mux_seq.seqptr;
                    ltc_state.muxmeas_nr_end = ltc_mux_seq.nr_of_steps;
                    ltc_state.muxmeas_seqendptr = ((LTC_MUX_CH_CFG_s *)ltc_mux_seq.seqptr)+ltc_mux_seq.nr_of_steps;  /* last sequence + 1 */

                    LTC_SaveTemperatures();

                    if (LTC_IsFirstMeasurementCycleFinished() == FALSE) {
                        LTC_SetFirstMeasurementCycleFinished();
                    }
                }

                ltc_state.check_spi_flag = TRUE;
                SPI_SetTransmitOngoing();
                retVal = LTC_SetMuxChannel(ltc_TXBuffer, ltc_TXPECbuffer,
                                            ltc_state.muxmeas_seqptr->muxID,  /* mux */
                                            ltc_state.muxmeas_seqptr->muxCh  /* channel */);
                if (retVal != E_OK) {
                    DIAG_Handler(DIAG_CH_LTC_SPI, DIAG_EVENT_NOK, 0);
                    ++ltc_state.muxmeas_seqptr;
                    LTC_StateTransition(LTC_STATEMACH_MUXMEASUREMENT, LTC_STATEMACH_MUXCONFIGURATION_INIT, LTC_STATEMACH_SHORTTIME);
                } else {
                    DIAG_Handler(DIAG_CH_LTC_SPI, DIAG_EVENT_OK, 0);
                    LTC_StateTransition(LTC_STATEMACH_MUXMEASUREMENT, LTC_SEND_CLOCK_STCOMM_MUXMEASUREMENT_CONFIG, (ltc_state.commandDataTransferTime+LTC_TRANSMISSION_TIMEOUT));
                }
                break;

            } else if (ltc_state.substate == LTC_SEND_CLOCK_STCOMM_MUXMEASUREMENT_CONFIG) {
                if (ltc_state.timer == 0 && SPI_IsTransmitOngoing() == TRUE) {
                    DIAG_Handler(DIAG_CH_LTC_SPI, DIAG_EVENT_NOK, 0);
                } else {
                    DIAG_Handler(DIAG_CH_LTC_SPI, DIAG_EVENT_OK, 0);
                }

                SPI_SetTransmitOngoing();
                retVal = LTC_I2CClock(ltc_TXBufferClock, ltc_TXPECBufferClock);
                if (LTC_GOTO_MUX_CHECK == TRUE) {
                    LTC_CondBasedStateTransition(retVal, DIAG_CH_LTC_SPI,
                                              LTC_STATEMACH_MUXMEASUREMENT, LTC_READ_I2C_TRANSMISSION_RESULT_RDCOMM_MUXMEASUREMENT_CONFIG, (ltc_state.gpioClocksTransferTime+LTC_TRANSMISSION_TIMEOUT),
                                              LTC_STATEMACH_MUXMEASUREMENT, LTC_READ_I2C_TRANSMISSION_RESULT_RDCOMM_MUXMEASUREMENT_CONFIG, LTC_STATEMACH_SHORTTIME);;
                } else {
                    LTC_CondBasedStateTransition(retVal, DIAG_CH_LTC_SPI,
                                              LTC_STATEMACH_MUXMEASUREMENT, LTC_STATEMACH_MUXMEASUREMENT, (ltc_state.gpioClocksTransferTime+LTC_TRANSMISSION_TIMEOUT),
                                              LTC_STATEMACH_MUXMEASUREMENT, LTC_STATEMACH_MUXMEASUREMENT, LTC_STATEMACH_SHORTTIME);
                }
                break;

            } else if (ltc_state.substate == LTC_READ_I2C_TRANSMISSION_RESULT_RDCOMM_MUXMEASUREMENT_CONFIG) {
                if (ltc_state.timer == 0 && SPI_IsTransmitOngoing() == TRUE) {
                    DIAG_Handler(DIAG_CH_LTC_SPI, DIAG_EVENT_NOK, 0);
                } else {
                    DIAG_Handler(DIAG_CH_LTC_SPI, DIAG_EVENT_OK, 0);
                }

                SPI_SetTransmitOngoing();
                retVal = LTC_RX((uint8_t*)ltc_cmdRDCOMM, ltc_RXPECbuffer);
                LTC_CondBasedStateTransition(retVal, DIAG_CH_LTC_SPI,
                                          LTC_STATEMACH_MUXMEASUREMENT, LTC_READ_I2C_TRANSMISSION_CHECK_MUXMEASUREMENT_CONFIG, ltc_state.commandDataTransferTime+LTC_TRANSMISSION_TIMEOUT,
                                          LTC_STATEMACH_MUXMEASUREMENT, LTC_READ_I2C_TRANSMISSION_CHECK_MUXMEASUREMENT_CONFIG, LTC_STATEMACH_SHORTTIME);
                break;

            } else if (ltc_state.substate == LTC_READ_I2C_TRANSMISSION_CHECK_MUXMEASUREMENT_CONFIG) {
                if (ltc_state.timer == 0 && SPI_IsTransmitOngoing() == TRUE) {
                    DIAG_Handler(DIAG_CH_LTC_SPI, DIAG_EVENT_NOK, 0);
                } else {
                    DIAG_Handler(DIAG_CH_LTC_SPI, DIAG_EVENT_OK, 0);
                }

                retVal = LTC_RX_PECCheck(ltc_RXPECbuffer);
                DIAG_checkEvent(retVal, DIAG_CH_LTC_PEC, 0);

                /* if CRC OK: check multiplexer answer on i2C bus */
                retVal = LTC_I2CCheckACK(ltc_RXPECbuffer, ltc_state.muxmeas_seqptr->muxID);
                DIAG_checkEvent(retVal, DIAG_CH_LTC_MUX, 0);
                LTC_StateTransition(LTC_STATEMACH_MUXMEASUREMENT, LTC_STATEMACH_MUXMEASUREMENT, LTC_STATEMACH_SHORTTIME);
                break;

            } else if (ltc_state.substate == LTC_STATEMACH_MUXMEASUREMENT) {
                if (ltc_state.muxmeas_seqptr->muxCh == 0xFF) {
                    /* actual multiplexer is switched off, so do not make a measurement and follow up with next step (mux configuration) */
                    ++ltc_state.muxmeas_seqptr;         /*  go further with next step of sequence
                                                            ltc_state.numberOfMeasuredMux not decremented, this does not count as a measurement */
                    LTC_StateTransition(LTC_STATEMACH_STARTMEAS, LTC_ENTRY, LTC_STATEMACH_SHORTTIME);
                    break;
                } else {
                    if (LTC_GOTO_MUX_CHECK == FALSE) {
                        if (ltc_state.timer == 0 && SPI_IsTransmitOngoing() == TRUE) {
                            DIAG_Handler(DIAG_CH_LTC_SPI, DIAG_EVENT_NOK, 0);
                        } else {
                            DIAG_Handler(DIAG_CH_LTC_SPI, DIAG_EVENT_OK, 0);
                        }
                    }

                    ltc_state.check_spi_flag = FALSE;
                    /* user multiplexer type -> connected to GPIO2! */
                    if (ltc_state.muxmeas_seqptr->muxID == 1 || ltc_state.muxmeas_seqptr->muxID == 2) {
                        retVal = LTC_StartGPIOMeasurement(ltc_state.adcMode, LTC_ADCMEAS_SINGLECHANNEL_GPIO2);
                    } else {
                        retVal = LTC_StartGPIOMeasurement(ltc_state.adcMode, LTC_ADCMEAS_SINGLECHANNEL_GPIO1);
                    }
                }
                LTC_CondBasedStateTransition(retVal, DIAG_CH_LTC_SPI,
                                          LTC_STATEMACH_MUXMEASUREMENT, LTC_STATEMACH_READMUXMEASUREMENT, (ltc_state.commandTransferTime + LTC_Get_MeasurementTCycle(ltc_state.adcMode, LTC_ADCMEAS_SINGLECHANNEL_GPIO2)),  /*  wait, ADAX-Command */
                                          LTC_STATEMACH_MUXMEASUREMENT, LTC_STATEMACH_READMUXMEASUREMENT, LTC_STATEMACH_SHORTTIME);
                break;

            } else if (ltc_state.substate == LTC_STATEMACH_READMUXMEASUREMENT) {
                ltc_state.check_spi_flag = TRUE;

                SPI_SetTransmitOngoing();
                retVal = LTC_RX((uint8_t*)(ltc_cmdRDAUXA), ltc_RXPECbuffer);
                LTC_CondBasedStateTransition(retVal, DIAG_CH_LTC_SPI,
                                          LTC_STATEMACH_MUXMEASUREMENT, LTC_STATEMACH_STOREMUXMEASUREMENT, ltc_state.commandDataTransferTime+LTC_TRANSMISSION_TIMEOUT,
                                          LTC_STATEMACH_MUXMEASUREMENT, LTC_STATEMACH_STOREMUXMEASUREMENT, LTC_STATEMACH_SHORTTIME);
                break;

            } else if (ltc_state.substate == LTC_STATEMACH_STOREMUXMEASUREMENT) {
                if (ltc_state.timer == 0 && SPI_IsTransmitOngoing() == TRUE) {
                    DIAG_Handler(DIAG_CH_LTC_SPI, DIAG_EVENT_NOK, 0);
                } else {
                    DIAG_Handler(DIAG_CH_LTC_SPI, DIAG_EVENT_OK, 0);
                }

                retVal = LTC_RX_PECCheck(ltc_RXPECbuffer);
                DIAG_checkEvent(retVal, DIAG_CH_LTC_PEC, 0);
                LTC_SaveMuxMeasurement(ltc_RXPECbuffer, ltc_state.muxmeas_seqptr);

                ++ltc_state.muxmeas_seqptr;

                if (ltc_state.balance_control_done == TRUE) {
                    statereq = LTC_TransferStateRequest(&tmpbusID, &tmpadcMode, &tmpadcMeasCh);
                    if (statereq == LTC_STATE_USER_IO_WRITE_REQUEST) {
                        LTC_StateTransition(LTC_STATEMACH_USER_IO_CONTROL, LTC_USER_IO_SET_OUTPUT_REGISTER, LTC_STATEMACH_SHORTTIME);
                        ltc_state.balance_control_done = FALSE;
                    } else if (statereq == LTC_STATE_USER_IO_READ_REQUEST) {
                        LTC_StateTransition(LTC_STATEMACH_USER_IO_FEEDBACK, LTC_USER_IO_READ_INPUT_REGISTER, LTC_STATEMACH_SHORTTIME);
                        ltc_state.balance_control_done = FALSE;
                    } else if (statereq == LTC_STATE_USER_IO_WRITE_REQUEST_TI) {
                        LTC_StateTransition(LTC_STATEMACH_USER_IO_CONTROL_TI, LTC_USER_IO_SET_DIRECTION_REGISTER_TI, LTC_STATEMACH_SHORTTIME);
                        ltc_state.balance_control_done = FALSE;
                    } else if (statereq == LTC_STATE_USER_IO_READ_REQUEST_TI) {
                        LTC_StateTransition(LTC_STATEMACH_USER_IO_FEEDBACK_TI, LTC_USER_IO_SET_DIRECTION_REGISTER_TI, LTC_STATEMACH_SHORTTIME);
                        ltc_state.balance_control_done = FALSE;
                    } else if (statereq == LTC_STATE_EEPROM_READ_REQUEST) {
                        LTC_StateTransition(LTC_STATEMACH_EEPROM_READ, LTC_EEPROM_READ_DATA1, LTC_STATEMACH_SHORTTIME);
                    } else if (statereq == LTC_STATE_EEPROM_WRITE_REQUEST) {
                        LTC_StateTransition(LTC_STATEMACH_EEPROM_WRITE, LTC_EEPROM_WRITE_DATA1, LTC_STATEMACH_SHORTTIME);
                        ltc_state.balance_control_done = FALSE;
                    } else if (statereq == LTC_STATE_TEMP_SENS_READ_REQUEST) {
                        LTC_StateTransition(LTC_STATEMACH_TEMP_SENS_READ, LTC_TEMP_SENS_SEND_DATA1, LTC_STATEMACH_SHORTTIME);
                        ltc_state.balance_control_done = FALSE;
                    } else if (statereq == LTC_STATEMACH_BALANCEFEEDBACK_REQUEST) {
                        LTC_StateTransition(LTC_STATEMACH_BALANCEFEEDBACK, LTC_ENTRY, LTC_STATEMACH_SHORTTIME);
                        ltc_state.balance_control_done = FALSE;
                    }   else if (statereq == LTC_STATE_OPENWIRE_CHECK_REQUEST) {
                        LTC_StateTransition(LTC_STATEMACH_OPENWIRE_CHECK, LTC_REQUEST_PULLUP_CURRENT_OPENWIRE_CHECK, LTC_STATEMACH_SHORTTIME);
                        /* Send ADOW command with PUP two times */
                        ltc_state.resendCommandCounter = LTC_NMBR_REQ_ADOW_COMMANDS;
                        ltc_state.balance_control_done = FALSE;
                    } else {
                        LTC_StateTransition(LTC_STATEMACH_BALANCECONTROL, LTC_CONFIG_BALANCECONTROL, LTC_STATEMACH_SHORTTIME);
                        ltc_state.balance_control_done = TRUE;
                    }
                } else {
                    LTC_StateTransition(LTC_STATEMACH_BALANCECONTROL, LTC_CONFIG_BALANCECONTROL, LTC_STATEMACH_SHORTTIME);
                    ltc_state.balance_control_done = TRUE;
                }

                break;
            }

            break;

        /****************************BALANCE CONTROL*********************************/
        case LTC_STATEMACH_BALANCECONTROL:

            if (ltc_state.substate == LTC_CONFIG_BALANCECONTROL) {
                ltc_state.check_spi_flag = TRUE;
                SPI_SetTransmitOngoing();
                retVal = LTC_BalanceControl(0);
                LTC_CondBasedStateTransition(retVal, DIAG_CH_LTC_SPI,
                        LTC_STATEMACH_BALANCECONTROL, LTC_CONFIG2_BALANCECONTROL, (ltc_state.commandDataTransferTime+LTC_TRANSMISSION_TIMEOUT),
                        LTC_STATEMACH_BALANCECONTROL, LTC_CONFIG2_BALANCECONTROL, LTC_STATEMACH_SHORTTIME);
                break;

            } else if (ltc_state.substate == LTC_CONFIG2_BALANCECONTROL) {
                if (ltc_state.timer == 0 && SPI_IsTransmitOngoing() == TRUE) {
                    DIAG_Handler(DIAG_CH_LTC_SPI, DIAG_EVENT_NOK, 0);
                    LTC_StateTransition(LTC_STATEMACH_STARTMEAS, LTC_ENTRY, LTC_STATEMACH_SHORTTIME);
                    break;
                } else {
                    DIAG_Handler(DIAG_CH_LTC_SPI, DIAG_EVENT_OK, 0);
                }

                if (BS_NR_OF_BAT_CELLS_PER_MODULE > 12) {
                    SPI_SetTransmitOngoing();
                    retVal = LTC_BalanceControl(1);
                    LTC_CondBasedStateTransition(retVal, DIAG_CH_LTC_SPI,
                            LTC_STATEMACH_BALANCECONTROL, LTC_CONFIG2_BALANCECONTROL_END, ltc_state.commandDataTransferTime+LTC_TRANSMISSION_TIMEOUT,
                            LTC_STATEMACH_BALANCECONTROL, LTC_CONFIG2_BALANCECONTROL_END, LTC_STATEMACH_SHORTTIME);
                } else {
                    /* 12 cells, balancing control finished */
                    ltc_state.check_spi_flag = FALSE;
                    LTC_StateTransition(LTC_STATEMACH_STARTMEAS, LTC_ENTRY, LTC_STATEMACH_SHORTTIME);
                }

                break;

            } else if (ltc_state.substate == LTC_CONFIG2_BALANCECONTROL_END) {
                if (ltc_state.timer == 0 && SPI_IsTransmitOngoing() == TRUE) {
                    DIAG_Handler(DIAG_CH_LTC_SPI, DIAG_EVENT_NOK, 0);
                    LTC_StateTransition(LTC_STATEMACH_STARTMEAS, LTC_ENTRY, LTC_STATEMACH_SHORTTIME);
                    break;
                } else {
                    DIAG_Handler(DIAG_CH_LTC_SPI, DIAG_EVENT_OK, 0);
                }
                /* More than 12 cells, balancing control finished */
                ltc_state.check_spi_flag = FALSE;
                LTC_StateTransition(LTC_STATEMACH_STARTMEAS, LTC_ENTRY, LTC_STATEMACH_SHORTTIME);

                break;
            }
            break;

            /****************************START MEASUREMENT*******************************/
            case LTC_STATEMACH_ALLGPIOMEASUREMENT:

                ltc_state.adcMode = LTC_GPIO_MEASUREMENT_MODE;
                ltc_state.adcMeasCh = LTC_ADCMEAS_ALLCHANNEL;

                ltc_state.check_spi_flag = FALSE;
                retVal = LTC_StartGPIOMeasurement(ltc_state.adcMode, ltc_state.adcMeasCh);
                LTC_CondBasedStateTransition(retVal, DIAG_CH_LTC_SPI,
                                          LTC_STATEMACH_READALLGPIO, LTC_READ_AUXILIARY_REGISTER_A_RDAUXA, (ltc_state.commandTransferTime + LTC_Get_MeasurementTCycle(ltc_state.adcMode, ltc_state.adcMeasCh)),
                                          LTC_STATEMACH_ALLGPIOMEASUREMENT, LTC_ENTRY, LTC_STATEMACH_SHORTTIME);      /* TODO: @koffel here same state is kept if error occurs */
                break;

        /****************************READ ALL GPIO VOLTAGE************************************/
        case LTC_STATEMACH_READALLGPIO:

            if (ltc_state.substate == LTC_READ_AUXILIARY_REGISTER_A_RDAUXA) {
                ltc_state.check_spi_flag = TRUE;
                SPI_SetTransmitOngoing();
                retVal = LTC_RX((uint8_t*)(ltc_cmdRDAUXA), ltc_RXPECbuffer);
                LTC_CondBasedStateTransition(retVal, DIAG_CH_LTC_SPI,
                                          LTC_STATEMACH_READALLGPIO, LTC_READ_AUXILIARY_REGISTER_B_RDAUXB, (ltc_state.commandDataTransferTime+LTC_TRANSMISSION_TIMEOUT),
                                          LTC_STATEMACH_READALLGPIO, LTC_READ_AUXILIARY_REGISTER_B_RDAUXB, LTC_STATEMACH_SHORTTIME);
                break;

            } else if (ltc_state.substate == LTC_READ_AUXILIARY_REGISTER_B_RDAUXB) {
                retVal = LTC_RX_PECCheck(ltc_RXPECbuffer);
                DIAG_checkEvent(retVal, DIAG_CH_LTC_PEC, 0);
                LTC_SaveRXtoGPIOBuffer(0, ltc_RXPECbuffer);

                SPI_SetTransmitOngoing();
                retVal = LTC_RX((uint8_t*)(ltc_cmdRDAUXB), ltc_RXPECbuffer);

                if (BS_MAX_SUPPORTED_CELLS > 12) {
                    LTC_CondBasedStateTransition(retVal, DIAG_CH_LTC_SPI,
                                              LTC_STATEMACH_READALLGPIO, LTC_READ_AUXILIARY_REGISTER_C_RDAUXC, (ltc_state.commandDataTransferTime+LTC_TRANSMISSION_TIMEOUT),
                                              LTC_STATEMACH_READALLGPIO, LTC_READ_AUXILIARY_REGISTER_C_RDAUXC, LTC_STATEMACH_SHORTTIME);
                } else {
                    LTC_CondBasedStateTransition(retVal, DIAG_CH_LTC_SPI,
                                              LTC_STATEMACH_READALLGPIO, LTC_EXIT_READAUXILIARY_ALLGPIOS, (ltc_state.commandDataTransferTime+LTC_TRANSMISSION_TIMEOUT),
                                              LTC_STATEMACH_READALLGPIO, LTC_EXIT_READAUXILIARY_ALLGPIOS, LTC_STATEMACH_SHORTTIME);
                }
                break;

            } else if (ltc_state.substate == LTC_READ_AUXILIARY_REGISTER_C_RDAUXC) {
                retVal = LTC_RX_PECCheck(ltc_RXPECbuffer);
                DIAG_checkEvent(retVal, DIAG_CH_LTC_PEC, 0);
                LTC_SaveRXtoGPIOBuffer(1, ltc_RXPECbuffer);

                SPI_SetTransmitOngoing();
                retVal = LTC_RX((uint8_t*)(ltc_cmdRDAUXC), ltc_RXPECbuffer);
                LTC_CondBasedStateTransition(retVal, DIAG_CH_LTC_SPI,
                                          LTC_STATEMACH_READALLGPIO, LTC_READ_AUXILIARY_REGISTER_D_RDAUXD, (ltc_state.commandDataTransferTime+LTC_TRANSMISSION_TIMEOUT),
                                          LTC_STATEMACH_READALLGPIO, LTC_READ_AUXILIARY_REGISTER_D_RDAUXD, LTC_STATEMACH_SHORTTIME);
                break;

            } else if (ltc_state.substate == LTC_READ_AUXILIARY_REGISTER_D_RDAUXD) {
                retVal = LTC_RX_PECCheck(ltc_RXPECbuffer);
                DIAG_checkEvent(retVal, DIAG_CH_LTC_PEC, 0);
                LTC_SaveRXtoGPIOBuffer(2, ltc_RXPECbuffer);

                SPI_SetTransmitOngoing();
                retVal = LTC_RX((uint8_t*)(ltc_cmdRDAUXD), ltc_RXPECbuffer);
                LTC_CondBasedStateTransition(retVal, DIAG_CH_LTC_SPI,
                                          LTC_STATEMACH_READALLGPIO, LTC_EXIT_READAUXILIARY_ALLGPIOS, (ltc_state.commandDataTransferTime+LTC_TRANSMISSION_TIMEOUT),
                                          LTC_STATEMACH_READALLGPIO, LTC_EXIT_READAUXILIARY_ALLGPIOS, LTC_STATEMACH_SHORTTIME);
                break;

            } else if (ltc_state.substate == LTC_EXIT_READAUXILIARY_ALLGPIOS) {
                retVal = LTC_RX_PECCheck(ltc_RXPECbuffer);
                DIAG_checkEvent(retVal, DIAG_CH_LTC_PEC, 0);

                if (BS_MAX_SUPPORTED_CELLS == 12) {
                    LTC_SaveRXtoGPIOBuffer(1, ltc_RXPECbuffer);
                } else if (BS_MAX_SUPPORTED_CELLS > 12) {
                    LTC_SaveRXtoGPIOBuffer(3, ltc_RXPECbuffer);
                }

                LTC_SaveAllGPIOMeasurement();

                if (ltc_state.balance_control_done == TRUE) {
                    statereq = LTC_TransferStateRequest(&tmpbusID, &tmpadcMode, &tmpadcMeasCh);
                    if (statereq == LTC_STATE_USER_IO_WRITE_REQUEST) {
                        LTC_StateTransition(LTC_STATEMACH_USER_IO_CONTROL, LTC_USER_IO_SET_OUTPUT_REGISTER, LTC_STATEMACH_SHORTTIME);
                        ltc_state.balance_control_done = FALSE;
                    } else if (statereq == LTC_STATE_USER_IO_READ_REQUEST) {
                        LTC_StateTransition(LTC_STATEMACH_USER_IO_FEEDBACK, LTC_USER_IO_READ_INPUT_REGISTER, LTC_STATEMACH_SHORTTIME);
                        ltc_state.balance_control_done = FALSE;
                    } else if (statereq == LTC_STATE_USER_IO_WRITE_REQUEST_TI) {
                        LTC_StateTransition(LTC_STATEMACH_USER_IO_CONTROL_TI, LTC_USER_IO_SET_DIRECTION_REGISTER_TI, LTC_STATEMACH_SHORTTIME);
                        ltc_state.balance_control_done = FALSE;
                    } else if (statereq == LTC_STATE_USER_IO_READ_REQUEST_TI) {
                        LTC_StateTransition(LTC_STATEMACH_USER_IO_FEEDBACK_TI, LTC_USER_IO_SET_DIRECTION_REGISTER_TI, LTC_STATEMACH_SHORTTIME);
                        ltc_state.balance_control_done = FALSE;
                    } else if (statereq == LTC_STATE_EEPROM_READ_REQUEST) {
                        LTC_StateTransition(LTC_STATEMACH_EEPROM_READ, LTC_EEPROM_READ_DATA1, LTC_STATEMACH_SHORTTIME);
                        ltc_state.balance_control_done = FALSE;
                    } else if (statereq == LTC_STATE_EEPROM_WRITE_REQUEST) {
                        LTC_StateTransition(LTC_STATEMACH_EEPROM_WRITE, LTC_EEPROM_WRITE_DATA1, LTC_STATEMACH_SHORTTIME);
                        ltc_state.balance_control_done = FALSE;
                    } else if (statereq == LTC_STATE_TEMP_SENS_READ_REQUEST) {
                        LTC_StateTransition(LTC_STATEMACH_TEMP_SENS_READ, LTC_TEMP_SENS_SEND_DATA1, LTC_STATEMACH_SHORTTIME);
                        ltc_state.balance_control_done = FALSE;
                    } else if (statereq == LTC_STATEMACH_BALANCEFEEDBACK_REQUEST) {
                        LTC_StateTransition(LTC_STATEMACH_BALANCEFEEDBACK, LTC_ENTRY, LTC_STATEMACH_SHORTTIME);
                        ltc_state.balance_control_done = FALSE;
                    }  else if (statereq == LTC_STATE_OPENWIRE_CHECK_REQUEST) {
                        LTC_StateTransition(LTC_STATEMACH_OPENWIRE_CHECK, LTC_REQUEST_PULLUP_CURRENT_OPENWIRE_CHECK, LTC_STATEMACH_SHORTTIME);
                        /* Send ADOW command with PUP two times */
                        ltc_state.resendCommandCounter = LTC_NMBR_REQ_ADOW_COMMANDS;
                        ltc_state.balance_control_done = FALSE;
                    } else {
                        LTC_StateTransition(LTC_STATEMACH_BALANCECONTROL, LTC_CONFIG_BALANCECONTROL, LTC_STATEMACH_SHORTTIME);
                        ltc_state.balance_control_done = TRUE;
                    }
                } else {
                    LTC_StateTransition(LTC_STATEMACH_BALANCECONTROL, LTC_CONFIG_BALANCECONTROL, LTC_STATEMACH_SHORTTIME);
                    ltc_state.balance_control_done = TRUE;
                }
            }

            break;


        /****************************BALANCE FEEDBACK*********************************/
        case LTC_STATEMACH_BALANCEFEEDBACK:

             if (ltc_state.substate == LTC_ENTRY) {
                ltc_state.adcMode = LTC_ADCMODE_NORMAL_DCP0;
                ltc_state.adcMeasCh = LTC_ADCMEAS_SINGLECHANNEL_GPIO3;

                ltc_state.check_spi_flag = FALSE;
                retVal = LTC_StartGPIOMeasurement(ltc_state.adcMode, ltc_state.adcMeasCh);
                LTC_CondBasedStateTransition(retVal, DIAG_CH_LTC_SPI,
                                          LTC_STATEMACH_BALANCEFEEDBACK, LTC_READ_FEEDBACK_BALANCECONTROL, (ltc_state.commandDataTransferTime + LTC_Get_MeasurementTCycle(ltc_state.adcMode, ltc_state.adcMeasCh)),
                                          LTC_STATEMACH_BALANCEFEEDBACK, LTC_READ_FEEDBACK_BALANCECONTROL, LTC_STATEMACH_SHORTTIME);
                break;

            } else if (ltc_state.substate == LTC_READ_FEEDBACK_BALANCECONTROL) {
                ltc_state.check_spi_flag = TRUE;
                SPI_SetTransmitOngoing();
                retVal = LTC_RX((uint8_t*)ltc_cmdRDAUXA, ltc_RXPECbuffer);  /* read AUXA register */
                LTC_CondBasedStateTransition(retVal, DIAG_CH_LTC_SPI,
                        LTC_STATEMACH_BALANCEFEEDBACK, LTC_SAVE_FEEDBACK_BALANCECONTROL, ltc_state.commandDataTransferTime+LTC_TRANSMISSION_TIMEOUT,
                        LTC_STATEMACH_BALANCEFEEDBACK, LTC_SAVE_FEEDBACK_BALANCECONTROL, LTC_STATEMACH_SHORTTIME);

            } else if (ltc_state.substate == LTC_SAVE_FEEDBACK_BALANCECONTROL) {
                if (ltc_state.timer == 0 && SPI_IsTransmitOngoing() == TRUE) {
                    DIAG_Handler(DIAG_CH_LTC_SPI, DIAG_EVENT_NOK, 0);
                    LTC_StateTransition(LTC_STATEMACH_STARTMEAS, LTC_ENTRY, LTC_STATEMACH_SHORTTIME);
                    break;
                } else {
                    DIAG_Handler(DIAG_CH_LTC_SPI, DIAG_EVENT_OK, 0);
                }

                if (LTC_RX_PECCheck(ltc_RXPECbuffer) != E_OK) {
                    DIAG_Handler(DIAG_CH_LTC_PEC, DIAG_EVENT_NOK, 0);
                } else {
                    DIAG_Handler(DIAG_CH_LTC_PEC, DIAG_EVENT_OK, 0);
                    LTC_SaveBalancingFeedback(ltc_RXPECbuffer);
                }
                LTC_StateTransition(LTC_STATEMACH_STARTMEAS, LTC_ENTRY, LTC_STATEMACH_SHORTTIME);
                break;
            }
            break;

        /****************************BOARD TEMPERATURE SENSOR*********************************/
        case LTC_STATEMACH_TEMP_SENS_READ:

            if (ltc_state.substate == LTC_TEMP_SENS_SEND_DATA1) {
                ltc_state.check_spi_flag = TRUE;
                SPI_SetTransmitOngoing();
                retVal = LTC_Send_I2C_Command(ltc_TXBuffer, ltc_TXPECbuffer, (uint8_t*)ltc_I2CcmdTempSens0);

                if (retVal != E_OK) {
                    DIAG_Handler(DIAG_CH_LTC_SPI, DIAG_EVENT_NOK, 0);
                    ++ltc_state.muxmeas_seqptr;
                    LTC_StateTransition(LTC_STATEMACH_STARTMEAS, LTC_ENTRY, LTC_STATEMACH_SHORTTIME);
                } else {
                    DIAG_Handler(DIAG_CH_LTC_SPI, DIAG_EVENT_OK, 0);
                    LTC_StateTransition(LTC_STATEMACH_TEMP_SENS_READ, LTC_TEMP_SENS_SEND_CLOCK_STCOMM1, ltc_state.commandDataTransferTime+LTC_TRANSMISSION_TIMEOUT);
                }

                break;

            } else if (ltc_state.substate == LTC_TEMP_SENS_SEND_CLOCK_STCOMM1) {
                if (ltc_state.timer == 0 && SPI_IsTransmitOngoing() == TRUE) {
                    DIAG_Handler(DIAG_CH_LTC_SPI, DIAG_EVENT_NOK, 0);
                    LTC_StateTransition(LTC_STATEMACH_STARTMEAS, LTC_ENTRY, LTC_STATEMACH_SHORTTIME);
                    break;
                } else {
                    DIAG_Handler(DIAG_CH_LTC_SPI, DIAG_EVENT_OK, 0);
                }

                SPI_SetTransmitOngoing();
                retVal = LTC_I2CClock(ltc_TXBufferClock, ltc_TXPECBufferClock);
                LTC_CondBasedStateTransition(retVal, DIAG_CH_LTC_SPI,
                                          LTC_STATEMACH_TEMP_SENS_READ, LTC_TEMP_SENS_READ_DATA1, (ltc_state.gpioClocksTransferTime+LTC_TRANSMISSION_TIMEOUT),
                                          LTC_STATEMACH_TEMP_SENS_READ, LTC_TEMP_SENS_READ_DATA1, LTC_STATEMACH_SHORTTIME);
                break;

            } else if (ltc_state.substate == LTC_TEMP_SENS_READ_DATA1) {
                if (ltc_state.timer == 0 && SPI_IsTransmitOngoing() == TRUE) {
                    DIAG_Handler(DIAG_CH_LTC_SPI, DIAG_EVENT_NOK, 0);
                    LTC_StateTransition(LTC_STATEMACH_STARTMEAS, LTC_ENTRY, LTC_STATEMACH_SHORTTIME);
                    break;
                } else {
                    DIAG_Handler(DIAG_CH_LTC_SPI, DIAG_EVENT_OK, 0);
                }

                SPI_SetTransmitOngoing();
                retVal = LTC_Send_I2C_Command(ltc_TXBuffer, ltc_TXPECbuffer, (uint8_t*)ltc_I2CcmdTempSens1);

                if (retVal != E_OK) {
                    DIAG_Handler(DIAG_CH_LTC_SPI, DIAG_EVENT_NOK, 0);
                    ++ltc_state.muxmeas_seqptr;
                    LTC_StateTransition(LTC_STATEMACH_STARTMEAS, LTC_ENTRY, LTC_STATEMACH_SHORTTIME);
                } else {
                    DIAG_Handler(DIAG_CH_LTC_SPI, DIAG_EVENT_OK, 0);
                    LTC_StateTransition(LTC_STATEMACH_TEMP_SENS_READ, LTC_TEMP_SENS_SEND_CLOCK_STCOMM2, (ltc_state.commandDataTransferTime+LTC_TRANSMISSION_TIMEOUT));
                }

                break;

            } else if (ltc_state.substate == LTC_TEMP_SENS_SEND_CLOCK_STCOMM2) {
                if (ltc_state.timer == 0 && SPI_IsTransmitOngoing() == TRUE) {
                    DIAG_Handler(DIAG_CH_LTC_SPI, DIAG_EVENT_NOK, 0);
                    LTC_StateTransition(LTC_STATEMACH_STARTMEAS, LTC_ENTRY, LTC_STATEMACH_SHORTTIME);
                    break;
                } else {
                    DIAG_Handler(DIAG_CH_LTC_SPI, DIAG_EVENT_OK, 0);
                }

                SPI_SetTransmitOngoing();
                retVal = LTC_I2CClock(ltc_TXBufferClock, ltc_TXPECBufferClock);
                LTC_CondBasedStateTransition(retVal, DIAG_CH_LTC_SPI,
                                          LTC_STATEMACH_TEMP_SENS_READ, LTC_TEMP_SENS_READ_I2C_TRANSMISSION_RESULT_RDCOMM, (ltc_state.gpioClocksTransferTime+LTC_TRANSMISSION_TIMEOUT),
                                          LTC_STATEMACH_TEMP_SENS_READ, LTC_TEMP_SENS_READ_I2C_TRANSMISSION_RESULT_RDCOMM, LTC_STATEMACH_SHORTTIME);
                break;
            }  else if (ltc_state.substate == LTC_TEMP_SENS_READ_I2C_TRANSMISSION_RESULT_RDCOMM) {
                if (ltc_state.timer == 0 && SPI_IsTransmitOngoing() == TRUE) {
                    DIAG_Handler(DIAG_CH_LTC_SPI, DIAG_EVENT_NOK, 0);
                    LTC_StateTransition(LTC_STATEMACH_STARTMEAS, LTC_ENTRY, LTC_STATEMACH_SHORTTIME);
                    break;
                } else {
                    DIAG_Handler(DIAG_CH_LTC_SPI, DIAG_EVENT_OK, 0);
                }

                SPI_SetTransmitOngoing();
                retVal = LTC_RX((uint8_t*)ltc_cmdRDCOMM, ltc_RXPECbuffer);
                LTC_CondBasedStateTransition(retVal, DIAG_CH_LTC_SPI,
                                          LTC_STATEMACH_TEMP_SENS_READ, LTC_TEMP_SENS_SAVE_TEMP, ltc_state.commandDataTransferTime+LTC_TRANSMISSION_TIMEOUT,
                                          LTC_STATEMACH_TEMP_SENS_READ, LTC_TEMP_SENS_SAVE_TEMP, LTC_STATEMACH_SHORTTIME);
                break;

            } else if (ltc_state.substate == LTC_TEMP_SENS_SAVE_TEMP) {
                if (ltc_state.timer == 0 && SPI_IsTransmitOngoing() == TRUE) {
                    DIAG_Handler(DIAG_CH_LTC_SPI, DIAG_EVENT_NOK, 0);
                    LTC_StateTransition(LTC_STATEMACH_STARTMEAS, LTC_ENTRY, LTC_STATEMACH_SHORTTIME);
                    break;
                } else {
                    DIAG_Handler(DIAG_CH_LTC_SPI, DIAG_EVENT_OK, 0);
                }

                if (LTC_RX_PECCheck(ltc_RXPECbuffer) != E_OK) {
                    DIAG_Handler(DIAG_CH_LTC_PEC, DIAG_EVENT_NOK, 0);
                } else {
                    DIAG_Handler(DIAG_CH_LTC_PEC, DIAG_EVENT_OK, 0);
                    LTC_TempSensSaveTemp(ltc_RXPECbuffer);
                }

                LTC_StateTransition(LTC_STATEMACH_STARTMEAS, LTC_ENTRY, LTC_STATEMACH_SHORTTIME);
                break;
            }
            break;

        /****************************WRITE TO PORT EXPANDER IO***********/
        case LTC_STATEMACH_USER_IO_CONTROL:

            if (ltc_state.substate == LTC_USER_IO_SET_OUTPUT_REGISTER) {
                ltc_state.check_spi_flag = TRUE;
                SPI_SetTransmitOngoing();
                retVal = LTC_SetPortExpander(ltc_TXBuffer, ltc_TXPECbuffer);

                if (retVal != E_OK) {
                    DIAG_Handler(DIAG_CH_LTC_SPI, DIAG_EVENT_NOK, 0);
                    ++ltc_state.muxmeas_seqptr;
                    LTC_StateTransition(LTC_STATEMACH_STARTMEAS, LTC_ENTRY, LTC_STATEMACH_SHORTTIME);
                } else {
                    DIAG_Handler(DIAG_CH_LTC_SPI, DIAG_EVENT_OK, 0);
                    LTC_StateTransition(LTC_STATEMACH_USER_IO_CONTROL, LTC_SEND_CLOCK_STCOMM_MUXMEASUREMENT_CONFIG, (ltc_state.commandDataTransferTime+LTC_TRANSMISSION_TIMEOUT));
                }
                break;

            } else if (ltc_state.substate == LTC_SEND_CLOCK_STCOMM_MUXMEASUREMENT_CONFIG) {
                if (ltc_state.timer == 0 && SPI_IsTransmitOngoing() == TRUE) {
                    DIAG_Handler(DIAG_CH_LTC_SPI, DIAG_EVENT_NOK, 0);
                    LTC_StateTransition(LTC_STATEMACH_STARTMEAS, LTC_ENTRY, LTC_STATEMACH_SHORTTIME);
                    break;
                } else {
                    DIAG_Handler(DIAG_CH_LTC_SPI, DIAG_EVENT_OK, 0);
                }

                ltc_state.check_spi_flag = FALSE;
                retVal = LTC_I2CClock(ltc_TXBufferClock, ltc_TXPECBufferClock);
                LTC_CondBasedStateTransition(retVal, DIAG_CH_LTC_SPI,
                                          LTC_STATEMACH_STARTMEAS, LTC_ENTRY, ltc_state.gpioClocksTransferTime,
                                          LTC_STATEMACH_STARTMEAS, LTC_ENTRY, LTC_STATEMACH_SHORTTIME);
                break;
            }
            break;

        /****************************READ FROM PORT EXPANDER IO***********/
        case LTC_STATEMACH_USER_IO_FEEDBACK:

            if (ltc_state.substate == LTC_USER_IO_READ_INPUT_REGISTER) {
                ltc_state.check_spi_flag = TRUE;
                SPI_SetTransmitOngoing();
                retVal = LTC_Send_I2C_Command(ltc_TXBuffer, ltc_TXPECbuffer, (uint8_t*)ltc_I2CcmdPortExpander1);

                if (retVal != E_OK) {
                    DIAG_Handler(DIAG_CH_LTC_SPI, DIAG_EVENT_NOK, 0);
                    ++ltc_state.muxmeas_seqptr;
                    LTC_StateTransition(LTC_STATEMACH_STARTMEAS, LTC_ENTRY, LTC_STATEMACH_SHORTTIME);
                } else {
                    DIAG_Handler(DIAG_CH_LTC_SPI, DIAG_EVENT_OK, 0);
                    LTC_StateTransition(LTC_STATEMACH_USER_IO_FEEDBACK, LTC_USER_IO_SEND_CLOCK_STCOMM, ltc_state.commandDataTransferTime+LTC_TRANSMISSION_TIMEOUT);
                }

                break;

            } else if (ltc_state.substate == LTC_USER_IO_SEND_CLOCK_STCOMM) {
                if (ltc_state.timer == 0 && SPI_IsTransmitOngoing() == TRUE) {
                    DIAG_Handler(DIAG_CH_LTC_SPI, DIAG_EVENT_NOK, 0);
                    LTC_StateTransition(LTC_STATEMACH_STARTMEAS, LTC_ENTRY, LTC_STATEMACH_SHORTTIME);
                    break;
                } else {
                    DIAG_Handler(DIAG_CH_LTC_SPI, DIAG_EVENT_OK, 0);
                }

                ltc_state.check_spi_flag = FALSE;
                retVal = LTC_I2CClock(ltc_TXBufferClock, ltc_TXPECBufferClock);
                LTC_CondBasedStateTransition(retVal, DIAG_CH_LTC_SPI,
                                          LTC_STATEMACH_USER_IO_FEEDBACK, LTC_USER_IO_READ_I2C_TRANSMISSION_RESULT_RDCOMM, ltc_state.gpioClocksTransferTime,
                                          LTC_STATEMACH_USER_IO_FEEDBACK, LTC_USER_IO_READ_I2C_TRANSMISSION_RESULT_RDCOMM, LTC_STATEMACH_SHORTTIME);
                break;

                } else if (ltc_state.substate == LTC_USER_IO_READ_I2C_TRANSMISSION_RESULT_RDCOMM) {
                    if (ltc_state.timer == 0 && SPI_IsTransmitOngoing() == TRUE) {
                        DIAG_Handler(DIAG_CH_LTC_SPI, DIAG_EVENT_NOK, 0);
                        LTC_StateTransition(LTC_STATEMACH_STARTMEAS, LTC_ENTRY, LTC_STATEMACH_SHORTTIME);
                        break;
                    } else {
                        DIAG_Handler(DIAG_CH_LTC_SPI, DIAG_EVENT_OK, 0);
                    }

                    SPI_SetTransmitOngoing();
                    retVal = LTC_RX((uint8_t*)ltc_cmdRDCOMM, ltc_RXPECbuffer);
                    LTC_CondBasedStateTransition(retVal, DIAG_CH_LTC_SPI,
                                              LTC_STATEMACH_USER_IO_FEEDBACK, LTC_USER_IO_SAVE_DATA, ltc_state.commandDataTransferTime+LTC_TRANSMISSION_TIMEOUT,
                                              LTC_STATEMACH_USER_IO_FEEDBACK, LTC_USER_IO_SAVE_DATA, LTC_STATEMACH_SHORTTIME);
                    break;

                } else if (ltc_state.substate == LTC_USER_IO_SAVE_DATA) {
                    if (ltc_state.timer == 0 && SPI_IsTransmitOngoing() == TRUE) {
                        DIAG_Handler(DIAG_CH_LTC_SPI, DIAG_EVENT_NOK, 0);
                        LTC_StateTransition(LTC_STATEMACH_STARTMEAS, LTC_ENTRY, LTC_STATEMACH_SHORTTIME);
                        break;
                    } else {
                        DIAG_Handler(DIAG_CH_LTC_SPI, DIAG_EVENT_OK, 0);
                    }

                    if (LTC_RX_PECCheck(ltc_RXPECbuffer) != E_OK) {
                        DIAG_Handler(DIAG_CH_LTC_PEC, DIAG_EVENT_NOK, 0);
                    } else {
                        DIAG_Handler(DIAG_CH_LTC_PEC, DIAG_EVENT_OK, 0);
                        LTC_PortExpanderSaveValues(ltc_RXPECbuffer);
                    }

                    LTC_StateTransition(LTC_STATEMACH_STARTMEAS, LTC_ENTRY, LTC_STATEMACH_SHORTTIME);
                    break;
                }

            break;

        /****************************WRITE TO TI PORT EXPANDER IO***********/
        case LTC_STATEMACH_USER_IO_CONTROL_TI:

            if (ltc_state.substate == LTC_USER_IO_SET_DIRECTION_REGISTER_TI) {
                ltc_state.check_spi_flag = TRUE;
                SPI_SetTransmitOngoing();
                retVal = LTC_SetPortExpanderDirection_TI(LTC_PORT_EXPANDER_TI_OUTPUT, ltc_TXBuffer, ltc_TXPECbuffer);
                LTC_CondBasedStateTransition(retVal, DIAG_CH_LTC_SPI,
                    LTC_STATEMACH_USER_IO_CONTROL_TI, LTC_USER_IO_SEND_CLOCK_STCOMM_TI, LTC_STATEMACH_SHORTTIME,
                    LTC_STATEMACH_STARTMEAS, LTC_ENTRY, LTC_STATEMACH_SHORTTIME);
                break;

            } else if (ltc_state.substate == LTC_USER_IO_SEND_CLOCK_STCOMM_TI) {
                if (ltc_state.timer == 0 && SPI_IsTransmitOngoing() == TRUE) {
                    DIAG_Handler(DIAG_CH_LTC_SPI, DIAG_EVENT_NOK, 0);
                    LTC_StateTransition(LTC_STATEMACH_STARTMEAS, LTC_ENTRY, LTC_STATEMACH_SHORTTIME);
                    break;

                } else {
                    DIAG_Handler(DIAG_CH_LTC_SPI, DIAG_EVENT_OK, 0);
                }

                ltc_state.check_spi_flag = FALSE;
                retVal = LTC_I2CClock(ltc_TXBufferClock, ltc_TXPECBufferClock);
                LTC_CondBasedStateTransition(retVal, DIAG_CH_LTC_SPI,
                        LTC_STATEMACH_USER_IO_CONTROL_TI, LTC_USER_IO_SET_OUTPUT_REGISTER_TI, ltc_state.gpioClocksTransferTime,
                        LTC_STATEMACH_STARTMEAS, LTC_ENTRY, LTC_STATEMACH_SHORTTIME);
                break;

            } else if (ltc_state.substate == LTC_USER_IO_SET_OUTPUT_REGISTER_TI) {
                ltc_state.check_spi_flag = TRUE;
                SPI_SetTransmitOngoing();
                retVal = LTC_SetPortExpander_Output_TI(ltc_TXBuffer, ltc_TXPECbuffer);
                LTC_CondBasedStateTransition(retVal, DIAG_CH_LTC_SPI,
                        LTC_STATEMACH_USER_IO_CONTROL_TI, LTC_USER_IO_READ_I2C_TRANSMISSION_RESULT_RDCOMM_TI_SECOND, ltc_state.commandDataTransferTime+LTC_TRANSMISSION_TIMEOUT,
                        LTC_STATEMACH_STARTMEAS, LTC_ENTRY, LTC_STATEMACH_SHORTTIME);
                break;

            } else if (ltc_state.substate == LTC_USER_IO_READ_I2C_TRANSMISSION_RESULT_RDCOMM_TI_SECOND) {
                if (ltc_state.timer == 0 && SPI_IsTransmitOngoing() == TRUE) {
                    DIAG_Handler(DIAG_CH_LTC_SPI, DIAG_EVENT_NOK, 0);
                    LTC_StateTransition(LTC_STATEMACH_STARTMEAS, LTC_ENTRY, LTC_STATEMACH_SHORTTIME);
                    break;
                } else {
                    DIAG_Handler(DIAG_CH_LTC_SPI, DIAG_EVENT_OK, 0);
                }

                ltc_state.check_spi_flag = FALSE;
                retVal = LTC_I2CClock(ltc_TXBufferClock, ltc_TXPECBufferClock);
                LTC_CondBasedStateTransition(retVal, DIAG_CH_LTC_SPI,
                     LTC_STATEMACH_STARTMEAS, LTC_ENTRY, ltc_state.gpioClocksTransferTime,
                     LTC_STATEMACH_STARTMEAS, LTC_ENTRY, LTC_STATEMACH_SHORTTIME);
                break;
            }
            break;

        /****************************READ TI PORT EXPANDER IO***********/
        case LTC_STATEMACH_USER_IO_FEEDBACK_TI:

            if (ltc_state.substate == LTC_USER_IO_SET_DIRECTION_REGISTER_TI) {
                ltc_state.check_spi_flag = TRUE;
                SPI_SetTransmitOngoing();
                retVal = LTC_SetPortExpanderDirection_TI(LTC_PORT_EXPANDER_TI_INPUT, ltc_TXBuffer, ltc_TXPECbuffer);
                LTC_CondBasedStateTransition(retVal, DIAG_CH_LTC_SPI,
                    LTC_STATEMACH_USER_IO_FEEDBACK_TI, LTC_USER_IO_SEND_CLOCK_STCOMM_TI, LTC_STATEMACH_SHORTTIME,
                    LTC_STATEMACH_STARTMEAS, LTC_ENTRY, LTC_STATEMACH_SHORTTIME);
                break;

            } else if (ltc_state.substate == LTC_USER_IO_SEND_CLOCK_STCOMM_TI) {
                if (ltc_state.timer == 0 && SPI_IsTransmitOngoing() == TRUE) {
                    DIAG_Handler(DIAG_CH_LTC_SPI, DIAG_EVENT_NOK, 0);
                    LTC_StateTransition(LTC_STATEMACH_STARTMEAS, LTC_ENTRY, LTC_STATEMACH_SHORTTIME);
                    break;

                } else {
                    DIAG_Handler(DIAG_CH_LTC_SPI, DIAG_EVENT_OK, 0);
                }

                ltc_state.check_spi_flag = FALSE;
                retVal = LTC_I2CClock(ltc_TXBufferClock, ltc_TXPECBufferClock);
                LTC_CondBasedStateTransition(retVal, DIAG_CH_LTC_SPI,
                        LTC_STATEMACH_USER_IO_FEEDBACK_TI, LTC_USER_IO_READ_INPUT_REGISTER_TI_FIRST, ltc_state.gpioClocksTransferTime,
                        LTC_STATEMACH_STARTMEAS, LTC_ENTRY, LTC_STATEMACH_SHORTTIME);
                break;

            } else if (ltc_state.substate == LTC_USER_IO_READ_INPUT_REGISTER_TI_FIRST) {
                ltc_state.check_spi_flag = TRUE;
                SPI_SetTransmitOngoing();
                retVal = LTC_GetPortExpander_Input_TI(0, ltc_TXBuffer, ltc_TXPECbuffer);
                LTC_CondBasedStateTransition(retVal, DIAG_CH_LTC_SPI,
                        LTC_STATEMACH_USER_IO_FEEDBACK_TI, LTC_USER_IO_READ_I2C_TRANSMISSION_RESULT_RDCOMM_TI_SECOND, ltc_state.commandDataTransferTime+LTC_TRANSMISSION_TIMEOUT,
                        LTC_STATEMACH_STARTMEAS, LTC_ENTRY, LTC_STATEMACH_SHORTTIME);
                break;

            } else if (ltc_state.substate == LTC_USER_IO_READ_I2C_TRANSMISSION_RESULT_RDCOMM_TI_SECOND) {
                if (ltc_state.timer == 0 && SPI_IsTransmitOngoing() == TRUE) {
                    DIAG_Handler(DIAG_CH_LTC_SPI, DIAG_EVENT_NOK, 0);
                    LTC_StateTransition(LTC_STATEMACH_STARTMEAS, LTC_ENTRY, LTC_STATEMACH_SHORTTIME);
                    break;
                } else {
                    DIAG_Handler(DIAG_CH_LTC_SPI, DIAG_EVENT_OK, 0);
                }

                ltc_state.check_spi_flag = FALSE;
                retVal = LTC_I2CClock(ltc_TXBufferClock, ltc_TXPECBufferClock);
                LTC_CondBasedStateTransition(retVal, DIAG_CH_LTC_SPI,
                    LTC_STATEMACH_USER_IO_FEEDBACK_TI, LTC_USER_IO_READ_INPUT_REGISTER_TI_SECOND, ltc_state.gpioClocksTransferTime,
                    LTC_STATEMACH_STARTMEAS, LTC_ENTRY, LTC_STATEMACH_SHORTTIME);
                break;
            } else if (ltc_state.substate == LTC_USER_IO_READ_INPUT_REGISTER_TI_SECOND) {
                ltc_state.check_spi_flag = TRUE;
                SPI_SetTransmitOngoing();
                retVal = LTC_GetPortExpander_Input_TI(1, ltc_TXBuffer, ltc_TXPECbuffer);
                LTC_CondBasedStateTransition(retVal, DIAG_CH_LTC_SPI,
                    LTC_STATEMACH_USER_IO_FEEDBACK_TI, LTC_USER_IO_READ_I2C_TRANSMISSION_RESULT_RDCOMM_TI_THIRD, ltc_state.commandDataTransferTime+LTC_TRANSMISSION_TIMEOUT,
                    LTC_STATEMACH_STARTMEAS, LTC_ENTRY, LTC_STATEMACH_SHORTTIME);
                break;

            } else if (ltc_state.substate == LTC_USER_IO_READ_I2C_TRANSMISSION_RESULT_RDCOMM_TI_THIRD) {
                if (ltc_state.timer == 0 && SPI_IsTransmitOngoing() == TRUE) {
                    DIAG_Handler(DIAG_CH_LTC_SPI, DIAG_EVENT_NOK, 0);
                    LTC_StateTransition(LTC_STATEMACH_STARTMEAS, LTC_ENTRY, LTC_STATEMACH_SHORTTIME);
                    break;
                } else {
                    DIAG_Handler(DIAG_CH_LTC_SPI, DIAG_EVENT_OK, 0);
                }

                ltc_state.check_spi_flag = FALSE;
                retVal = LTC_I2CClock(ltc_TXBufferClock, ltc_TXPECBufferClock);
                LTC_CondBasedStateTransition(retVal, DIAG_CH_LTC_SPI,
                    LTC_STATEMACH_USER_IO_FEEDBACK_TI, LTC_USER_IO_READ_I2C_TRANSMISSION_RESULT_RDCOMM_TI_FOURTH, ltc_state.gpioClocksTransferTime,
                    LTC_STATEMACH_STARTMEAS, LTC_ENTRY, LTC_STATEMACH_SHORTTIME);
                break;
            } else if (ltc_state.substate == LTC_USER_IO_READ_I2C_TRANSMISSION_RESULT_RDCOMM_TI_FOURTH) {
                if (ltc_state.timer == 0 && SPI_IsTransmitOngoing() == TRUE) {
                    DIAG_Handler(DIAG_CH_LTC_SPI, DIAG_EVENT_NOK, 0);
                    LTC_StateTransition(LTC_STATEMACH_STARTMEAS, LTC_ENTRY, LTC_STATEMACH_SHORTTIME);
                    break;
                } else {
                    DIAG_Handler(DIAG_CH_LTC_SPI, DIAG_EVENT_OK, 0);
                }

                SPI_SetTransmitOngoing();
                retVal = LTC_RX((uint8_t*)ltc_cmdRDCOMM, ltc_RXPECbuffer);
                LTC_CondBasedStateTransition(retVal, DIAG_CH_LTC_SPI,
                    LTC_STATEMACH_USER_IO_FEEDBACK_TI, LTC_USER_IO_SAVE_DATA_TI, ltc_state.commandDataTransferTime+LTC_TRANSMISSION_TIMEOUT,
                    LTC_STATEMACH_USER_IO_FEEDBACK_TI, LTC_USER_IO_SAVE_DATA_TI, LTC_STATEMACH_SHORTTIME);
                break;

            } else if (ltc_state.substate == LTC_USER_IO_SAVE_DATA_TI) {
                if (ltc_state.timer == 0 && SPI_IsTransmitOngoing() == TRUE) {
                    DIAG_Handler(DIAG_CH_LTC_SPI, DIAG_EVENT_NOK, 0);
                    LTC_StateTransition(LTC_STATEMACH_STARTMEAS, LTC_ENTRY, LTC_STATEMACH_SHORTTIME);
                    break;
                } else {
                    DIAG_Handler(DIAG_CH_LTC_SPI, DIAG_EVENT_OK, 0);
                }

                if (LTC_RX_PECCheck(ltc_RXPECbuffer) != E_OK) {
                    DIAG_Handler(DIAG_CH_LTC_PEC, DIAG_EVENT_NOK, 0);
                } else {
                    DIAG_Handler(DIAG_CH_LTC_PEC, DIAG_EVENT_OK, 0);
                    LTC_PortExpanderSaveValues_TI(ltc_RXPECbuffer);
                }

                LTC_StateTransition(LTC_STATEMACH_STARTMEAS, LTC_ENTRY, LTC_STATEMACH_SHORTTIME);
                break;
            }

            break;

        /****************************EEPROM READ*********************************/
        case LTC_STATEMACH_EEPROM_READ:

            if (ltc_state.substate == LTC_EEPROM_READ_DATA1) {
                ltc_state.check_spi_flag = TRUE;
                SPI_SetTransmitOngoing();
                retVal = LTC_SendEEPROMReadCommand(ltc_TXBuffer, ltc_TXPECbuffer, 0);

                if (retVal != E_OK) {
                    DIAG_Handler(DIAG_CH_LTC_SPI, DIAG_EVENT_NOK, 0);
                    ++ltc_state.muxmeas_seqptr;
                    LTC_StateTransition(LTC_STATEMACH_STARTMEAS, LTC_ENTRY, LTC_STATEMACH_SHORTTIME);
                } else {
                    DIAG_Handler(DIAG_CH_LTC_SPI, DIAG_EVENT_OK, 0);
                    LTC_StateTransition(LTC_STATEMACH_EEPROM_READ, LTC_EEPROM_SEND_CLOCK_STCOMM1, ltc_state.commandDataTransferTime+LTC_TRANSMISSION_TIMEOUT);
                }

                break;

            } else if (ltc_state.substate == LTC_EEPROM_SEND_CLOCK_STCOMM1) {
                if (ltc_state.timer == 0 && SPI_IsTransmitOngoing() == TRUE) {
                    DIAG_Handler(DIAG_CH_LTC_SPI, DIAG_EVENT_NOK, 0);
                    LTC_StateTransition(LTC_STATEMACH_STARTMEAS, LTC_ENTRY, LTC_STATEMACH_SHORTTIME);
                    break;
                } else {
                    DIAG_Handler(DIAG_CH_LTC_SPI, DIAG_EVENT_OK, 0);
                }

                SPI_SetTransmitOngoing();
                retVal = LTC_I2CClock(ltc_TXBufferClock, ltc_TXPECBufferClock);
                LTC_CondBasedStateTransition(retVal, DIAG_CH_LTC_SPI,
                                          LTC_STATEMACH_EEPROM_READ, LTC_EEPROM_READ_DATA2, (ltc_state.gpioClocksTransferTime+LTC_TRANSMISSION_TIMEOUT),
                                          LTC_STATEMACH_EEPROM_READ, LTC_EEPROM_READ_DATA2, LTC_STATEMACH_SHORTTIME);
                break;

            } else if (ltc_state.substate == LTC_EEPROM_READ_DATA2) {
                if (ltc_state.timer == 0 && SPI_IsTransmitOngoing() == TRUE) {
                    DIAG_Handler(DIAG_CH_LTC_SPI, DIAG_EVENT_NOK, 0);
                    LTC_StateTransition(LTC_STATEMACH_STARTMEAS, LTC_ENTRY, LTC_STATEMACH_SHORTTIME);
                    break;
                } else {
                    DIAG_Handler(DIAG_CH_LTC_SPI, DIAG_EVENT_OK, 0);
                }

                SPI_SetTransmitOngoing();
                retVal = LTC_SendEEPROMReadCommand(ltc_TXBuffer, ltc_TXPECbuffer, 1);
                LTC_CondBasedStateTransition(retVal, DIAG_CH_LTC_SPI,
                                          LTC_STATEMACH_EEPROM_READ, LTC_EEPROM_SEND_CLOCK_STCOMM2, (ltc_state.commandDataTransferTime+LTC_TRANSMISSION_TIMEOUT),
                                          LTC_STATEMACH_EEPROM_READ, LTC_EEPROM_SEND_CLOCK_STCOMM2, LTC_STATEMACH_SHORTTIME);
                break;

            } else if (ltc_state.substate == LTC_EEPROM_SEND_CLOCK_STCOMM2) {
                if (ltc_state.timer == 0 && SPI_IsTransmitOngoing() == TRUE) {
                    DIAG_Handler(DIAG_CH_LTC_SPI, DIAG_EVENT_NOK, 0);
                    LTC_StateTransition(LTC_STATEMACH_STARTMEAS, LTC_ENTRY, LTC_STATEMACH_SHORTTIME);
                    break;
                } else {
                    DIAG_Handler(DIAG_CH_LTC_SPI, DIAG_EVENT_OK, 0);
                }

                SPI_SetTransmitOngoing();
                retVal = LTC_I2CClock(ltc_TXBufferClock, ltc_TXPECBufferClock);
                LTC_CondBasedStateTransition(retVal, DIAG_CH_LTC_SPI,
                                          LTC_STATEMACH_EEPROM_READ, LTC_EEPROM_READ_I2C_TRANSMISSION_RESULT_RDCOMM, (ltc_state.gpioClocksTransferTime+LTC_TRANSMISSION_TIMEOUT),
                                          LTC_STATEMACH_EEPROM_READ, LTC_EEPROM_READ_I2C_TRANSMISSION_RESULT_RDCOMM, LTC_STATEMACH_SHORTTIME);
                break;
            }  else if (ltc_state.substate == LTC_EEPROM_READ_I2C_TRANSMISSION_RESULT_RDCOMM) {
                if (ltc_state.timer == 0 && SPI_IsTransmitOngoing() == TRUE) {
                    DIAG_Handler(DIAG_CH_LTC_SPI, DIAG_EVENT_NOK, 0);
                    LTC_StateTransition(LTC_STATEMACH_STARTMEAS, LTC_ENTRY, LTC_STATEMACH_SHORTTIME);
                    break;
                } else {
                    DIAG_Handler(DIAG_CH_LTC_SPI, DIAG_EVENT_OK, 0);
                }

                SPI_SetTransmitOngoing();
                retVal = LTC_RX((uint8_t*)ltc_cmdRDCOMM, ltc_RXPECbuffer);
                LTC_CondBasedStateTransition(retVal, DIAG_CH_LTC_SPI,
                                          LTC_STATEMACH_EEPROM_READ, LTC_EEPROM_SAVE_READ, (ltc_state.commandDataTransferTime+LTC_TRANSMISSION_TIMEOUT),
                                          LTC_STATEMACH_EEPROM_READ, LTC_EEPROM_SAVE_READ, LTC_STATEMACH_SHORTTIME);
                break;

            } else if (ltc_state.substate == LTC_EEPROM_SAVE_READ) {
                if (ltc_state.timer == 0 && SPI_IsTransmitOngoing() == TRUE) {
                    DIAG_Handler(DIAG_CH_LTC_SPI, DIAG_EVENT_NOK, 0);
                    LTC_StateTransition(LTC_STATEMACH_STARTMEAS, LTC_ENTRY, LTC_STATEMACH_SHORTTIME);
                    break;
                } else {
                    DIAG_Handler(DIAG_CH_LTC_SPI, DIAG_EVENT_OK, 0);
                }

                if (LTC_RX_PECCheck(ltc_RXPECbuffer) != E_OK) {
                    DIAG_Handler(DIAG_CH_LTC_PEC, DIAG_EVENT_NOK, 0);
                } else {
                    DIAG_Handler(DIAG_CH_LTC_PEC, DIAG_EVENT_OK, 0);
                    LTC_EEPROMSaveReadValue(ltc_RXPECbuffer);
                }
                LTC_StateTransition(LTC_STATEMACH_STARTMEAS, LTC_ENTRY, LTC_STATEMACH_SHORTTIME);
                break;
            }

            break;

        /****************************EEPROM READ*********************************/
        case LTC_STATEMACH_EEPROM_WRITE:

            if (ltc_state.substate == LTC_EEPROM_WRITE_DATA1) {
                ltc_state.check_spi_flag = TRUE;
                SPI_SetTransmitOngoing();
                retVal = LTC_SendEEPROMWriteCommand(ltc_TXBuffer, ltc_TXPECbuffer, 0);

                if (retVal != E_OK) {
                    DIAG_Handler(DIAG_CH_LTC_SPI, DIAG_EVENT_NOK, 0);
                    ++ltc_state.muxmeas_seqptr;
                    LTC_StateTransition(LTC_STATEMACH_STARTMEAS, LTC_ENTRY, LTC_STATEMACH_SHORTTIME);
                } else {
                    DIAG_Handler(DIAG_CH_LTC_SPI, DIAG_EVENT_OK, 0);
                    LTC_StateTransition(LTC_STATEMACH_EEPROM_WRITE, LTC_EEPROM_SEND_CLOCK_STCOMM3, (ltc_state.commandDataTransferTime+LTC_TRANSMISSION_TIMEOUT));
                }

                break;

            } else if (ltc_state.substate == LTC_EEPROM_SEND_CLOCK_STCOMM3) {
                if (ltc_state.timer == 0 && SPI_IsTransmitOngoing() == TRUE) {
                    DIAG_Handler(DIAG_CH_LTC_SPI, DIAG_EVENT_NOK, 0);
                    LTC_StateTransition(LTC_STATEMACH_STARTMEAS, LTC_ENTRY, LTC_STATEMACH_SHORTTIME);
                    break;
                } else {
                    DIAG_Handler(DIAG_CH_LTC_SPI, DIAG_EVENT_OK, 0);
                }

                SPI_SetTransmitOngoing();
                retVal = LTC_I2CClock(ltc_TXBufferClock, ltc_TXPECBufferClock);
                LTC_CondBasedStateTransition(retVal, DIAG_CH_LTC_SPI,
                                          LTC_STATEMACH_EEPROM_WRITE, LTC_EEPROM_WRITE_DATA2, (ltc_state.gpioClocksTransferTime+LTC_TRANSMISSION_TIMEOUT),
                                          LTC_STATEMACH_EEPROM_WRITE, LTC_EEPROM_WRITE_DATA2, LTC_STATEMACH_SHORTTIME);
                break;

            } else if (ltc_state.substate == LTC_EEPROM_WRITE_DATA2) {
                if (ltc_state.timer == 0 && SPI_IsTransmitOngoing() == TRUE) {
                    DIAG_Handler(DIAG_CH_LTC_SPI, DIAG_EVENT_NOK, 0);
                    LTC_StateTransition(LTC_STATEMACH_STARTMEAS, LTC_ENTRY, LTC_STATEMACH_SHORTTIME);
                    break;
                } else {
                    DIAG_Handler(DIAG_CH_LTC_SPI, DIAG_EVENT_OK, 0);
                }

                SPI_SetTransmitOngoing();
                retVal = LTC_SendEEPROMWriteCommand(ltc_TXBuffer, ltc_TXPECbuffer, 1);
                LTC_CondBasedStateTransition(retVal, DIAG_CH_LTC_SPI,
                                          LTC_STATEMACH_EEPROM_WRITE, LTC_EEPROM_SEND_CLOCK_STCOMM4, (ltc_state.commandDataTransferTime+LTC_TRANSMISSION_TIMEOUT),
                                          LTC_STATEMACH_EEPROM_WRITE, LTC_EEPROM_SEND_CLOCK_STCOMM4, LTC_STATEMACH_SHORTTIME);
                break;

            } else if (ltc_state.substate == LTC_EEPROM_SEND_CLOCK_STCOMM4) {
                if (ltc_state.timer == 0 && SPI_IsTransmitOngoing() == TRUE) {
                    DIAG_Handler(DIAG_CH_LTC_SPI, DIAG_EVENT_NOK, 0);
                    LTC_StateTransition(LTC_STATEMACH_STARTMEAS, LTC_ENTRY, LTC_STATEMACH_SHORTTIME);
                    break;
                } else {
                    DIAG_Handler(DIAG_CH_LTC_SPI, DIAG_EVENT_OK, 0);
                }

                SPI_SetTransmitOngoing();
                retVal = LTC_I2CClock(ltc_TXBufferClock, ltc_TXPECBufferClock);
                LTC_CondBasedStateTransition(retVal, DIAG_CH_LTC_SPI,
                                          LTC_STATEMACH_EEPROM_WRITE, LTC_EEPROM_FINISHED, (ltc_state.gpioClocksTransferTime+LTC_TRANSMISSION_TIMEOUT),
                                          LTC_STATEMACH_EEPROM_WRITE, LTC_EEPROM_FINISHED, LTC_STATEMACH_SHORTTIME);
                break;
            }  else if (ltc_state.substate == LTC_EEPROM_FINISHED) {
                if (ltc_state.timer == 0 && SPI_IsTransmitOngoing() == TRUE) {
                    DIAG_Handler(DIAG_CH_LTC_SPI, DIAG_EVENT_NOK, 0);
                    LTC_StateTransition(LTC_STATEMACH_STARTMEAS, LTC_ENTRY, LTC_STATEMACH_SHORTTIME);
                    break;
                } else {
                    DIAG_Handler(DIAG_CH_LTC_SPI, DIAG_EVENT_OK, 0);
                }
                LTC_StateTransition(LTC_STATEMACH_STARTMEAS, LTC_ENTRY, LTC_STATEMACH_SHORTTIME);
                break;
            }

            break;

        /**************************OPEN-WIRE CHECK*******************************/
        case LTC_STATEMACH_OPENWIRE_CHECK:
            if (ltc_state.substate == LTC_REQUEST_PULLUP_CURRENT_OPENWIRE_CHECK) {
                /* Run ADOW command with PUP = 1 */
                ltc_state.adcMode = LTC_OW_MEASUREMENT_MODE;
                ltc_state.check_spi_flag = FALSE;

                retVal = LTC_StartOpenWireMeasurement(ltc_state.adcMode, 1);
                if (retVal == E_OK) {
                    DIAG_Handler(DIAG_CH_LTC_SPI, DIAG_EVENT_OK, 0);
                    LTC_StateTransition(LTC_STATEMACH_OPENWIRE_CHECK, LTC_REQUEST_PULLUP_CURRENT_OPENWIRE_CHECK, (ltc_state.commandDataTransferTime + LTC_Get_MeasurementTCycle(ltc_state.adcMode, LTC_ADCMEAS_ALLCHANNEL)));
                    ltc_state.resendCommandCounter--;

                    /* Check how many retries are left */
                    if (ltc_state.resendCommandCounter == 0) {
                        /* Switch to read voltage state to read cell voltages */
                        LTC_StateTransition(LTC_STATEMACH_READVOLTAGE, LTC_READ_VOLTAGE_REGISTER_A_RDCVA_READVOLTAGE, (ltc_state.commandDataTransferTime + LTC_Get_MeasurementTCycle(ltc_state.adcMode, LTC_ADCMEAS_ALLCHANNEL)));
                        /* Reuse read voltage register */
                        ltc_state.reusageMeasurementMode = LTC_REUSE_READVOLT_FOR_ADOW_PUP;
                    }
                } else {
                    DIAG_Handler(DIAG_CH_LTC_SPI, DIAG_EVENT_NOK, 0);
                    LTC_StateTransition(LTC_STATEMACH_STARTMEAS, LTC_ENTRY, LTC_STATEMACH_SHORTTIME);
                }
            } else if (ltc_state.substate == LTC_READ_VOLTAGES_PULLUP_OPENWIRE_CHECK) {
                /* Previous state: Read voltage -> information stored in voltage buffer */
                ltc_state.reusageMeasurementMode = LTC_NOT_REUSED;

                /* Copy data from voltage struct into open-wire struct */
                for (uint16_t i = 0; i < BS_NR_OF_BAT_CELLS; i++) {
                    ltc_openwire_pup_buffer[i] = ltc_cellvoltage.voltage[i];
                }

                /* Set number of ADOW retries - send ADOW command with pull-down two times */
                ltc_state.resendCommandCounter = LTC_NMBR_REQ_ADOW_COMMANDS;
                LTC_StateTransition(LTC_STATEMACH_OPENWIRE_CHECK, LTC_REQUEST_PULLDOWN_CURRENT_OPENWIRE_CHECK, LTC_STATEMACH_SHORTTIME);

            } else if (ltc_state.substate == LTC_REQUEST_PULLDOWN_CURRENT_OPENWIRE_CHECK) {
                /* Run ADOW command with PUP = 0 */
                ltc_state.adcMode = LTC_OW_MEASUREMENT_MODE;
                ltc_state.check_spi_flag = FALSE;

                retVal = LTC_StartOpenWireMeasurement(ltc_state.adcMode, 0);
                if (retVal == E_OK) {
                    DIAG_Handler(DIAG_CH_LTC_SPI, DIAG_EVENT_OK, 0);
                    LTC_StateTransition(LTC_STATEMACH_OPENWIRE_CHECK, LTC_REQUEST_PULLDOWN_CURRENT_OPENWIRE_CHECK, (ltc_state.commandDataTransferTime + LTC_Get_MeasurementTCycle(ltc_state.adcMode, LTC_ADCMEAS_ALLCHANNEL)));
                    ltc_state.resendCommandCounter--;

                    /* Check how many retries are left */
                    if (ltc_state.resendCommandCounter == 0) {
                        /* Switch to read voltage state to read cell voltages */
                        LTC_StateTransition(LTC_STATEMACH_READVOLTAGE, LTC_READ_VOLTAGE_REGISTER_A_RDCVA_READVOLTAGE, (ltc_state.commandDataTransferTime + LTC_Get_MeasurementTCycle(ltc_state.adcMode, LTC_ADCMEAS_ALLCHANNEL)));
                        /* Reuse read voltage register */
                        ltc_state.reusageMeasurementMode = LTC_REUSE_READVOLT_FOR_ADOW_PDOWN;
                    }
                } else {
                    DIAG_Handler(DIAG_CH_LTC_SPI, DIAG_EVENT_NOK, 0);
                    LTC_StateTransition(LTC_STATEMACH_STARTMEAS, LTC_ENTRY, LTC_STATEMACH_SHORTTIME);
                }
            } else if (ltc_state.substate == LTC_READ_VOLTAGES_PULLDOWN_OPENWIRE_CHECK) {
                /* Previous state: Read voltage -> information stored in voltage buffer */
                ltc_state.reusageMeasurementMode = LTC_NOT_REUSED;

                /* Copy data from voltage struct into open-wire struct */
                for (uint16_t i = 0; i < BS_NR_OF_BAT_CELLS; i++) {
                    ltc_openwire_pdown_buffer[i] = ltc_cellvoltage.voltage[i];
                }
                LTC_StateTransition(LTC_STATEMACH_OPENWIRE_CHECK, LTC_PERFORM_OPENWIRE_CHECK, LTC_STATEMACH_SHORTTIME);
            } else if (ltc_state.substate == LTC_PERFORM_OPENWIRE_CHECK) {
                /* Perform actual open-wire check */
                for (uint8_t m = 0; m < BS_NR_OF_MODULES; m++) {
                    /* Open-wire at C0: cell_pup(0) == 0 */
                    if (ltc_openwire_pup_buffer[0 + (m*BS_NR_OF_BAT_CELLS_PER_MODULE)] == 0) {
                        ltc_openwire.openwire[0 + (m*(BS_NR_OF_BAT_CELLS_PER_MODULE))] = 1;
                    }
                    /* Open-wire at Cmax: cell_pdown(BS_NR_OF_BAT_CELLS_PER_MODULE-1) == 0 */
                    if (ltc_openwire_pdown_buffer[((BS_NR_OF_BAT_CELLS_PER_MODULE-1) + (m*BS_NR_OF_BAT_CELLS_PER_MODULE))] == 0) {
                        ltc_openwire.openwire[BS_NR_OF_BAT_CELLS_PER_MODULE + (m*BS_NR_OF_BAT_CELLS_PER_MODULE)] = 1;
                    }
                }

                /* Take difference between pull-up and pull-down measurement */
                for (uint16_t i = 1; i < BS_NR_OF_BAT_CELLS; i++) {
                    ltc_openwire_delta[i] = (int32_t)(ltc_openwire_pup_buffer[i] - ltc_openwire_pdown_buffer[i]);
                }

                /* Open-wire at C(N): delta cell(n+1) < -400mV */
                for (uint8_t m = 0; m < BS_NR_OF_MODULES; m++) {
                    for (uint8_t c = 1; c < BS_NR_OF_BAT_CELLS_PER_MODULE-1; c++) {
                        if (ltc_openwire_delta[c + (m*BS_NR_OF_BAT_CELLS_PER_MODULE)] < -400) {
                            ltc_openwire.openwire[c + (m*BS_NR_OF_BAT_CELLS_PER_MODULE)] = 1;
                        }
                    }
                }

                /* Write database entry */
                DB_WriteBlock(&ltc_openwire, DATA_BLOCK_ID_OPEN_WIRE);
                /* Start new measurement cycle */
                LTC_StateTransition(LTC_STATEMACH_STARTMEAS, LTC_ENTRY, LTC_STATEMACH_SHORTTIME);
            }
            break;

        /****************************DEFAULT**************************/
        default:
            break;
    }

    ltc_state.triggerentry--;        /* reentrance counter */
}



/**
 * @brief   saves the multiplexer values read from the LTC daisy-chain.
 *
 * After a voltage measurement was initiated on GPIO 1 to read the currently selected
 * multiplexer voltage, the results is read via SPI from the daisy-chain.
 * This function is called to store the result from the transmission in a buffer.
 *
 * @param   *DataBufferSPI_RX   buffer containing the data obtained from the SPI transmission
 * @param   muxseqptr           pointer to the multiplexer sequence, which configures the currently selected multiplexer ID and channel
 */
static void LTC_SaveMuxMeasurement(uint8_t *rxBuffer, LTC_MUX_CH_CFG_s  *muxseqptr) {
    uint16_t i = 0;
    uint16_t val_ui = 0;
    int16_t temperature = 0;
    uint8_t sensor_idx = 0;
    uint8_t ch_idx = 0;
    uint32_t bitmask = 0;

    /* pointer to measurement Sequence of Mux- and Channel-Configurations (1,0xFF)...(3,0xFF),(0,1),...(0,7)) */
    if (muxseqptr->muxCh == 0xFF)
        return; /* Channel 0xFF means that the multiplexer is deactivated, therefore no measurement will be made and saved*/

    /* user multiplexer type -> connected to GPIO2! */
    if (muxseqptr->muxID == 1 || muxseqptr->muxID == 2) {
        for (i=0; i < LTC_N_LTC; i++) {
            if (muxseqptr->muxID == 1)
                ch_idx = 0 + muxseqptr->muxCh;    /* channel index 0..7 */
            else
                ch_idx = 8 + muxseqptr->muxCh;    /* channel index 8..15 */

            if (ch_idx < 2*8) {
                val_ui =*((uint16_t *)(&rxBuffer[6+1*i*8]));        /* raw values, all mux on all LTCs */
                ltc_user_mux.value[i*8*2+ch_idx] = (uint16_t)(((float)(val_ui))*100e-6f*1000.0f);  /* Unit -> in V -> in mV */
            }
        }
    } else {
        /* temperature multiplexer type -> connected to GPIO1! */
        for (i=0; i < LTC_N_LTC; i++) {
            val_ui = *((uint16_t *)(&rxBuffer[4+i*8]));
            /* GPIO voltage in 100uV -> * 0.1 ----  conversion to V from mV * 0.001 ----- -> 0.0001 */
            temperature = (int16_t)LTC_Convert_MuxVoltages_to_Temperatures((float)(val_ui)*0.0001f);        /* Unit Celsius */
            sensor_idx = ltc_muxsensortemperatur_cfg[muxseqptr->muxCh];
            /* if wrong configuration: exit and write nothing */
            if (sensor_idx >= BS_NR_OF_TEMP_SENSORS_PER_MODULE)
                return;
            /* Set bitmask for valid flags */
            bitmask |= 1 < sensor_idx;
            /* Check LTC PEC error */
            if (LTC_ErrorTable[i].PEC_valid == TRUE) {
                bitmask = ~bitmask;  /* negate bitmask to only validate flags of this cell voltage */
                ltc_celltemperature.valid_temperature[i] &= bitmask;
                ltc_celltemperature.temperature[i*(BS_NR_OF_TEMP_SENSORS_PER_MODULE)+sensor_idx] = temperature;
            } else {
                ltc_celltemperature.valid_temperature[i] |= bitmask;
            }
        }
    }
}



/**
 * @brief   saves the voltage values read from the LTC daisy-chain.
 *
 * After a voltage measurement was initiated to measure the voltages of the cells,
 * the result is read via SPI from the daisy-chain.
 * There are 6 register to read _(A,B,C,D,E,F) to get all cell voltages.
 * Only one register can be read at a time.
 * This function is called to store the result from the transmission in a buffer.
 *
 * @param   registerSet    voltage register that was read (voltage register A,B,C,D,E or F)
 * @param   *rxBuffer      buffer containing the data obtained from the SPI transmission
 * @param   PEC_valid      tells the functions if the PEC is valid or not, if not, manage indices but do not store
 *
 */
static void LTC_SaveRXtoVoltagebuffer(uint8_t registerSet, uint8_t *rxBuffer) {
    uint16_t i = 0;
    uint16_t j = 0;
    uint16_t i_offset = 0;
    uint16_t voltage_index = 0;
    uint16_t val_ui = 0;
    uint16_t voltage = 0;
    uint8_t incrementations = 0;
    uint32_t bitmask = 0;

    if (registerSet == 0) {
    /* RDCVA command -> voltage register group A */
        i_offset = 0;
    } else if (registerSet == 1) {
    /* RDCVB command -> voltage register group B */
        i_offset = 3;
    } else if (registerSet == 2) {
    /* RDCVC command -> voltage register group C */
        i_offset = 6;
    } else if (registerSet == 3) {
    /* RDCVD command -> voltage register group D */
        i_offset = 9;
    } else if (registerSet == 4) {
    /* RDCVD command -> voltage register group E (only for 15 and 18 cell version) */
        i_offset = 12;
    } else if (registerSet == 5) {
    /* RDCVD command -> voltage register group F (only for 18 cell version) */
        i_offset = 15;
    } else {
        return;
    }

    /* Calculate bitmask for valid flags */
    bitmask |= 0x07 << i_offset;    /* 0x07: three voltages in each register */

    /* reinitialize index counter at begin of cycle */
    if (i_offset == 0) {
        ltc_used_cells_index = 0;
    }

    /* Retrieve data without command and CRC*/
    for (i=0; i < LTC_N_LTC; i++) {
        incrementations = 0;

        /* parse all three voltages (3 * 2bytes) contained in one register */
        for (j=0; j < 3; j++) {
            /* index considering maximum number of cells */
            voltage_index = j+i_offset;

            if (ltc_voltage_input_used[voltage_index] == 1) {
                val_ui = *((uint16_t *)(&rxBuffer[4+2*j+i*8]));
                voltage = (uint16_t)(((float)(val_ui))*100e-6f*1000.0f);        /* Unit V -> in mV */
                /* Check PEC for every LTC in the daisy-chain */
                if (LTC_ErrorTable[i].PEC_valid == TRUE) {
                    ltc_cellvoltage.voltage[ltc_used_cells_index+i*(BS_NR_OF_BAT_CELLS_PER_MODULE)] = voltage;
                    bitmask = ~bitmask;  /* negate bitmask to only validate flags of this voltage register */
                    ltc_cellvoltage.valid_volt[(i/LTC_NUMBER_OF_LTC_PER_MODULE)] &= bitmask;
                } else {
                    /* PEC_valid == FALSE: Invalidate only flags of this voltage register */
                    ltc_cellvoltage.valid_volt[(i/LTC_NUMBER_OF_LTC_PER_MODULE)] |= bitmask;
                }

                ltc_used_cells_index++;
                incrementations++;

                if (ltc_used_cells_index > BS_NR_OF_BAT_CELLS_PER_MODULE) {
                    return;
                }
            }
        }
        /* restore start value for next module */
#pragma GCC diagnostic push
        /* This warning is allowed for the edge case
         * LTC_N_LTC == 1
         */
#pragma GCC diagnostic ignored "-Wtype-limits"
        if (i < LTC_N_LTC-1) {
#pragma GCC diagnostic pop
            ltc_used_cells_index -= incrementations;
        }
    }
}

/**
 * @brief   saves the GPIO voltage values read from the LTC daisy-chain.
 *
 * After a voltage measurement was initiated to measure the voltages on all GPIOs,
 * the result is read via SPI from the daisy-chain. In order to read the result of all GPIO measurements,
 * it is necessary to read auxiliary register A and B.
 * Only one register can be read at a time.
 * This function is called to store the result from the transmission in a buffer.
 *
 * @param   registerSet    voltage register that was read (auxiliary register A, B, C or D)
 * @param   *rxBuffer      buffer containing the data obtained from the SPI transmission
 *
 */
static void LTC_SaveRXtoGPIOBuffer(uint8_t registerSet, uint8_t *rxBuffer) {
    uint16_t i = 0;
    uint8_t i_offset = 0;
    uint32_t bitmask = 0;

    if (registerSet == 0) {
    /* RDAUXA command -> GPIO register group A */
        i_offset = 0;
        bitmask = 0x07 << i_offset;  /* 0x07: three temperatures in this register */
        /* Retrieve data without command and CRC*/
        for (i = 0; i < LTC_N_LTC; i++) {
            /* Check if PEC is valid */
            if (LTC_ErrorTable[i].PEC_valid == TRUE) {
                bitmask = ~bitmask; /* negate bitmask to only validate flags of this voltage register */
                ltc_allgpiovoltage.valid_gpiovoltages[i] &= bitmask;
                /* values received in 100uV -> divide by 10 to convert to mV */
                ltc_allgpiovoltage.gpiovoltage[0 + i_offset + BS_NR_OF_GPIOS_PER_MODULE*i]= *((uint16_t *)(&rxBuffer[4+i*8]))/10;
                ltc_allgpiovoltage.gpiovoltage[1 + i_offset + BS_NR_OF_GPIOS_PER_MODULE*i]= *((uint16_t *)(&rxBuffer[6+i*8]))/10;
                ltc_allgpiovoltage.gpiovoltage[2 + i_offset + BS_NR_OF_GPIOS_PER_MODULE*i]= *((uint16_t *)(&rxBuffer[8+i*8]))/10;
            } else {
                ltc_allgpiovoltage.valid_gpiovoltages[i] |= bitmask;
            }
        }
    } else if (registerSet == 1) {
        /* RDAUXB command -> GPIO register group B */
        i_offset = 3;
        bitmask = 0x03 << i_offset;  /* 0x03: two temperatures in this register */
        /* Retrieve data without command and CRC*/
        for (i = 0; i < LTC_N_LTC; i++) {
            /* Check if PEC is valid */
            if (LTC_ErrorTable[i].PEC_valid == TRUE) {
                bitmask = ~bitmask; /* negate bitmask to only validate flags of this voltage register */
                ltc_allgpiovoltage.valid_gpiovoltages[i] &= bitmask;
                /* values received in 100uV -> divide by 10 to convert to mV */
                ltc_allgpiovoltage.gpiovoltage[0 + i_offset + BS_NR_OF_GPIOS_PER_MODULE*i]= *((uint16_t *)(&rxBuffer[4+i*8]))/10;
                ltc_allgpiovoltage.gpiovoltage[1 + i_offset + BS_NR_OF_GPIOS_PER_MODULE*i]= *((uint16_t *)(&rxBuffer[6+i*8]))/10;
            } else {
                ltc_allgpiovoltage.valid_gpiovoltages[i] |= bitmask;
            }
        }
    } else if (registerSet == 2) {
        /* RDAUXC command -> GPIO register group C, for 18 cell version */
        i_offset = 5;
        bitmask = 0x07 << i_offset;  /* 0x07: three temperatures in this register */
        /* Retrieve data without command and CRC*/
        for (i = 0; i < LTC_N_LTC; i++) {
            /* Check if PEC is valid */
            if (LTC_ErrorTable[i].PEC_valid == TRUE) {
                bitmask = ~bitmask; /* negate bitmask to only validate flags of this voltage register */
                ltc_allgpiovoltage.valid_gpiovoltages[i] &= bitmask;
                /* values received in 100uV -> divide by 10 to convert to mV */
                ltc_allgpiovoltage.gpiovoltage[0 + i_offset + BS_NR_OF_GPIOS_PER_MODULE*i]= *((uint16_t *)(&rxBuffer[4+i*8]))/10;
                ltc_allgpiovoltage.gpiovoltage[1 + i_offset + BS_NR_OF_GPIOS_PER_MODULE*i]= *((uint16_t *)(&rxBuffer[6+i*8]))/10;
                ltc_allgpiovoltage.gpiovoltage[2 + i_offset + BS_NR_OF_GPIOS_PER_MODULE*i]= *((uint16_t *)(&rxBuffer[8+i*8]))/10;
            } else {
                ltc_allgpiovoltage.valid_gpiovoltages[i] |= bitmask;
            }
        }
    } else if (registerSet == 3) {
        /* RDAUXD command -> GPIO register group D, for 18 cell version */
        i_offset = 8;
        bitmask = 0x01 << i_offset;  /* 0x01: one temperature in this register */
        /* Retrieve data without command and CRC*/
        for (i = 0; i < LTC_N_LTC; i++) {
            /* Check if PEC is valid */
            if (LTC_ErrorTable[i].PEC_valid == TRUE) {
                bitmask = ~bitmask; /* negate bitmask to only validate flags of this voltage register */
                ltc_allgpiovoltage.valid_gpiovoltages[i] &= bitmask;
                /* values received in 100uV -> divide by 10 to convert to mV */
                ltc_allgpiovoltage.gpiovoltage[0 + i_offset + BS_NR_OF_GPIOS_PER_MODULE*i]= *((uint16_t *)(&rxBuffer[4+i*8]))/10;
            } else {
                ltc_allgpiovoltage.valid_gpiovoltages[i] |= bitmask;
            }
        }
    } else {
        return;
    }
}


/**
 * @brief   checks if the multiplexers acknowledged transmission.
 *
 * The RDCOMM command can be used to read the answer of the multiplexers to a
 * I2C transmission.
 * This function determines if the communication with the multiplexers was
 * successful or not.
 * The array LTC_ErrorTable is updated to locate the multiplexers that did not
 * acknowledge transmission.
 *
 * @param   *DataBufferSPI_RX    data obtained from the SPI transmission
 * @param   mux                  multiplexer to be addressed (multiplexer ID)
 *
 * @return  mux_error            0 is there was no error, 1 if there was errors
 */
static uint8_t LTC_I2CCheckACK(uint8_t *DataBufferSPI_RX, int mux) {
    uint8_t mux_error = E_OK;
    uint16_t i = 0;

    for (i=0; i < BS_NR_OF_MODULES; i++) {
        if (mux == 0) {
            if ((DataBufferSPI_RX[4+1+LTC_NUMBER_OF_LTC_PER_MODULE*i*8] & 0x0F) != 0x07) {  /* ACK = 0xX7 */
                if (LTC_DISCARD_MUX_CHECK == FALSE) {
                    LTC_ErrorTable[i].mux0 = 1;
                }
                mux_error = E_NOT_OK;
            } else {
                LTC_ErrorTable[i].mux0 = 0;
            }
        }
        if (mux == 1) {
            if ((DataBufferSPI_RX[4+1+LTC_NUMBER_OF_LTC_PER_MODULE*i*8] & 0x0F) != 0x27) {
                if (LTC_DISCARD_MUX_CHECK == FALSE) {
                    LTC_ErrorTable[i].mux1 = 1;
                }
                mux_error = E_NOT_OK;
            } else {
                LTC_ErrorTable[i].mux1 = 0;
            }
        }
        if (mux == 2) {
            if ((DataBufferSPI_RX[4+1+LTC_NUMBER_OF_LTC_PER_MODULE*i*8] & 0x0F) != 0x47) {
                if (LTC_DISCARD_MUX_CHECK == FALSE) {
                    LTC_ErrorTable[i].mux2 = 1;
                }
                mux_error = E_NOT_OK;
            } else {
                LTC_ErrorTable[i].mux2 = 0;
            }
        }
        if (mux == 3) {
            if ((DataBufferSPI_RX[4+1+LTC_NUMBER_OF_LTC_PER_MODULE*i*8] & 0x0F) != 0x67) {
                if (LTC_DISCARD_MUX_CHECK == FALSE) {
                    LTC_ErrorTable[i].mux3 = 1;
                }
                mux_error = E_NOT_OK;
            } else {
                LTC_ErrorTable[i].mux3 = 0;
            }
        }
    }

    if (LTC_DISCARD_MUX_CHECK == TRUE) {
        return 0;
    } else {
        return mux_error;
    }
}
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
