ArakniD/foxbms/embedded-software/mcu-primary/src/module/config/cansignal_cfg.c

/**
 *
 * @copyright &copy; 2010 - 2019, Fraunhofer-Gesellschaft zur Foerderung der
 *  angewandten Forschung e.V. All rights reserved.
 *
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
 * We kindly request you to use one or more of the following phrases to refer
 * to foxBMS in your hardware, software, documentation or advertising
 * materials:
 *
 * &Prime;This product uses parts of foxBMS&reg;&Prime;
 *
 * &Prime;This product includes parts of foxBMS&reg;&Prime;
 *
 * &Prime;This product is derived from foxBMS&reg;&Prime;
 *
 */

/**
 * @file    cansignal_cfg.c
 * @author  foxBMS Team
 * @date    16.09.2015 (date of creation)
 * @ingroup DRIVERS_CONF
 * @prefix  CANS
 *
 * @brief   Configuration of the messages and signal settings for the CAN driver
 *
 */

/*================== Includes ===============================================*/
#include "cansignal_cfg.h"

#include "bal.h"
#include "database.h"
#include "diag.h"
#include "sox.h"
#include "sys.h"

/*================== Macros and Definitions =================================*/
static DATA_BLOCK_CURRENT_SENSOR_s cans_current_tab;

#define CANS_MODULSIGNALS_VOLT      (CAN0_SIG_Mod0_temp_valid_0_2 - CAN0_SIG_Mod0_volt_valid_0_2)
#define CANS_MODULSIGNALS_TEMP      (CAN0_SIG_Mod1_volt_valid_0_2 - CAN0_SIG_Mod0_temp_valid_0_2)


/*================== Static Function Prototypes =============================*/

static float cans_checkLimits(float value, uint32_t sigIdx);

/* TX/Getter functions */
static uint32_t cans_getvolt(uint32_t, void *);
static uint32_t cans_gettempering(uint32_t, void *);
static uint32_t cans_getcanerr(uint32_t, void *);
static uint32_t cans_gettemp(uint32_t, void *);
static uint32_t cans_getsoc(uint32_t, void *);
static uint32_t cans_getRecommendedOperatingCurrent(uint32_t, void *);
static uint32_t cans_getMaxAllowedPower(uint32_t, void *);
static uint32_t cans_getpower(uint32_t, void *);
static uint32_t cans_getcurr(uint32_t, void *);
static uint32_t cans_getPackVoltage(uint32_t, void *);
static uint32_t cans_getminmaxvolt(uint32_t, void *);
static uint32_t cans_getminmaxtemp(uint32_t, void *);
static uint32_t cans_getisoguard(uint32_t, void *);


/* RX/Setter functions */
static uint32_t cans_setcurr(uint32_t, void *);
static uint32_t cans_setstaterequest(uint32_t, void *);
static uint32_t cans_setdebug(uint32_t, void *);
static uint32_t cans_setSWversion(uint32_t, void *);


#ifdef CURRENT_SENSOR_ISABELLENHUETTE_TRIGGERED
static uint32_t cans_gettriggercurrent(uint32_t sigIdx, void *value);
#endif /* CURRENT_SENSOR_ISABELLENHUETTE_TRIGGERED */



/*================== Static Constant and Variable Definitions ===============*/

/*================== Extern Constant and Variable Definitions ===============*/

const CANS_signal_s cans_CAN0_signals_tx[] = {
    { {CAN0_MSG_SystemState_0}, 0, 3, 0, 7, 1, 0, NULL_PTR, &cans_getcanerr },  /*!< CAN0_SIG_GS0_general_error, */
    { {CAN0_MSG_SystemState_0}, 8, 8, 0, UINT8_MAX, 1, 0, NULL_PTR, &cans_getcanerr },  /*!< CAN0_SIG_GS0_current_state, */
    { {CAN0_MSG_SystemState_0}, 16, 3, 0, 7, 1, 0, NULL_PTR, &cans_getcanerr },  /*!< CAN0_SIG_GS0_error_overtemp_charge, */
    { {CAN0_MSG_SystemState_0}, 24, 3, 0, 7, 1, 0, NULL_PTR, &cans_getcanerr },  /*!< CAN0_SIG_GS0_error_undertemp_charge, */
    { {CAN0_MSG_SystemState_0}, 32, 3, 0, 7, 1, 0, NULL_PTR, &cans_getcanerr },  /*!< CAN0_SIG_GS0_error_overtemp_discharge, */
    { {CAN0_MSG_SystemState_0}, 40, 3, 0, 7, 1, 0, NULL_PTR, &cans_getcanerr },  /*!< CAN0_SIG_GS0_error_undertemp_discharge, */
    { {CAN0_MSG_SystemState_0}, 48, 3, 0, 7, 1, 0, NULL_PTR, &cans_getcanerr },  /*!< CAN0_SIG_GS0_error_overcurrent_charge, */
    { {CAN0_MSG_SystemState_0}, 56, 3, 0, 7, 1, 0, NULL_PTR, &cans_getcanerr },  /*!< CAN0_SIG_GS0_error_overcurrent_discharge, */

    { {CAN0_MSG_SystemState_1}, 0, 3, 0, 7, 1, 0, NULL_PTR, &cans_getcanerr },  /*!< CAN0_SIG_GS1_error_overvoltage, */
    { {CAN0_MSG_SystemState_1}, 8, 3, 0, 7, 1, 0, NULL_PTR, &cans_getcanerr },  /*!< CAN0_SIG_GS1_error_undervoltage, */
    { {CAN0_MSG_SystemState_1}, 11, 1, 0, 1, 1, 0, NULL_PTR, &cans_getcanerr },  /*!< CAN0_SIG_GS1_error_deep_discharge, */
    { {CAN0_MSG_SystemState_1}, 16, 1, 0, 1, 1, 0, NULL_PTR, &cans_getcanerr },  /*!< CAN0_SIG_GS1_error_temperature_MCU0 */
    { {CAN0_MSG_SystemState_1}, 24, 1, 0, 1, 1, 0, NULL_PTR, &cans_getcanerr },  /*!< CAN0_SIG_GS1_error_contactor */
    { {CAN0_MSG_SystemState_1}, 32, 1, 0, 1, 1, 0, NULL_PTR, &cans_getcanerr },  /*!< CAN0_SIG_GS1_error_selftest, */
    { {CAN0_MSG_SystemState_1}, 40, 1, 0, 1, 1, 0, NULL_PTR, &cans_getcanerr },  /*!< CAN_SIG_GS1_error_cantiming, */
    { {CAN0_MSG_SystemState_1}, 48, 1, 0, 1, 1, 0, NULL_PTR, &cans_getcanerr },  /*!< CAN0_SIG_GS1_current_sensor, */
    { {CAN0_MSG_SystemState_1}, 56, 1, 0, 1, 1, 0, NULL_PTR, &cans_getcanerr },  /*!< CAN0_SIG_GS1_balancing_active, */

    { {CAN0_MSG_SystemState_2}, 0, 16, 0, UINT16_MAX, 1, 0, NULL_PTR, &cans_getcanerr },  /*!< CAN0_SIG_GS2_states_relays */
    { {CAN0_MSG_SystemState_2}, 16, 1, 0, 1, 1, 0, NULL_PTR, &cans_getcanerr },   /*!< CAN0_SIG_GS2_error_insulation */
    { {CAN0_MSG_SystemState_2}, 24, 4, 0, 15, 1, 0, NULL_PTR, &cans_getcanerr },  /*!< CAN0_SIG_GS2_fuse_state */
    { {CAN0_MSG_SystemState_2}, 32, 2, 0, 3, 1, 0, NULL_PTR, &cans_getcanerr },   /*!< CAN0_SIG_GS2_lowCoinCellVolt */
    { {CAN0_MSG_SystemState_2}, 40, 1, 0, 1, 1, 0, NULL_PTR, &cans_getcanerr },   /*!< CAN0_SIG_GS2_error_openWire */
    { {CAN0_MSG_SystemState_2}, 48, 3, 0, 7, 1, 0, NULL_PTR, &cans_getcanerr },   /*!< CAN0_SIG_GS2_daisyChain */
    { {CAN0_MSG_SystemState_2}, 56, 3, 0, 7, 1, 0, NULL_PTR, &cans_getcanerr },   /*!< CAN0_SIG_GS2_plausibilityCheck */

    { {CAN0_MSG_SlaveState_0}, 0, 64, 0, UINT64_MAX, 1, 0, NULL_PTR, NULL_PTR },  /*!< CAN0_SIG_SS0_states */
    { {CAN0_MSG_SlaveState_1}, 0, 64, 0, UINT64_MAX, 1, 0, NULL_PTR, NULL_PTR },  /*!< CAN0_SIG_SS0_states */

    { {CAN0_MSG_RecOperatingCurrent}, 0, 16, 0, 6553.5, 10, 0, NULL_PTR, &cans_getRecommendedOperatingCurrent },  /*!< CAN0_SIG_MaxChargeCurrent */
    { {CAN0_MSG_RecOperatingCurrent}, 16, 16, 0, 6553.5, 10, 0, NULL_PTR, &cans_getRecommendedOperatingCurrent },  /*!< CAN0_SIG_MaxChargeCurrent_Peak */
    { {CAN0_MSG_RecOperatingCurrent}, 32, 16, 0, 6553.5, 10, 0, NULL_PTR, &cans_getRecommendedOperatingCurrent },  /*!< CAN0_SIG_MaxDischargeCurrent */
    { {CAN0_MSG_RecOperatingCurrent}, 48, 16, 0, 6553.5, 10, 0, NULL_PTR, &cans_getRecommendedOperatingCurrent },  /*!< CAN0_SIG_MaxDischargeCurrent_Peak */

    { {CAN0_MSG_SOP}, 0, 16, 0, 6553.5, 10, 0, NULL_PTR, &cans_getMaxAllowedPower },  /*!< CAN0_SIG_MaxChargePower */
    { {CAN0_MSG_SOP}, 16, 16, 0, 6553.5, 10, 0, NULL_PTR, &cans_getMaxAllowedPower },  /*!< CAN0_SIG_MaxChargePower_Peak */
    { {CAN0_MSG_SOP}, 32, 16, 0, 6553.5, 10, 0, NULL_PTR, &cans_getMaxAllowedPower },  /*!< CAN0_SIG_MaxDischargePower */
    { {CAN0_MSG_SOP}, 48, 16, 0, 6553.5, 10, 0, NULL_PTR, &cans_getMaxAllowedPower },  /*!< CAN0_SIG_MaxDischargePower_Peak */

    { {CAN0_MSG_SOC}, 0, 16, 0, 100, 100, 0, NULL_PTR, &cans_getsoc },  /*!< CAN0_SIG_SOC_mean */
    { {CAN0_MSG_SOC}, 16, 16, 0, 100, 100, 0, NULL_PTR, &cans_getsoc },  /*!< CAN0_SIG_SOC_min */
    { {CAN0_MSG_SOC}, 32, 16, 0, 100, 100, 0, NULL_PTR, &cans_getsoc },  /*!< CAN0_SIG_SOC_max */

    { {CAN0_MSG_SOH}, 0, 16, 0, 0, 100, 0, NULL_PTR, NULL_PTR },  /*!< CAN0_SIG_SOH_mean */
    { {CAN0_MSG_SOH}, 16, 16, 0, 0, 100, 0, NULL_PTR, NULL_PTR },  /*!< CAN0_SIG_SOH_min */
    { {CAN0_MSG_SOH}, 32, 16, 0, 0, 100, 0, NULL_PTR, NULL_PTR },  /*!< CAN0_SIG_SOH_max */

    { {CAN0_MSG_SOE}, 0, 16, 0, 0, 100, 0, NULL_PTR, NULL_PTR },  /*!< CAN0_SIG_SOE */
    { {CAN0_MSG_SOE}, 16, 32, 0, UINT32_MAX, 1, 0, NULL_PTR, NULL_PTR },  /*!< CAN0_SIG_RemainingEnergy */

    { {CAN0_MSG_MinMaxCellVolt}, 0, 16, 0, UINT16_MAX, 1, 0, NULL_PTR, &cans_getminmaxvolt },  /*!< CAN0_SIG_Cellvolt_mean */
    { {CAN0_MSG_MinMaxCellVolt}, 16, 16, 0, UINT16_MAX, 1, 0, NULL_PTR, &cans_getminmaxvolt },  /*!< CAN0_SIG_Cellvolt_min */
    { {CAN0_MSG_MinMaxCellVolt}, 32, 16, 0, UINT16_MAX, 1, 0, NULL_PTR, &cans_getminmaxvolt },  /*!< CAN0_SIG_Cellvolt_max */
    { {CAN0_MSG_MinMaxCellVolt}, 48, 8, 0, UINT8_MAX, 1, 0, NULL_PTR, &cans_getminmaxvolt },  /*!< CAN0_SIG_ModNumber_min */
    { {CAN0_MSG_MinMaxCellVolt}, 56, 8, 0, UINT8_MAX, 1, 0, NULL_PTR, &cans_getminmaxvolt },  /*!< CAN0_SIG_ModNumber_max */

    { {CAN0_MSG_SOV}, 0, 16, 0, 100, 100, 0, NULL_PTR, NULL_PTR },  /*!< CAN0_SIG_SOV */

    { {CAN0_MSG_MinMaxCellTemp}, 0, 16, -128, 527.35, 100, 128, NULL_PTR, &cans_getminmaxtemp },  /*!< CAN0_SIG_Cellvolt_mean */
    { {CAN0_MSG_MinMaxCellTemp}, 16, 16, -128, 527.35, 100, 128, NULL_PTR, &cans_getminmaxtemp },  /*!< CAN0_SIG_Cellvolt_min */
    { {CAN0_MSG_MinMaxCellTemp}, 32, 16, -128, 527.35, 100, 128, NULL_PTR, &cans_getminmaxtemp },  /*!< CAN0_SIG_Cellvolt_max */
    { {CAN0_MSG_MinMaxCellTemp}, 48, 8, 0, UINT8_MAX, 1, 0, NULL_PTR, &cans_getminmaxtemp },  /*!< CAN0_SIG_ModNumber_min */
    { {CAN0_MSG_MinMaxCellTemp}, 56, 8, 0, UINT8_MAX, 1, 0, NULL_PTR, &cans_getminmaxtemp },  /*!< CAN0_SIG_ModNumber_max */

    { {CAN0_MSG_Tempering}, 0, 8, 0, UINT8_MAX, 1, 0, NULL_PTR, &cans_gettempering },  /*!< CAN0_SIG_CoolingNeeded */
    { {CAN0_MSG_Tempering}, 8, 8, 0, UINT8_MAX, 1, 0, NULL_PTR, &cans_gettempering },  /*!< CAN0_SIG_HeatingNeeded */
    { {CAN0_MSG_Tempering}, 16, 32, 0, UINT32_MAX, 1, 0, NULL_PTR, &cans_gettempering },  /*!< CAN0_SIG_TemperingDemand */

    { {CAN0_MSG_Insulation}, 0, 8, 0, UINT8_MAX, 1, 0, NULL_PTR, &cans_getisoguard },  /*!< CAN0_SIG_InsulationStatus */
    { {CAN0_MSG_Insulation}, 8, 16, 0, UINT16_MAX, 1, 0, NULL_PTR, &cans_getisoguard },  /*!< CAN0_SIG_InsulationValue */

    { {CAN0_MSG_Power_0}, 0, 32, -2500000, 4292467295, 1, 2500000, NULL_PTR, &cans_getpower },  /*!< CAN0_SIG_RunAverage_Power_1s */
    { {CAN0_MSG_Power_0}, 32, 32, -2500000, 4292467295, 1, 2500000, NULL_PTR, &cans_getpower },  /*!< CAN0_SIG_RunAverage_Power_5s */
    { {CAN0_MSG_Power_1}, 0, 32, -2500000, 4292467295, 1, 2500000, NULL_PTR, &cans_getpower },  /*!< CAN0_SIG_RunAverage_Power_10s */
    { {CAN0_MSG_Power_1}, 32, 32, -2500000, 4292467295, 1, 2500000, NULL_PTR, &cans_getpower },  /*!< CAN0_SIG_RunAverage_Power_30s */
    { {CAN0_MSG_Power_2}, 0, 32, -2500000, 4292467295, 1, 2500000, NULL_PTR, &cans_getpower },  /*!< CAN0_SIG_RunAverage_Power_60s */
    { {CAN0_MSG_Power_2}, 32, 32, -2500000, 4292467295, 1, 2500000, NULL_PTR, &cans_getpower },  /*!< CAN0_SIG_RunAverage_Power_config */

    { {CAN0_MSG_Current_0}, 0, 32, -2500000, 4292467295, 1, 2500000, NULL_PTR, &cans_getcurr },  /*!< CAN0_SIG_RunAverage_Current_1s */
    { {CAN0_MSG_Current_0}, 32, 32, -2500000, 4292467295, 1, 2500000, NULL_PTR, &cans_getcurr },  /*!< CAN0_SIG_RunAverage_Current_5s */
    { {CAN0_MSG_Current_1}, 0, 32, -2500000, 4292467295, 1, 2500000, NULL_PTR, &cans_getcurr },  /*!< CAN0_SIG_RunAverage_Current_10s */
    { {CAN0_MSG_Current_1}, 32, 32, -2500000, 4292467295, 1, 2500000, NULL_PTR, &cans_getcurr },  /*!< CAN0_SIG_RunAverage_Current_30s */
    { {CAN0_MSG_Current_2}, 0, 32, -2500000, 4292467295, 1, 2500000, NULL_PTR, &cans_getcurr },  /*!< CAN0_SIG_RunAverage_Current_60s */
    { {CAN0_MSG_Current_2}, 32, 32, -2500000, 4292467295, 1, 2500000, NULL_PTR, &cans_getcurr },  /*!< CAN0_SIG_RunAverage_Current_config */

    { {CAN0_MSG_PackVoltage}, 0, 32, 0, UINT32_MAX, 1, 0, NULL_PTR, &cans_getPackVoltage },  /*!< CAN0_SIG_PackVolt_Battery */
    { {CAN0_MSG_PackVoltage}, 32, 32, 0, UINT32_MAX, 1, 0, NULL_PTR, &cans_getPackVoltage },  /*!< CAN0_SIG_PackVolt_PowerNet */

    /* Module 0 cell voltages */
    { {CAN0_MSG_Mod0_Cellvolt_0}, 0, 8, 0, UINT8_MAX, 1, 0, NULL_PTR, &cans_getvolt },  /*!< CAN0_SIG_Mod0_volt_valid_0_2 */
    { {CAN0_MSG_Mod0_Cellvolt_0}, 8, 16, 0, UINT16_MAX, 1, 0, NULL_PTR, &cans_getvolt },  /*!< CAN0_SIG_Mod0_volt_0 */
    { {CAN0_MSG_Mod0_Cellvolt_0}, 24, 16, 0, UINT16_MAX, 1, 0, NULL_PTR, &cans_getvolt },  /*!< CAN0_SIG_Mod0_volt_1 */
    { {CAN0_MSG_Mod0_Cellvolt_0}, 40, 16, 0, UINT16_MAX, 1, 0, NULL_PTR, &cans_getvolt },  /*!< CAN0_SIG_Mod0_volt_2 */
    { {CAN0_MSG_Mod0_Cellvolt_1}, 0, 8, 0, UINT8_MAX, 1, 0, NULL_PTR, &cans_getvolt },  /*!< CAN0_SIG_Mod0_volt_valid_3_5 */
    { {CAN0_MSG_Mod0_Cellvolt_1}, 8, 16, 0, UINT16_MAX, 1, 0, NULL_PTR, &cans_getvolt },  /*!< CAN0_SIG_Mod0_volt_3 */
    { {CAN0_MSG_Mod0_Cellvolt_1}, 24, 16, 0, UINT16_MAX, 1, 0, NULL_PTR, &cans_getvolt },  /*!< CAN0_SIG_Mod0_volt_4 */
    { {CAN0_MSG_Mod0_Cellvolt_1}, 40, 16, 0, UINT16_MAX, 1, 0, NULL_PTR, &cans_getvolt },  /*!< CAN0_SIG_Mod0_volt_5 */
    { {CAN0_MSG_Mod0_Cellvolt_2}, 0, 8, 0, UINT8_MAX, 1, 0, NULL_PTR, &cans_getvolt },  /*!< CAN0_SIG_Mod0_volt_valid_6_8 */
    { {CAN0_MSG_Mod0_Cellvolt_2}, 8, 16, 0, UINT16_MAX, 1, 0, NULL_PTR, &cans_getvolt },  /*!< CAN0_SIG_Mod0_volt_6 */
    { {CAN0_MSG_Mod0_Cellvolt_2}, 24, 16, 0, UINT16_MAX, 1, 0, NULL_PTR, &cans_getvolt },  /*!< CAN0_SIG_Mod0_volt_7 */
    { {CAN0_MSG_Mod0_Cellvolt_2}, 40, 16, 0, UINT16_MAX, 1, 0, NULL_PTR, &cans_getvolt },  /*!< CAN0_SIG_Mod0_volt_8 */
    { {CAN0_MSG_Mod0_Cellvolt_3}, 0, 8, 0, UINT8_MAX, 1, 0, NULL_PTR, &cans_getvolt },  /*!< CAN0_SIG_Mod0_volt_valid_9_11 */
    { {CAN0_MSG_Mod0_Cellvolt_3}, 8, 16, 0, UINT16_MAX, 1, 0, NULL_PTR, &cans_getvolt },  /*!< CAN0_SIG_Mod0_volt_9 */
    { {CAN0_MSG_Mod0_Cellvolt_3}, 24, 16, 0, UINT16_MAX, 1, 0, NULL_PTR, &cans_getvolt },  /*!< CAN0_SIG_Mod0_volt_10 */
    { {CAN0_MSG_Mod0_Cellvolt_3}, 40, 16, 0, UINT16_MAX, 1, 0, NULL_PTR, &cans_getvolt },  /*!< CAN0_SIG_Mod0_volt_11 */
    { {CAN0_MSG_Mod0_Cellvolt_4}, 0, 8, 0, UINT8_MAX, 1, 0, NULL_PTR, &cans_getvolt },  /*!< CAN0_SIG_Mod0_volt_valid_12_14 */
    { {CAN0_MSG_Mod0_Cellvolt_4}, 8, 16, 0, UINT16_MAX, 1, 0, NULL_PTR, &cans_getvolt },  /*!< CAN0_SIG_Mod0_volt_12 */
    { {CAN0_MSG_Mod0_Cellvolt_4}, 24, 16, 0, UINT16_MAX, 1, 0, NULL_PTR, &cans_getvolt },  /*!< CAN0_SIG_Mod0_volt_13 */
    { {CAN0_MSG_Mod0_Cellvolt_4}, 40, 16, 0, UINT16_MAX, 1, 0, NULL_PTR, &cans_getvolt },  /*!< CAN0_SIG_Mod0_volt_14 */
    { {CAN0_MSG_Mod0_Cellvolt_5}, 0, 8, 0, UINT8_MAX, 1, 0, NULL_PTR, &cans_getvolt },  /*!< CAN0_SIG_Mod0_volt_valid_15_17 */
    { {CAN0_MSG_Mod0_Cellvolt_5}, 8, 16, 0, UINT16_MAX, 1, 0, NULL_PTR, &cans_getvolt },  /*!< CAN0_SIG_Mod0_volt_15 */
    { {CAN0_MSG_Mod0_Cellvolt_5}, 24, 16, 0, UINT16_MAX, 1, 0, NULL_PTR, &cans_getvolt },  /*!< CAN0_SIG_Mod0_volt_16 */
    { {CAN0_MSG_Mod0_Cellvolt_5}, 40, 16, 0, UINT16_MAX, 1, 0, NULL_PTR, &cans_getvolt },  /*!< CAN0_SIG_Mod0_volt_17 */

    /* Module 0 cell temperatures */
    { {CAN0_MSG_Mod0_Celltemp_0}, 0, 8, 0, UINT8_MAX, 1, 0, NULL_PTR, &cans_gettemp },  /*!< CAN0_SIG_Mod0_volt_valid_0_2 */
    { {CAN0_MSG_Mod0_Celltemp_0}, 8, 16, -128, 527.35, 100, 128, NULL_PTR, &cans_gettemp },  /*!< CAN0_SIG_Mod0_temp_0 */
    { {CAN0_MSG_Mod0_Celltemp_0}, 24, 16, -128, 527.35, 100, 128, NULL_PTR, &cans_gettemp },  /*!< CAN0_SIG_Mod0_temp_1 */
    { {CAN0_MSG_Mod0_Celltemp_0}, 40, 16, -128, 527.35, 100, 128, NULL_PTR, &cans_gettemp },  /*!< CAN0_SIG_Mod0_temp_2 */
    { {CAN0_MSG_Mod0_Celltemp_1}, 0, 8, 0, UINT8_MAX, 1, 0, NULL_PTR, &cans_gettemp },  /*!< CAN0_SIG_Mod0_volt_valid_3_5 */
    { {CAN0_MSG_Mod0_Celltemp_1}, 8, 16, -128, 527.35, 100, 128, NULL_PTR, &cans_gettemp },  /*!< CAN0_SIG_Mod0_temp_3 */
    { {CAN0_MSG_Mod0_Celltemp_1}, 24, 16, -128, 527.35, 100, 128, NULL_PTR, &cans_gettemp },  /*!< CAN0_SIG_Mod0_temp_4 */
    { {CAN0_MSG_Mod0_Celltemp_1}, 40, 16, -128, 527.35, 100, 128, NULL_PTR, &cans_gettemp },  /*!< CAN0_SIG_Mod0_temp_5 */
    { {CAN0_MSG_Mod0_Celltemp_2}, 0, 8, 0, UINT8_MAX, 1, 0, NULL_PTR, &cans_gettemp },  /*!< CAN0_SIG_Mod0_volt_valid_6_8 */
    { {CAN0_MSG_Mod0_Celltemp_2}, 8, 16, -128, 527.35, 100, 128, NULL_PTR, &cans_gettemp },  /*!< CAN0_SIG_Mod0_temp_6 */
    { {CAN0_MSG_Mod0_Celltemp_2}, 24, 16, -128, 527.35, 100, 128, NULL_PTR, &cans_gettemp },  /*!< CAN0_SIG_Mod0_temp_7 */
    { {CAN0_MSG_Mod0_Celltemp_2}, 40, 16, -128, 527.35, 100, 128, NULL_PTR, &cans_gettemp },  /*!< CAN0_SIG_Mod0_temp_8 */
    { {CAN0_MSG_Mod0_Celltemp_3}, 0, 8, 0, UINT8_MAX, 1, 0, NULL_PTR, &cans_gettemp },  /*!< CAN0_SIG_Mod0_volt_valid_9_11 */
    { {CAN0_MSG_Mod0_Celltemp_3}, 8, 16, -128, 527.35, 100, 128, NULL_PTR, &cans_gettemp },  /*!< CAN0_SIG_Mod0_temp_9 */
    { {CAN0_MSG_Mod0_Celltemp_3}, 24, 16, -128, 527.35, 100, 128, NULL_PTR, &cans_gettemp },  /*!< CAN0_SIG_Mod0_temp_10 */
    { {CAN0_MSG_Mod0_Celltemp_3}, 40, 16, -128, 527.35, 100, 128, NULL_PTR, &cans_gettemp },  /*!< CAN0_SIG_Mod0_temp_11 */

    /* Module 1 cell voltages */
    { {CAN0_MSG_Mod1_Cellvolt_0}, 0, 8, 0, UINT8_MAX, 1, 0, NULL_PTR, &cans_getvolt },  /*!< CAN0_SIG_Mod1_volt_valid_0_2 */
    { {CAN0_MSG_Mod1_Cellvolt_0}, 8, 16, 0, UINT16_MAX, 1, 0, NULL_PTR, &cans_getvolt },  /*!< CAN0_SIG_Mod1_volt_0 */
    { {CAN0_MSG_Mod1_Cellvolt_0}, 24, 16, 0, UINT16_MAX, 1, 0, NULL_PTR, &cans_getvolt },  /*!< CAN0_SIG_Mod1_volt_1 */
    { {CAN0_MSG_Mod1_Cellvolt_0}, 40, 16, 0, UINT16_MAX, 1, 0, NULL_PTR, &cans_getvolt },  /*!< CAN0_SIG_Mod1_volt_2 */
    { {CAN0_MSG_Mod1_Cellvolt_1}, 0, 8, 0, UINT8_MAX, 1, 0, NULL_PTR, &cans_getvolt },  /*!< CAN0_SIG_Mod1_volt_valid_3_5 */
    { {CAN0_MSG_Mod1_Cellvolt_1}, 8, 16, 0, UINT16_MAX, 1, 0, NULL_PTR, &cans_getvolt },  /*!< CAN0_SIG_Mod1_volt_3 */
    { {CAN0_MSG_Mod1_Cellvolt_1}, 24, 16, 0, UINT16_MAX, 1, 0, NULL_PTR, &cans_getvolt },  /*!< CAN0_SIG_Mod1_volt_4 */
    { {CAN0_MSG_Mod1_Cellvolt_1}, 40, 16, 0, UINT16_MAX, 1, 0, NULL_PTR, &cans_getvolt },  /*!< CAN0_SIG_Mod1_volt_5 */
    { {CAN0_MSG_Mod1_Cellvolt_2}, 0, 8, 0, UINT8_MAX, 1, 0, NULL_PTR, &cans_getvolt },  /*!< CAN0_SIG_Mod1_volt_valid_6_8 */
    { {CAN0_MSG_Mod1_Cellvolt_2}, 8, 16, 0, UINT16_MAX, 1, 0, NULL_PTR, &cans_getvolt },  /*!< CAN0_SIG_Mod1_volt_6 */
    { {CAN0_MSG_Mod1_Cellvolt_2}, 24, 16, 0, UINT16_MAX, 1, 0, NULL_PTR, &cans_getvolt },  /*!< CAN0_SIG_Mod1_volt_7 */
    { {CAN0_MSG_Mod1_Cellvolt_2}, 40, 16, 0, UINT16_MAX, 1, 0, NULL_PTR, &cans_getvolt },  /*!< CAN0_SIG_Mod1_volt_8 */
    { {CAN0_MSG_Mod1_Cellvolt_3}, 0, 8, 0, UINT8_MAX, 1, 0, NULL_PTR, &cans_getvolt },  /*!< CAN0_SIG_Mod1_volt_valid_9_11 */
    { {CAN0_MSG_Mod1_Cellvolt_3}, 8, 16, 0, UINT16_MAX, 1, 0, NULL_PTR, &cans_getvolt },  /*!< CAN0_SIG_Mod1_volt_9 */
    { {CAN0_MSG_Mod1_Cellvolt_3}, 24, 16, 0, UINT16_MAX, 1, 0, NULL_PTR, &cans_getvolt },  /*!< CAN0_SIG_Mod1_volt_10 */
    { {CAN0_MSG_Mod1_Cellvolt_3}, 40, 16, 0, UINT16_MAX, 1, 0, NULL_PTR, &cans_getvolt },  /*!< CAN0_SIG_Mod1_volt_11 */
    { {CAN0_MSG_Mod1_Cellvolt_4}, 0, 8, 0, UINT8_MAX, 1, 0, NULL_PTR, &cans_getvolt },  /*!< CAN0_SIG_Mod1_volt_valid_12_14 */
    { {CAN0_MSG_Mod1_Cellvolt_4}, 8, 16, 0, UINT16_MAX, 1, 0, NULL_PTR, &cans_getvolt },  /*!< CAN0_SIG_Mod1_volt_12 */
    { {CAN0_MSG_Mod1_Cellvolt_4}, 24, 16, 0, UINT16_MAX, 1, 0, NULL_PTR, &cans_getvolt },  /*!< CAN0_SIG_Mod1_volt_13 */
    { {CAN0_MSG_Mod1_Cellvolt_4}, 40, 16, 0, UINT16_MAX, 1, 0, NULL_PTR, &cans_getvolt },  /*!< CAN0_SIG_Mod1_volt_14 */
    { {CAN0_MSG_Mod1_Cellvolt_5}, 0, 8, 0, UINT8_MAX, 1, 0, NULL_PTR, &cans_getvolt },  /*!< CAN0_SIG_Mod1_volt_valid_15_17 */
    { {CAN0_MSG_Mod1_Cellvolt_5}, 8, 16, 0, UINT16_MAX, 1, 0, NULL_PTR, &cans_getvolt },  /*!< CAN0_SIG_Mod1_volt_15 */
    { {CAN0_MSG_Mod1_Cellvolt_5}, 24, 16, 0, UINT16_MAX, 1, 0, NULL_PTR, &cans_getvolt },  /*!< CAN0_SIG_Mod1_volt_16 */
    { {CAN0_MSG_Mod1_Cellvolt_5}, 40, 16, 0, UINT16_MAX, 1, 0, NULL_PTR, &cans_getvolt },  /*!< CAN0_SIG_Mod1_volt_17 */

    /* Module 1 cell temperatures */
    { {CAN0_MSG_Mod1_Celltemp_0}, 0, 8, 0, UINT8_MAX, 1, 0, NULL_PTR, &cans_gettemp },  /*!< CAN0_SIG_Mod1_volt_valid_0_2 */
    { {CAN0_MSG_Mod1_Celltemp_0}, 8, 16, -128, 527.35, 100, 128, NULL_PTR, &cans_gettemp },  /*!< CAN0_SIG_Mod1_temp_0 */
    { {CAN0_MSG_Mod1_Celltemp_0}, 24, 16, -128, 527.35, 100, 128, NULL_PTR, &cans_gettemp },  /*!< CAN0_SIG_Mod1_temp_1 */
    { {CAN0_MSG_Mod1_Celltemp_0}, 40, 16, -128, 527.35, 100, 128, NULL_PTR, &cans_gettemp },  /*!< CAN0_SIG_Mod1_temp_2 */
    { {CAN0_MSG_Mod1_Celltemp_1}, 0, 8, 0, UINT8_MAX, 1, 0, NULL_PTR, &cans_gettemp },  /*!< CAN0_SIG_Mod1_volt_valid_3_5 */
    { {CAN0_MSG_Mod1_Celltemp_1}, 8, 16, -128, 527.35, 100, 128, NULL_PTR, &cans_gettemp },  /*!< CAN0_SIG_Mod1_temp_3 */
    { {CAN0_MSG_Mod1_Celltemp_1}, 24, 16, -128, 527.35, 100, 128, NULL_PTR, &cans_gettemp },  /*!< CAN0_SIG_Mod1_temp_4 */
    { {CAN0_MSG_Mod1_Celltemp_1}, 40, 16, -128, 527.35, 100, 128, NULL_PTR, &cans_gettemp },  /*!< CAN0_SIG_Mod1_temp_5 */
    { {CAN0_MSG_Mod1_Celltemp_2}, 0, 8, 0, UINT8_MAX, 1, 0, NULL_PTR, &cans_gettemp },  /*!< CAN0_SIG_Mod1_volt_valid_6_8 */
    { {CAN0_MSG_Mod1_Celltemp_2}, 8, 16, -128, 527.35, 100, 128, NULL_PTR, &cans_gettemp },  /*!< CAN0_SIG_Mod1_temp_6 */
    { {CAN0_MSG_Mod1_Celltemp_2}, 24, 16, -128, 527.35, 100, 128, NULL_PTR, &cans_gettemp },  /*!< CAN0_SIG_Mod1_temp_7 */
    { {CAN0_MSG_Mod1_Celltemp_2}, 40, 16, -128, 527.35, 100, 128, NULL_PTR, &cans_gettemp },  /*!< CAN0_SIG_Mod1_temp_8 */
    { {CAN0_MSG_Mod1_Celltemp_3}, 0, 8, 0, UINT8_MAX, 1, 0, NULL_PTR, &cans_gettemp },  /*!< CAN0_SIG_Mod1_volt_valid_9_11 */
    { {CAN0_MSG_Mod1_Celltemp_3}, 8, 16, -128, 527.35, 100, 128, NULL_PTR, &cans_gettemp },  /*!< CAN0_SIG_Mod1_temp_9 */
    { {CAN0_MSG_Mod1_Celltemp_3}, 24, 16, -128, 527.35, 100, 128, NULL_PTR, &cans_gettemp },  /*!< CAN0_SIG_Mod1_temp_10 */
    { {CAN0_MSG_Mod1_Celltemp_3}, 40, 16, -128, 527.35, 100, 128, NULL_PTR, &cans_gettemp },  /*!< CAN0_SIG_Mod1_temp_11 */

    /* Module 2 cell voltages */
    { {CAN0_MSG_Mod2_Cellvolt_0}, 0, 8, 0, UINT8_MAX, 1, 0, NULL_PTR, &cans_getvolt },  /*!< CAN0_SIG_Mod2_volt_valid_0_2 */
    { {CAN0_MSG_Mod2_Cellvolt_0}, 8, 16, 0, UINT16_MAX, 1, 0, NULL_PTR, &cans_getvolt },  /*!< CAN0_SIG_Mod2_volt_0 */
    { {CAN0_MSG_Mod2_Cellvolt_0}, 24, 16, 0, UINT16_MAX, 1, 0, NULL_PTR, &cans_getvolt },  /*!< CAN0_SIG_Mod2_volt_1 */
    { {CAN0_MSG_Mod2_Cellvolt_0}, 40, 16, 0, UINT16_MAX, 1, 0, NULL_PTR, &cans_getvolt },  /*!< CAN0_SIG_Mod2_volt_2 */
    { {CAN0_MSG_Mod2_Cellvolt_1}, 0, 8, 0, UINT8_MAX, 1, 0, NULL_PTR, &cans_getvolt },  /*!< CAN0_SIG_Mod2_volt_valid_3_5 */
    { {CAN0_MSG_Mod2_Cellvolt_1}, 8, 16, 0, UINT16_MAX, 1, 0, NULL_PTR, &cans_getvolt },  /*!< CAN0_SIG_Mod2_volt_3 */
    { {CAN0_MSG_Mod2_Cellvolt_1}, 24, 16, 0, UINT16_MAX, 1, 0, NULL_PTR, &cans_getvolt },  /*!< CAN0_SIG_Mod2_volt_4 */
    { {CAN0_MSG_Mod2_Cellvolt_1}, 40, 16, 0, UINT16_MAX, 1, 0, NULL_PTR, &cans_getvolt },  /*!< CAN0_SIG_Mod2_volt_5 */
    { {CAN0_MSG_Mod2_Cellvolt_2}, 0, 8, 0, UINT8_MAX, 1, 0, NULL_PTR, &cans_getvolt },  /*!< CAN0_SIG_Mod2_volt_valid_6_8 */
    { {CAN0_MSG_Mod2_Cellvolt_2}, 8, 16, 0, UINT16_MAX, 1, 0, NULL_PTR, &cans_getvolt },  /*!< CAN0_SIG_Mod2_volt_6 */
    { {CAN0_MSG_Mod2_Cellvolt_2}, 24, 16, 0, UINT16_MAX, 1, 0, NULL_PTR, &cans_getvolt },  /*!< CAN0_SIG_Mod2_volt_7 */
    { {CAN0_MSG_Mod2_Cellvolt_2}, 40, 16, 0, UINT16_MAX, 1, 0, NULL_PTR, &cans_getvolt },  /*!< CAN0_SIG_Mod2_volt_8 */
    { {CAN0_MSG_Mod2_Cellvolt_3}, 0, 8, 0, UINT8_MAX, 1, 0, NULL_PTR, &cans_getvolt },  /*!< CAN0_SIG_Mod2_volt_valid_9_11 */
    { {CAN0_MSG_Mod2_Cellvolt_3}, 8, 16, 0, UINT16_MAX, 1, 0, NULL_PTR, &cans_getvolt },  /*!< CAN0_SIG_Mod2_volt_9 */
    { {CAN0_MSG_Mod2_Cellvolt_3}, 24, 16, 0, UINT16_MAX, 1, 0, NULL_PTR, &cans_getvolt },  /*!< CAN0_SIG_Mod2_volt_10 */
    { {CAN0_MSG_Mod2_Cellvolt_3}, 40, 16, 0, UINT16_MAX, 1, 0, NULL_PTR, &cans_getvolt },  /*!< CAN0_SIG_Mod2_volt_11 */
    { {CAN0_MSG_Mod2_Cellvolt_4}, 0, 8, 0, UINT8_MAX, 1, 0, NULL_PTR, &cans_getvolt },  /*!< CAN0_SIG_Mod2_volt_valid_12_14 */
    { {CAN0_MSG_Mod2_Cellvolt_4}, 8, 16, 0, UINT16_MAX, 1, 0, NULL_PTR, &cans_getvolt },  /*!< CAN0_SIG_Mod2_volt_12 */
    { {CAN0_MSG_Mod2_Cellvolt_4}, 24, 16, 0, UINT16_MAX, 1, 0, NULL_PTR, &cans_getvolt },  /*!< CAN0_SIG_Mod2_volt_13 */
    { {CAN0_MSG_Mod2_Cellvolt_4}, 40, 16, 0, UINT16_MAX, 1, 0, NULL_PTR, &cans_getvolt },  /*!< CAN0_SIG_Mod2_volt_14 */
    { {CAN0_MSG_Mod2_Cellvolt_5}, 0, 8, 0, UINT8_MAX, 1, 0, NULL_PTR, &cans_getvolt },  /*!< CAN0_SIG_Mod2_volt_valid_15_17 */
    { {CAN0_MSG_Mod2_Cellvolt_5}, 8, 16, 0, UINT16_MAX, 1, 0, NULL_PTR, &cans_getvolt },  /*!< CAN0_SIG_Mod2_volt_15 */
    { {CAN0_MSG_Mod2_Cellvolt_5}, 24, 16, 0, UINT16_MAX, 1, 0, NULL_PTR, &cans_getvolt },  /*!< CAN0_SIG_Mod2_volt_16 */
    { {CAN0_MSG_Mod2_Cellvolt_5}, 40, 16, 0, UINT16_MAX, 1, 0, NULL_PTR, &cans_getvolt },  /*!< CAN0_SIG_Mod2_volt_17 */

    /* Module 2 cell temperatures */
    { {CAN0_MSG_Mod2_Celltemp_0}, 0, 8, 0, UINT8_MAX, 1, 0, NULL_PTR, &cans_gettemp },  /*!< CAN0_SIG_Mod2_volt_valid_0_2 */
    { {CAN0_MSG_Mod2_Celltemp_0}, 8, 16, -128, 527.35, 100, 128, NULL_PTR, &cans_gettemp },  /*!< CAN0_SIG_Mod2_temp_0 */
    { {CAN0_MSG_Mod2_Celltemp_0}, 24, 16, -128, 527.35, 100, 128, NULL_PTR, &cans_gettemp },  /*!< CAN0_SIG_Mod2_temp_1 */
    { {CAN0_MSG_Mod2_Celltemp_0}, 40, 16, -128, 527.35, 100, 128, NULL_PTR, &cans_gettemp },  /*!< CAN0_SIG_Mod2_temp_2 */
    { {CAN0_MSG_Mod2_Celltemp_1}, 0, 8, 0, UINT8_MAX, 1, 0, NULL_PTR, &cans_gettemp },  /*!< CAN0_SIG_Mod2_volt_valid_3_5 */
    { {CAN0_MSG_Mod2_Celltemp_1}, 8, 16, -128, 527.35, 100, 128, NULL_PTR, &cans_gettemp },  /*!< CAN0_SIG_Mod2_temp_3 */
    { {CAN0_MSG_Mod2_Celltemp_1}, 24, 16, -128, 527.35, 100, 128, NULL_PTR, &cans_gettemp },  /*!< CAN0_SIG_Mod2_temp_4 */
    { {CAN0_MSG_Mod2_Celltemp_1}, 40, 16, -128, 527.35, 100, 128, NULL_PTR, &cans_gettemp },  /*!< CAN0_SIG_Mod2_temp_5 */
    { {CAN0_MSG_Mod2_Celltemp_2}, 0, 8, 0, UINT8_MAX, 1, 0, NULL_PTR, &cans_gettemp },  /*!< CAN0_SIG_Mod2_volt_valid_6_8 */
    { {CAN0_MSG_Mod2_Celltemp_2}, 8, 16, -128, 527.35, 100, 128, NULL_PTR, &cans_gettemp },  /*!< CAN0_SIG_Mod2_temp_6 */
    { {CAN0_MSG_Mod2_Celltemp_2}, 24, 16, -128, 527.35, 100, 128, NULL_PTR, &cans_gettemp },  /*!< CAN0_SIG_Mod2_temp_7 */
    { {CAN0_MSG_Mod2_Celltemp_2}, 40, 16, -128, 527.35, 100, 128, NULL_PTR, &cans_gettemp },  /*!< CAN0_SIG_Mod2_temp_8 */
    { {CAN0_MSG_Mod2_Celltemp_3}, 0, 8, 0, UINT8_MAX, 1, 0, NULL_PTR, &cans_gettemp },  /*!< CAN0_SIG_Mod2_volt_valid_9_11 */
    { {CAN0_MSG_Mod2_Celltemp_3}, 8, 16, -128, 527.35, 100, 128, NULL_PTR, &cans_gettemp },  /*!< CAN0_SIG_Mod2_temp_9 */
    { {CAN0_MSG_Mod2_Celltemp_3}, 24, 16, -128, 527.35, 100, 128, NULL_PTR, &cans_gettemp },  /*!< CAN0_SIG_Mod2_temp_10 */
    { {CAN0_MSG_Mod2_Celltemp_3}, 40, 16, -128, 527.35, 100, 128, NULL_PTR, &cans_gettemp },  /*!< CAN0_SIG_Mod2_temp_11 */

    /* Module 3 cell voltages */
    { {CAN0_MSG_Mod3_Cellvolt_0}, 0, 8, 0, UINT8_MAX, 1, 0, NULL_PTR, &cans_getvolt },  /*!< CAN0_SIG_Mod3_volt_valid_0_2 */
    { {CAN0_MSG_Mod3_Cellvolt_0}, 8, 16, 0, UINT16_MAX, 1, 0, NULL_PTR, &cans_getvolt },  /*!< CAN0_SIG_Mod3_volt_0 */
    { {CAN0_MSG_Mod3_Cellvolt_0}, 24, 16, 0, UINT16_MAX, 1, 0, NULL_PTR, &cans_getvolt },  /*!< CAN0_SIG_Mod3_volt_1 */
    { {CAN0_MSG_Mod3_Cellvolt_0}, 40, 16, 0, UINT16_MAX, 1, 0, NULL_PTR, &cans_getvolt },  /*!< CAN0_SIG_Mod3_volt_2 */
    { {CAN0_MSG_Mod3_Cellvolt_1}, 0, 8, 0, UINT8_MAX, 1, 0, NULL_PTR, &cans_getvolt },  /*!< CAN0_SIG_Mod3_volt_valid_3_5 */
    { {CAN0_MSG_Mod3_Cellvolt_1}, 8, 16, 0, UINT16_MAX, 1, 0, NULL_PTR, &cans_getvolt },  /*!< CAN0_SIG_Mod3_volt_3 */
    { {CAN0_MSG_Mod3_Cellvolt_1}, 24, 16, 0, UINT16_MAX, 1, 0, NULL_PTR, &cans_getvolt },  /*!< CAN0_SIG_Mod3_volt_4 */
    { {CAN0_MSG_Mod3_Cellvolt_1}, 40, 16, 0, UINT16_MAX, 1, 0, NULL_PTR, &cans_getvolt },  /*!< CAN0_SIG_Mod3_volt_5 */
    { {CAN0_MSG_Mod3_Cellvolt_2}, 0, 8, 0, UINT8_MAX, 1, 0, NULL_PTR, &cans_getvolt },  /*!< CAN0_SIG_Mod3_volt_valid_6_8 */
    { {CAN0_MSG_Mod3_Cellvolt_2}, 8, 16, 0, UINT16_MAX, 1, 0, NULL_PTR, &cans_getvolt },  /*!< CAN0_SIG_Mod3_volt_6 */
    { {CAN0_MSG_Mod3_Cellvolt_2}, 24, 16, 0, UINT16_MAX, 1, 0, NULL_PTR, &cans_getvolt },  /*!< CAN0_SIG_Mod3_volt_7 */
    { {CAN0_MSG_Mod3_Cellvolt_2}, 40, 16, 0, UINT16_MAX, 1, 0, NULL_PTR, &cans_getvolt },  /*!< CAN0_SIG_Mod3_volt_8 */
    { {CAN0_MSG_Mod3_Cellvolt_3}, 0, 8, 0, UINT8_MAX, 1, 0, NULL_PTR, &cans_getvolt },  /*!< CAN0_SIG_Mod3_volt_valid_9_11 */
    { {CAN0_MSG_Mod3_Cellvolt_3}, 8, 16, 0, UINT16_MAX, 1, 0, NULL_PTR, &cans_getvolt },  /*!< CAN0_SIG_Mod3_volt_9 */
    { {CAN0_MSG_Mod3_Cellvolt_3}, 24, 16, 0, UINT16_MAX, 1, 0, NULL_PTR, &cans_getvolt },  /*!< CAN0_SIG_Mod3_volt_10 */
    { {CAN0_MSG_Mod3_Cellvolt_3}, 40, 16, 0, UINT16_MAX, 1, 0, NULL_PTR, &cans_getvolt },  /*!< CAN0_SIG_Mod3_volt_11 */
    { {CAN0_MSG_Mod3_Cellvolt_4}, 0, 8, 0, UINT8_MAX, 1, 0, NULL_PTR, &cans_getvolt },  /*!< CAN0_SIG_Mod3_volt_valid_12_14 */
    { {CAN0_MSG_Mod3_Cellvolt_4}, 8, 16, 0, UINT16_MAX, 1, 0, NULL_PTR, &cans_getvolt },  /*!< CAN0_SIG_Mod3_volt_12 */
    { {CAN0_MSG_Mod3_Cellvolt_4}, 24, 16, 0, UINT16_MAX, 1, 0, NULL_PTR, &cans_getvolt },  /*!< CAN0_SIG_Mod3_volt_13 */
    { {CAN0_MSG_Mod3_Cellvolt_4}, 40, 16, 0, UINT16_MAX, 1, 0, NULL_PTR, &cans_getvolt },  /*!< CAN0_SIG_Mod3_volt_14 */
    { {CAN0_MSG_Mod3_Cellvolt_5}, 0, 8, 0, UINT8_MAX, 1, 0, NULL_PTR, &cans_getvolt },  /*!< CAN0_SIG_Mod3_volt_valid_15_17 */
    { {CAN0_MSG_Mod3_Cellvolt_5}, 8, 16, 0, UINT16_MAX, 1, 0, NULL_PTR, &cans_getvolt },  /*!< CAN0_SIG_Mod3_volt_15 */
    { {CAN0_MSG_Mod3_Cellvolt_5}, 24, 16, 0, UINT16_MAX, 1, 0, NULL_PTR, &cans_getvolt },  /*!< CAN0_SIG_Mod3_volt_16 */
    { {CAN0_MSG_Mod3_Cellvolt_5}, 40, 16, 0, UINT16_MAX, 1, 0, NULL_PTR, &cans_getvolt },  /*!< CAN0_SIG_Mod3_volt_17 */

    /* Module 3 cell temperatures */
    { {CAN0_MSG_Mod3_Celltemp_0}, 0, 8, 0, UINT8_MAX, 1, 0, NULL_PTR, &cans_gettemp },  /*!< CAN0_SIG_Mod3_volt_valid_0_2 */
    { {CAN0_MSG_Mod3_Celltemp_0}, 8, 16, -128, 527.35, 100, 128, NULL_PTR, &cans_gettemp },  /*!< CAN0_SIG_Mod3_temp_0 */
    { {CAN0_MSG_Mod3_Celltemp_0}, 24, 16, -128, 527.35, 100, 128, NULL_PTR, &cans_gettemp },  /*!< CAN0_SIG_Mod3_temp_1 */
    { {CAN0_MSG_Mod3_Celltemp_0}, 40, 16, -128, 527.35, 100, 128, NULL_PTR, &cans_gettemp },  /*!< CAN0_SIG_Mod3_temp_2 */
    { {CAN0_MSG_Mod3_Celltemp_1}, 0, 8, 0, UINT8_MAX, 1, 0, NULL_PTR, &cans_gettemp },  /*!< CAN0_SIG_Mod3_volt_valid_3_5 */
    { {CAN0_MSG_Mod3_Celltemp_1}, 8, 16, -128, 527.35, 100, 128, NULL_PTR, &cans_gettemp },  /*!< CAN0_SIG_Mod3_temp_3 */
    { {CAN0_MSG_Mod3_Celltemp_1}, 24, 16, -128, 527.35, 100, 128, NULL_PTR, &cans_gettemp },  /*!< CAN0_SIG_Mod3_temp_4 */
    { {CAN0_MSG_Mod3_Celltemp_1}, 40, 16, -128, 527.35, 100, 128, NULL_PTR, &cans_gettemp },  /*!< CAN0_SIG_Mod3_temp_5 */
    { {CAN0_MSG_Mod3_Celltemp_2}, 0, 8, 0, UINT8_MAX, 1, 0, NULL_PTR, &cans_gettemp },  /*!< CAN0_SIG_Mod3_volt_valid_6_8 */
    { {CAN0_MSG_Mod3_Celltemp_2}, 8, 16, -128, 527.35, 100, 128, NULL_PTR, &cans_gettemp },  /*!< CAN0_SIG_Mod3_temp_6 */
    { {CAN0_MSG_Mod3_Celltemp_2}, 24, 16, -128, 527.35, 100, 128, NULL_PTR, &cans_gettemp },  /*!< CAN0_SIG_Mod3_temp_7 */
    { {CAN0_MSG_Mod3_Celltemp_2}, 40, 16, -128, 527.35, 100, 128, NULL_PTR, &cans_gettemp },  /*!< CAN0_SIG_Mod3_temp_8 */
    { {CAN0_MSG_Mod3_Celltemp_3}, 0, 8, 0, UINT8_MAX, 1, 0, NULL_PTR, &cans_gettemp },  /*!< CAN0_SIG_Mod3_volt_valid_9_11 */
    { {CAN0_MSG_Mod3_Celltemp_3}, 8, 16, -128, 527.35, 100, 128, NULL_PTR, &cans_gettemp },  /*!< CAN0_SIG_Mod3_temp_9 */
    { {CAN0_MSG_Mod3_Celltemp_3}, 24, 16, -128, 527.35, 100, 128, NULL_PTR, &cans_gettemp },  /*!< CAN0_SIG_Mod3_temp_10 */
    { {CAN0_MSG_Mod3_Celltemp_3}, 40, 16, -128, 527.35, 100, 128, NULL_PTR, &cans_gettemp },  /*!< CAN0_SIG_Mod3_temp_11 */

    /* Module 4 cell voltages */
    { {CAN0_MSG_Mod4_Cellvolt_0}, 0, 8, 0, UINT8_MAX, 1, 0, NULL_PTR, &cans_getvolt },  /*!< CAN0_SIG_Mod4_volt_valid_0_2 */
    { {CAN0_MSG_Mod4_Cellvolt_0}, 8, 16, 0, UINT16_MAX, 1, 0, NULL_PTR, &cans_getvolt },  /*!< CAN0_SIG_Mod4_volt_0 */
    { {CAN0_MSG_Mod4_Cellvolt_0}, 24, 16, 0, UINT16_MAX, 1, 0, NULL_PTR, &cans_getvolt },  /*!< CAN0_SIG_Mod4_volt_1 */
    { {CAN0_MSG_Mod4_Cellvolt_0}, 40, 16, 0, UINT16_MAX, 1, 0, NULL_PTR, &cans_getvolt },  /*!< CAN0_SIG_Mod4_volt_2 */
    { {CAN0_MSG_Mod4_Cellvolt_1}, 0, 8, 0, UINT8_MAX, 1, 0, NULL_PTR, &cans_getvolt },  /*!< CAN0_SIG_Mod4_volt_valid_3_5 */
    { {CAN0_MSG_Mod4_Cellvolt_1}, 8, 16, 0, UINT16_MAX, 1, 0, NULL_PTR, &cans_getvolt },  /*!< CAN0_SIG_Mod4_volt_3 */
    { {CAN0_MSG_Mod4_Cellvolt_1}, 24, 16, 0, UINT16_MAX, 1, 0, NULL_PTR, &cans_getvolt },  /*!< CAN0_SIG_Mod4_volt_4 */
    { {CAN0_MSG_Mod4_Cellvolt_1}, 40, 16, 0, UINT16_MAX, 1, 0, NULL_PTR, &cans_getvolt },  /*!< CAN0_SIG_Mod4_volt_5 */
    { {CAN0_MSG_Mod4_Cellvolt_2}, 0, 8, 0, UINT8_MAX, 1, 0, NULL_PTR, &cans_getvolt },  /*!< CAN0_SIG_Mod4_volt_valid_6_8 */
    { {CAN0_MSG_Mod4_Cellvolt_2}, 8, 16, 0, UINT16_MAX, 1, 0, NULL_PTR, &cans_getvolt },  /*!< CAN0_SIG_Mod4_volt_6 */
    { {CAN0_MSG_Mod4_Cellvolt_2}, 24, 16, 0, UINT16_MAX, 1, 0, NULL_PTR, &cans_getvolt },  /*!< CAN0_SIG_Mod4_volt_7 */
    { {CAN0_MSG_Mod4_Cellvolt_2}, 40, 16, 0, UINT16_MAX, 1, 0, NULL_PTR, &cans_getvolt },  /*!< CAN0_SIG_Mod4_volt_8 */
    { {CAN0_MSG_Mod4_Cellvolt_3}, 0, 8, 0, UINT8_MAX, 1, 0, NULL_PTR, &cans_getvolt },  /*!< CAN0_SIG_Mod4_volt_valid_9_11 */
    { {CAN0_MSG_Mod4_Cellvolt_3}, 8, 16, 0, UINT16_MAX, 1, 0, NULL_PTR, &cans_getvolt },  /*!< CAN0_SIG_Mod4_volt_9 */
    { {CAN0_MSG_Mod4_Cellvolt_3}, 24, 16, 0, UINT16_MAX, 1, 0, NULL_PTR, &cans_getvolt },  /*!< CAN0_SIG_Mod4_volt_10 */
    { {CAN0_MSG_Mod4_Cellvolt_3}, 40, 16, 0, UINT16_MAX, 1, 0, NULL_PTR, &cans_getvolt },  /*!< CAN0_SIG_Mod4_volt_11 */
    { {CAN0_MSG_Mod4_Cellvolt_4}, 0, 8, 0, UINT8_MAX, 1, 0, NULL_PTR, &cans_getvolt },  /*!< CAN0_SIG_Mod5_volt_valid_12_14 */
    { {CAN0_MSG_Mod4_Cellvolt_4}, 8, 16, 0, UINT16_MAX, 1, 0, NULL_PTR, &cans_getvolt },  /*!< CAN0_SIG_Mod5_volt_12 */
    { {CAN0_MSG_Mod4_Cellvolt_4}, 24, 16, 0, UINT16_MAX, 1, 0, NULL_PTR, &cans_getvolt },  /*!< CAN0_SIG_Mod5_volt_13 */
    { {CAN0_MSG_Mod4_Cellvolt_4}, 40, 16, 0, UINT16_MAX, 1, 0, NULL_PTR, &cans_getvolt },  /*!< CAN0_SIG_Mod5_volt_14 */
    { {CAN0_MSG_Mod4_Cellvolt_5}, 0, 8, 0, UINT8_MAX, 1, 0, NULL_PTR, &cans_getvolt },  /*!< CAN0_SIG_Mod5_volt_valid_15_17 */
    { {CAN0_MSG_Mod4_Cellvolt_5}, 8, 16, 0, UINT16_MAX, 1, 0, NULL_PTR, &cans_getvolt },  /*!< CAN0_SIG_Mod5_volt_15 */
    { {CAN0_MSG_Mod4_Cellvolt_5}, 24, 16, 0, UINT16_MAX, 1, 0, NULL_PTR, &cans_getvolt },  /*!< CAN0_SIG_Mod5_volt_16 */
    { {CAN0_MSG_Mod4_Cellvolt_5}, 40, 16, 0, UINT16_MAX, 1, 0, NULL_PTR, &cans_getvolt },  /*!< CAN0_SIG_Mod5_volt_17 */

    /* Module 4 cell temperatures */
    { {CAN0_MSG_Mod4_Celltemp_0}, 0, 8, 0, UINT8_MAX, 1, 0, NULL_PTR, &cans_gettemp },  /*!< CAN0_SIG_Mod4_volt_valid_0_2 */
    { {CAN0_MSG_Mod4_Celltemp_0}, 8, 16, -128, 527.35, 100, 128, NULL_PTR, &cans_gettemp },  /*!< CAN0_SIG_Mod4_temp_0 */
    { {CAN0_MSG_Mod4_Celltemp_0}, 24, 16, -128, 527.35, 100, 128, NULL_PTR, &cans_gettemp },  /*!< CAN0_SIG_Mod4_temp_1 */
    { {CAN0_MSG_Mod4_Celltemp_0}, 40, 16, -128, 527.35, 100, 128, NULL_PTR, &cans_gettemp },  /*!< CAN0_SIG_Mod4_temp_2 */
    { {CAN0_MSG_Mod4_Celltemp_1}, 0, 8, 0, UINT8_MAX, 1, 0, NULL_PTR, &cans_gettemp },  /*!< CAN0_SIG_Mod4_volt_valid_3_5 */
    { {CAN0_MSG_Mod4_Celltemp_1}, 8, 16, -128, 527.35, 100, 128, NULL_PTR, &cans_gettemp },  /*!< CAN0_SIG_Mod4_temp_3 */
    { {CAN0_MSG_Mod4_Celltemp_1}, 24, 16, -128, 527.35, 100, 128, NULL_PTR, &cans_gettemp },  /*!< CAN0_SIG_Mod4_temp_4 */
    { {CAN0_MSG_Mod4_Celltemp_1}, 40, 16, -128, 527.35, 100, 128, NULL_PTR, &cans_gettemp },  /*!< CAN0_SIG_Mod4_temp_5 */
    { {CAN0_MSG_Mod4_Celltemp_2}, 0, 8, 0, UINT8_MAX, 1, 0, NULL_PTR, &cans_gettemp },  /*!< CAN0_SIG_Mod4_volt_valid_6_8 */
    { {CAN0_MSG_Mod4_Celltemp_2}, 8, 16, -128, 527.35, 100, 128, NULL_PTR, &cans_gettemp },  /*!< CAN0_SIG_Mod4_temp_6 */
    { {CAN0_MSG_Mod4_Celltemp_2}, 24, 16, -128, 527.35, 100, 128, NULL_PTR, &cans_gettemp },  /*!< CAN0_SIG_Mod4_temp_7 */
    { {CAN0_MSG_Mod4_Celltemp_2}, 40, 16, -128, 527.35, 100, 128, NULL_PTR, &cans_gettemp },  /*!< CAN0_SIG_Mod4_temp_8 */
    { {CAN0_MSG_Mod4_Celltemp_3}, 0, 8, 0, UINT8_MAX, 1, 0, NULL_PTR, &cans_gettemp },  /*!< CAN0_SIG_Mod4_volt_valid_9_11 */
    { {CAN0_MSG_Mod4_Celltemp_3}, 8, 16, -128, 527.35, 100, 128, NULL_PTR, &cans_gettemp },  /*!< CAN0_SIG_Mod4_temp_9 */
    { {CAN0_MSG_Mod4_Celltemp_3}, 24, 16, -128, 527.35, 100, 128, NULL_PTR, &cans_gettemp },  /*!< CAN0_SIG_Mod4_temp_10 */
    { {CAN0_MSG_Mod4_Celltemp_3}, 40, 16, -128, 527.35, 100, 128, NULL_PTR, &cans_gettemp },  /*!< CAN0_SIG_Mod4_temp_11 */

    /* Module 5 cell voltages */
    { {CAN0_MSG_Mod5_Cellvolt_0}, 0, 8, 0, UINT8_MAX, 1, 0, NULL_PTR, &cans_getvolt },  /*!< CAN0_SIG_Mod5_volt_valid_0_2 */
    { {CAN0_MSG_Mod5_Cellvolt_0}, 8, 16, 0, UINT16_MAX, 1, 0, NULL_PTR, &cans_getvolt },  /*!< CAN0_SIG_Mod5_volt_0 */
    { {CAN0_MSG_Mod5_Cellvolt_0}, 24, 16, 0, UINT16_MAX, 1, 0, NULL_PTR, &cans_getvolt },  /*!< CAN0_SIG_Mod5_volt_1 */
    { {CAN0_MSG_Mod5_Cellvolt_0}, 40, 16, 0, UINT16_MAX, 1, 0, NULL_PTR, &cans_getvolt },  /*!< CAN0_SIG_Mod5_volt_2 */
    { {CAN0_MSG_Mod5_Cellvolt_1}, 0, 8, 0, UINT8_MAX, 1, 0, NULL_PTR, &cans_getvolt },  /*!< CAN0_SIG_Mod5_volt_valid_3_5 */
    { {CAN0_MSG_Mod5_Cellvolt_1}, 8, 16, 0, UINT16_MAX, 1, 0, NULL_PTR, &cans_getvolt },  /*!< CAN0_SIG_Mod5_volt_3 */
    { {CAN0_MSG_Mod5_Cellvolt_1}, 24, 16, 0, UINT16_MAX, 1, 0, NULL_PTR, &cans_getvolt },  /*!< CAN0_SIG_Mod5_volt_4 */
    { {CAN0_MSG_Mod5_Cellvolt_1}, 40, 16, 0, UINT16_MAX, 1, 0, NULL_PTR, &cans_getvolt },  /*!< CAN0_SIG_Mod5_volt_5 */
    { {CAN0_MSG_Mod5_Cellvolt_2}, 0, 8, 0, UINT8_MAX, 1, 0, NULL_PTR, &cans_getvolt },  /*!< CAN0_SIG_Mod5_volt_valid_6_8 */
    { {CAN0_MSG_Mod5_Cellvolt_2}, 8, 16, 0, UINT16_MAX, 1, 0, NULL_PTR, &cans_getvolt },  /*!< CAN0_SIG_Mod5_volt_6 */
    { {CAN0_MSG_Mod5_Cellvolt_2}, 24, 16, 0, UINT16_MAX, 1, 0, NULL_PTR, &cans_getvolt },  /*!< CAN0_SIG_Mod5_volt_7 */
    { {CAN0_MSG_Mod5_Cellvolt_2}, 40, 16, 0, UINT16_MAX, 1, 0, NULL_PTR, &cans_getvolt },  /*!< CAN0_SIG_Mod5_volt_8 */
    { {CAN0_MSG_Mod5_Cellvolt_3}, 0, 8, 0, UINT8_MAX, 1, 0, NULL_PTR, &cans_getvolt },  /*!< CAN0_SIG_Mod5_volt_valid_9_11 */
    { {CAN0_MSG_Mod5_Cellvolt_3}, 8, 16, 0, UINT16_MAX, 1, 0, NULL_PTR, &cans_getvolt },  /*!< CAN0_SIG_Mod5_volt_9 */
    { {CAN0_MSG_Mod5_Cellvolt_3}, 24, 16, 0, UINT16_MAX, 1, 0, NULL_PTR, &cans_getvolt },  /*!< CAN0_SIG_Mod5_volt_10 */
    { {CAN0_MSG_Mod5_Cellvolt_3}, 40, 16, 0, UINT16_MAX, 1, 0, NULL_PTR, &cans_getvolt },  /*!< CAN0_SIG_Mod5_volt_11 */
    { {CAN0_MSG_Mod5_Cellvolt_4}, 0, 8, 0, UINT8_MAX, 1, 0, NULL_PTR, &cans_getvolt },  /*!< CAN0_SIG_Mod5_volt_valid_12_14 */
    { {CAN0_MSG_Mod5_Cellvolt_4}, 8, 16, 0, UINT16_MAX, 1, 0, NULL_PTR, &cans_getvolt },  /*!< CAN0_SIG_Mod5_volt_12 */
    { {CAN0_MSG_Mod5_Cellvolt_4}, 24, 16, 0, UINT16_MAX, 1, 0, NULL_PTR, &cans_getvolt },  /*!< CAN0_SIG_Mod5_volt_13 */
    { {CAN0_MSG_Mod5_Cellvolt_4}, 40, 16, 0, UINT16_MAX, 1, 0, NULL_PTR, &cans_getvolt },  /*!< CAN0_SIG_Mod5_volt_14 */
    { {CAN0_MSG_Mod5_Cellvolt_5}, 0, 8, 0, UINT8_MAX, 1, 0, NULL_PTR, &cans_getvolt },  /*!< CAN0_SIG_Mod5_volt_valid_15_17 */
    { {CAN0_MSG_Mod5_Cellvolt_5}, 8, 16, 0, UINT16_MAX, 1, 0, NULL_PTR, &cans_getvolt },  /*!< CAN0_SIG_Mod5_volt_15 */
    { {CAN0_MSG_Mod5_Cellvolt_5}, 24, 16, 0, UINT16_MAX, 1, 0, NULL_PTR, &cans_getvolt },  /*!< CAN0_SIG_Mod5_volt_16 */
    { {CAN0_MSG_Mod5_Cellvolt_5}, 40, 16, 0, UINT16_MAX, 1, 0, NULL_PTR, &cans_getvolt },  /*!< CAN0_SIG_Mod5_volt_17 */

    /* Module 5 cell temperatures */
    { {CAN0_MSG_Mod5_Celltemp_0}, 0, 8, 0, UINT8_MAX, 1, 0, NULL_PTR, &cans_gettemp },  /*!< CAN0_SIG_Mod5_volt_valid_0_2 */
    { {CAN0_MSG_Mod5_Celltemp_0}, 8, 16, -128, 527.35, 100, 128, NULL_PTR, &cans_gettemp },  /*!< CAN0_SIG_Mod5_temp_0 */
    { {CAN0_MSG_Mod5_Celltemp_0}, 24, 16, -128, 527.35, 100, 128, NULL_PTR, &cans_gettemp },  /*!< CAN0_SIG_Mod5_temp_1 */
    { {CAN0_MSG_Mod5_Celltemp_0}, 40, 16, -128, 527.35, 100, 128, NULL_PTR, &cans_gettemp },  /*!< CAN0_SIG_Mod5_temp_2 */
    { {CAN0_MSG_Mod5_Celltemp_1}, 0, 8, 0, UINT8_MAX, 1, 0, NULL_PTR, &cans_gettemp },  /*!< CAN0_SIG_Mod5_volt_valid_3_5 */
    { {CAN0_MSG_Mod5_Celltemp_1}, 8, 16, -128, 527.35, 100, 128, NULL_PTR, &cans_gettemp },  /*!< CAN0_SIG_Mod5_temp_3 */
    { {CAN0_MSG_Mod5_Celltemp_1}, 24, 16, -128, 527.35, 100, 128, NULL_PTR, &cans_gettemp },  /*!< CAN0_SIG_Mod5_temp_4 */
    { {CAN0_MSG_Mod5_Celltemp_1}, 40, 16, -128, 527.35, 100, 128, NULL_PTR, &cans_gettemp },  /*!< CAN0_SIG_Mod5_temp_5 */
    { {CAN0_MSG_Mod5_Celltemp_2}, 0, 8, 0, UINT8_MAX, 1, 0, NULL_PTR, &cans_gettemp },  /*!< CAN0_SIG_Mod5_volt_valid_6_8 */
    { {CAN0_MSG_Mod5_Celltemp_2}, 8, 16, -128, 527.35, 100, 128, NULL_PTR, &cans_gettemp },  /*!< CAN0_SIG_Mod5_temp_6 */
    { {CAN0_MSG_Mod5_Celltemp_2}, 24, 16, -128, 527.35, 100, 128, NULL_PTR, &cans_gettemp },  /*!< CAN0_SIG_Mod5_temp_7 */
    { {CAN0_MSG_Mod5_Celltemp_2}, 40, 16, -128, 527.35, 100, 128, NULL_PTR, &cans_gettemp },  /*!< CAN0_SIG_Mod5_temp_8 */
    { {CAN0_MSG_Mod5_Celltemp_3}, 0, 8, 0, UINT8_MAX, 1, 0, NULL_PTR, &cans_gettemp },  /*!< CAN0_SIG_Mod5_volt_valid_9_11 */
    { {CAN0_MSG_Mod5_Celltemp_3}, 8, 16, -128, 527.35, 100, 128, NULL_PTR, &cans_gettemp },  /*!< CAN0_SIG_Mod5_temp_9 */
    { {CAN0_MSG_Mod5_Celltemp_3}, 24, 16, -128, 527.35, 100, 128, NULL_PTR, &cans_gettemp },  /*!< CAN0_SIG_Mod5_temp_10 */
    { {CAN0_MSG_Mod5_Celltemp_3}, 40, 16, -128, 527.35, 100, 128, NULL_PTR, &cans_gettemp },  /*!< CAN0_SIG_Mod5_temp_11 */

    /* Module 6 cell voltages */
    { {CAN0_MSG_Mod6_Cellvolt_0}, 0, 8, 0, UINT8_MAX, 1, 0, NULL_PTR, &cans_getvolt },  /*!< CAN0_SIG_Mod6_volt_valid_0_2 */
    { {CAN0_MSG_Mod6_Cellvolt_0}, 8, 16, 0, UINT16_MAX, 1, 0, NULL_PTR, &cans_getvolt },  /*!< CAN0_SIG_Mod6_volt_0 */
    { {CAN0_MSG_Mod6_Cellvolt_0}, 24, 16, 0, UINT16_MAX, 1, 0, NULL_PTR, &cans_getvolt },  /*!< CAN0_SIG_Mod6_volt_1 */
    { {CAN0_MSG_Mod6_Cellvolt_0}, 40, 16, 0, UINT16_MAX, 1, 0, NULL_PTR, &cans_getvolt },  /*!< CAN0_SIG_Mod6_volt_2 */
    { {CAN0_MSG_Mod6_Cellvolt_1}, 0, 8, 0, UINT8_MAX, 1, 0, NULL_PTR, &cans_getvolt },  /*!< CAN0_SIG_Mod6_volt_valid_3_5 */
    { {CAN0_MSG_Mod6_Cellvolt_1}, 8, 16, 0, UINT16_MAX, 1, 0, NULL_PTR, &cans_getvolt },  /*!< CAN0_SIG_Mod6_volt_3 */
    { {CAN0_MSG_Mod6_Cellvolt_1}, 24, 16, 0, UINT16_MAX, 1, 0, NULL_PTR, &cans_getvolt },  /*!< CAN0_SIG_Mod6_volt_4 */
    { {CAN0_MSG_Mod6_Cellvolt_1}, 40, 16, 0, UINT16_MAX, 1, 0, NULL_PTR, &cans_getvolt },  /*!< CAN0_SIG_Mod6_volt_5 */
    { {CAN0_MSG_Mod6_Cellvolt_2}, 0, 8, 0, UINT8_MAX, 1, 0, NULL_PTR, &cans_getvolt },  /*!< CAN0_SIG_Mod6_volt_valid_6_8 */
    { {CAN0_MSG_Mod6_Cellvolt_2}, 8, 16, 0, UINT16_MAX, 1, 0, NULL_PTR, &cans_getvolt },  /*!< CAN0_SIG_Mod6_volt_6 */
    { {CAN0_MSG_Mod6_Cellvolt_2}, 24, 16, 0, UINT16_MAX, 1, 0, NULL_PTR, &cans_getvolt },  /*!< CAN0_SIG_Mod6_volt_7 */
    { {CAN0_MSG_Mod6_Cellvolt_2}, 40, 16, 0, UINT16_MAX, 1, 0, NULL_PTR, &cans_getvolt },  /*!< CAN0_SIG_Mod6_volt_8 */
    { {CAN0_MSG_Mod6_Cellvolt_3}, 0, 8, 0, UINT8_MAX, 1, 0, NULL_PTR, &cans_getvolt },  /*!< CAN0_SIG_Mod6_volt_valid_9_11 */
    { {CAN0_MSG_Mod6_Cellvolt_3}, 8, 16, 0, UINT16_MAX, 1, 0, NULL_PTR, &cans_getvolt },  /*!< CAN0_SIG_Mod6_volt_9 */
    { {CAN0_MSG_Mod6_Cellvolt_3}, 24, 16, 0, UINT16_MAX, 1, 0, NULL_PTR, &cans_getvolt },  /*!< CAN0_SIG_Mod6_volt_10 */
    { {CAN0_MSG_Mod6_Cellvolt_3}, 40, 16, 0, UINT16_MAX, 1, 0, NULL_PTR, &cans_getvolt },  /*!< CAN0_SIG_Mod6_volt_11 */
    { {CAN0_MSG_Mod6_Cellvolt_4}, 0, 8, 0, UINT8_MAX, 1, 0, NULL_PTR, &cans_getvolt },  /*!< CAN0_SIG_Mod6_volt_valid_12_14 */
    { {CAN0_MSG_Mod6_Cellvolt_4}, 8, 16, 0, UINT16_MAX, 1, 0, NULL_PTR, &cans_getvolt },  /*!< CAN0_SIG_Mod6_volt_12 */
    { {CAN0_MSG_Mod6_Cellvolt_4}, 24, 16, 0, UINT16_MAX, 1, 0, NULL_PTR, &cans_getvolt },  /*!< CAN0_SIG_Mod6_volt_13 */
    { {CAN0_MSG_Mod6_Cellvolt_4}, 40, 16, 0, UINT16_MAX, 1, 0, NULL_PTR, &cans_getvolt },  /*!< CAN0_SIG_Mod6_volt_14 */
    { {CAN0_MSG_Mod6_Cellvolt_5}, 0, 8, 0, UINT8_MAX, 1, 0, NULL_PTR, &cans_getvolt },  /*!< CAN0_SIG_Mod6_volt_valid_15_17 */
    { {CAN0_MSG_Mod6_Cellvolt_5}, 8, 16, 0, UINT16_MAX, 1, 0, NULL_PTR, &cans_getvolt },  /*!< CAN0_SIG_Mod6_volt_15 */
    { {CAN0_MSG_Mod6_Cellvolt_5}, 24, 16, 0, UINT16_MAX, 1, 0, NULL_PTR, &cans_getvolt },  /*!< CAN0_SIG_Mod6_volt_16 */
    { {CAN0_MSG_Mod6_Cellvolt_5}, 40, 16, 0, UINT16_MAX, 1, 0, NULL_PTR, &cans_getvolt },  /*!< CAN0_SIG_Mod6_volt_17 */

    /* Module 6 cell temperatures */
    { {CAN0_MSG_Mod6_Celltemp_0}, 0, 8, 0, UINT8_MAX, 1, 0, NULL_PTR, &cans_gettemp },  /*!< CAN0_SIG_Mod6_volt_valid_0_2 */
    { {CAN0_MSG_Mod6_Celltemp_0}, 8, 16, -128, 527.35, 100, 128, NULL_PTR, &cans_gettemp },  /*!< CAN0_SIG_Mod6_temp_0 */
    { {CAN0_MSG_Mod6_Celltemp_0}, 24, 16, -128, 527.35, 100, 128, NULL_PTR, &cans_gettemp },  /*!< CAN0_SIG_Mod6_temp_1 */
    { {CAN0_MSG_Mod6_Celltemp_0}, 40, 16, -128, 527.35, 100, 128, NULL_PTR, &cans_gettemp },  /*!< CAN0_SIG_Mod6_temp_2 */
    { {CAN0_MSG_Mod6_Celltemp_1}, 0, 8, 0, UINT8_MAX, 1, 0, NULL_PTR, &cans_gettemp },  /*!< CAN0_SIG_Mod6_volt_valid_3_5 */
    { {CAN0_MSG_Mod6_Celltemp_1}, 8, 16, -128, 527.35, 100, 128, NULL_PTR, &cans_gettemp },  /*!< CAN0_SIG_Mod6_temp_3 */
    { {CAN0_MSG_Mod6_Celltemp_1}, 24, 16, -128, 527.35, 100, 128, NULL_PTR, &cans_gettemp },  /*!< CAN0_SIG_Mod6_temp_4 */
    { {CAN0_MSG_Mod6_Celltemp_1}, 40, 16, -128, 527.35, 100, 128, NULL_PTR, &cans_gettemp },  /*!< CAN0_SIG_Mod6_temp_5 */
    { {CAN0_MSG_Mod6_Celltemp_2}, 0, 8, 0, UINT8_MAX, 1, 0, NULL_PTR, &cans_gettemp },  /*!< CAN0_SIG_Mod6_volt_valid_6_8 */
    { {CAN0_MSG_Mod6_Celltemp_2}, 8, 16, -128, 527.35, 100, 128, NULL_PTR, &cans_gettemp },  /*!< CAN0_SIG_Mod6_temp_6 */
    { {CAN0_MSG_Mod6_Celltemp_2}, 24, 16, -128, 527.35, 100, 128, NULL_PTR, &cans_gettemp },  /*!< CAN0_SIG_Mod6_temp_7 */
    { {CAN0_MSG_Mod6_Celltemp_2}, 40, 16, -128, 527.35, 100, 128, NULL_PTR, &cans_gettemp },  /*!< CAN0_SIG_Mod6_temp_8 */
    { {CAN0_MSG_Mod6_Celltemp_3}, 0, 8, 0, UINT8_MAX, 1, 0, NULL_PTR, &cans_gettemp },  /*!< CAN0_SIG_Mod6_volt_valid_9_11 */
    { {CAN0_MSG_Mod6_Celltemp_3}, 8, 16, -128, 527.35, 100, 128, NULL_PTR, &cans_gettemp },  /*!< CAN0_SIG_Mod6_temp_9 */
    { {CAN0_MSG_Mod6_Celltemp_3}, 24, 16, -128, 527.35, 100, 128, NULL_PTR, &cans_gettemp },  /*!< CAN0_SIG_Mod6_temp_10 */
    { {CAN0_MSG_Mod6_Celltemp_3}, 40, 16, -128, 527.35, 100, 128, NULL_PTR, &cans_gettemp },  /*!< CAN0_SIG_Mod6_temp_11 */

    /* Module 7 cell voltages */
    { {CAN0_MSG_Mod7_Cellvolt_0}, 0, 8, 0, UINT8_MAX, 1, 0, NULL_PTR, &cans_getvolt },  /*!< CAN0_SIG_Mod7_volt_valid_0_2 */
    { {CAN0_MSG_Mod7_Cellvolt_0}, 8, 16, 0, UINT16_MAX, 1, 0, NULL_PTR, &cans_getvolt },  /*!< CAN0_SIG_Mod7_volt_0 */
    { {CAN0_MSG_Mod7_Cellvolt_0}, 24, 16, 0, UINT16_MAX, 1, 0, NULL_PTR, &cans_getvolt },  /*!< CAN0_SIG_Mod7_volt_1 */
    { {CAN0_MSG_Mod7_Cellvolt_0}, 40, 16, 0, UINT16_MAX, 1, 0, NULL_PTR, &cans_getvolt },  /*!< CAN0_SIG_Mod7_volt_2 */
    { {CAN0_MSG_Mod7_Cellvolt_1}, 0, 8, 0, UINT8_MAX, 1, 0, NULL_PTR, &cans_getvolt },  /*!< CAN0_SIG_Mod7_volt_valid_3_5 */
    { {CAN0_MSG_Mod7_Cellvolt_1}, 8, 16, 0, UINT16_MAX, 1, 0, NULL_PTR, &cans_getvolt },  /*!< CAN0_SIG_Mod7_volt_3 */
    { {CAN0_MSG_Mod7_Cellvolt_1}, 24, 16, 0, UINT16_MAX, 1, 0, NULL_PTR, &cans_getvolt },  /*!< CAN0_SIG_Mod7_volt_4 */
    { {CAN0_MSG_Mod7_Cellvolt_1}, 40, 16, 0, UINT16_MAX, 1, 0, NULL_PTR, &cans_getvolt },  /*!< CAN0_SIG_Mod7_volt_5 */
    { {CAN0_MSG_Mod7_Cellvolt_2}, 0, 8, 0, UINT8_MAX, 1, 0, NULL_PTR, &cans_getvolt },  /*!< CAN0_SIG_Mod7_volt_valid_6_8 */
    { {CAN0_MSG_Mod7_Cellvolt_2}, 8, 16, 0, UINT16_MAX, 1, 0, NULL_PTR, &cans_getvolt },  /*!< CAN0_SIG_Mod7_volt_6 */
    { {CAN0_MSG_Mod7_Cellvolt_2}, 24, 16, 0, UINT16_MAX, 1, 0, NULL_PTR, &cans_getvolt },  /*!< CAN0_SIG_Mod7_volt_7 */
    { {CAN0_MSG_Mod7_Cellvolt_2}, 40, 16, 0, UINT16_MAX, 1, 0, NULL_PTR, &cans_getvolt },  /*!< CAN0_SIG_Mod7_volt_8 */
    { {CAN0_MSG_Mod7_Cellvolt_3}, 0, 8, 0, UINT8_MAX, 1, 0, NULL_PTR, &cans_getvolt },  /*!< CAN0_SIG_Mod7_volt_valid_9_11 */
    { {CAN0_MSG_Mod7_Cellvolt_3}, 8, 16, 0, UINT16_MAX, 1, 0, NULL_PTR, &cans_getvolt },  /*!< CAN0_SIG_Mod7_volt_9 */
    { {CAN0_MSG_Mod7_Cellvolt_3}, 24, 16, 0, UINT16_MAX, 1, 0, NULL_PTR, &cans_getvolt },  /*!< CAN0_SIG_Mod7_volt_10 */
    { {CAN0_MSG_Mod7_Cellvolt_3}, 40, 16, 0, UINT16_MAX, 1, 0, NULL_PTR, &cans_getvolt },  /*!< CAN0_SIG_Mod7_volt_11 */
    { {CAN0_MSG_Mod7_Cellvolt_4}, 0, 8, 0, UINT8_MAX, 1, 0, NULL_PTR, &cans_getvolt },  /*!< CAN0_SIG_Mod7_volt_valid_12_14 */
    { {CAN0_MSG_Mod7_Cellvolt_4}, 8, 16, 0, UINT16_MAX, 1, 0, NULL_PTR, &cans_getvolt },  /*!< CAN0_SIG_Mod7_volt_12 */
    { {CAN0_MSG_Mod7_Cellvolt_4}, 24, 16, 0, UINT16_MAX, 1, 0, NULL_PTR, &cans_getvolt },  /*!< CAN0_SIG_Mod7_volt_13 */
    { {CAN0_MSG_Mod7_Cellvolt_4}, 40, 16, 0, UINT16_MAX, 1, 0, NULL_PTR, &cans_getvolt },  /*!< CAN0_SIG_Mod7_volt_14 */
    { {CAN0_MSG_Mod7_Cellvolt_5}, 0, 8, 0, UINT8_MAX, 1, 0, NULL_PTR, &cans_getvolt },  /*!< CAN0_SIG_Mod7_volt_valid_15_17 */
    { {CAN0_MSG_Mod7_Cellvolt_5}, 8, 16, 0, UINT16_MAX, 1, 0, NULL_PTR, &cans_getvolt },  /*!< CAN0_SIG_Mod7_volt_15 */
    { {CAN0_MSG_Mod7_Cellvolt_5}, 24, 16, 0, UINT16_MAX, 1, 0, NULL_PTR, &cans_getvolt },  /*!< CAN0_SIG_Mod7_volt_16 */
    { {CAN0_MSG_Mod7_Cellvolt_5}, 40, 16, 0, UINT16_MAX, 1, 0, NULL_PTR, &cans_getvolt },  /*!< CAN0_SIG_Mod7_volt_17 */

    /* Module 7 cell temperatures */
    { {CAN0_MSG_Mod7_Celltemp_0}, 0, 8, 0, UINT8_MAX, 1, 0, NULL_PTR, &cans_gettemp },  /*!< CAN0_SIG_Mod4_volt_valid_0_2 */
    { {CAN0_MSG_Mod7_Celltemp_0}, 8, 16, -128, 527.35, 100, 128, NULL_PTR, &cans_gettemp },  /*!< CAN0_SIG_Mod4_temp_0 */
    { {CAN0_MSG_Mod7_Celltemp_0}, 24, 16, -128, 527.35, 100, 128, NULL_PTR, &cans_gettemp },  /*!< CAN0_SIG_Mod4_temp_1 */
    { {CAN0_MSG_Mod7_Celltemp_0}, 40, 16, -128, 527.35, 100, 128, NULL_PTR, &cans_gettemp },  /*!< CAN0_SIG_Mod4_temp_2 */
    { {CAN0_MSG_Mod7_Celltemp_1}, 0, 8, 0, UINT8_MAX, 1, 0, NULL_PTR, &cans_gettemp },  /*!< CAN0_SIG_Mod4_volt_valid_3_5 */
    { {CAN0_MSG_Mod7_Celltemp_1}, 8, 16, -128, 527.35, 100, 128, NULL_PTR, &cans_gettemp },  /*!< CAN0_SIG_Mod4_temp_3 */
    { {CAN0_MSG_Mod7_Celltemp_1}, 24, 16, -128, 527.35, 100, 128, NULL_PTR, &cans_gettemp },  /*!< CAN0_SIG_Mod4_temp_4 */
    { {CAN0_MSG_Mod7_Celltemp_1}, 40, 16, -128, 527.35, 100, 128, NULL_PTR, &cans_gettemp },  /*!< CAN0_SIG_Mod4_temp_5 */
    { {CAN0_MSG_Mod7_Celltemp_2}, 0, 8, 0, UINT8_MAX, 1, 0, NULL_PTR, &cans_gettemp },  /*!< CAN0_SIG_Mod4_volt_valid_6_8 */
    { {CAN0_MSG_Mod7_Celltemp_2}, 8, 16, -128, 527.35, 100, 128, NULL_PTR, &cans_gettemp },  /*!< CAN0_SIG_Mod4_temp_6 */
    { {CAN0_MSG_Mod7_Celltemp_2}, 24, 16, -128, 527.35, 100, 128, NULL_PTR, &cans_gettemp },  /*!< CAN0_SIG_Mod4_temp_7 */
    { {CAN0_MSG_Mod7_Celltemp_2}, 40, 16, -128, 527.35, 100, 128, NULL_PTR, &cans_gettemp },  /*!< CAN0_SIG_Mod4_temp_8 */
    { {CAN0_MSG_Mod7_Celltemp_3}, 0, 8, 0, UINT8_MAX, 1, 0, NULL_PTR, &cans_gettemp },  /*!< CAN0_SIG_Mod4_volt_valid_9_11 */
    { {CAN0_MSG_Mod7_Celltemp_3}, 8, 16, -128, 527.35, 100, 128, NULL_PTR, &cans_gettemp },  /*!< CAN0_SIG_Mod4_temp_9 */
    { {CAN0_MSG_Mod7_Celltemp_3}, 24, 16, -128, 527.35, 100, 128, NULL_PTR, &cans_gettemp },  /*!< CAN0_SIG_Mod4_temp_10 */
    { {CAN0_MSG_Mod7_Celltemp_3}, 40, 16, -128, 527.35, 100, 128, NULL_PTR, &cans_gettemp },  /*!< CAN0_SIG_Mod4_temp_11 */

#ifdef CURRENT_SENSOR_ISABELLENHUETTE_TRIGGERED
        {{CAN0_MSG_BMS_CurrentTrigger}, 0, 32, 0, 0, 1, 0, NULL_PTR, &cans_gettriggercurrent }  /*!< CAN0_SIG_ISA_Trigger */
#endif /* CURRENT_SENSOR_ISABELLENHUETTE_TRIGGERED */
};


const CANS_signal_s cans_CAN1_signals_tx[] = {
};


const CANS_signal_s cans_CAN0_signals_rx[] = {
    { {CAN0_MSG_StateRequest}, 8, 8, 0, UINT8_MAX, 1, 0, &cans_setstaterequest, NULL_PTR },
    { {CAN0_MSG_IVT_Current}, 0, 8, 0, UINT8_MAX, 1, 0, NULL_PTR, NULL_PTR },  /* CAN0_SIG_ISENS0_I_MuxID */
    { {CAN0_MSG_IVT_Current}, 8, 8, 0, UINT8_MAX, 1, 0, NULL_PTR, NULL_PTR },  /* CAN0_SIG_ISENS0_I_Status */
    { {CAN0_MSG_IVT_Current}, 16, 32, INT32_MIN, INT32_MAX, 1, 0, &cans_setcurr, NULL_PTR },  /* CAN0_SIG_ISENS0_I_Measurement */
    { {CAN0_MSG_IVT_Voltage_1}, 0, 8, 0, UINT8_MAX, 1, 0, NULL_PTR, NULL_PTR },  /* CAN0_SIG_ISENS1_U1_MuxID */
    { {CAN0_MSG_IVT_Voltage_1}, 8, 8, 0, UINT8_MAX, 1, 0, NULL_PTR, NULL_PTR },  /* CAN0_SIG_ISENS1_U1_Status */
    { {CAN0_MSG_IVT_Voltage_1}, 16, 32, 0, INT32_MAX, 1, 0, &cans_setcurr, NULL_PTR },  /* CAN0_SIG_ISENS1_U1_Measurement */
    { {CAN0_MSG_IVT_Voltage_2}, 0, 8, 0, UINT8_MAX, 1, 0, NULL_PTR, NULL_PTR },  /* CAN0_SIG_ISENS2_U2_MuxID */
    { {CAN0_MSG_IVT_Voltage_2}, 8, 8, 0, UINT8_MAX, 1, 0, NULL_PTR, NULL_PTR },  /* CAN0_SIG_ISENS2_U2_Status */
    { {CAN0_MSG_IVT_Voltage_2}, 16, 32, 0, INT32_MAX, 1, 0, &cans_setcurr, NULL_PTR },  /* CAN0_SIG_ISENS2_U2_Measurement */
    { {CAN0_MSG_IVT_Voltage_3}, 0, 8, 0, UINT8_MAX, 1, 0, NULL_PTR, NULL_PTR },  /* CAN0_SIG_ISENS3_U3_MuxID */
    { {CAN0_MSG_IVT_Voltage_3}, 8, 8, 0, UINT8_MAX, 1, 0, NULL_PTR, NULL_PTR },  /* CAN0_SIG_ISENS3_U3_Status */
    { {CAN0_MSG_IVT_Voltage_3}, 16, 32, 0, INT32_MAX, 1, 0, &cans_setcurr, NULL_PTR },  /* CAN0_SIG_ISENS3_U3_Measurement */
    { {CAN0_MSG_IVT_Temperature}, 0, 8, 0, UINT8_MAX, 1, 0, NULL_PTR, NULL_PTR },  /* CAN0_SIG_ISENS4_T_MuxID */
    { {CAN0_MSG_IVT_Temperature}, 8, 8, 0, UINT8_MAX, 1, 0, NULL_PTR, NULL_PTR },  /* CAN0_SIG_ISENS4_T_Status */
    { {CAN0_MSG_IVT_Temperature}, 16, 32, INT32_MIN, INT32_MAX, 0.1, 0, &cans_setcurr, NULL_PTR },  /* CAN0_SIG_ISENS4_T_Measurement */
    { {CAN0_MSG_IVT_Power}, 0, 8, 0, UINT8_MAX, 1, 0, NULL_PTR, NULL_PTR },  /* CAN0_SIG_ISENS5_P_MuxID */
    { {CAN0_MSG_IVT_Power}, 8, 8, 0, UINT8_MAX, 1, 0, NULL_PTR, NULL_PTR },  /* CAN0_SIG_ISENS5_P_Status */
    { {CAN0_MSG_IVT_Power}, 16, 32, INT32_MIN, INT32_MAX, 1, 0, &cans_setcurr, NULL_PTR },  /* CAN0_SIG_ISENS5_P_Measurement */
    { {CAN0_MSG_IVT_CoulombCount}, 0, 8, 0, UINT8_MAX, 1, 0, NULL_PTR, NULL_PTR },  /* CAN0_SIG_ISENS6_CC_MuxID */
    { {CAN0_MSG_IVT_CoulombCount}, 8, 8, 0, UINT8_MAX, 1, 0, NULL_PTR, NULL_PTR },  /* CAN0_SIG_ISENS6_CC_Status */
    { {CAN0_MSG_IVT_CoulombCount}, 16, 32, INT32_MIN, INT32_MAX, 1, 0, &cans_setcurr, NULL_PTR },  /* CAN0_SIG_ISENS6_CC_Measurement */
    { {CAN0_MSG_IVT_EnergyCount}, 0, 8, 0, UINT8_MAX, 1, 0, NULL_PTR, NULL_PTR },  /* CAN0_SIG_ISENS7_EC_MuxID */
    { {CAN0_MSG_IVT_EnergyCount}, 8, 8, 0, UINT8_MAX, 1, 0, NULL_PTR, NULL_PTR },  /* CAN0_SIG_ISENS7_EC_Status */
    { {CAN0_MSG_IVT_EnergyCount}, 16, 32, INT32_MIN, INT32_MAX, 1, 0, &cans_setcurr, NULL_PTR },  /* CAN0_SIG_ISENS7_EC_Measurement */
    { {CAN0_MSG_DEBUG}, 0, 64, 0, UINT64_MAX, 1, 0, &cans_setdebug, NULL_PTR },  /* CAN0_SIG_DEBUG_Data */
    { {CAN0_MSG_GetReleaseVersion}, 0, 64, 0, UINT64_MAX, 1, 0, &cans_setSWversion, NULL_PTR }  /* CAN0_SIG_DEBUG_Data */
};

const CANS_signal_s cans_CAN1_signals_rx[] = {
};


const uint16_t cans_CAN0_signals_tx_length = sizeof(cans_CAN0_signals_tx)/sizeof(cans_CAN0_signals_tx[0]);
const uint16_t cans_CAN1_signals_tx_length = sizeof(cans_CAN1_signals_tx)/sizeof(cans_CAN1_signals_tx[0]);

const uint16_t cans_CAN0_signals_rx_length = sizeof(cans_CAN0_signals_rx)/sizeof(cans_CAN0_signals_rx[0]);
const uint16_t cans_CAN1_signals_rx_length = sizeof(cans_CAN1_signals_rx)/sizeof(cans_CAN1_signals_rx[0]);

/*================== Static Function Implementations ========================*/
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
