ArakniD/foxbms/embedded-software/mcu-primary/src/module/config/contactor_cfg.h

/**
 *
 * @copyright &copy; 2010 - 2019, Fraunhofer-Gesellschaft zur Foerderung der
 *  angewandten Forschung e.V. All rights reserved.
 *
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
 * We kindly request you to use one or more of the following phrases to refer
 * to foxBMS in your hardware, software, documentation or advertising
 * materials:
 *
 * &Prime;This product uses parts of foxBMS&reg;&Prime;
 *
 * &Prime;This product includes parts of foxBMS&reg;&Prime;
 *
 * &Prime;This product is derived from foxBMS&reg;&Prime;
 *
 */

/**
 * @file    contactor_cfg.h
 * @author  foxBMS Team
 * @date    23.09.2015 (date of creation)
 * @ingroup DRIVERS_CONF
 * @prefix  CONT
 *
 * @brief   Header for the configuration for the driver for the contactors
 *
 */

#ifndef CONTACTOR_CFG_H_
#define CONTACTOR_CFG_H_

/*================== Includes =============================================*/
#include "general.h"
#include "batterysystem_cfg.h"
#include "io.h"

/*================== Macros and Definitions ===============================*/

/**
 * @ingroup CONFIG_CONTACTOR
 * defines the number of bad countings of opening contactors at too
 *  high current
 * \par Type:
 * int
 * \par Default:
 * 10
 * \par Range:
 * [9,11]
*/
#define CONT_NUMBER_OF_BAD_COUNTINGS 10

/**
 * @ingroup CONFIG_CONTACTOR
 * This macro describes the limiting current from the the positive to
 * negative side of the contactor at which a damaging of the
 * contactor occurs. If this limit is exceeded the contactor
 * module makes an entry in the diagnosis module indicating a
 * switching off of the contactors under a bad  condition
 *
 * \par Type:
 * float
 * \par Default:
 * 1.0
 * \par Range:
 * [1.0,2.0]
*/
#define BAD_SWITCHOFF_CURRENT_POS 100000.0f

/**
 * @ingroup CONFIG_CONTACTOR
 * This macro describes the limiting current from the the negative to
 * positive side of the contactor at which a damaging of the
 * contactor occurs. If this limit is exceeded the contactor
 * module makes an entry in the diagnosis module indicating a
 * switching off of the contactors under a bad  condition
 *
 * \par Type:
 * float
 * \par Default:
 * -1.0
 * \par Range:
 * [-2.0,-1.0]
*/
#define BAD_SWITCHOFF_CURRENT_NEG -1000000.0f

/*
 * The number of defines per contactor must be the same as the length
 *  of the array cont_contactors_cfg in contactor_cfg.c
 * Every contactor consists of 1 control pin and 1 feedback pin
 * counting together as 1 contactor.
 * E.g. if you have 1 contactor your define has to be:
 *      #define CONT_MAIN_PLUS_CONTROL      IO_PIN_CONTACTOR_0_CONTROL
 *      #define CONT_MAIN_PLUS_FEEDBACK     IO_PIN_CONTACTOR_0_FEEDBACK
 */
#define CONT_MAIN_PLUS_CONTROL                  IO_PIN_CONTACTOR_0_CONTROL
#define CONT_MAIN_PLUS_FEEDBACK                 IO_PIN_CONTACTOR_0_FEEDBACK

#define CONT_PRECHARGE_PLUS_CONTROL             IO_PIN_CONTACTOR_1_CONTROL
#define CONT_PRECHARGE_PLUS_FEEDBACK            IO_PIN_CONTACTOR_1_FEEDBACK

#define CONT_MAIN_MINUS_CONTROL                 IO_PIN_CONTACTOR_2_CONTROL
#define CONT_MAIN_MINUS_FEEDBACK                IO_PIN_CONTACTOR_2_FEEDBACK

#if BS_SEPARATE_POWERLINES == 1
#define CONT_CHARGE_MAIN_PLUS_CONTROL           IO_PIN_CONTACTOR_3_CONTROL
#define CONT_CHARGE_MAIN_PLUS_FEEDBACK          IO_PIN_CONTACTOR_3_FEEDBACK

#define CONT_CHARGE_PRECHARGE_PLUS_CONTROL      IO_PIN_CONTACTOR_4_CONTROL
#define CONT_CHARGE_PRECHARGE_PLUS_FEEDBACK     IO_PIN_CONTACTOR_4_FEEDBACK

#define CONT_CHARGE_MAIN_MINUS_CONTROL          IO_PIN_CONTACTOR_5_CONTROL
#define CONT_CHARGE_MAIN_MINUS_FEEDBACK         IO_PIN_CONTACTOR_5_FEEDBACK
#endif /* BS_SEPARATE_POWERLINES == 1 */
/*
 * additional possible contactors from the io definition
#define CONT_X0_CONTROL                         PIN_CONTACTOR_3_CONTROL
#define CONT_X0_FEEDBACK                        PIN_CONTACTOR_3_FEEDBACK

#define CONT_X1_CONTROL                         PIN_CONTACTOR_4_CONTROL
#define CONT_X1_FEEDBACK                        PIN_CONTACTOR_4_FEEDBACK

#define CONT_X2_CONTROL                         PIN_CONTACTOR_5_CONTROL
#define CONT_X2_FEEDBACK                        PIN_CONTACTOR_5_FEEDBACK
*/
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
